bleroy/3d-junkyard/Atari130MX/Atari130MX-adapter/Atari130MX-FFC-schematic.png

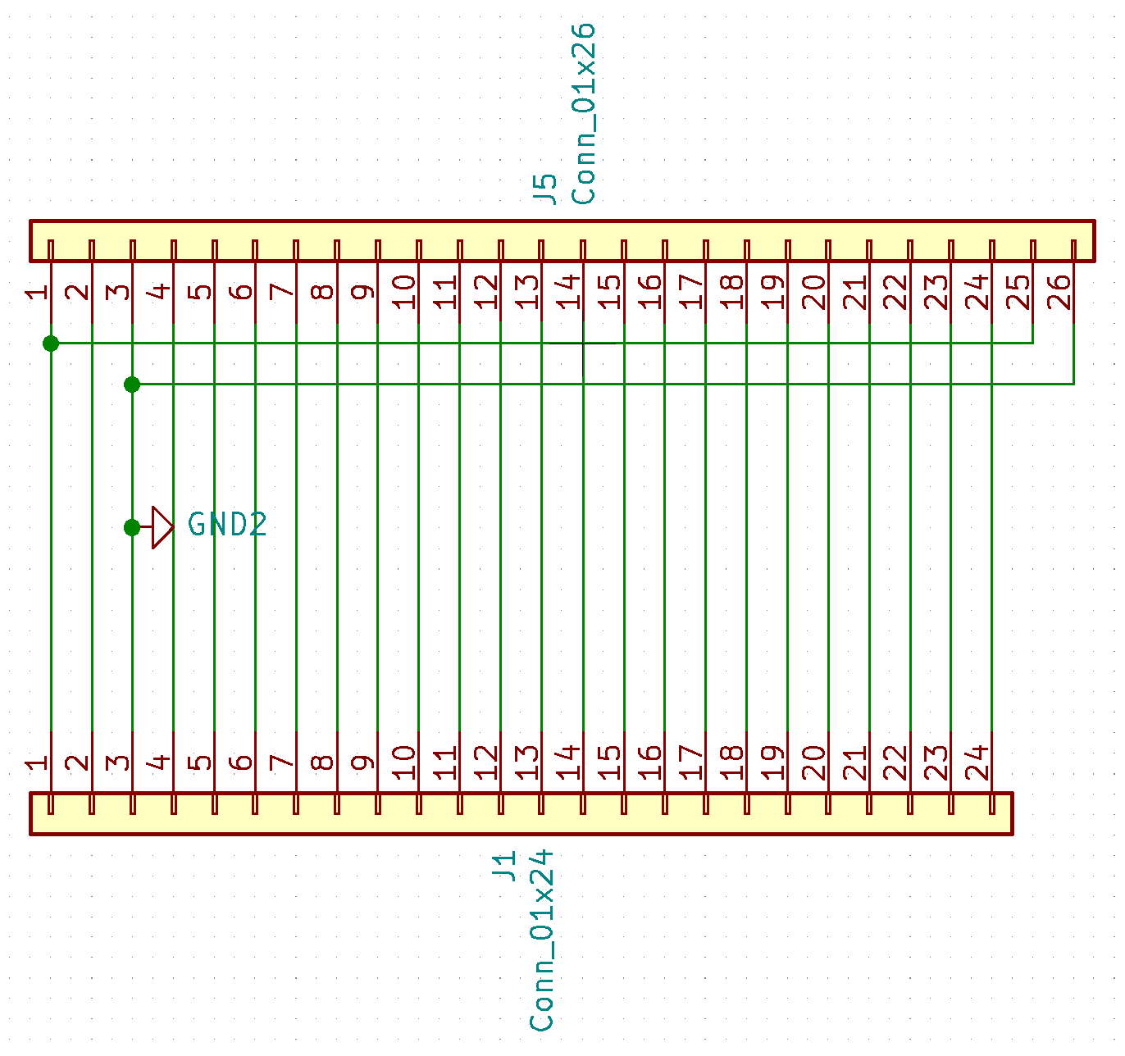
Atari130MX/Atari130MX-adapter/Atari130MX-FFC-schematic.png
