bleroy/3d-junkyard/Atari130MX/Caps/pmk-Layout.png

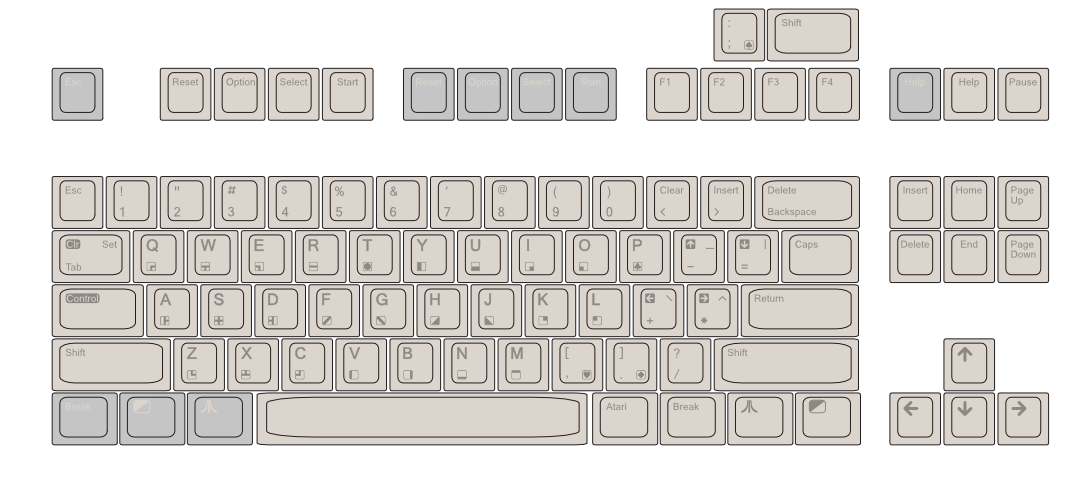
Atari130MX/Caps/pmk-Layout.png
