bleroy/3d-junkyard/Atari130MX/Caps/standard-full-XE-layout.png

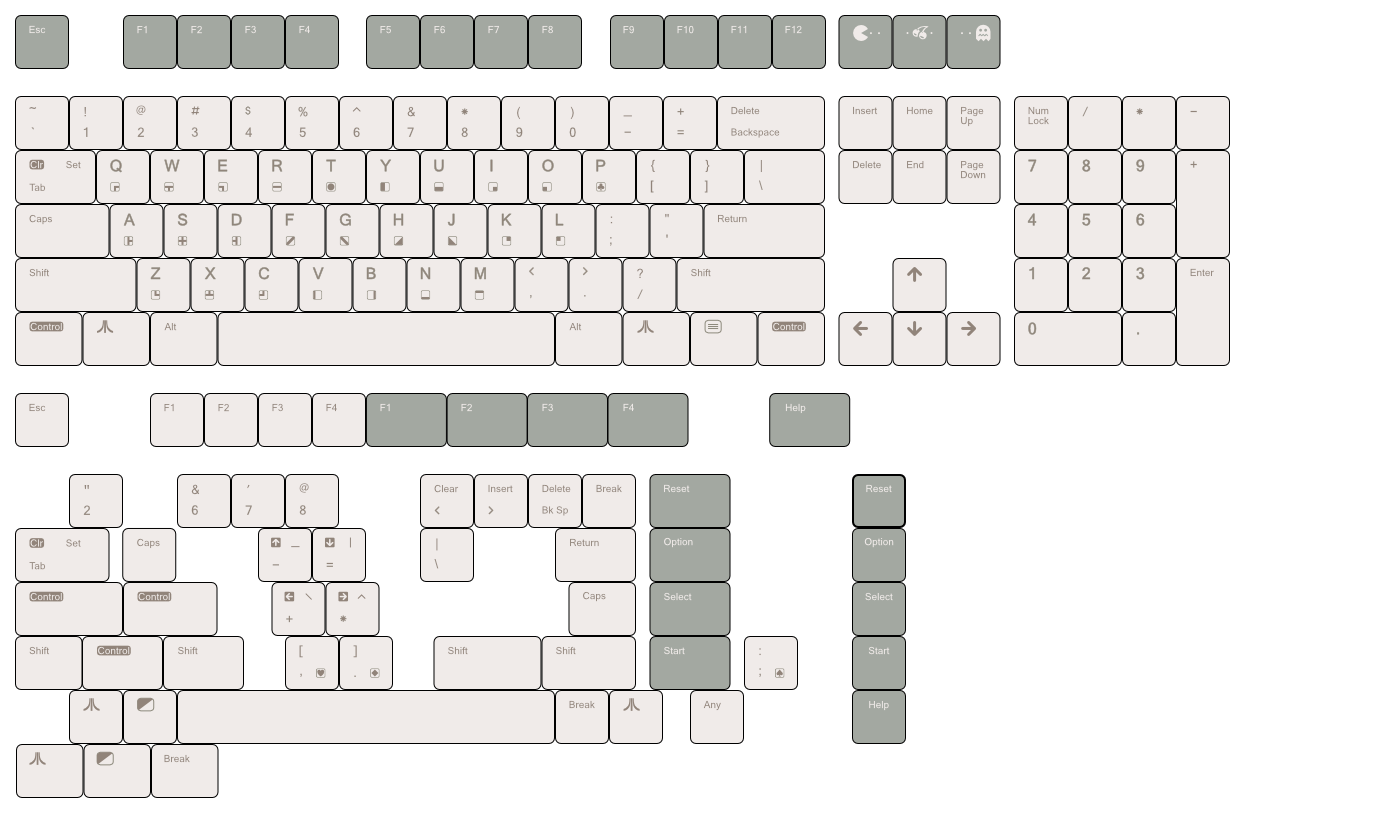
Atari130MX/Caps/standard-full-XE-layout.png
