bleroy/3d-junkyard/Atari130MX/DecentXE-to-USB/DecentXE-to-USB-front.png

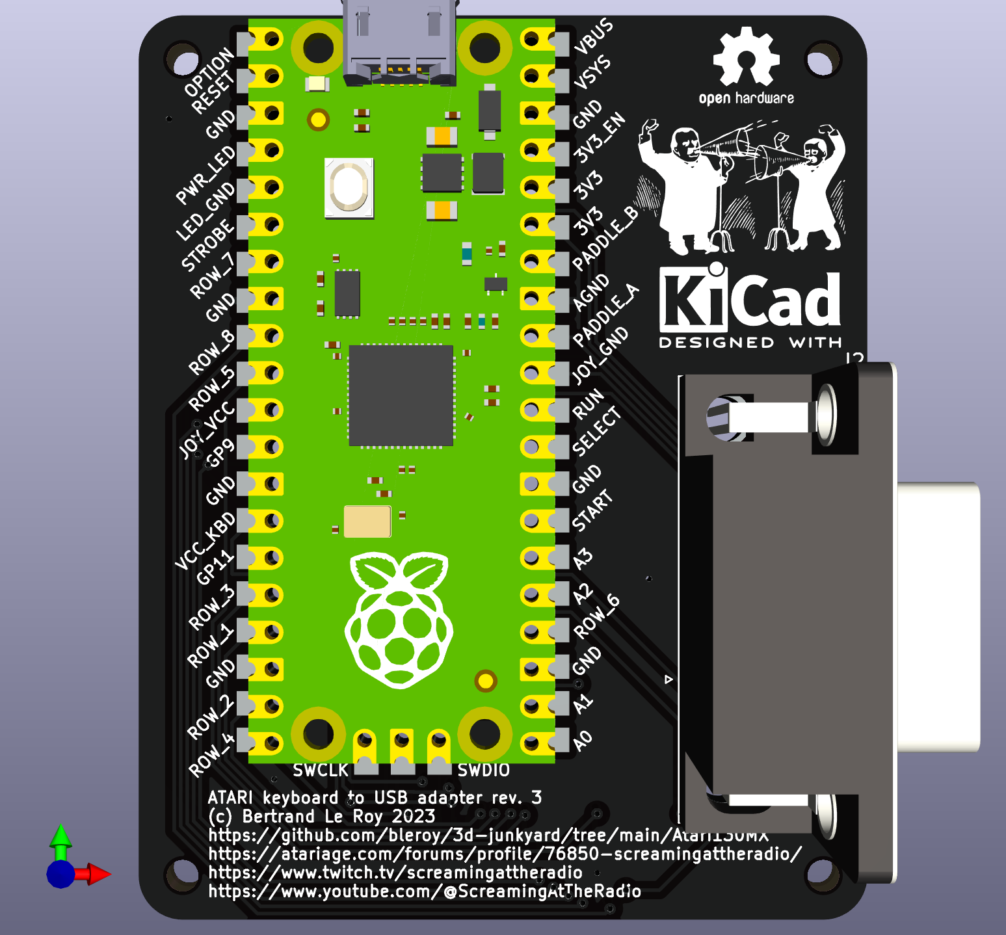
Atari130MX/DecentXE-to-USB/DecentXE-to-USB-front.png
