bleroy/3d-junkyard/Atari130MX/Glyphs/ArrowDownInverse.png

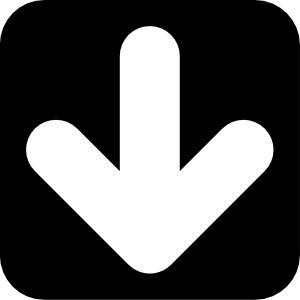
Atari130MX/Glyphs/ArrowDownInverse.png
