bleroy/3d-junkyard/Atari130MX/Glyphs/ArrowLeftInverse.png

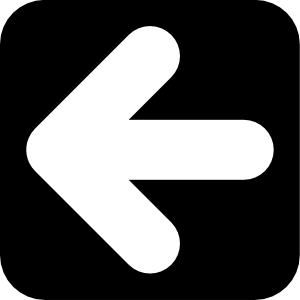
Atari130MX/Glyphs/ArrowLeftInverse.png
