bleroy/3d-junkyard/Atari130MX/Glyphs/ArrowRightInverse.png

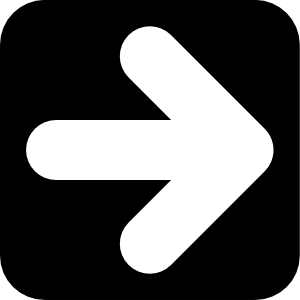
Atari130MX/Glyphs/ArrowRightInverse.png
