bleroy/3d-junkyard/Atari130MX/Glyphs/ArrowUpInverse.png

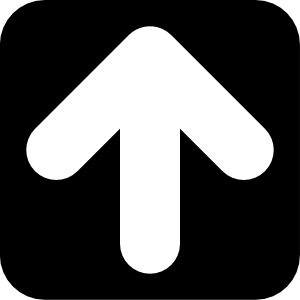
Atari130MX/Glyphs/ArrowUpInverse.png
