bleroy/3d-junkyard/Atari130MX/Glyphs/CtrlA.png

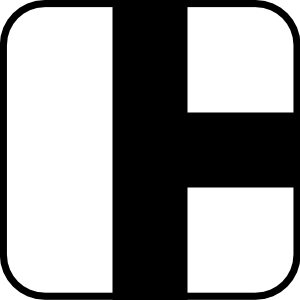
Atari130MX/Glyphs/CtrlA.png
