bleroy/3d-junkyard/Atari130MX/Glyphs/CtrlB.png

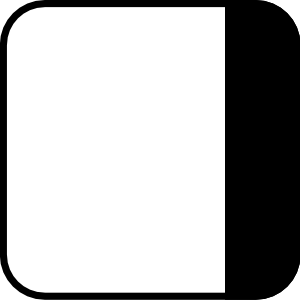
Atari130MX/Glyphs/CtrlB.png
