bleroy/3d-junkyard/Atari130MX/Glyphs/CtrlC.png

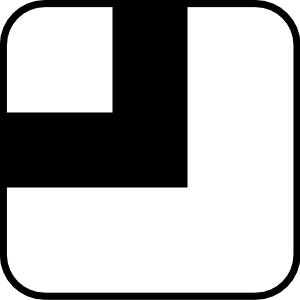
Atari130MX/Glyphs/CtrlC.png
