bleroy/3d-junkyard/Atari130MX/Glyphs/CtrlComma.png

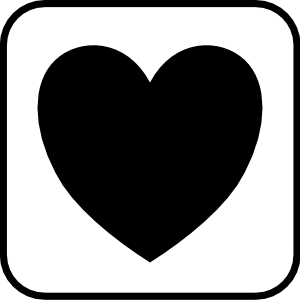
Atari130MX/Glyphs/CtrlComma.png
