bleroy/3d-junkyard/Atari130MX/Glyphs/CtrlD.png

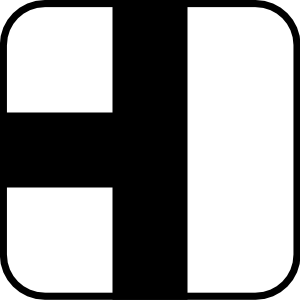
Atari130MX/Glyphs/CtrlD.png
