bleroy/3d-junkyard/Atari130MX/Glyphs/CtrlE.png

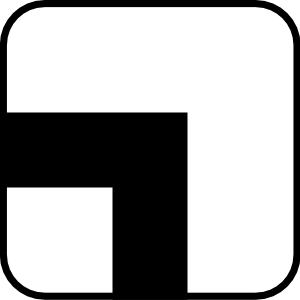
Atari130MX/Glyphs/CtrlE.png
