bleroy/3d-junkyard/Atari130MX/Glyphs/CtrlF.png

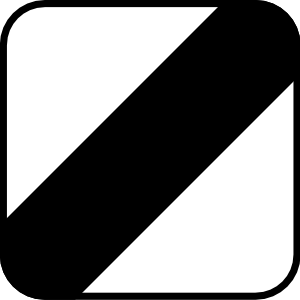
Atari130MX/Glyphs/CtrlF.png
