bleroy/3d-junkyard/Atari130MX/Glyphs/CtrlG.png

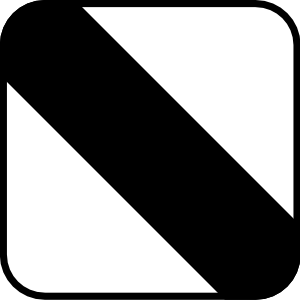
Atari130MX/Glyphs/CtrlG.png
