bleroy/3d-junkyard/Atari130MX/Glyphs/CtrlH.png

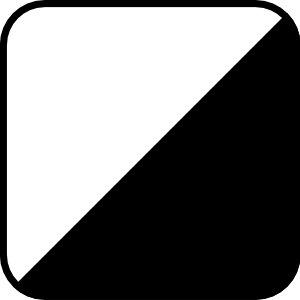
Atari130MX/Glyphs/CtrlH.png
