bleroy/3d-junkyard/Atari130MX/Glyphs/CtrlJ.png

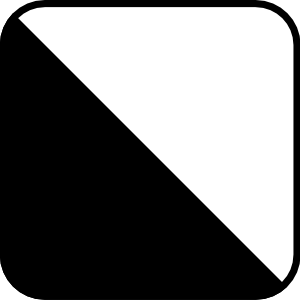
Atari130MX/Glyphs/CtrlJ.png
