bleroy/3d-junkyard/Atari130MX/Glyphs/CtrlL.png

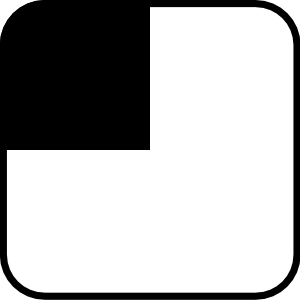
Atari130MX/Glyphs/CtrlL.png
