bleroy/3d-junkyard/Atari130MX/Glyphs/CtrlM.png

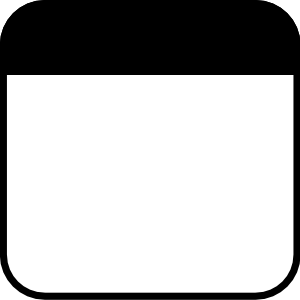
Atari130MX/Glyphs/CtrlM.png
