bleroy/3d-junkyard/Atari130MX/Glyphs/CtrlO.png

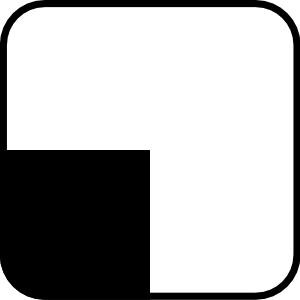
Atari130MX/Glyphs/CtrlO.png
