bleroy/3d-junkyard/Atari130MX/Glyphs/CtrlP.png

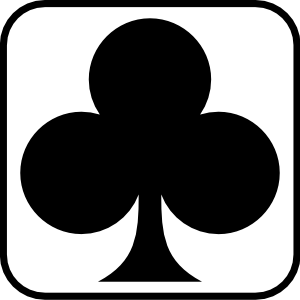
Atari130MX/Glyphs/CtrlP.png
