bleroy/3d-junkyard/Atari130MX/Glyphs/CtrlPeriod.png

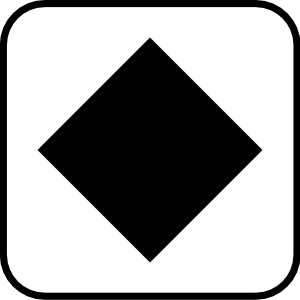
Atari130MX/Glyphs/CtrlPeriod.png
