bleroy/3d-junkyard/Atari130MX/Glyphs/CtrlQ.png

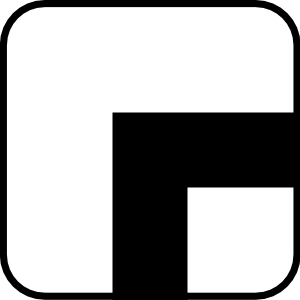
Atari130MX/Glyphs/CtrlQ.png
