bleroy/3d-junkyard/Atari130MX/Glyphs/CtrlR.png

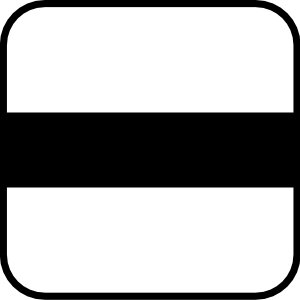
Atari130MX/Glyphs/CtrlR.png
