bleroy/3d-junkyard/Atari130MX/Glyphs/CtrlSemiColon.png

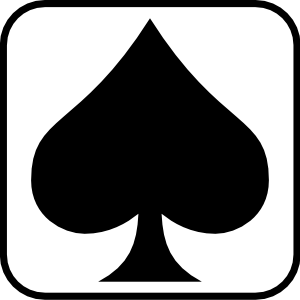
Atari130MX/Glyphs/CtrlSemiColon.png
