bleroy/3d-junkyard/Atari130MX/Glyphs/CtrlT.png

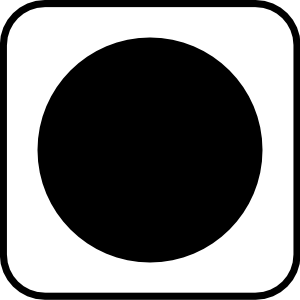
Atari130MX/Glyphs/CtrlT.png
