bleroy/3d-junkyard/Atari130MX/Glyphs/CtrlV.png

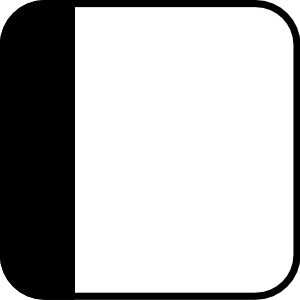
Atari130MX/Glyphs/CtrlV.png
