bleroy/3d-junkyard/Atari130MX/Glyphs/CtrlX.png

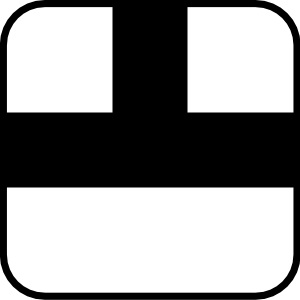
Atari130MX/Glyphs/CtrlX.png
