bleroy/3d-junkyard/Atari130MX/Glyphs/CtrlY.png

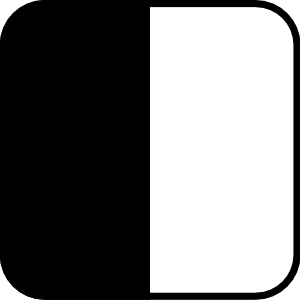
Atari130MX/Glyphs/CtrlY.png
