bleroy/3d-junkyard/Atari130MX/Glyphs/Fuji.png

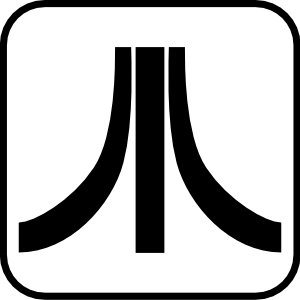
Atari130MX/Glyphs/Fuji.png
