bleroy/3d-junkyard/Atari130MX/Glyphs/FujiInverse.png

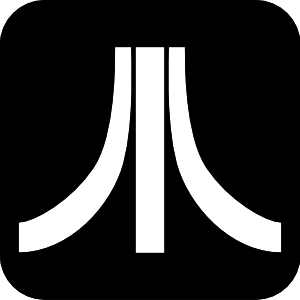
Atari130MX/Glyphs/FujiInverse.png
