bleroy/3d-junkyard/Atari130MX/Media/AlPlate.jpg

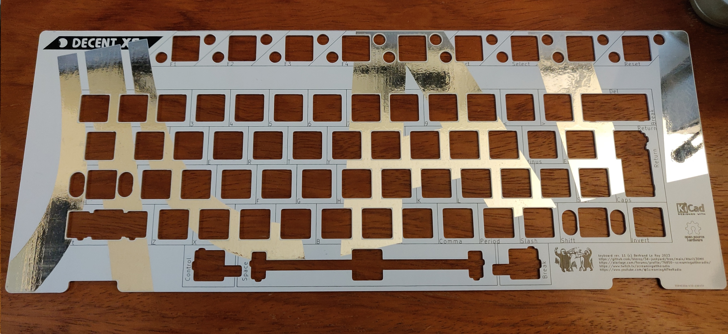
Atari130MX/Media/AlPlate.jpg
