bleroy/3d-junkyard/Atari130MX/Media/Decent-cable.jpg

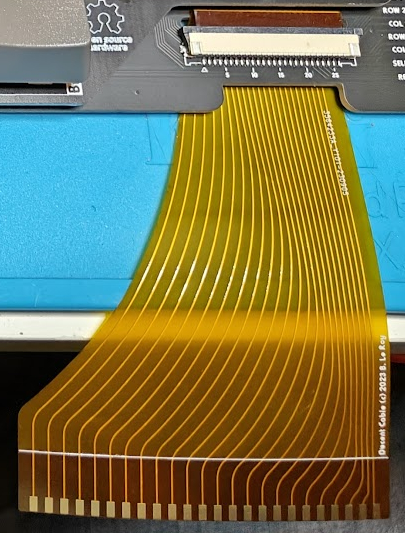
Atari130MX/Media/Decent-cable.jpg
