bleroy/3d-junkyard/Atari130MX/Media/DecentXE-Back.png

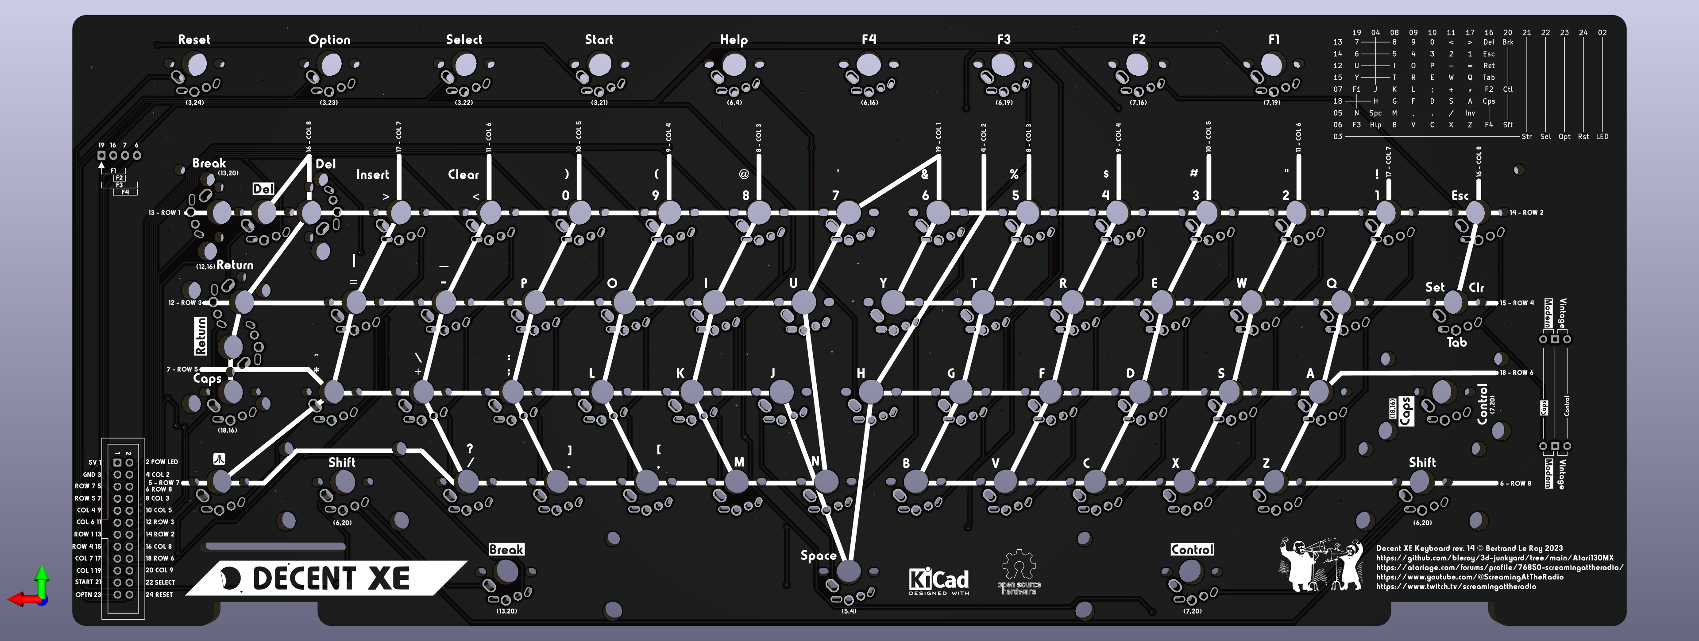
Atari130MX/Media/DecentXE-Back.png
