bleroy/3d-junkyard/Atari130MX/Media/DecentXE-cable.png

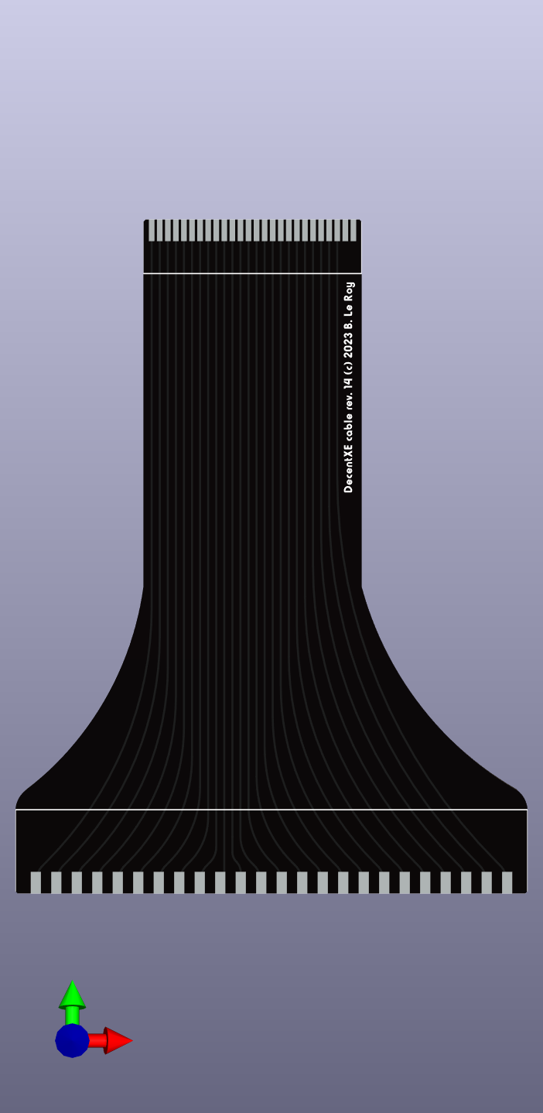
Atari130MX/Media/DecentXE-cable.png
