bleroy/3d-junkyard/Atari130MX/Media/DecentXE-front.png

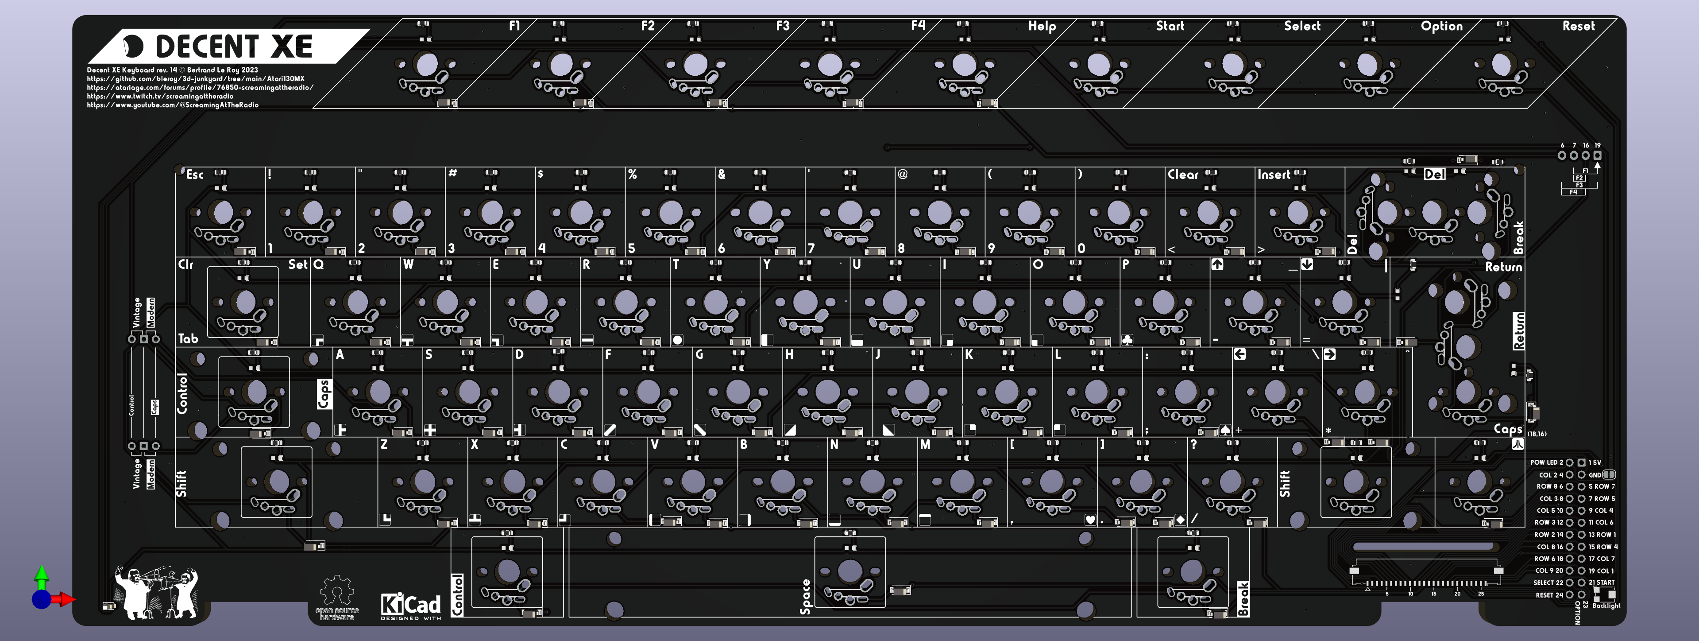
Atari130MX/Media/DecentXE-front.png
