bleroy/3d-junkyard/Atari130MX/Media/DecentXE-plate.png

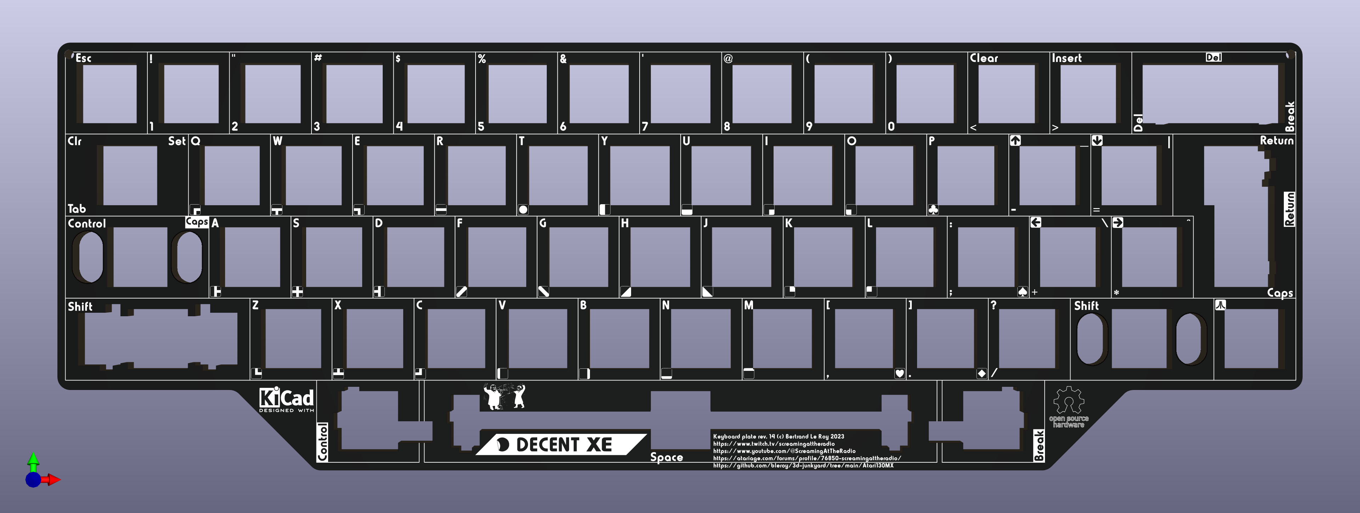
Atari130MX/Media/DecentXE-plate.png
