bleroy/3d-junkyard/Atari130MX/Media/steel-plate.jpg

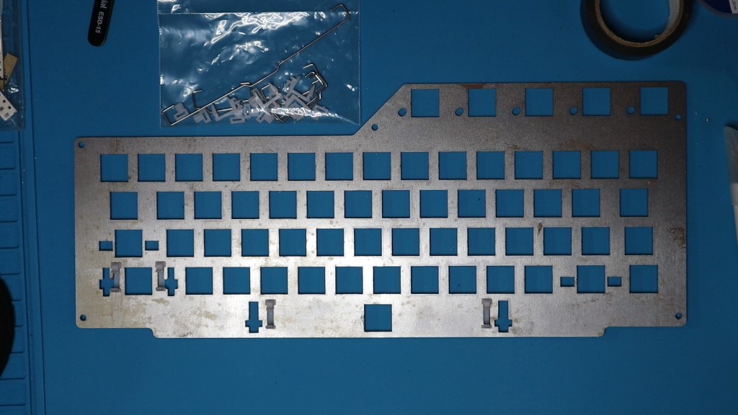
Atari130MX/Media/steel-plate.jpg
