bleroy/3d-junkyard/Atari130MX/Reference/Atari130XE.jpg

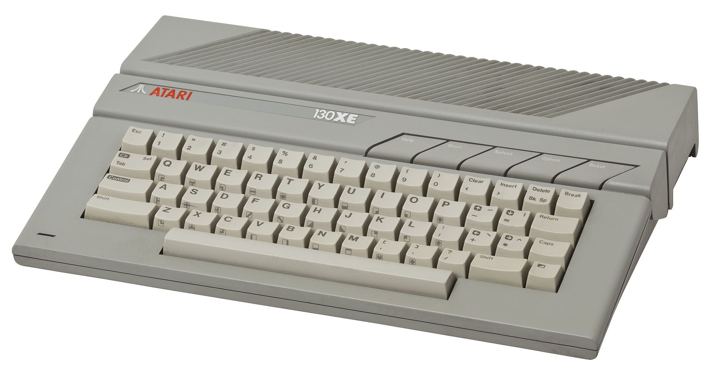
Atari130MX/Reference/Atari130XE.jpg
