bleroy/3d-junkyard/Atari130MX/Reference/AtariXL-Alps.jpg

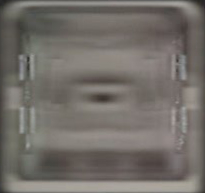
Atari130MX/Reference/AtariXL-Alps.jpg
