bleroy/3d-junkyard/Atari130MX/Reference/BackBottom.jpg

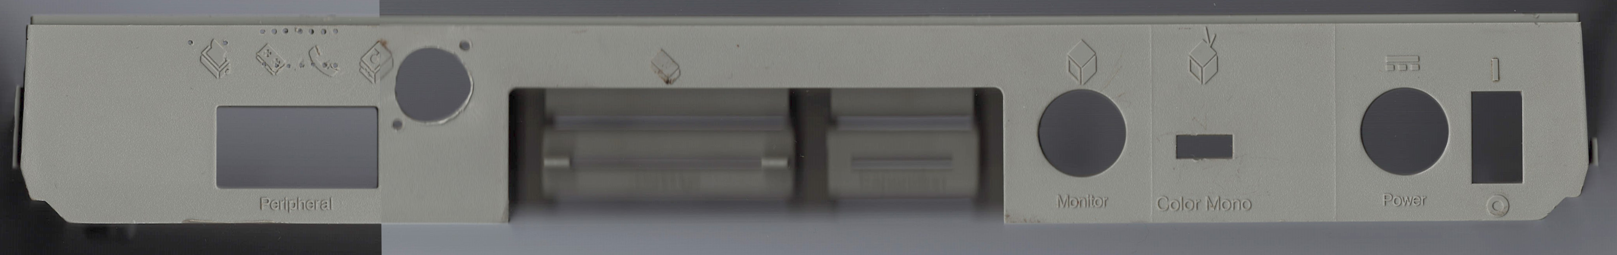
Atari130MX/Reference/BackBottom.jpg
