bleroy/3d-junkyard/Atari130MX/Reference/Bottom.jpg

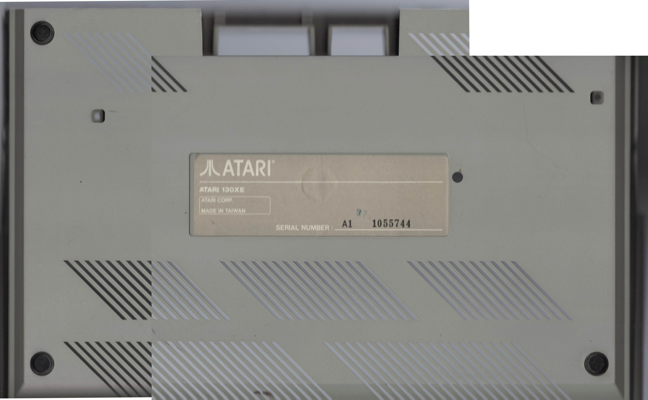
Atari130MX/Reference/Bottom.jpg
