bleroy/3d-junkyard/Atari130MX/Reference/Left.jpg

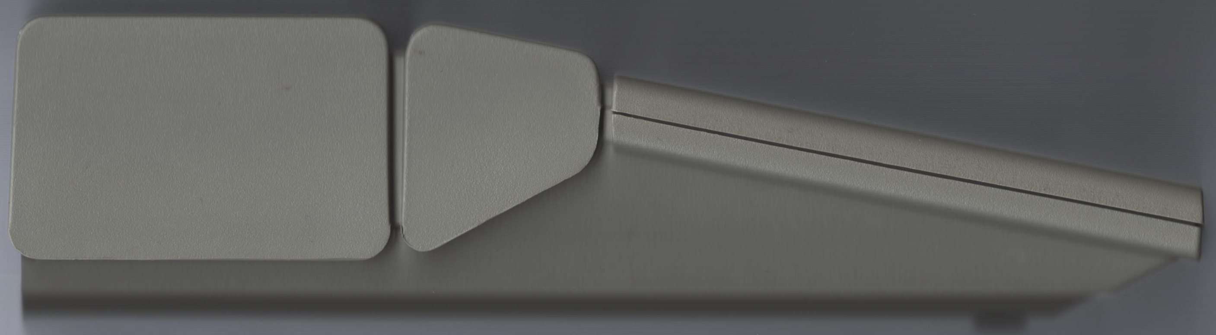
Atari130MX/Reference/Left.jpg
