bleroy/3d-junkyard/Atari130MX/Reference/LeftTop.jpg

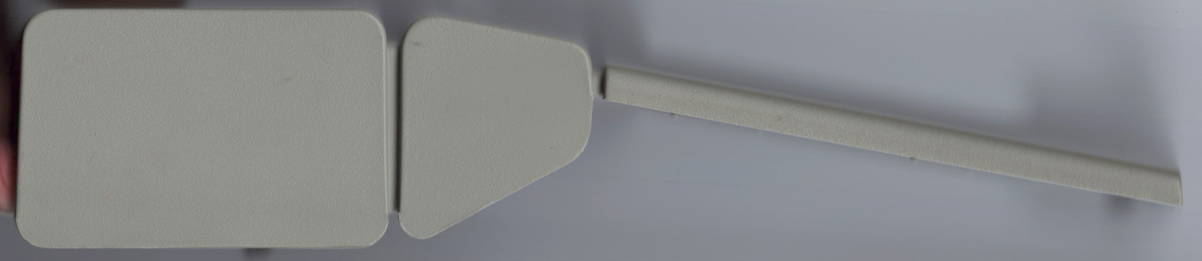
Atari130MX/Reference/LeftTop.jpg
