bleroy/3d-junkyard/Atari130MX/Reference/low-pro-kailh-gateron-reddragon.jpg

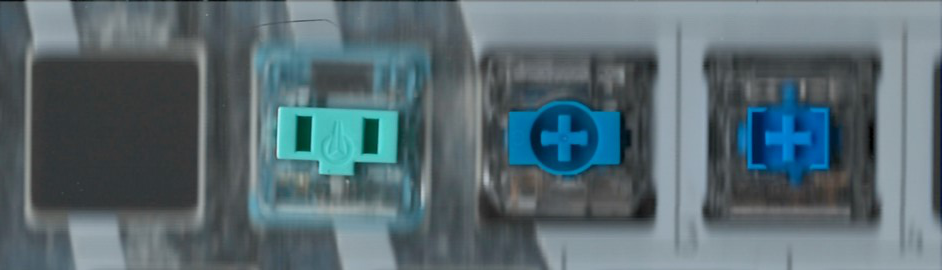
Atari130MX/Reference/low-pro-kailh-gateron-reddragon.jpg
