bleroy/3d-junkyard/Atari130MX/Reference/RightBottom.jpg

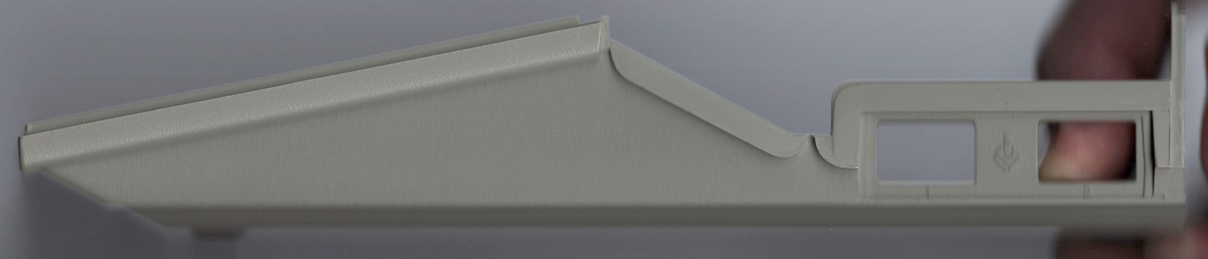
Atari130MX/Reference/RightBottom.jpg
