bleroy/3d-junkyard/Atari130MX/Reference/RightTop.jpg

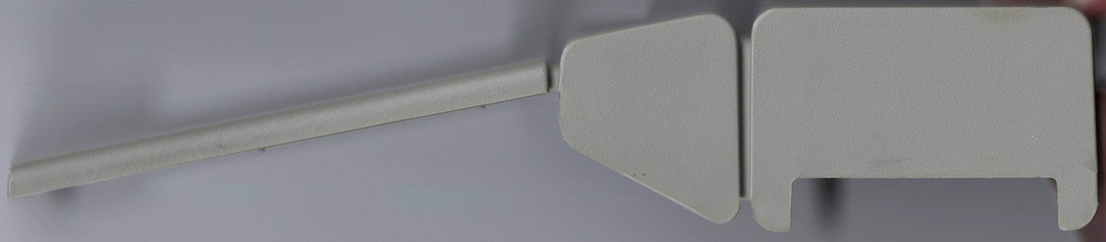
Atari130MX/Reference/RightTop.jpg
