bleroy/3d-junkyard/Atari130MX/Reference/TopBack.jpg

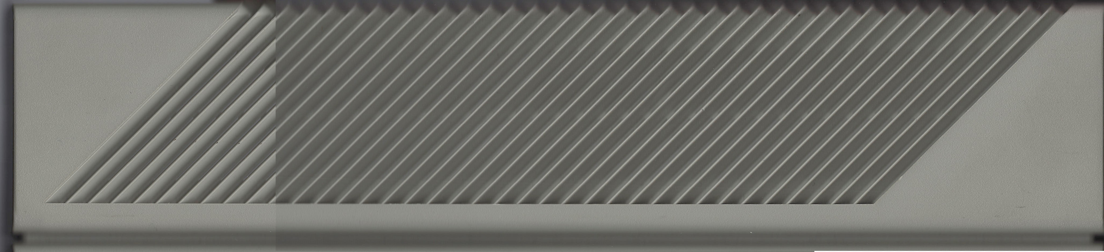
Atari130MX/Reference/TopBack.jpg
