bleroy/3d-junkyard/Atari130MX/Reference/TopFront.jpg

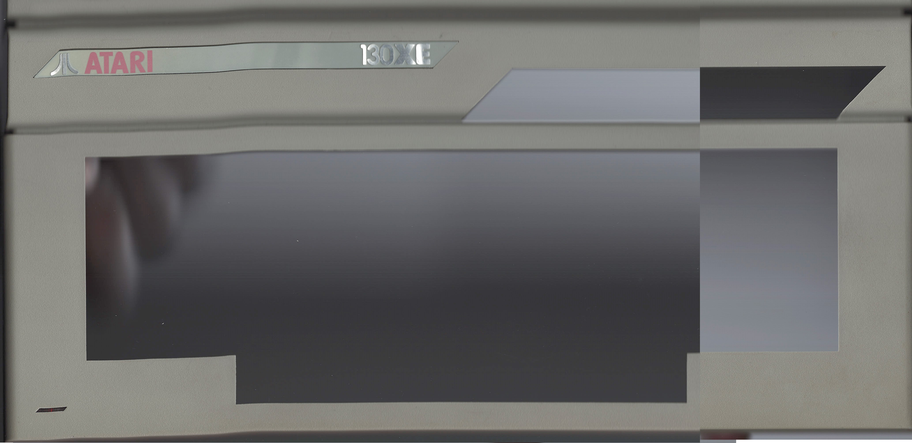
Atari130MX/Reference/TopFront.jpg
