bleroy/3d-junkyard/Atari130MX/Reference/TopLeftScrew.jpg

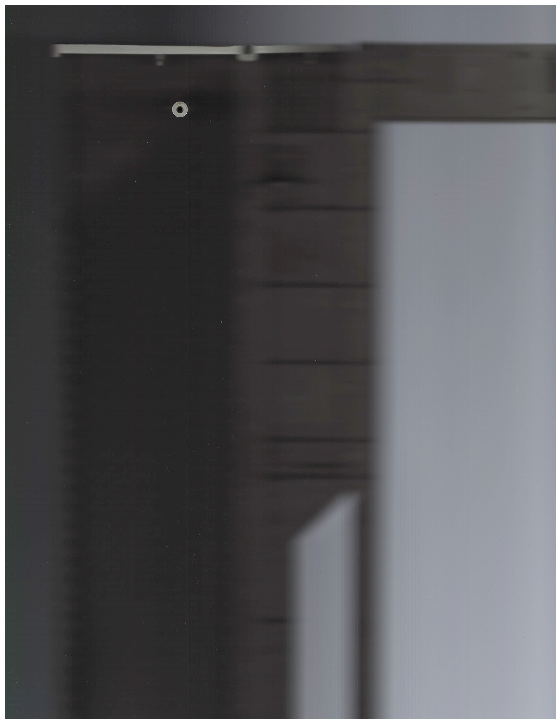
Atari130MX/Reference/TopLeftScrew.jpg
