bleroy/3d-junkyard/Atari130MX/Reference/TopRightScrew.jpg

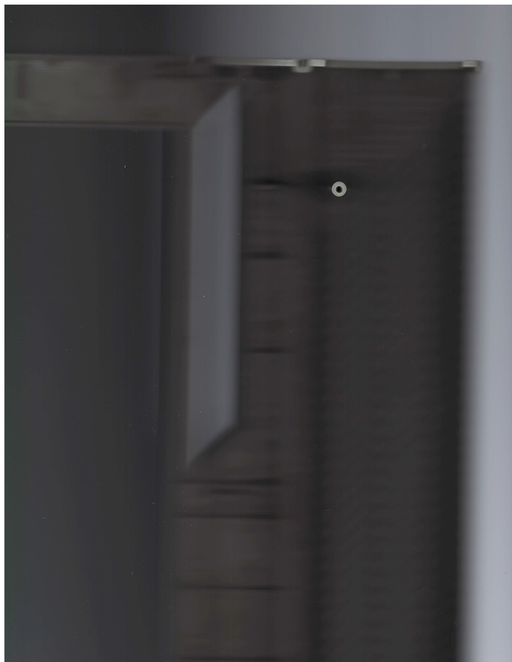
Atari130MX/Reference/TopRightScrew.jpg
