bleroy/3d-junkyard/Decent60/keyboard/Media/Layout.png

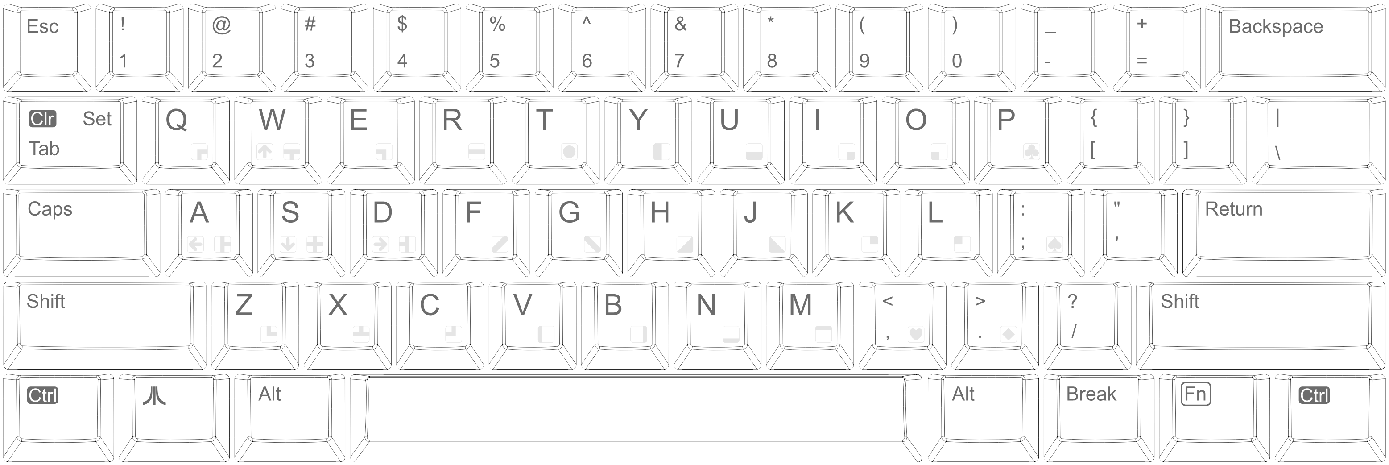
Decent60/keyboard/Media/Layout.png
