bleroy/3d-junkyard/Decent60/keyboard/Media/MegaXE-keyboard-back.png

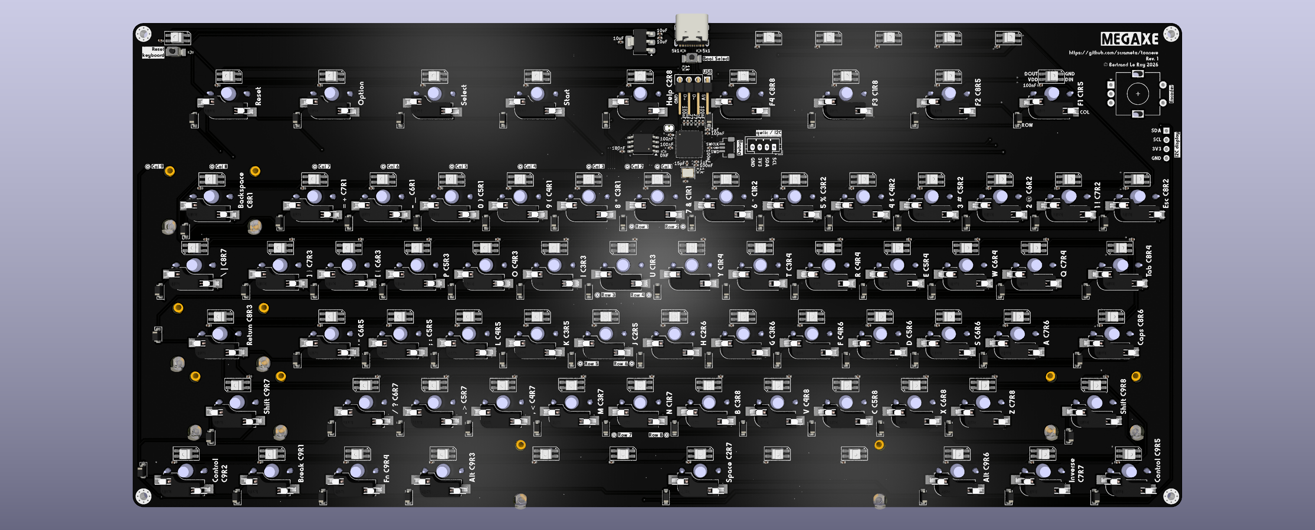
Decent60/keyboard/Media/MegaXE-keyboard-back.png
