bleroy/3d-junkyard/Decent60/keyboard/Media/MegaXE-keyboard.png

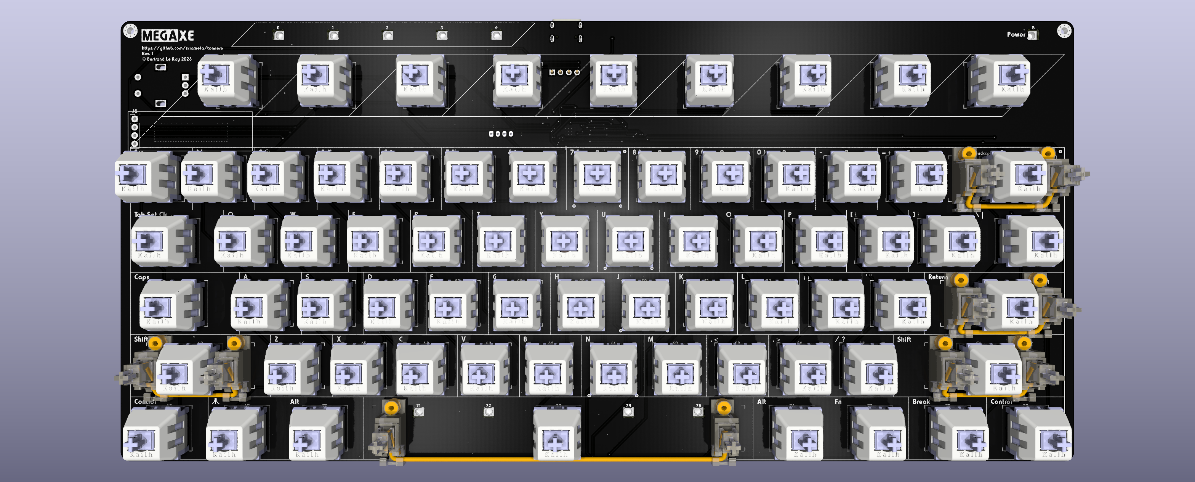
Decent60/keyboard/Media/MegaXE-keyboard.png
