bleroy/3d-junkyard/Decent60/keyboard/Media/MegaXE-plate.png

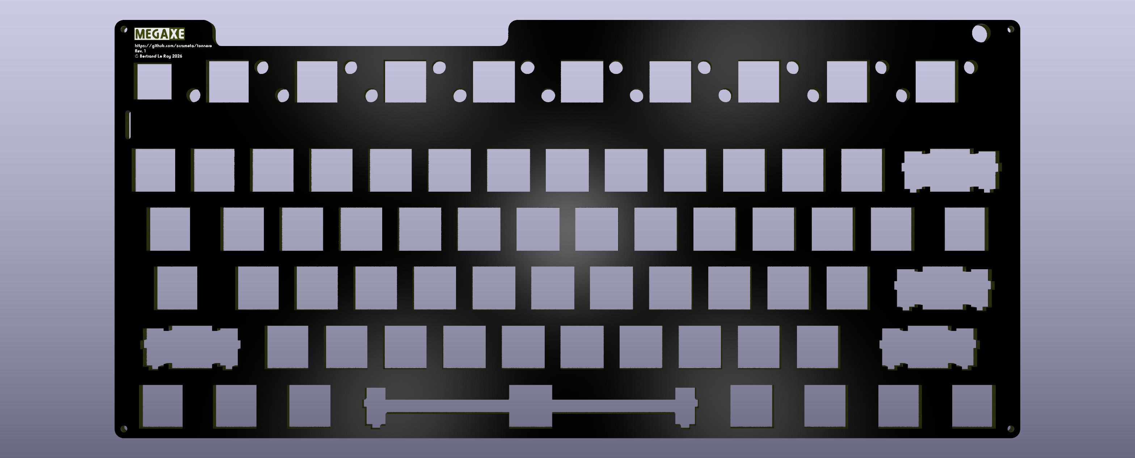
Decent60/keyboard/Media/MegaXE-plate.png
