bleroy/3d-junkyard/Decent60/Media/Decent60DirNumPad-back.png

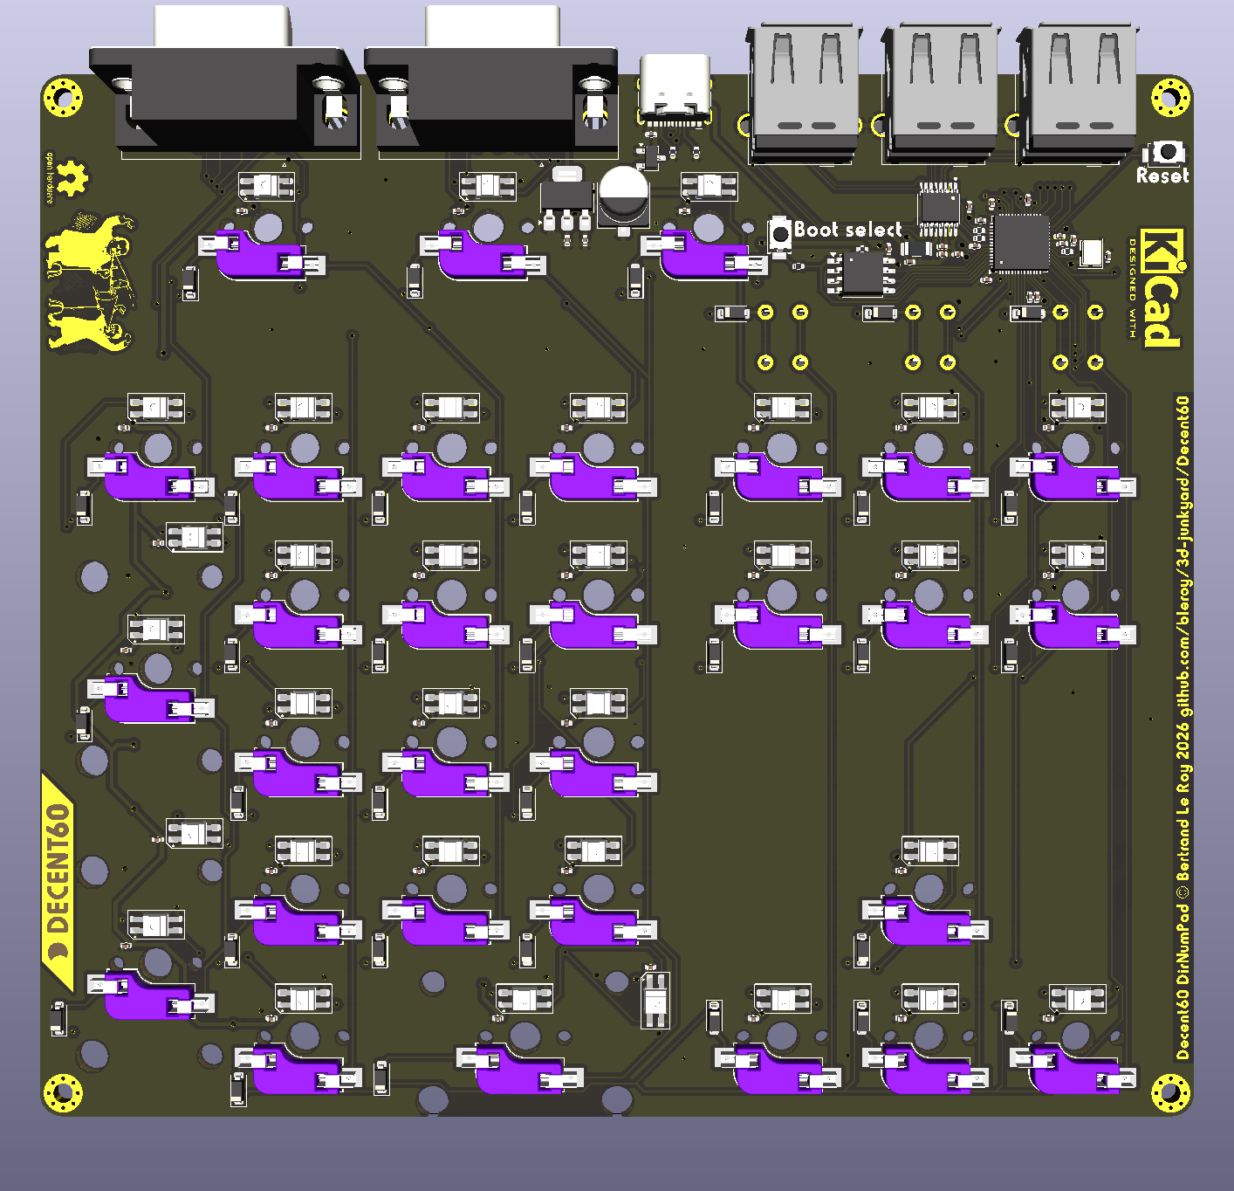
Decent60/Media/Decent60DirNumPad-back.png
