bleroy/3d-junkyard/Decent60/Media/Decent60DirNumPad-front.png

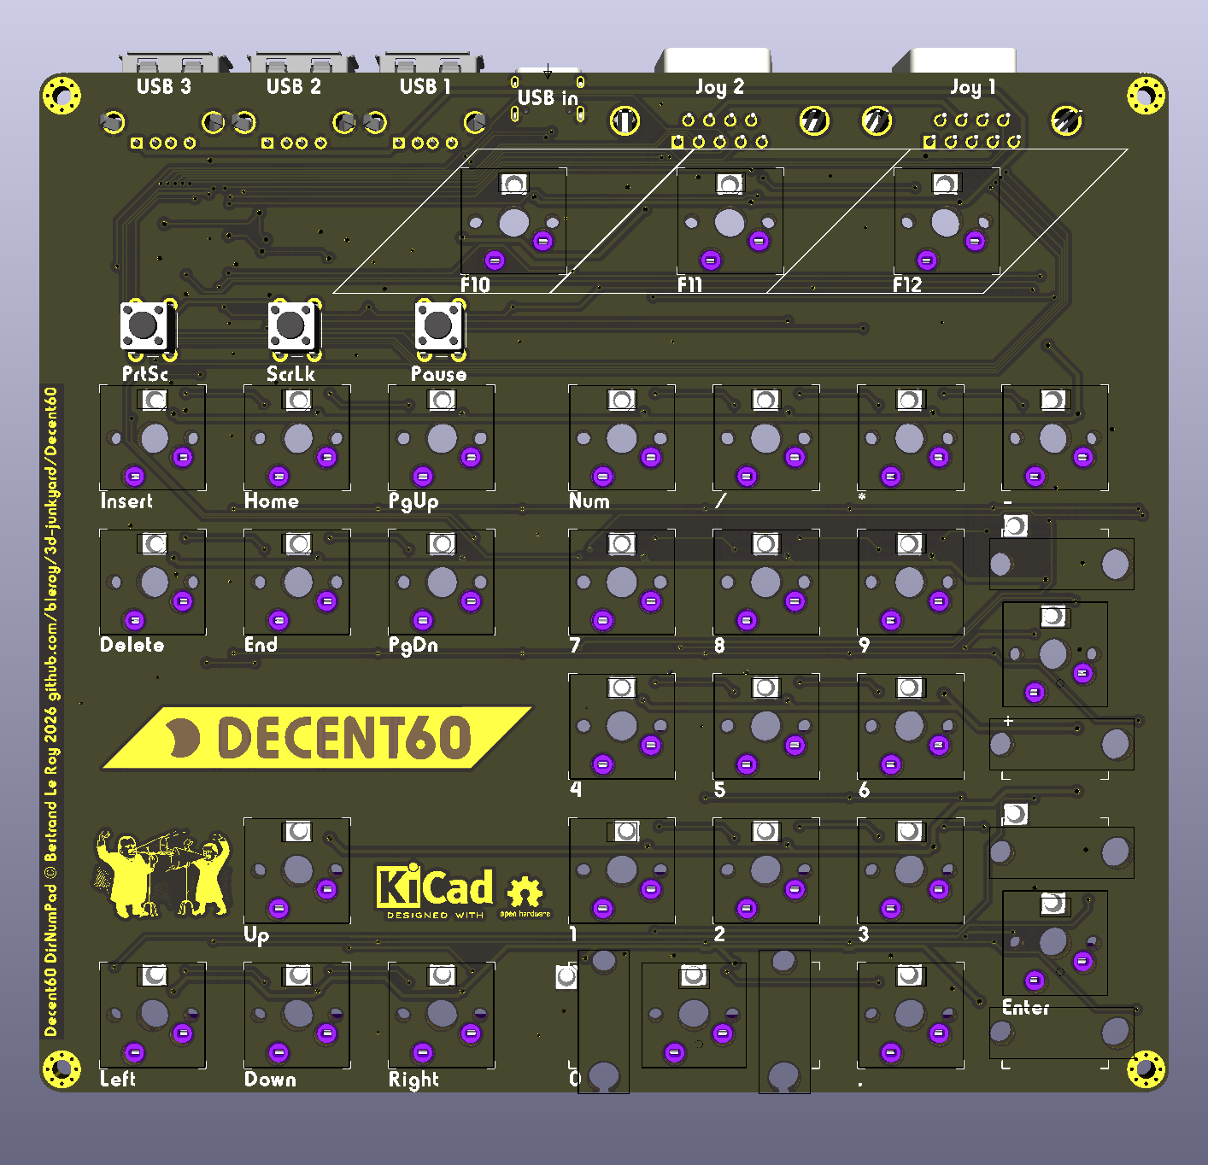
Decent60/Media/Decent60DirNumPad-front.png
