bleroy/3d-junkyard/Decent60/Media/NavNumPad-plate.png

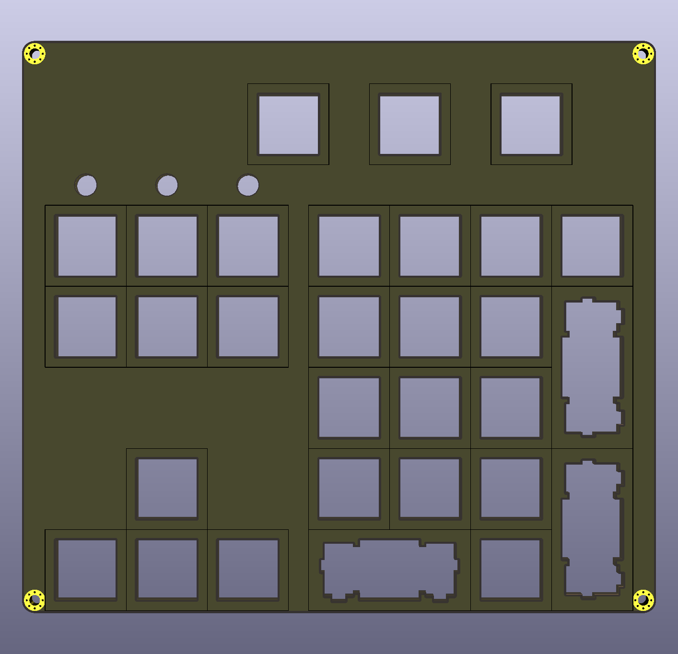
Decent60/Media/NavNumPad-plate.png
