bleroy/3d-junkyard/Decent400/Caps/Blocks/Decent400-emboss-block7.png

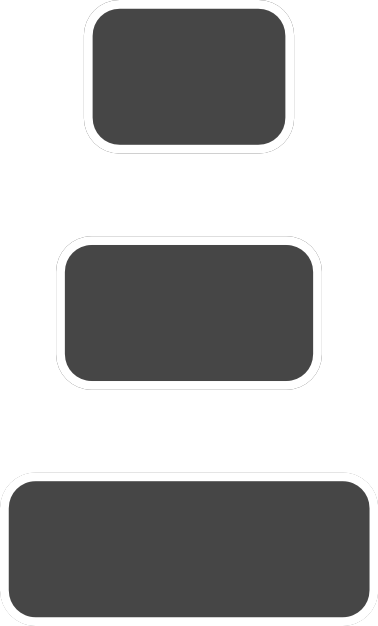
Decent400/Caps/Blocks/Decent400-emboss-block7.png
