bleroy/3d-junkyard/Decent400/Caps/Blocks/Decent400-emboss-block8.png

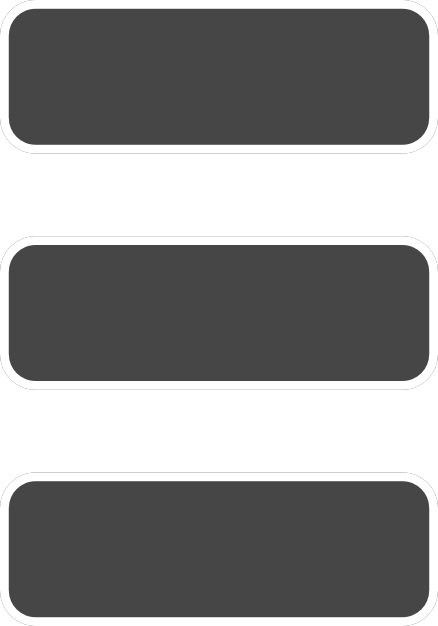
Decent400/Caps/Blocks/Decent400-emboss-block8.png
