bleroy/3d-junkyard/Decent400/Caps/Blocks/Decent400-emboss-block9.png

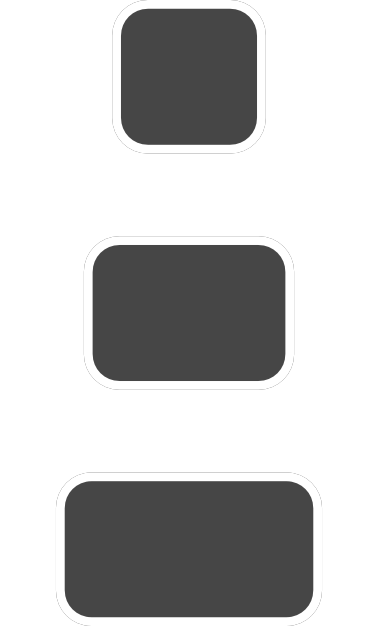
Decent400/Caps/Blocks/Decent400-emboss-block9.png
