bleroy/3d-junkyard/Decent400/Caps/Blocks/Decent400-emboss-block-1U.png

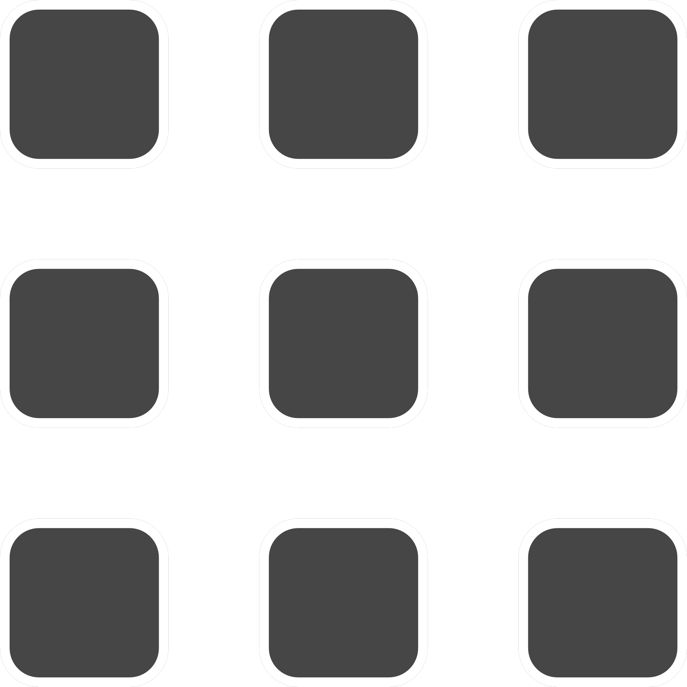
Decent400/Caps/Blocks/Decent400-emboss-block-1U.png
