bleroy/3d-junkyard/Decent400/Caps/Blocks/temp-block.png

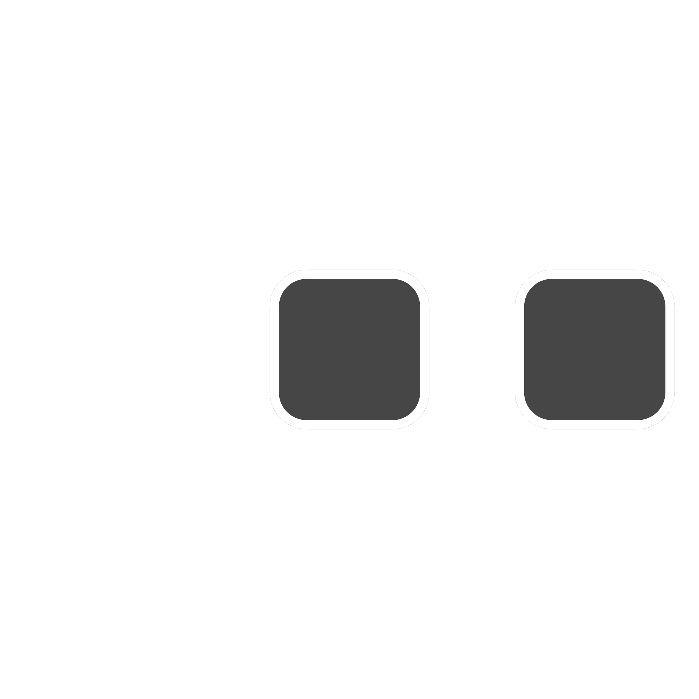
Decent400/Caps/Blocks/temp-block.png
