bleroy/3d-junkyard/Decent400/Caps/Singles/1U25-emboss.png

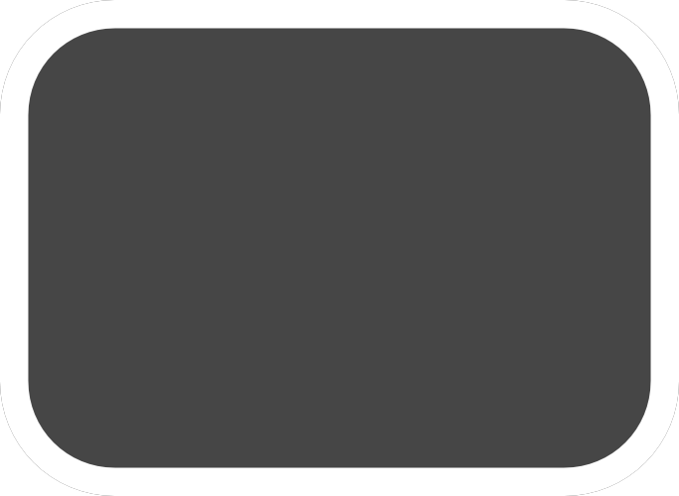
Decent400/Caps/Singles/1U25-emboss.png
