bleroy/3d-junkyard/Decent400/Media/Decent400-keyboard-back.png

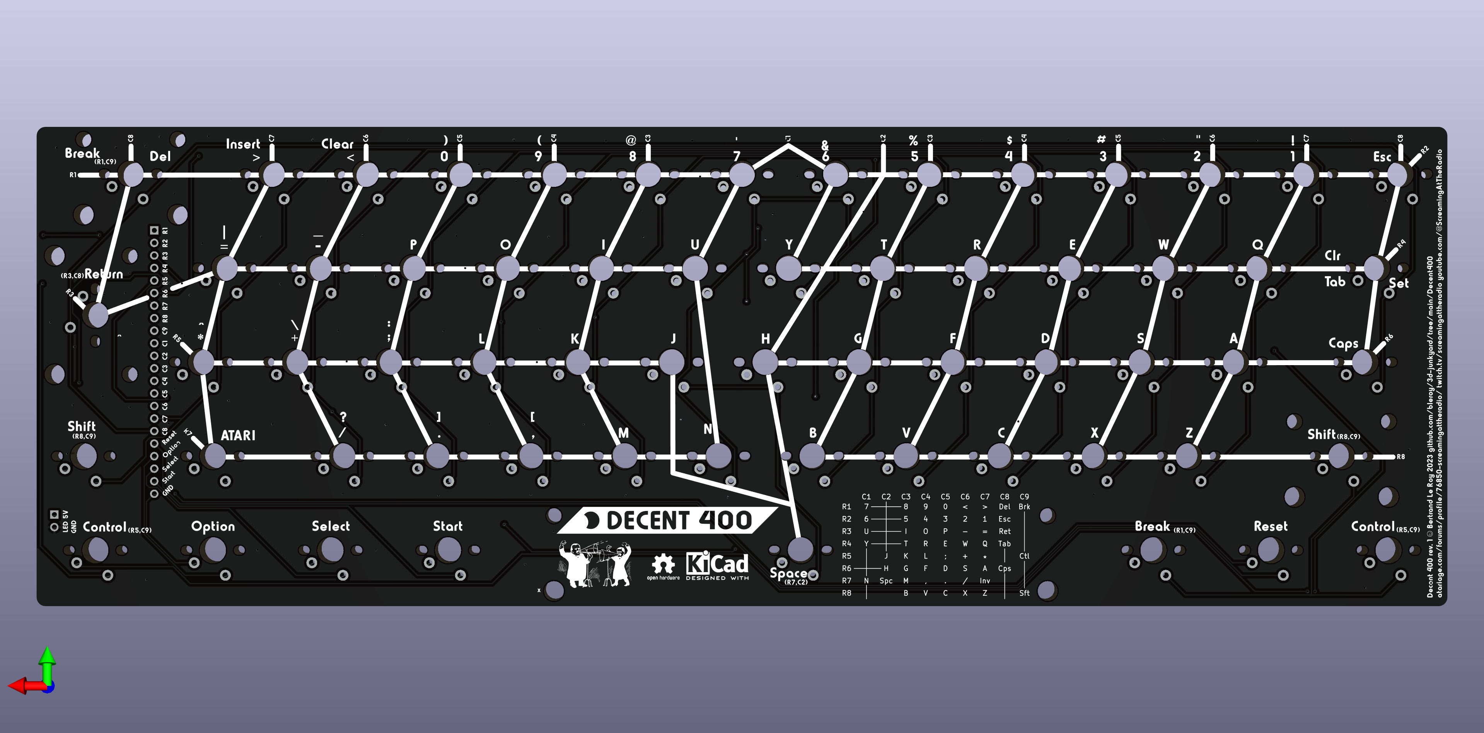
Decent400/Media/Decent400-keyboard-back.png
