bleroy/3d-junkyard/Decent400/Media/Decent400-keyboard-front.png

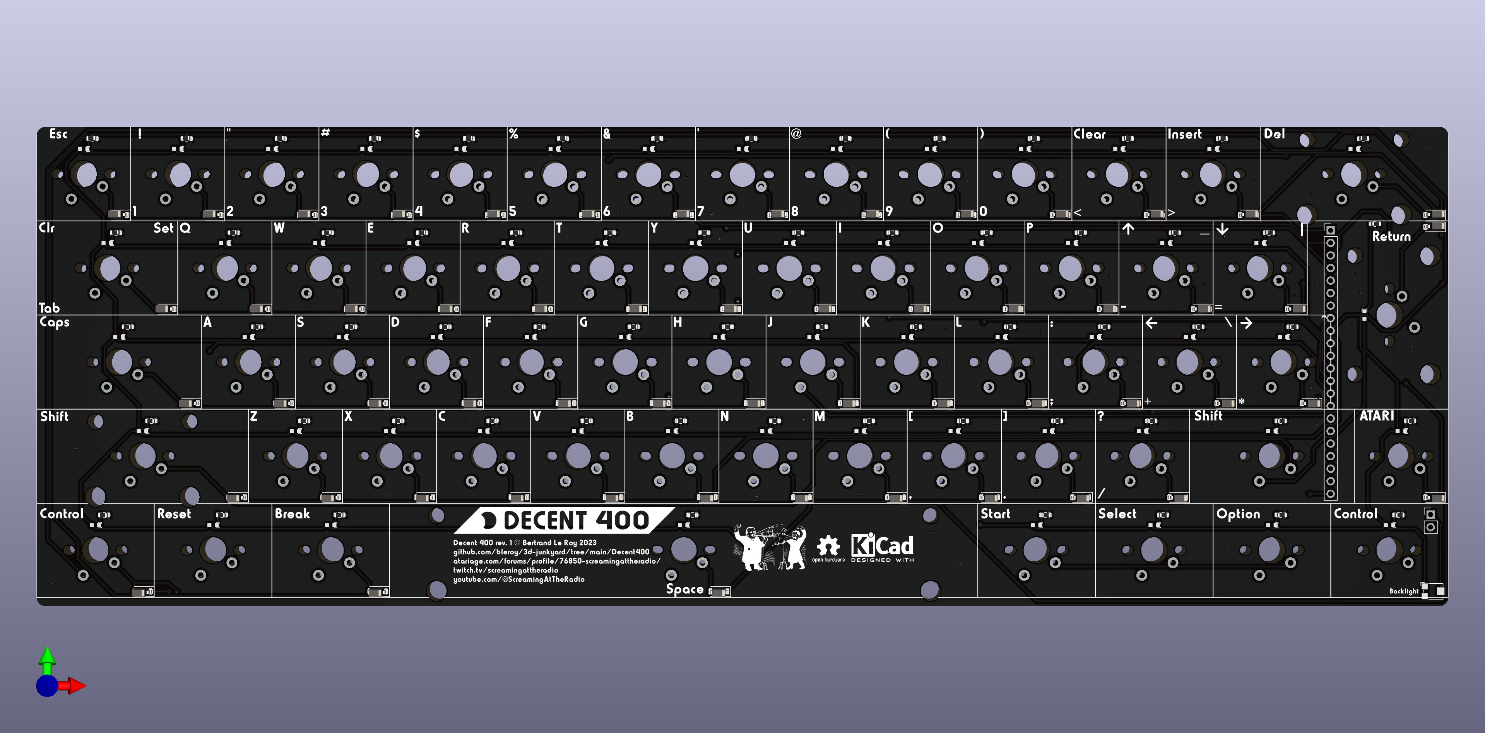
Decent400/Media/Decent400-keyboard-front.png
