bleroy/3d-junkyard/Decent400/Media/Decent400-plate-back.png

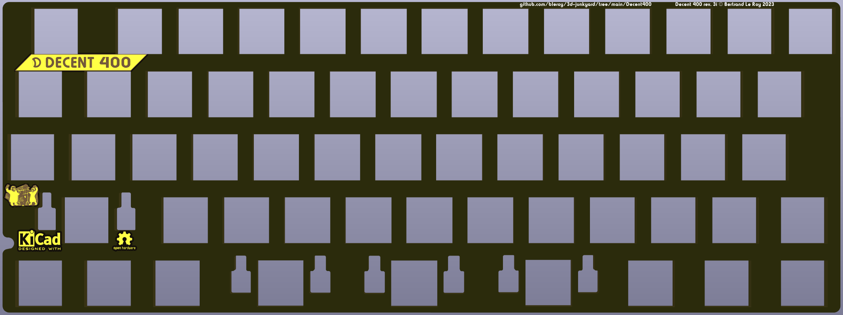
Decent400/Media/Decent400-plate-back.png
