bleroy/3d-junkyard/Decent400/Media/Decent400-plate.png

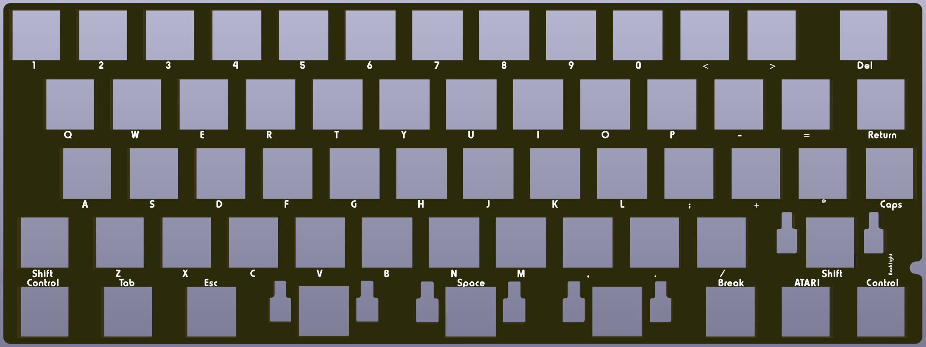
Decent400/Media/Decent400-plate.png
