bleroy/3d-junkyard/Decent400/Media/Decent400i-flush.jpg

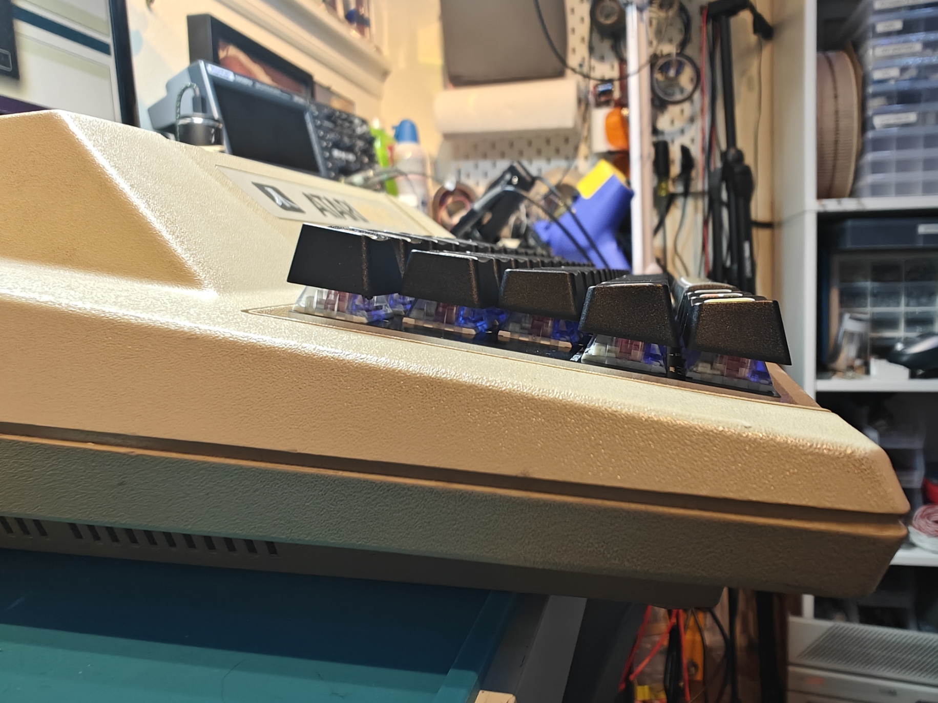
Decent400/Media/Decent400i-flush.jpg
