bleroy/3d-junkyard/Decent400/Media/Decent400i-on.jpg

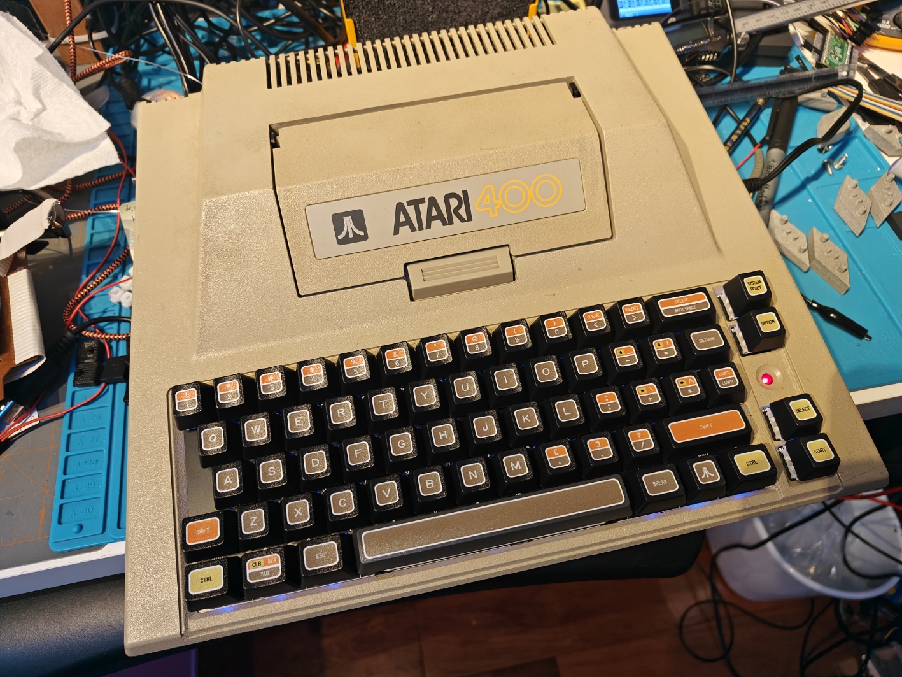
Decent400/Media/Decent400i-on.jpg
