bleroy/3d-junkyard/Decent400/Media/Decent400i.jpg

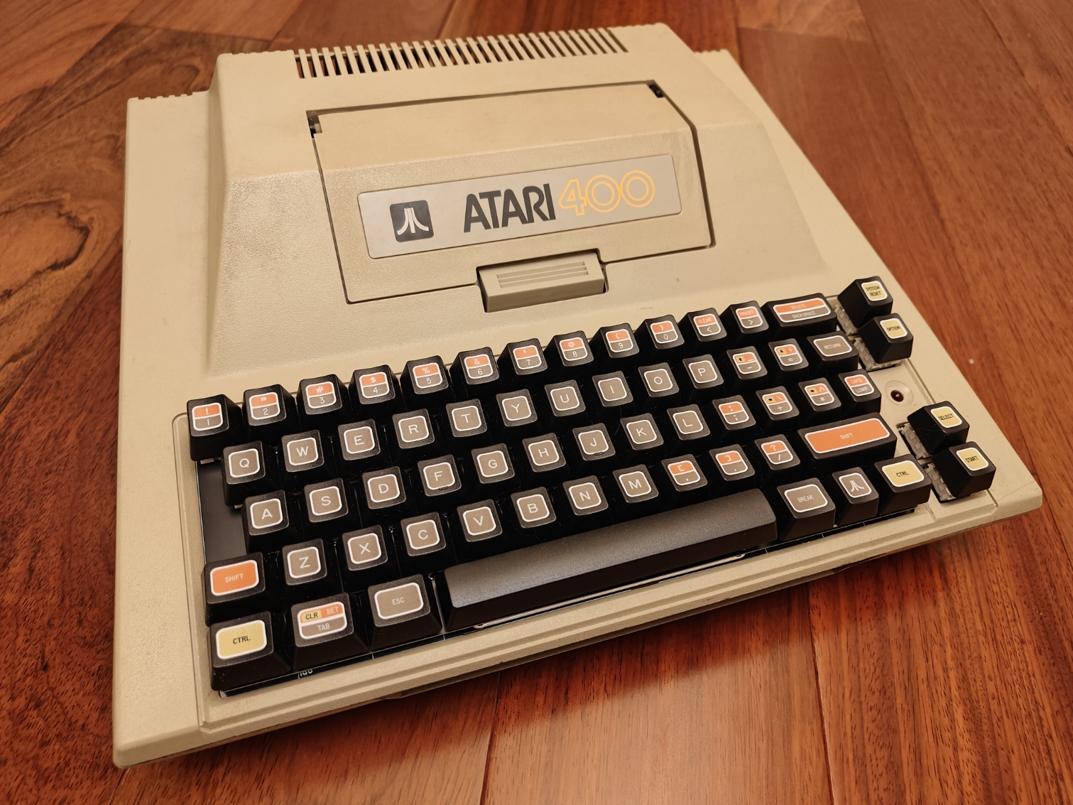
Decent400/Media/Decent400i.jpg
