bleroy/3d-junkyard/Decent400/Media/Decent400W-keyboard-back.png

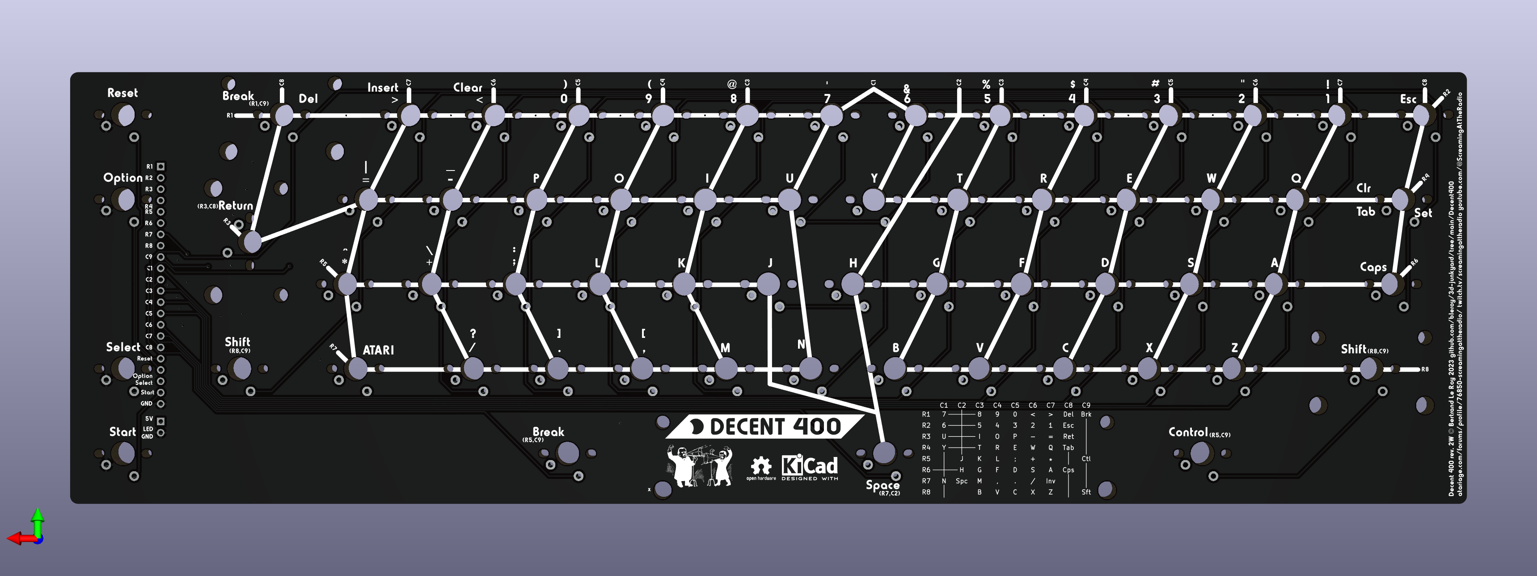
Decent400/Media/Decent400W-keyboard-back.png
