bleroy/3d-junkyard/Decent400/Media/Decent400W-keyboard-front.png

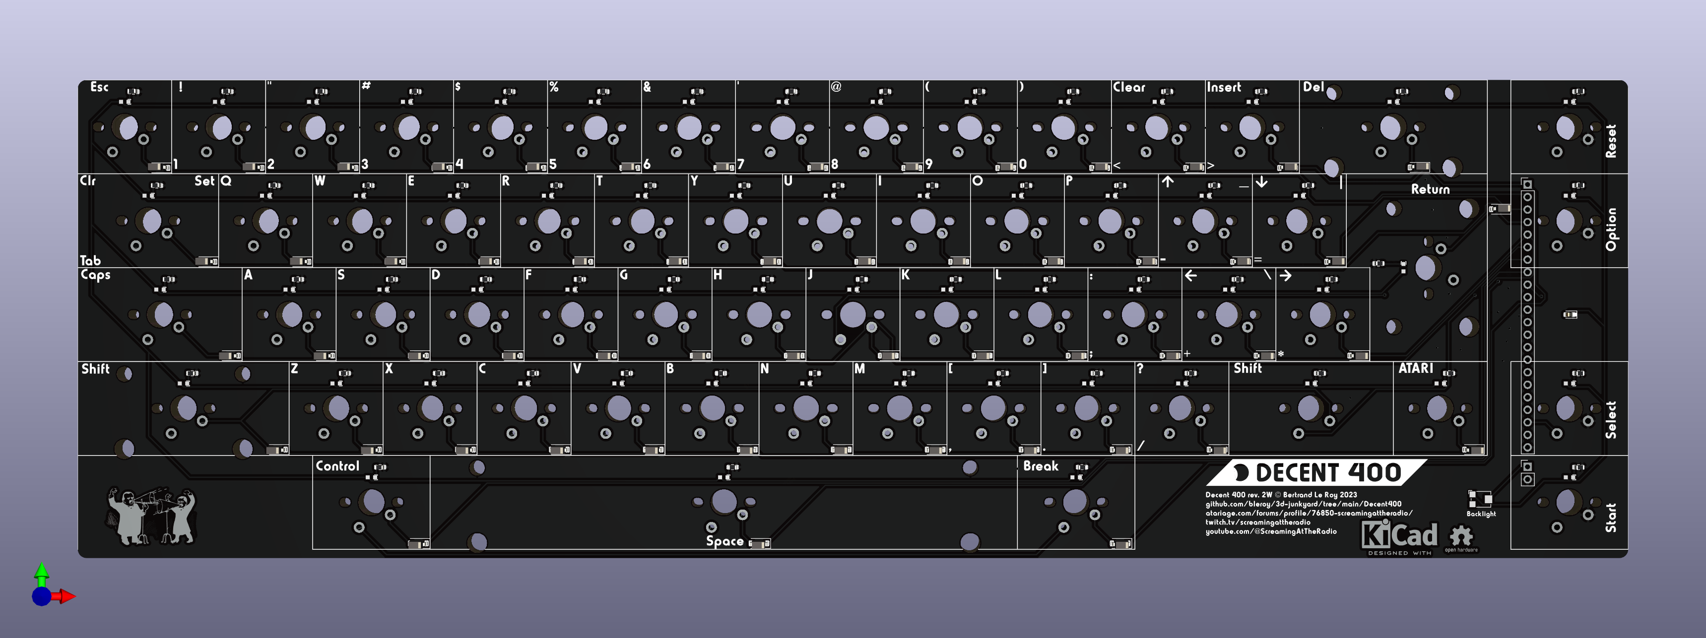
Decent400/Media/Decent400W-keyboard-front.png
