bleroy/3d-junkyard/Decent400/Media/Decent400W-plate.png

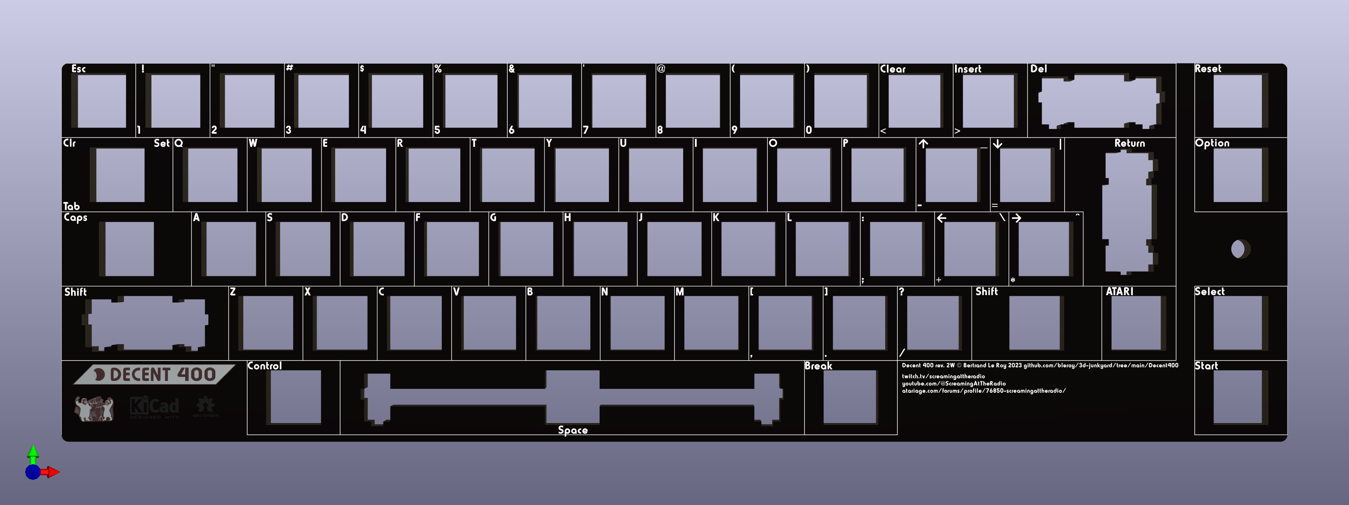
Decent400/Media/Decent400W-plate.png
