bleroy/3d-junkyard/Decent400/Reference/400-above.jpg

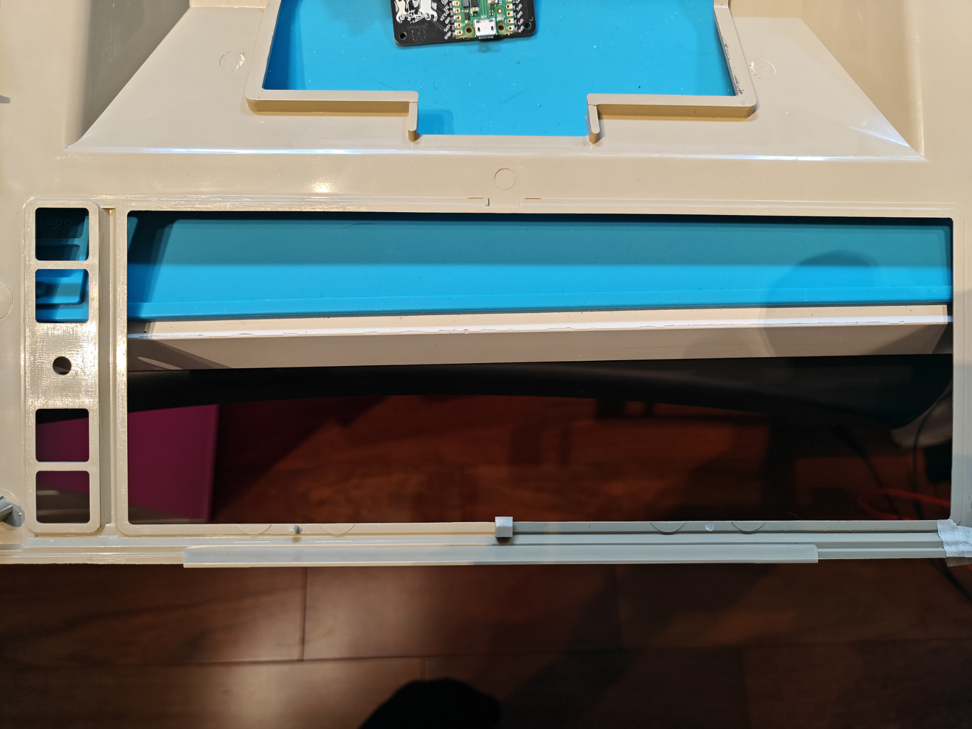
Decent400/Reference/400-above.jpg
