bleroy/3d-junkyard/Decent400/Reference/400-keeb.jpg

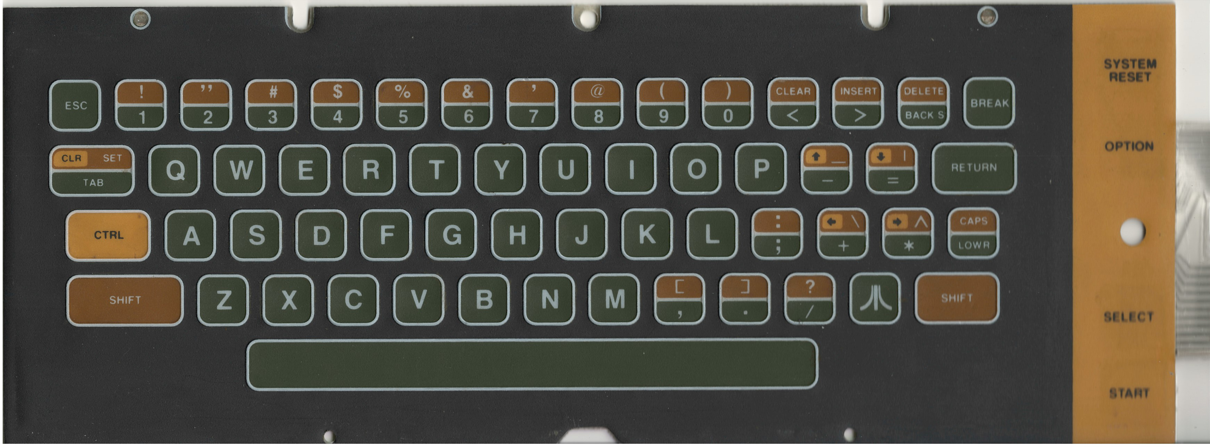
Decent400/Reference/400-keeb.jpg
