bleroy/3d-junkyard/Decent400/Reference/400-under.jpg

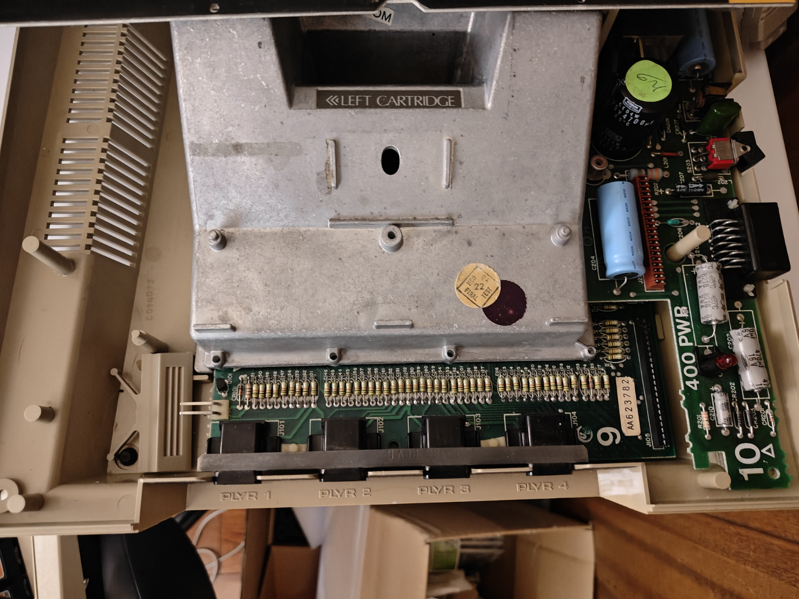
Decent400/Reference/400-under.jpg
