bleroy/3d-junkyard/Decent400/Reference/a400-keeb-back.jpg

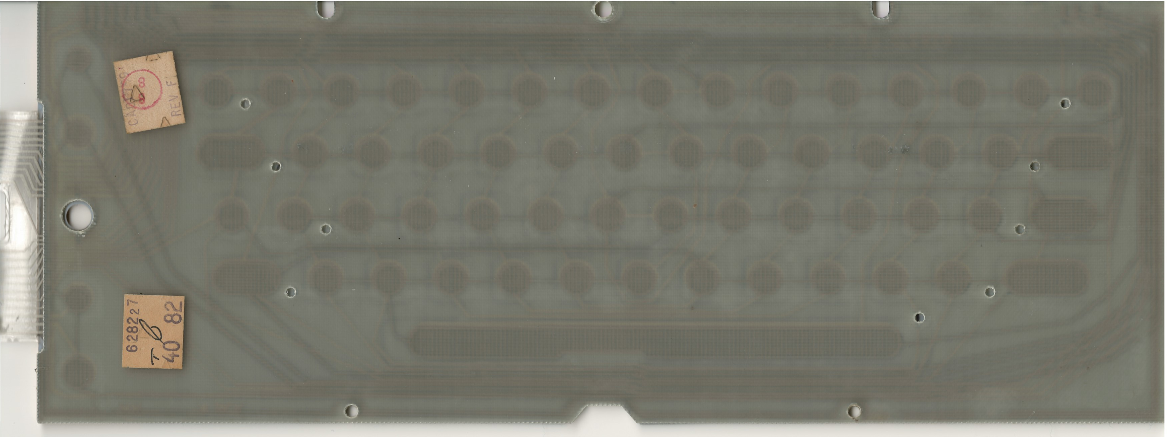
Decent400/Reference/a400-keeb-back.jpg
