bleroy/3d-junkyard/Decent800/Media/Decent800-keyboard-back.png

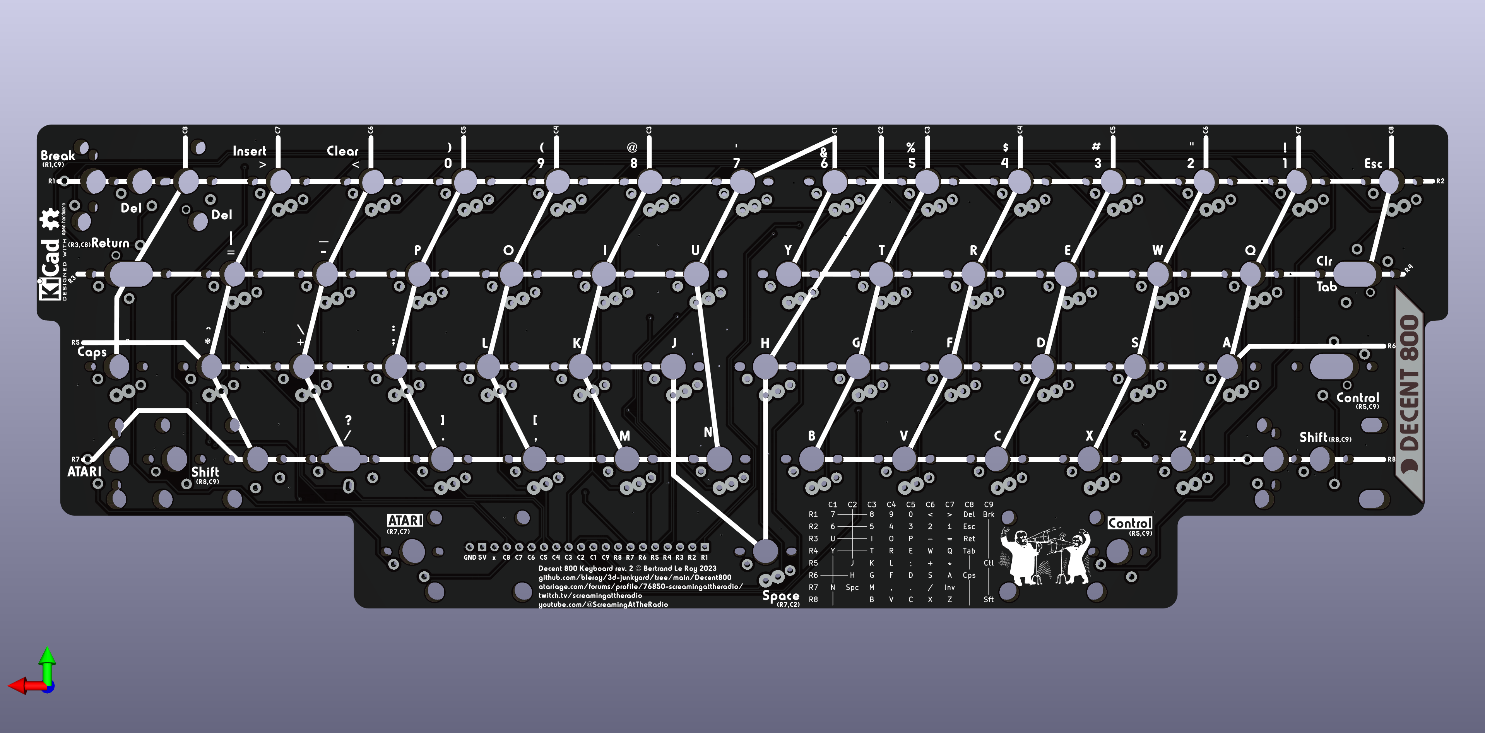
Decent800/Media/Decent800-keyboard-back.png
