bleroy/3d-junkyard/Decent800/Media/Decent800-keyboard-front.png

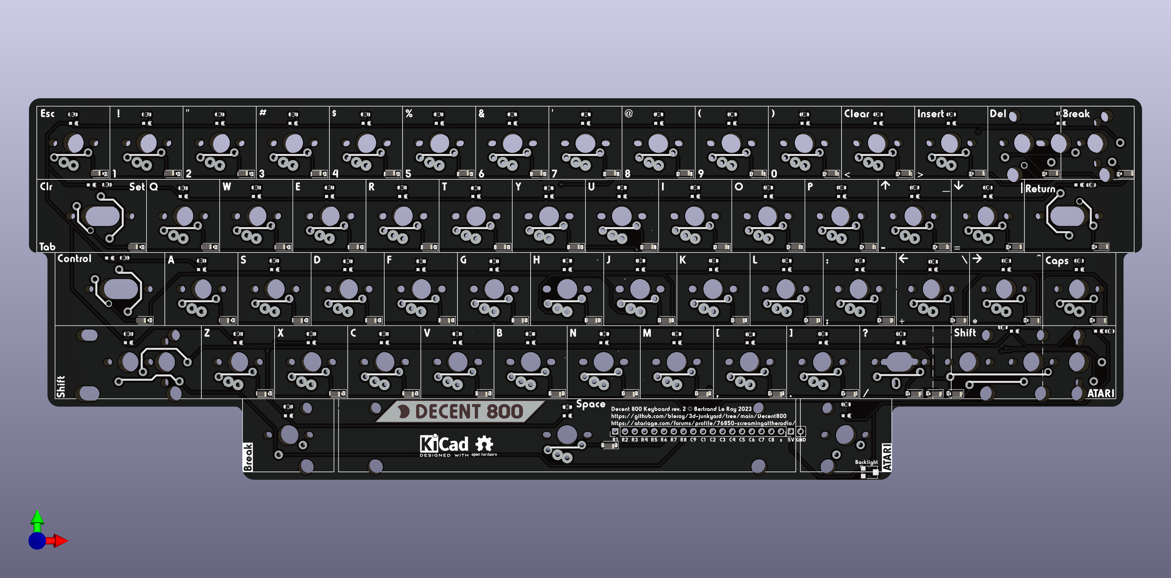
Decent800/Media/Decent800-keyboard-front.png
