bleroy/3d-junkyard/Decent800/Media/Decent800-plate.png

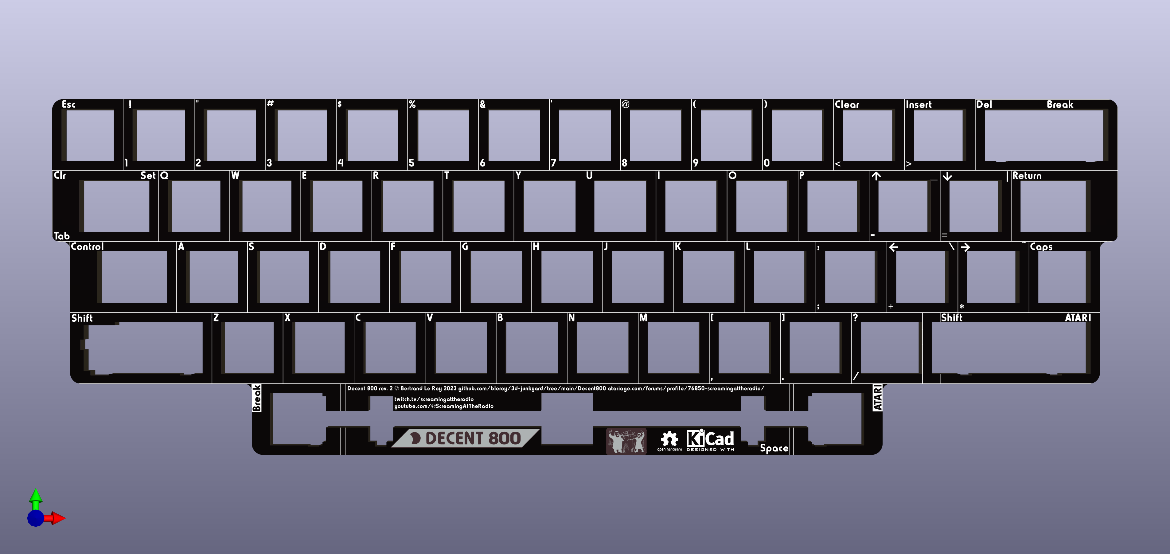
Decent800/Media/Decent800-plate.png
