bleroy/3d-junkyard/Decent800/Reference/Atari800KeyboardPCB-back.jpg

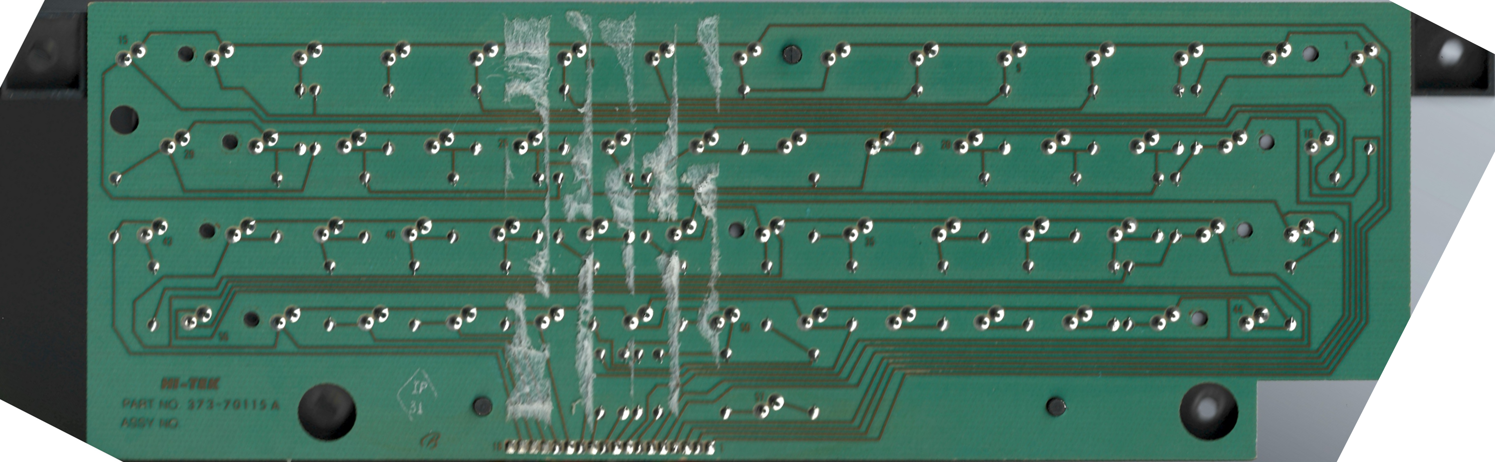
Decent800/Reference/Atari800KeyboardPCB-back.jpg
