bleroy/3d-junkyard/Decent1200/Media/Decent1200-keyboard-front.png

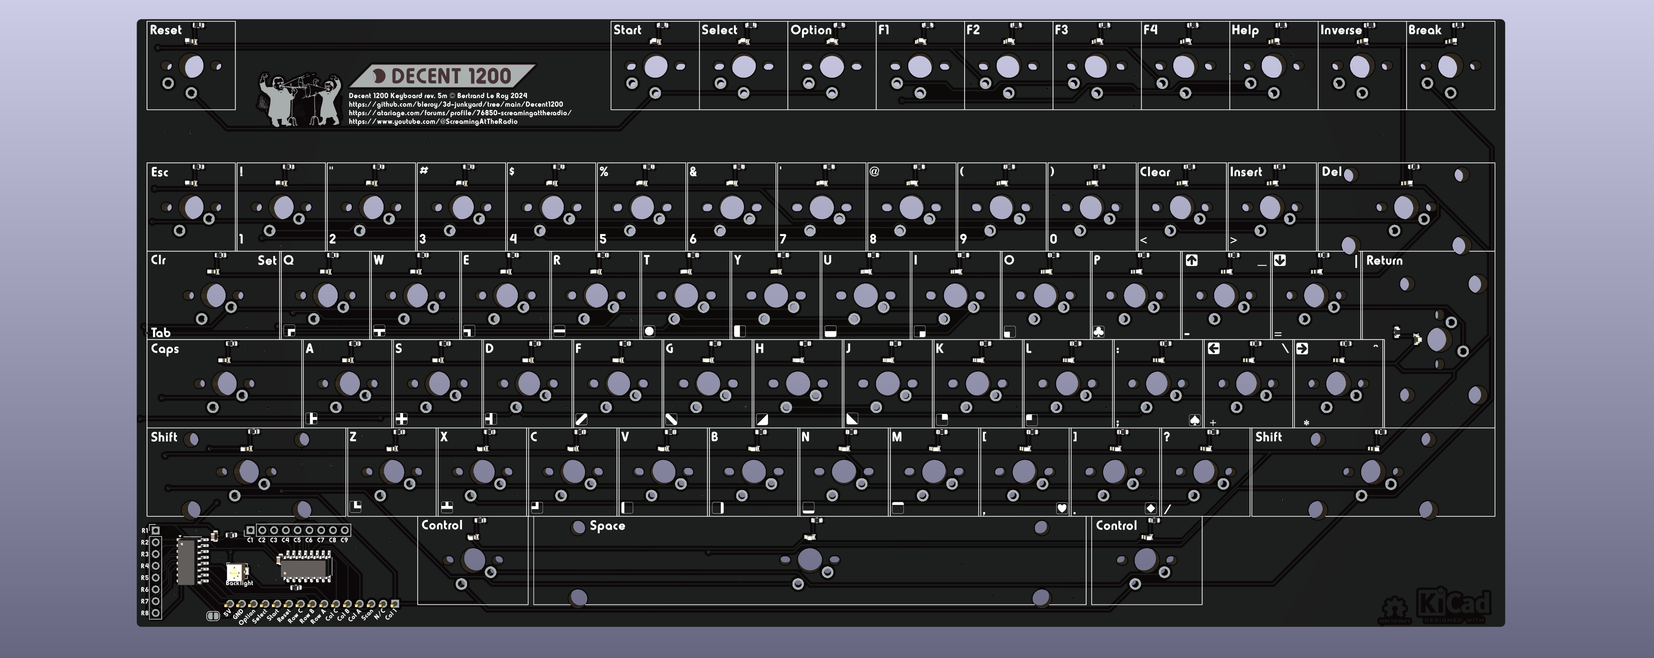
Decent1200/Media/Decent1200-keyboard-front.png
