bleroy/3d-junkyard/Decent1200/Media/decent_atari_1200xl-layout.png

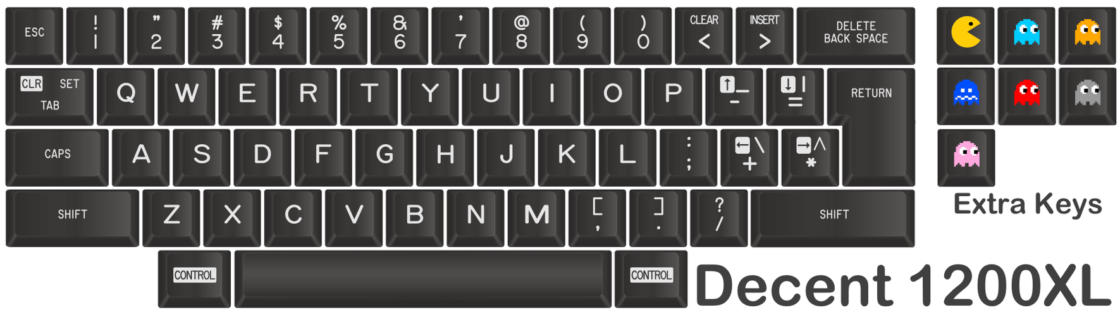
Decent1200/Media/decent_atari_1200xl-layout.png
