bleroy/3d-junkyard/Decent1200/Reference/1200xl_keeb_schematic.png

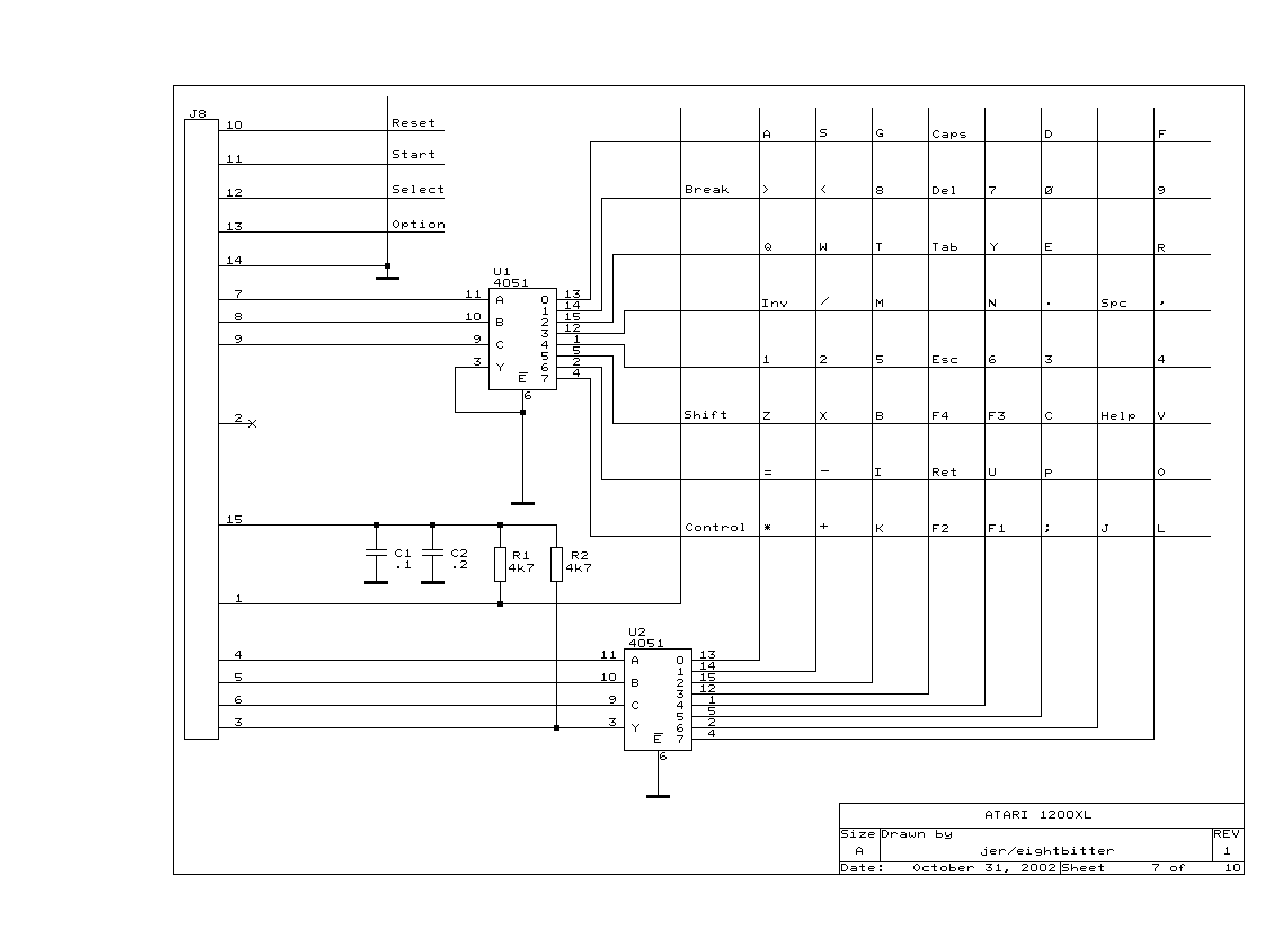
Decent1200/Reference/1200xl_keeb_schematic.png
