bleroy/3d-junkyard/Decent1200/Reference/Frame.jpg

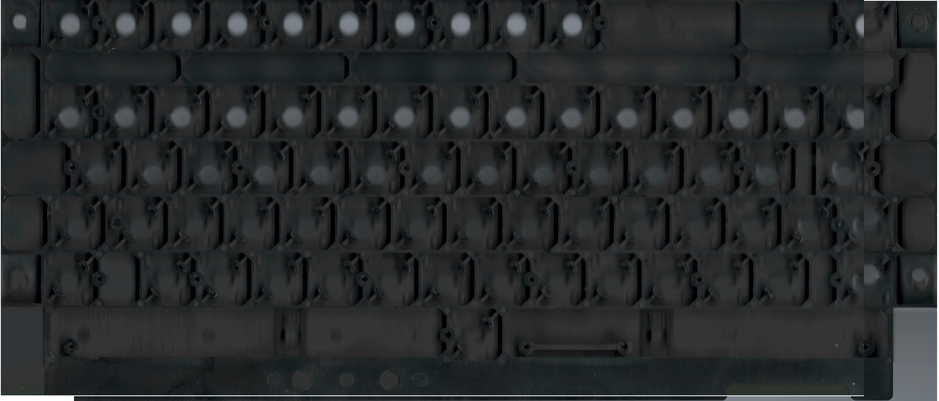
Decent1200/Reference/Frame.jpg
