bleroy/3d-junkyard/Decent1200/Reference/Membrane.jpg

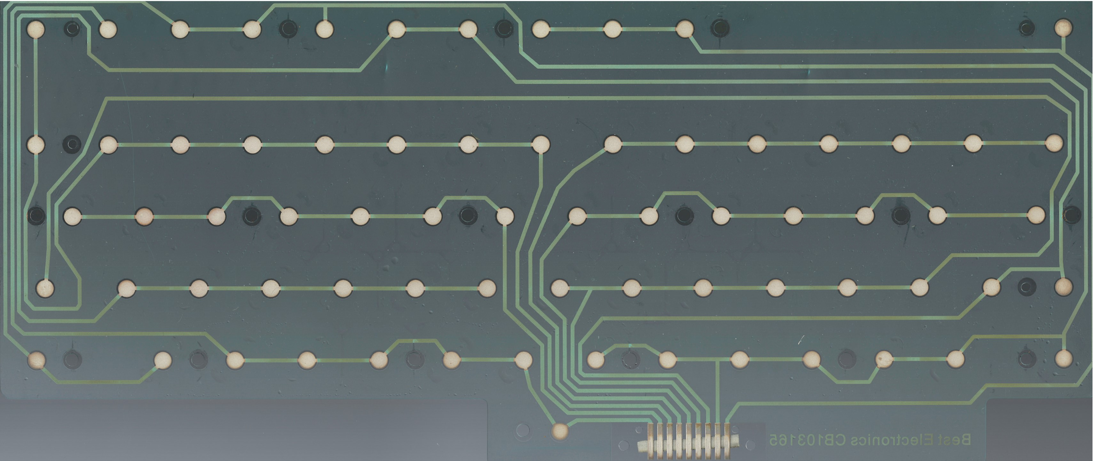
Decent1200/Reference/Membrane.jpg
