bleroy/3d-junkyard/Decent1200/Reference/PCB-back.jpg

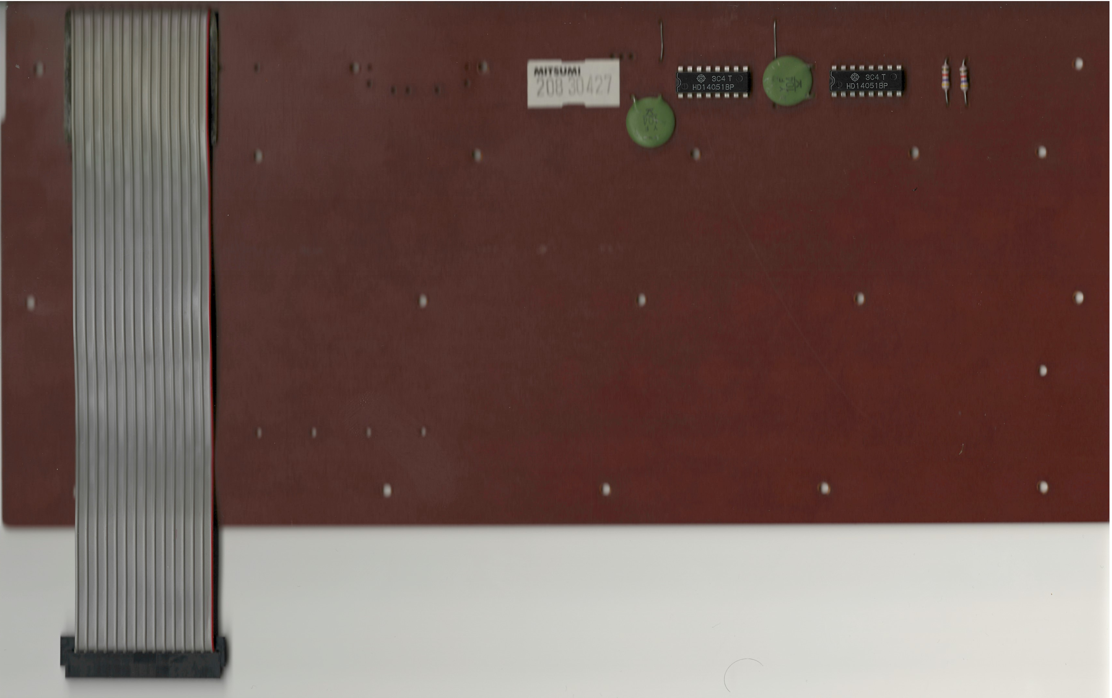
Decent1200/Reference/PCB-back.jpg
