bleroy/3d-junkyard/Decent1200/Reference/PCB-front.jpg

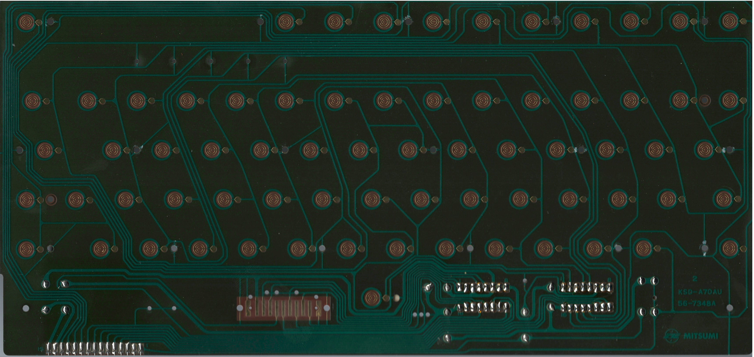
Decent1200/Reference/PCB-front.jpg
