bleroy/3d-junkyard/DecentCart/Media/DecentCart2040-PCB-back.png

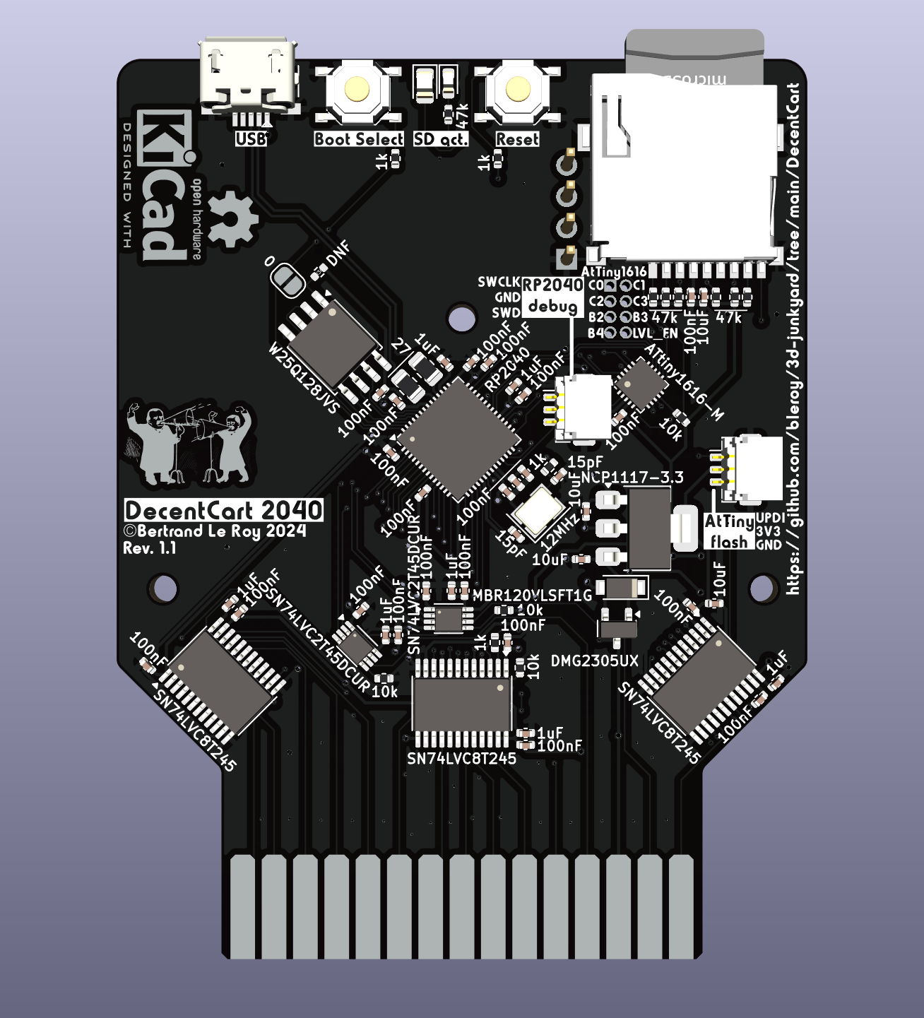
DecentCart/Media/DecentCart2040-PCB-back.png
