bleroy/3d-junkyard/DecentCart/Media/DecentCart2040-PCB-front.png

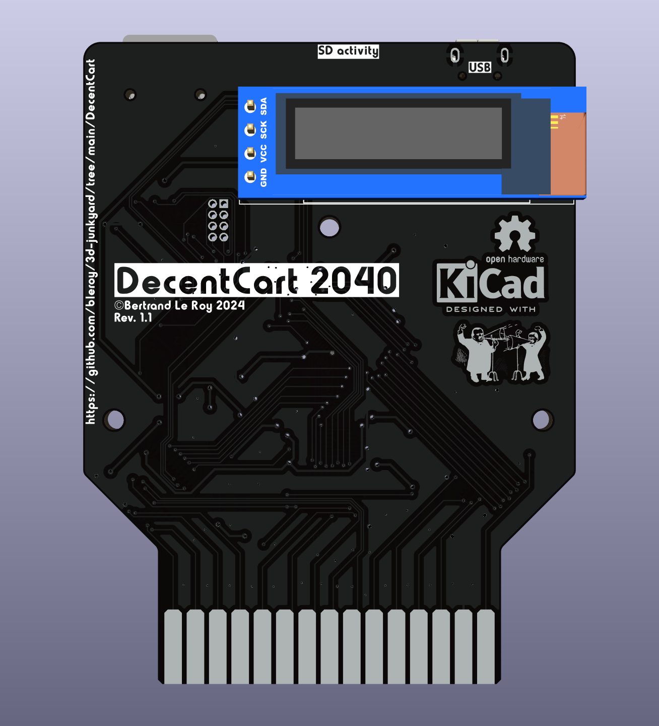
DecentCart/Media/DecentCart2040-PCB-front.png
