bleroy/3d-junkyard/DecentCart/Media/DecentCart2350-PCB-back.png

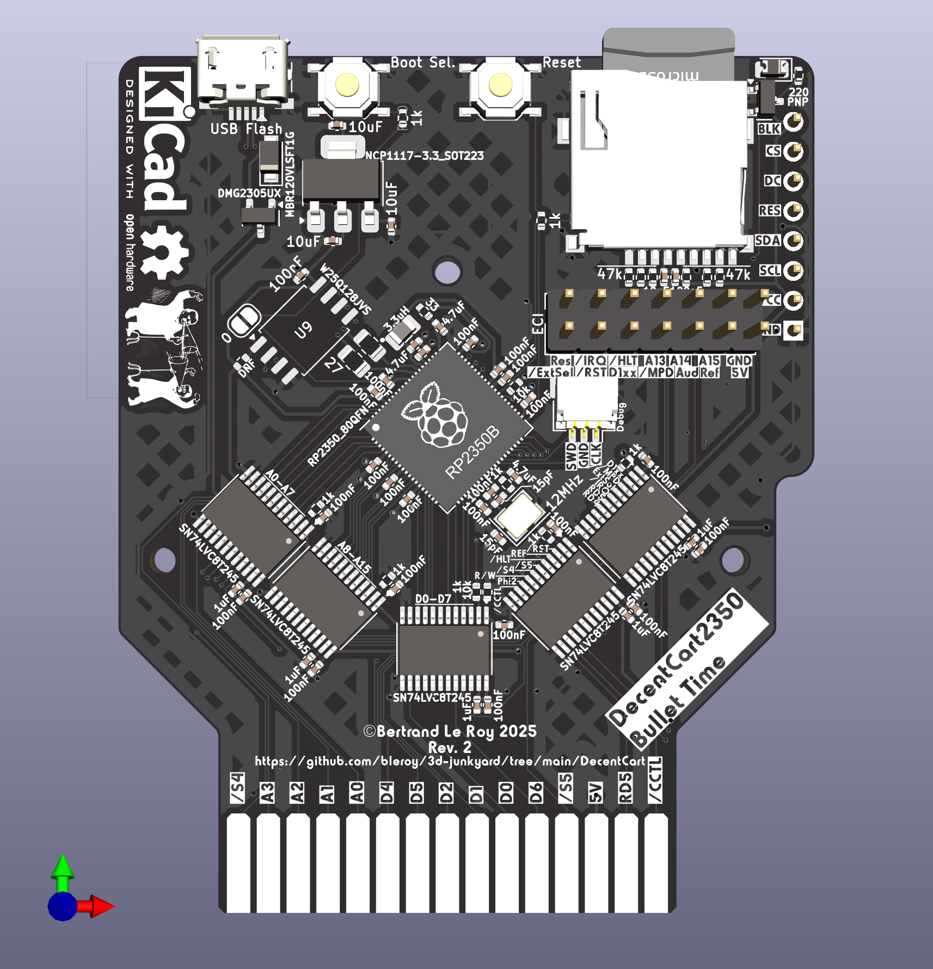
DecentCart/Media/DecentCart2350-PCB-back.png
