bleroy/3d-junkyard/DecentCart/Media/DecentCart2350-PCB-front.png

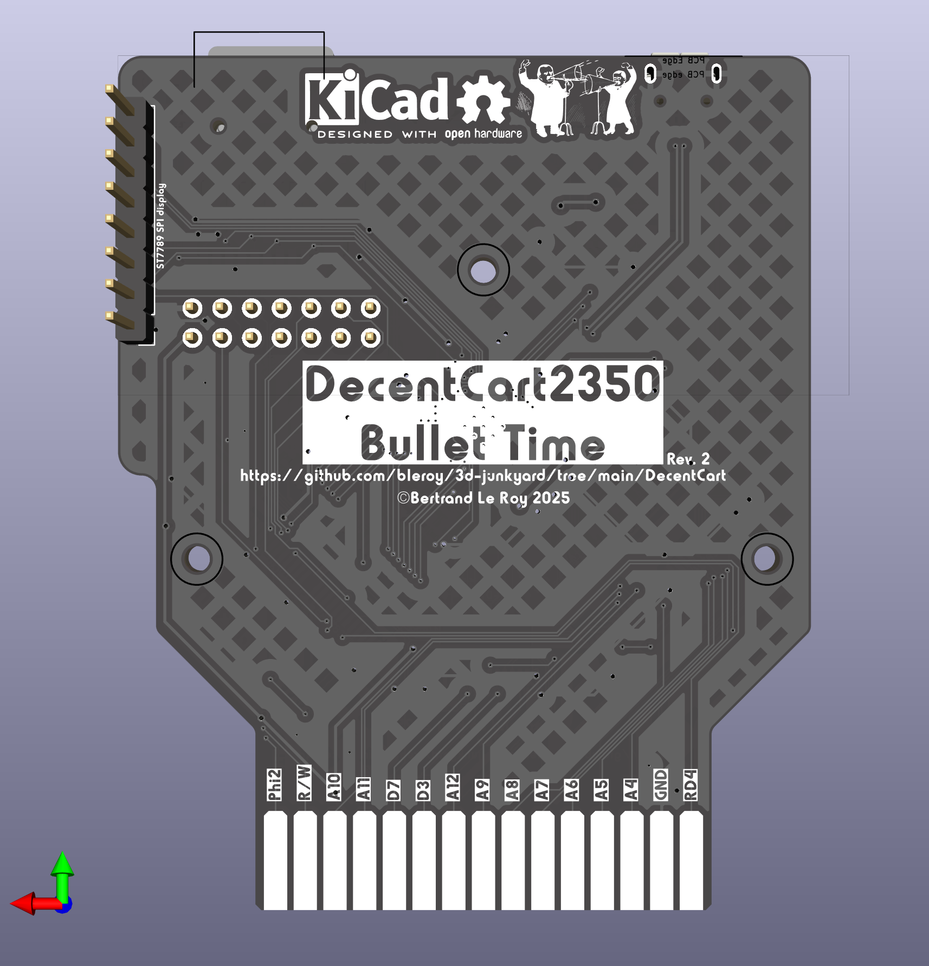
DecentCart/Media/DecentCart2350-PCB-front.png
