bleroy/3d-junkyard/DecentCart/Media/DecentCart2354B-PCB-back.png

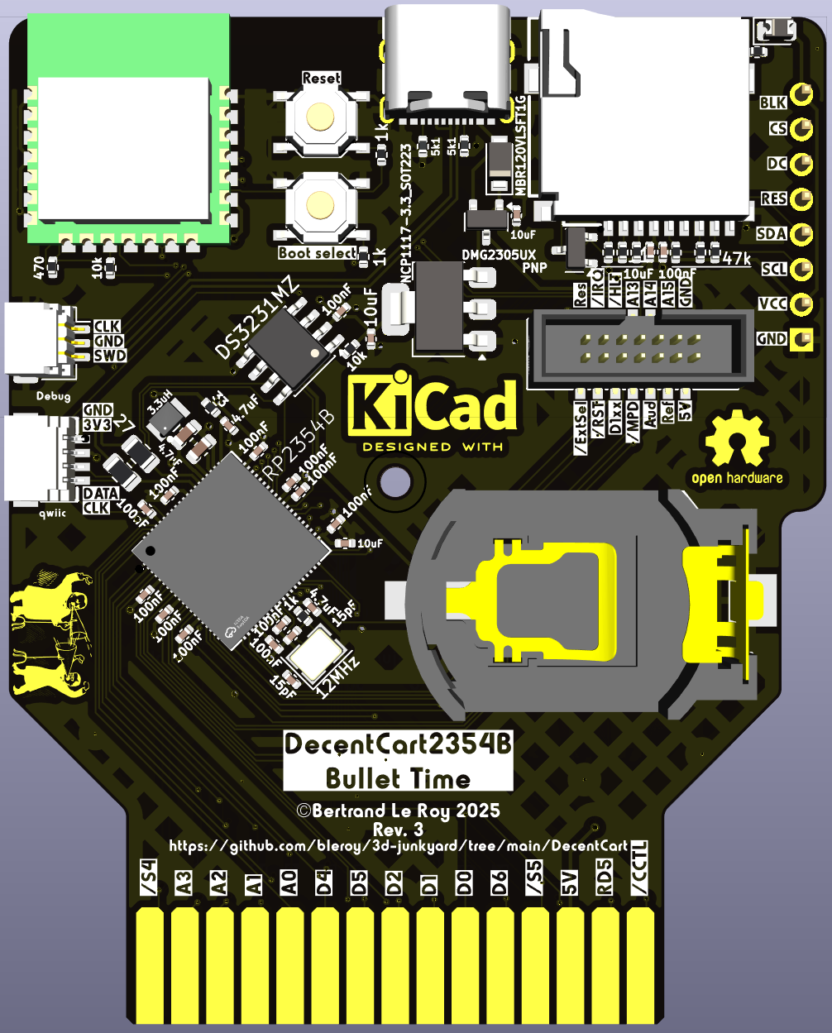
DecentCart/Media/DecentCart2354B-PCB-back.png
