bleroy/3d-junkyard/DecentCart/Media/DecentCart2354B-PCB-front.png

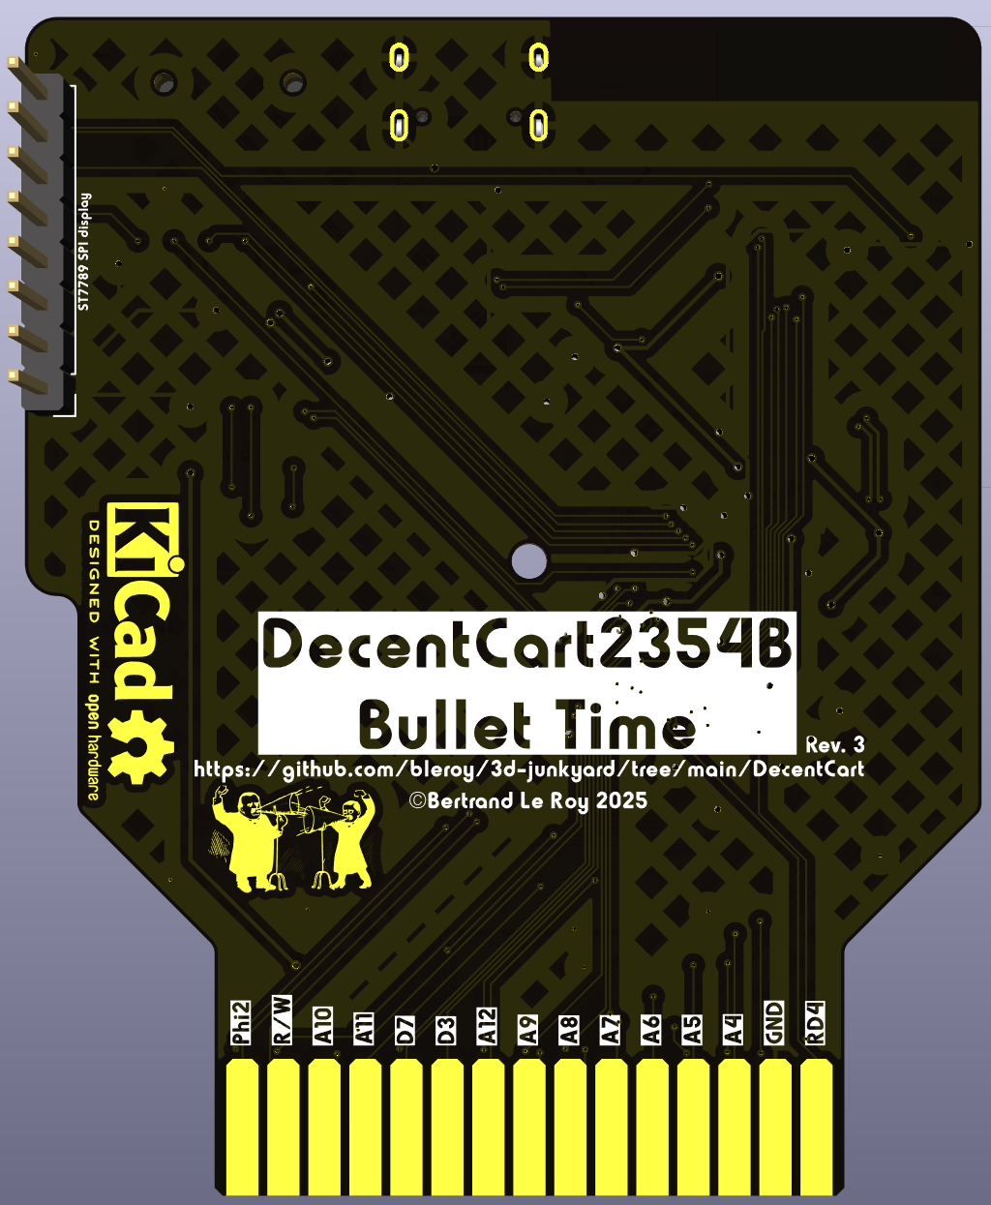
DecentCart/Media/DecentCart2354B-PCB-front.png
