bleroy/3d-junkyard/DecentCart/Media/DecentCart5200-PCB-back.png

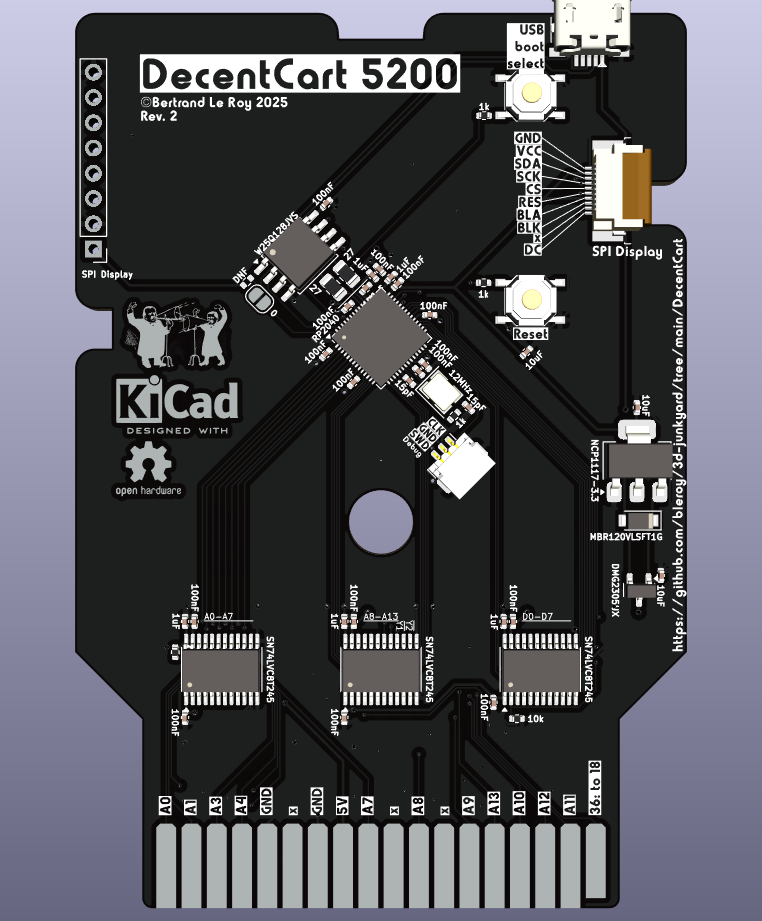
DecentCart/Media/DecentCart5200-PCB-back.png
