bleroy/3d-junkyard/DecentCart/Media/DecentCart5200-PCB-front.png

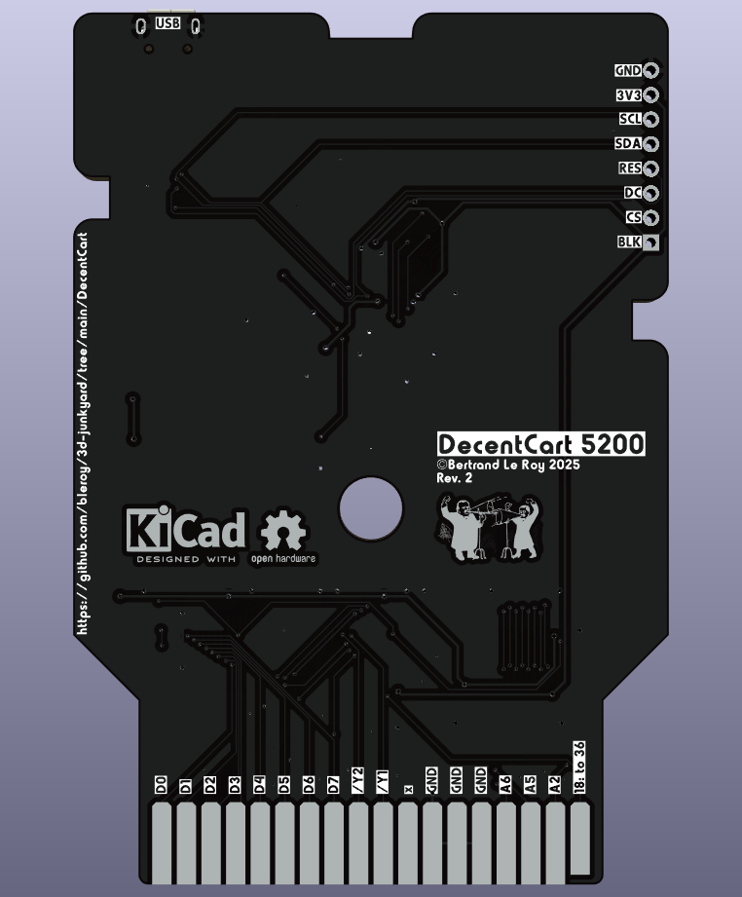
DecentCart/Media/DecentCart5200-PCB-front.png
