bleroy/3d-junkyard/DecenTKL/Media/DecenTKL-back.png

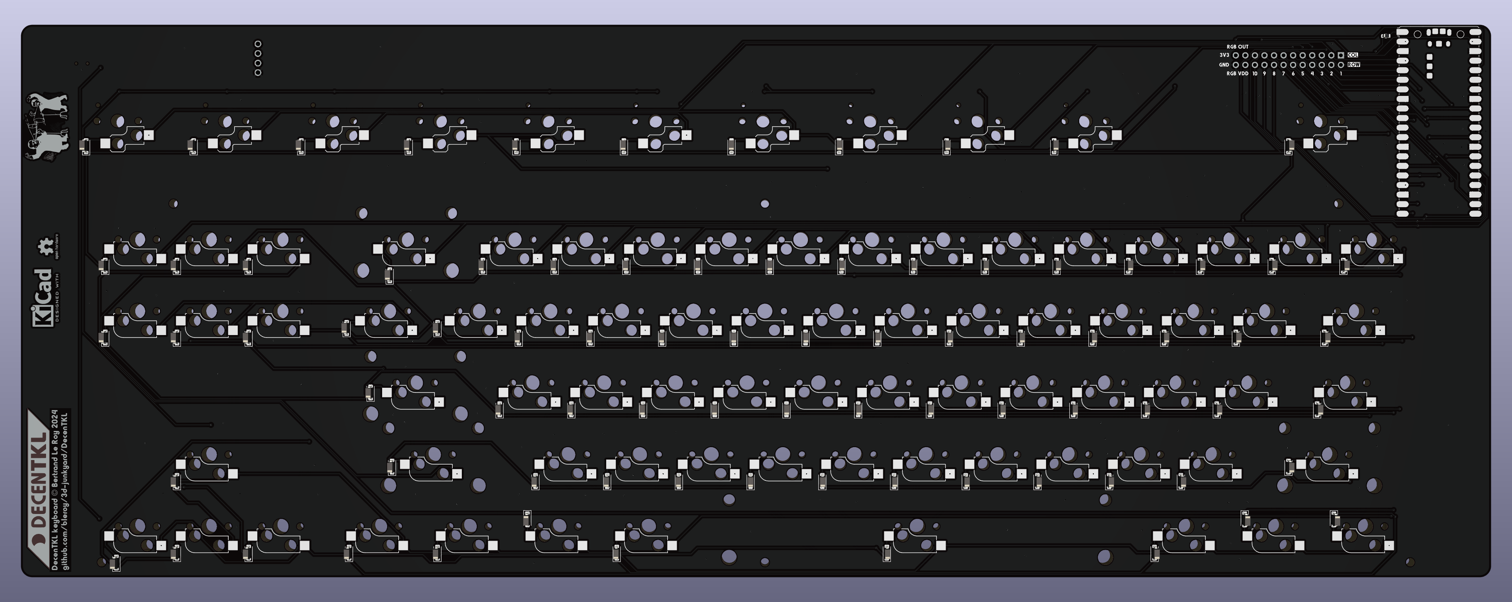
DecenTKL/Media/DecenTKL-back.png
