bleroy/3d-junkyard/DecenTKL/Media/DecenTKL-front.png

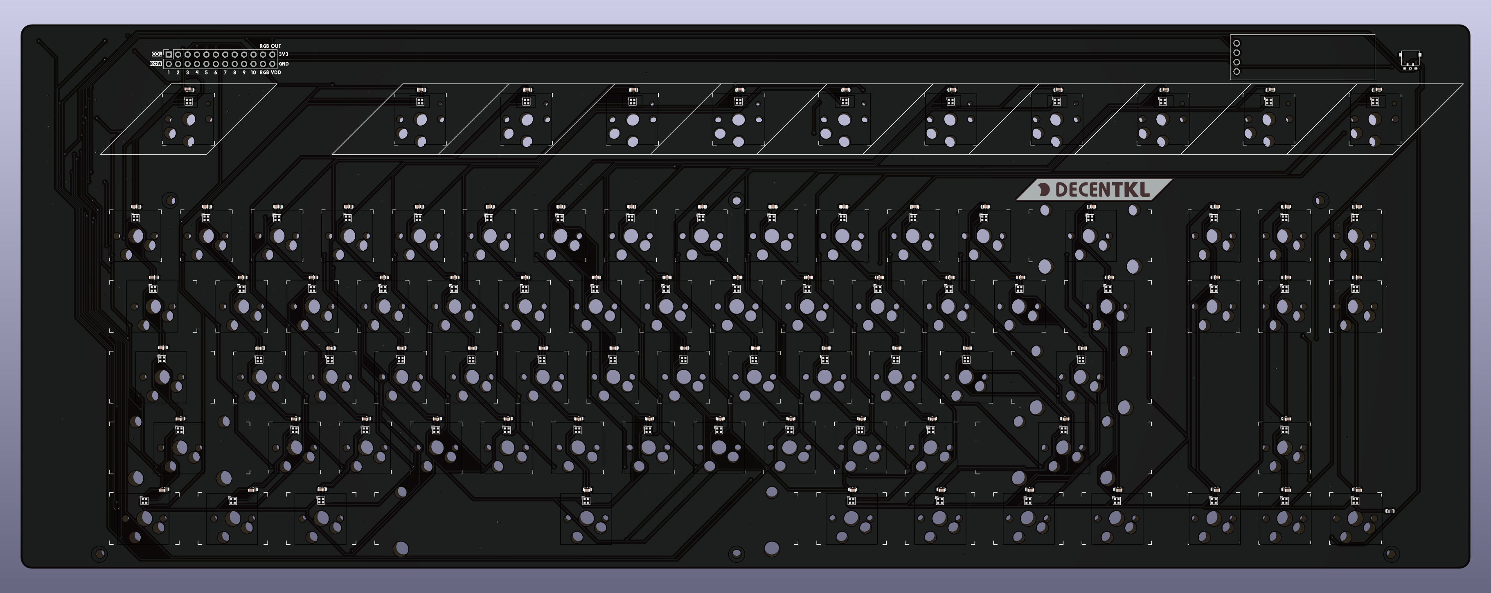
DecenTKL/Media/DecenTKL-front.png
