bleroy/3d-junkyard/DecenTKL/Media/DecenTKL-plate.png

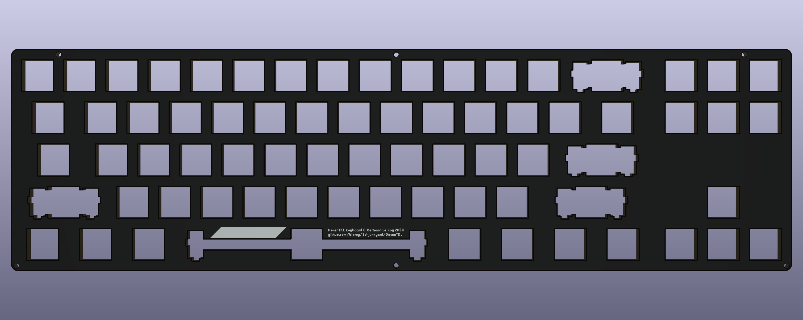
DecenTKL/Media/DecenTKL-plate.png
