bleroy/3d-junkyard/DecenTKL/Media/DecenTKL.jpg

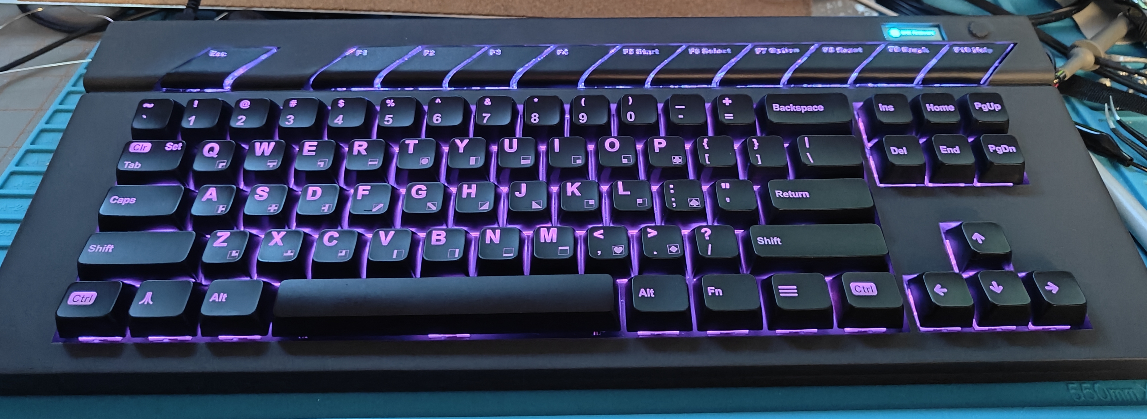
DecenTKL/Media/DecenTKL.jpg
