bleroy/3d-junkyard/DecenTKL/Media/NumPad-back.png

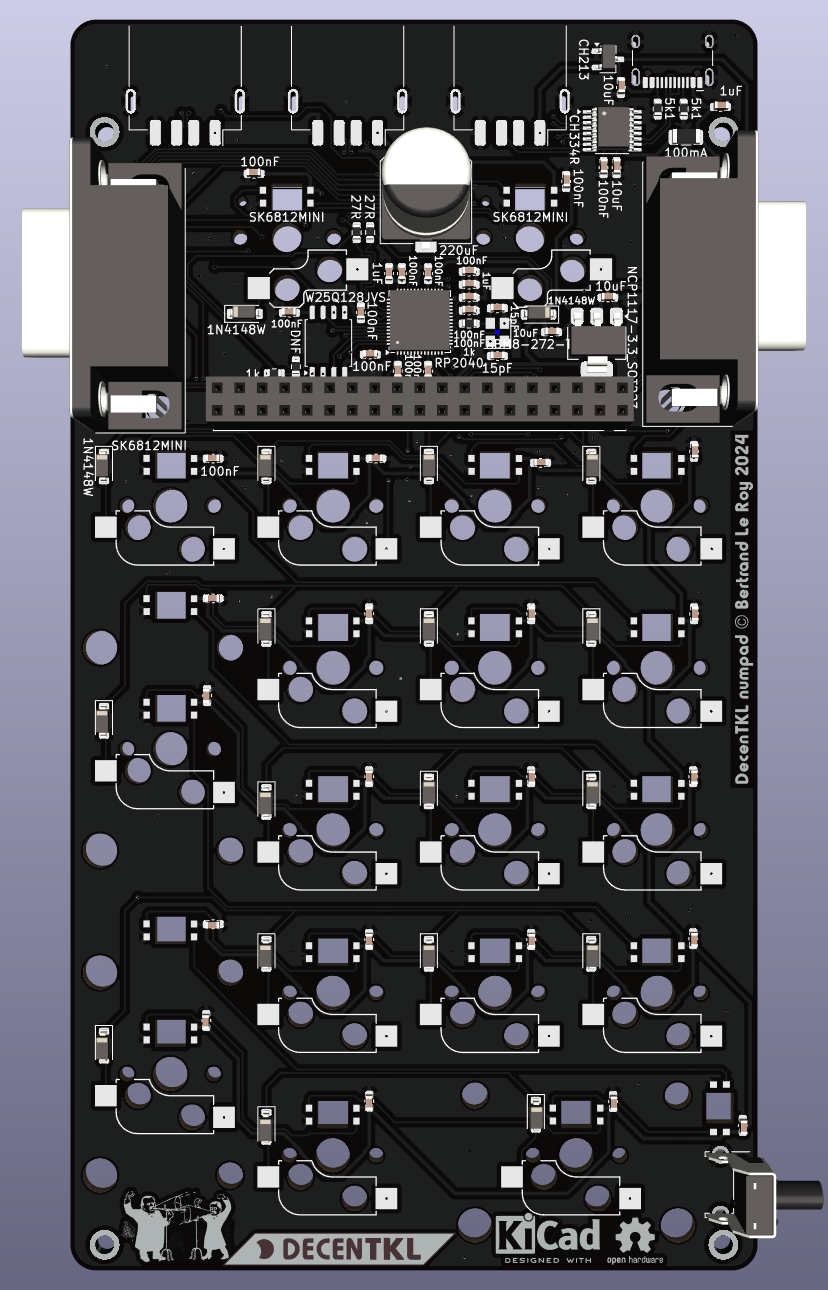
DecenTKL/Media/NumPad-back.png
