bleroy/3d-junkyard/DecenTKL/Media/NumPad-front.png

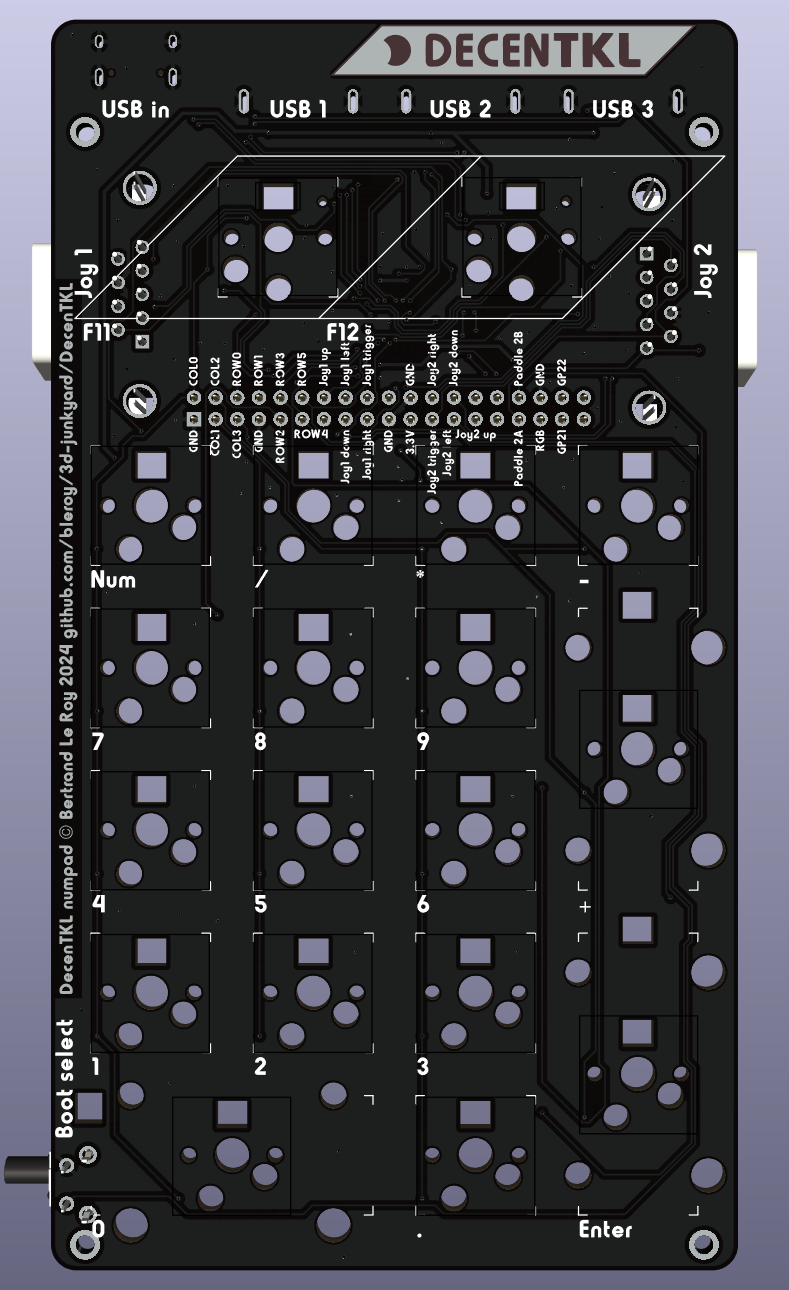
DecenTKL/Media/NumPad-front.png
