bleroy/3d-junkyard/DecenTKL/Media/NumPadPlate.png

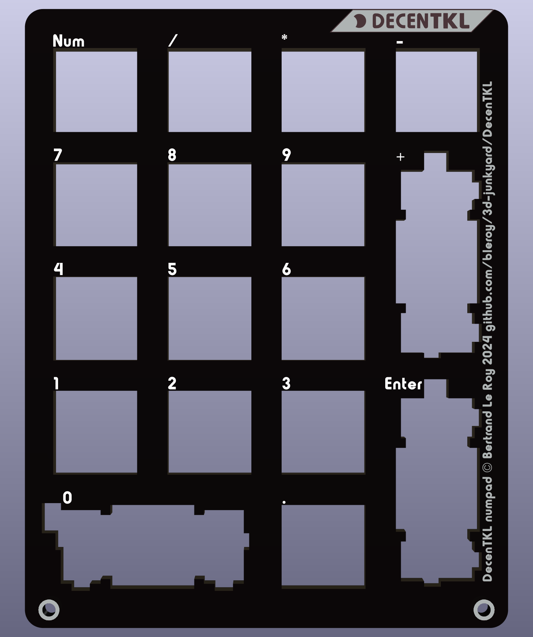
DecenTKL/Media/NumPadPlate.png
