bleroy/3d-junkyard/DecentUSB/Media/DecentUSB-back.png

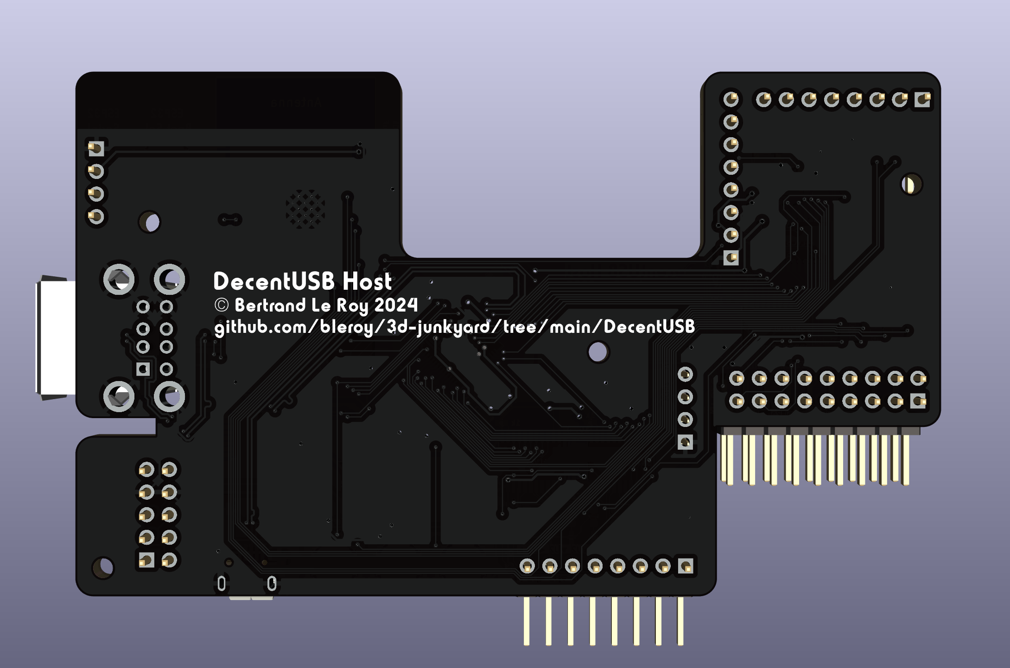
DecentUSB/Media/DecentUSB-back.png
