bleroy/3d-junkyard/DecentUSB/Media/DecentUSB-front.png

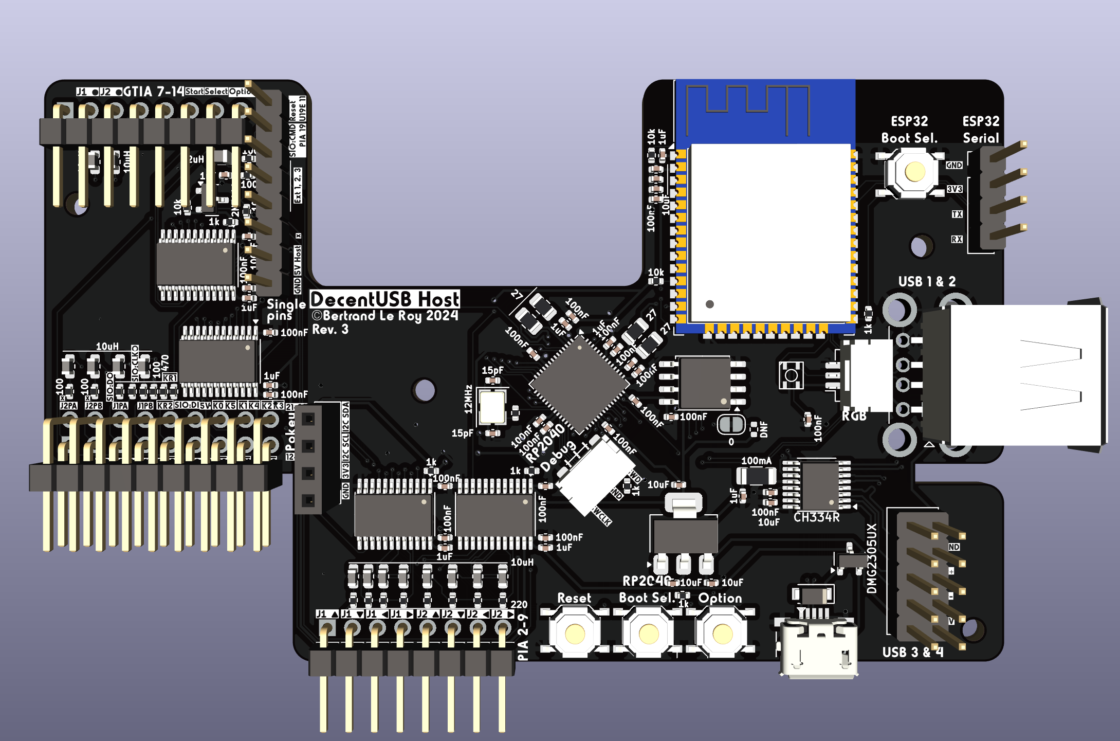
DecentUSB/Media/DecentUSB-front.png
