bleroy/3d-junkyard/DecentUSB/Reference/K3K4K5-Col1.png

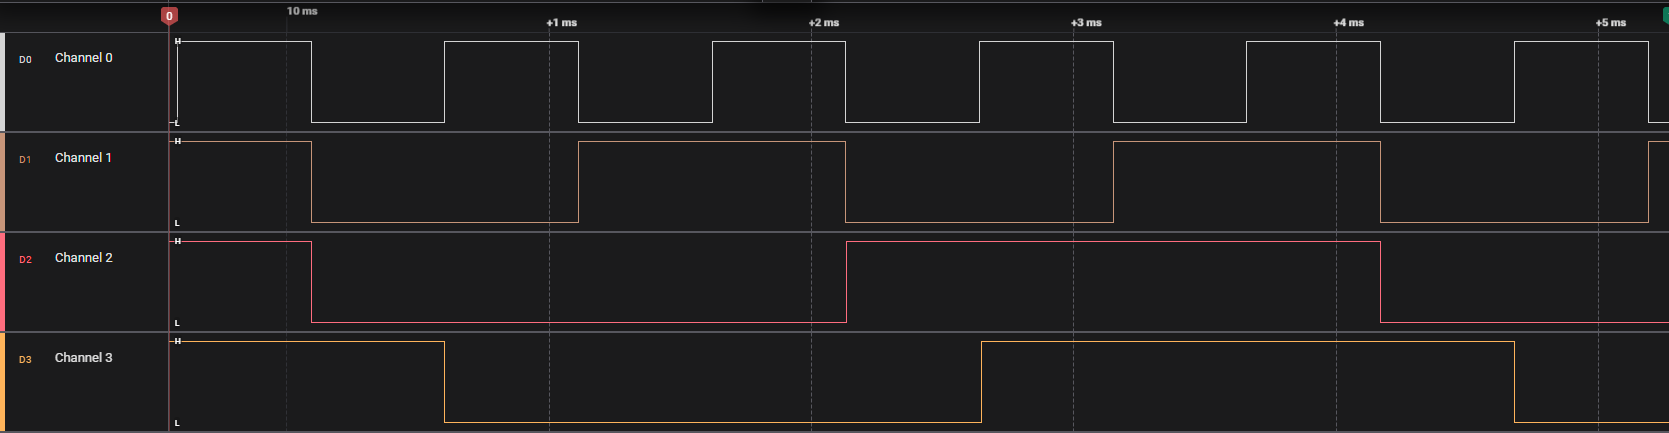
DecentUSB/Reference/K3K4K5-Col1.png
