bleroy/3d-junkyard/DecentUSB/Reference/K3K4K5-Col3.png

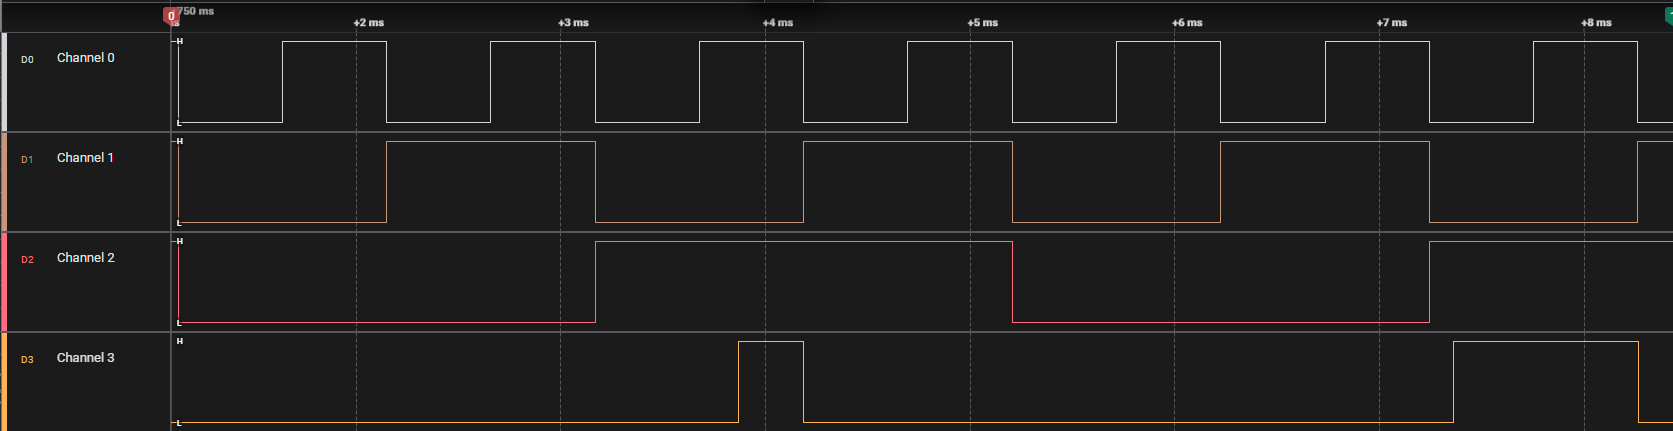
DecentUSB/Reference/K3K4K5-Col3.png
