bleroy/3d-junkyard/DecentUSB/Reference/PokeyCycle_A.png

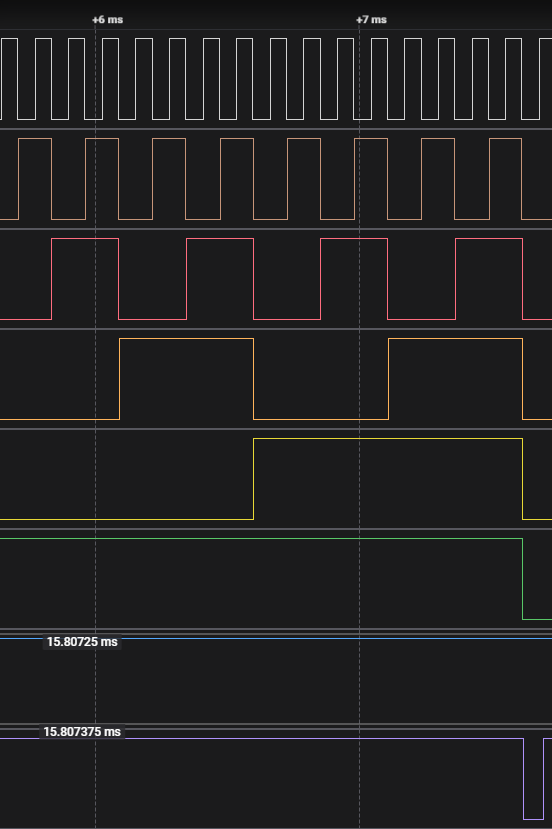
DecentUSB/Reference/PokeyCycle_A.png
