bleroy/3d-junkyard/DecentXE/Caps/AtariXE space bar cap sides reference.jpg

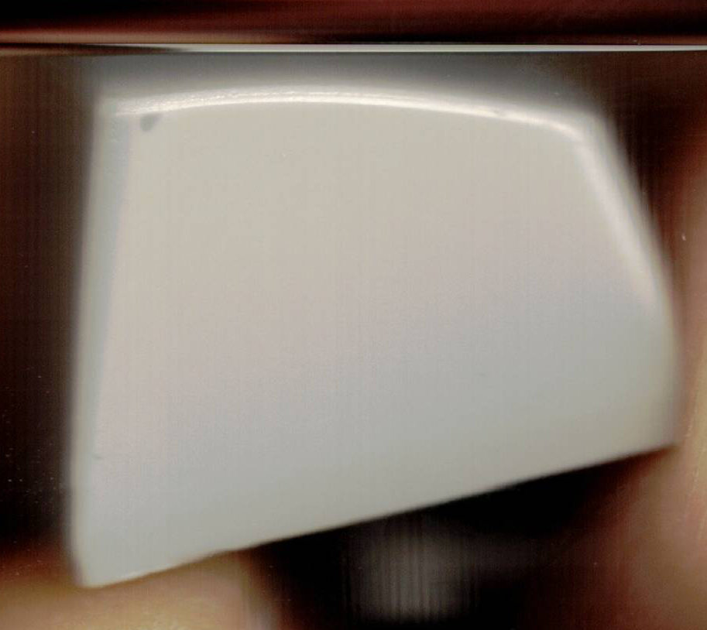
DecentXE/Caps/AtariXE space bar cap sides reference.jpg
