bleroy/3d-junkyard/DecentXE/Media/DecentXE-LowPro.png

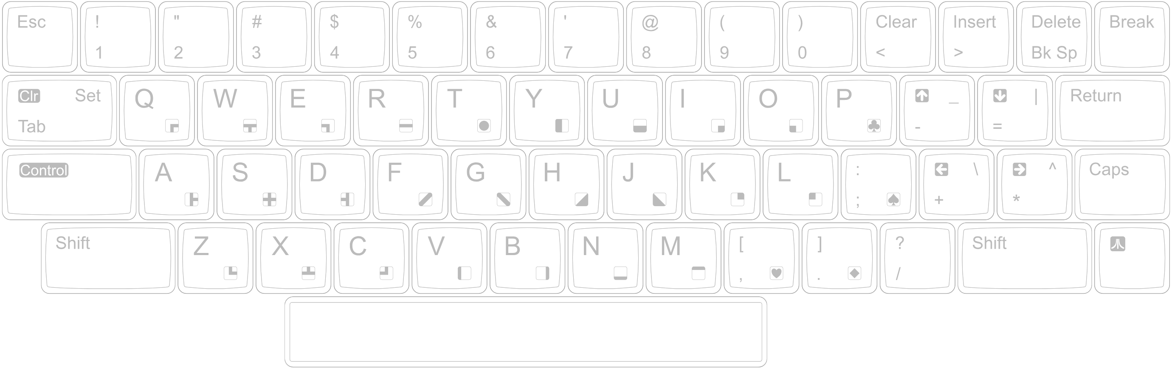
DecentXE/Media/DecentXE-LowPro.png
