bleroy/3d-junkyard/DecentXE/Media/DecentXE-Modern-back.png

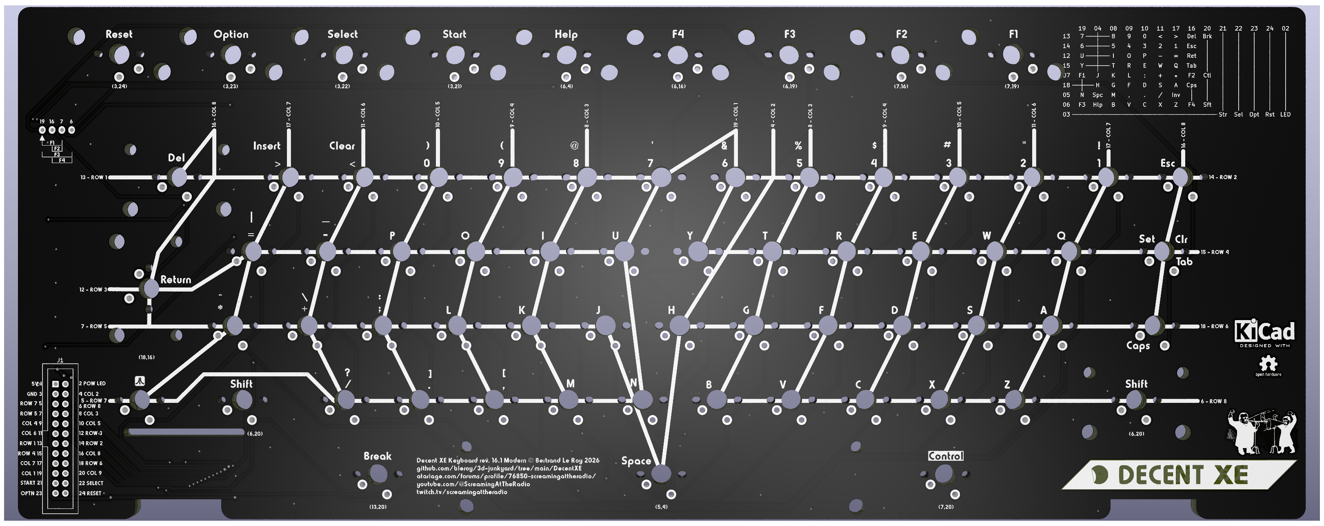
DecentXE/Media/DecentXE-Modern-back.png
