bleroy/3d-junkyard/DecentXE/Media/Vintage.jpg

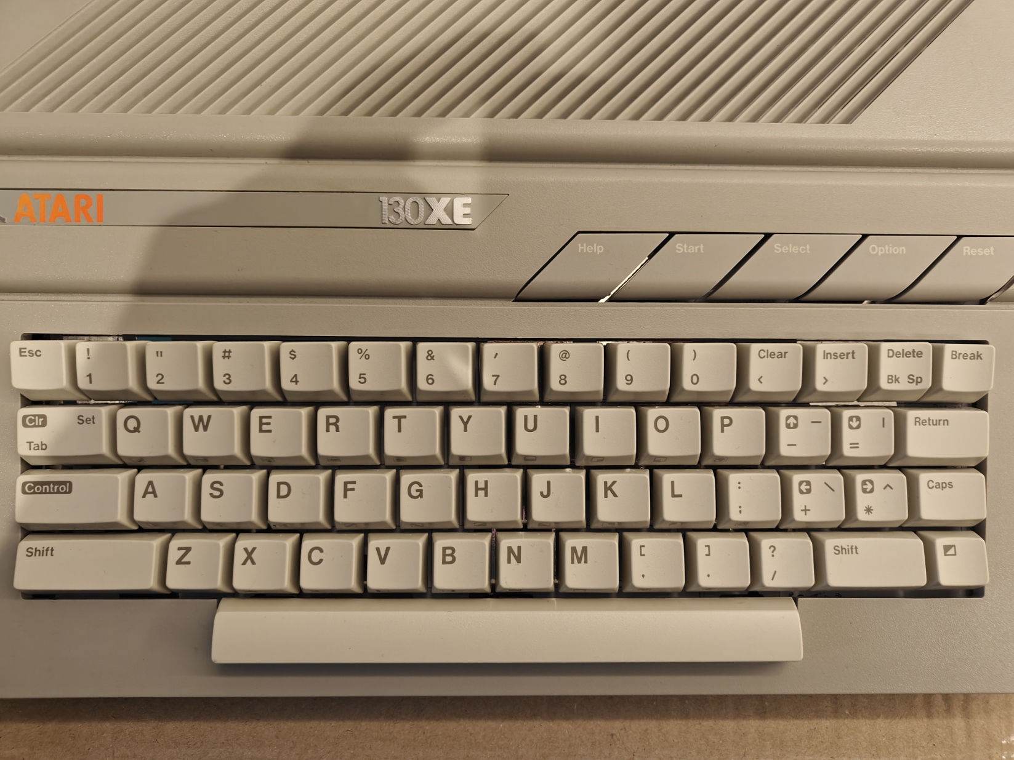
DecentXE/Media/Vintage.jpg
