bleroy/3d-junkyard/DecentXL/Media/DecentXL-keyboard-modern-back.png

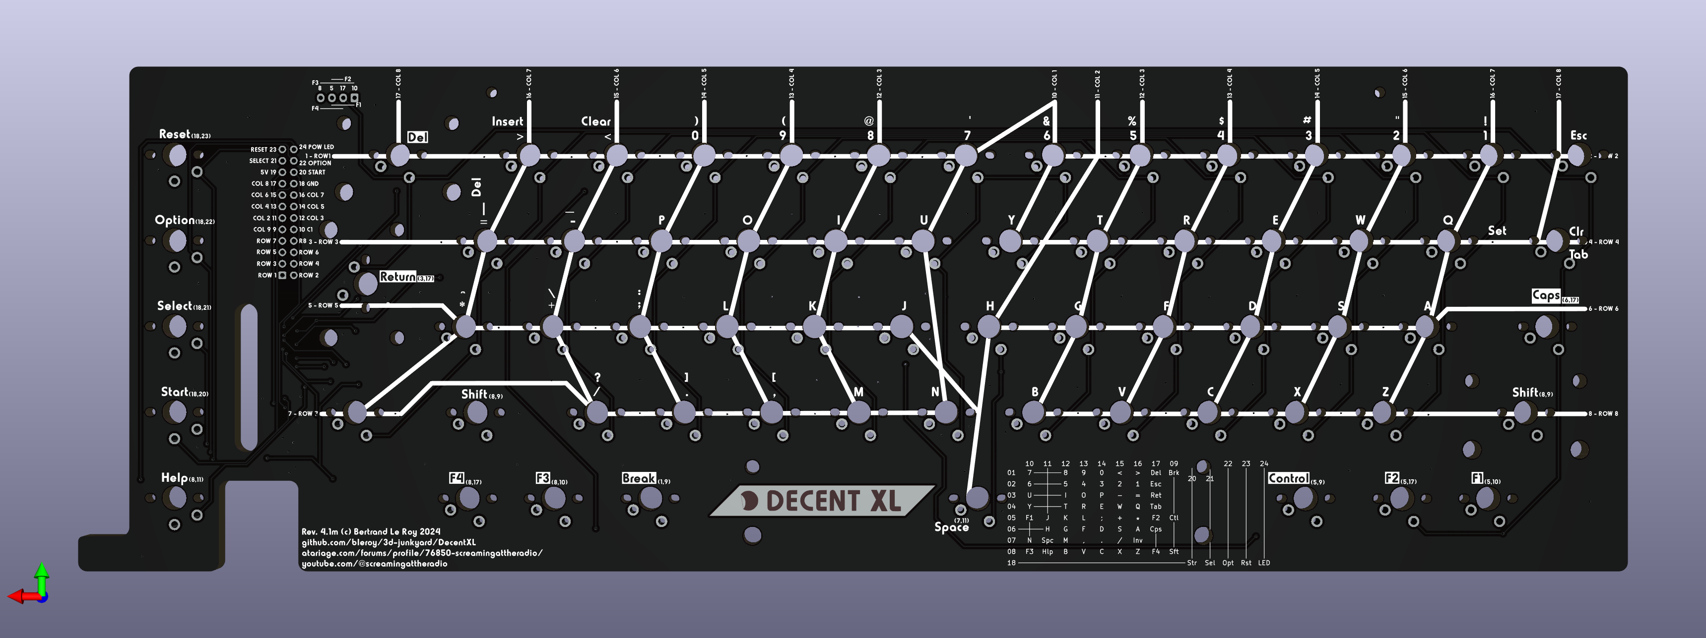
DecentXL/Media/DecentXL-keyboard-modern-back.png
