bleroy/3d-junkyard/DecentXL/Media/DecentXL-keyboard-vintage-back.png

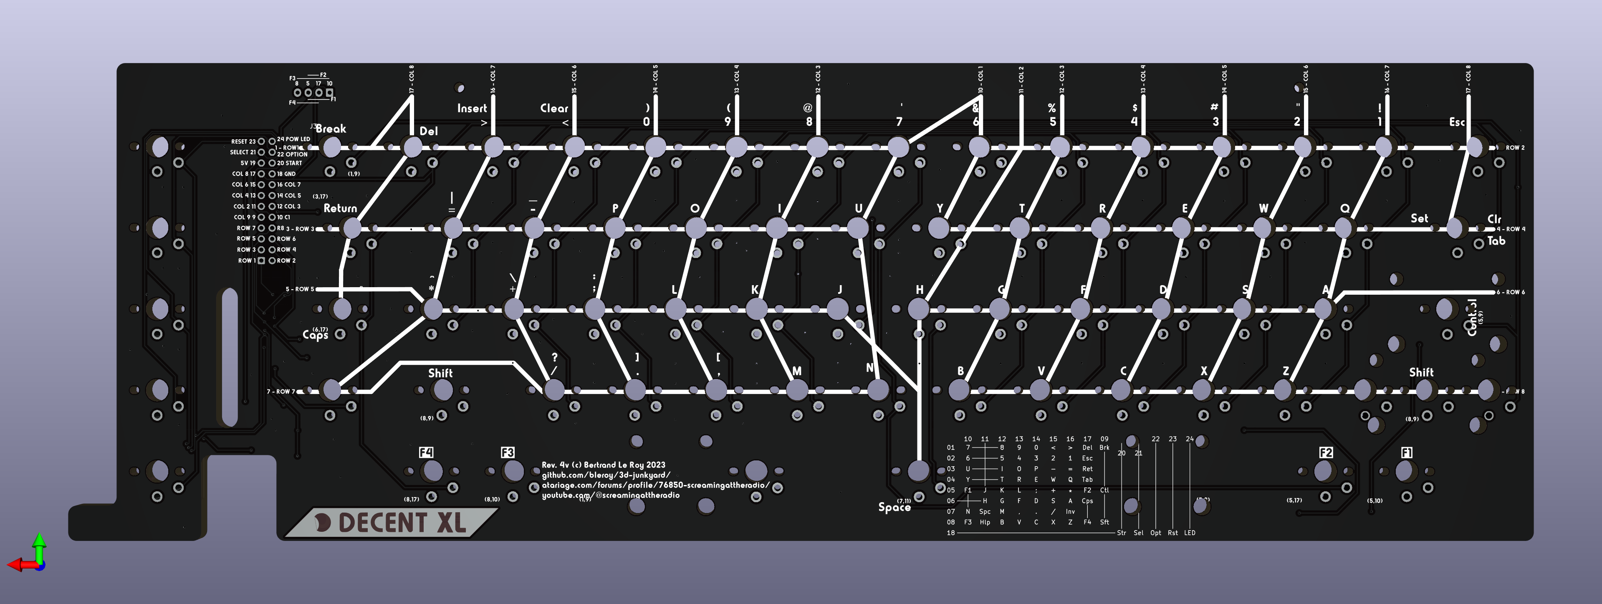
DecentXL/Media/DecentXL-keyboard-vintage-back.png
