bleroy/3d-junkyard/DecentXL/Media/DecentXL-layout-modern.png

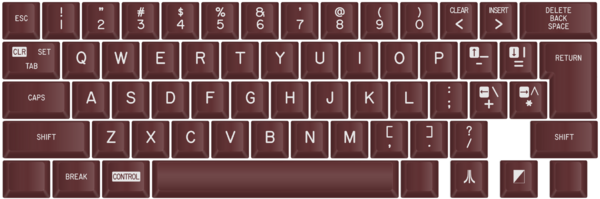
DecentXL/Media/DecentXL-layout-modern.png
