bleroy/3d-junkyard/DecentXL/Media/KailhChocv2.jpg

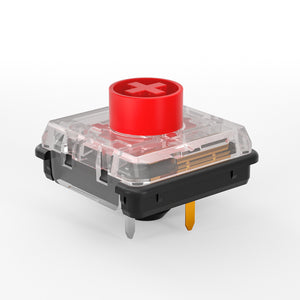
DecentXL/Media/KailhChocv2.jpg
