bleroy/3d-junkyard/DecentXL/Media/MX-Alps.jpg

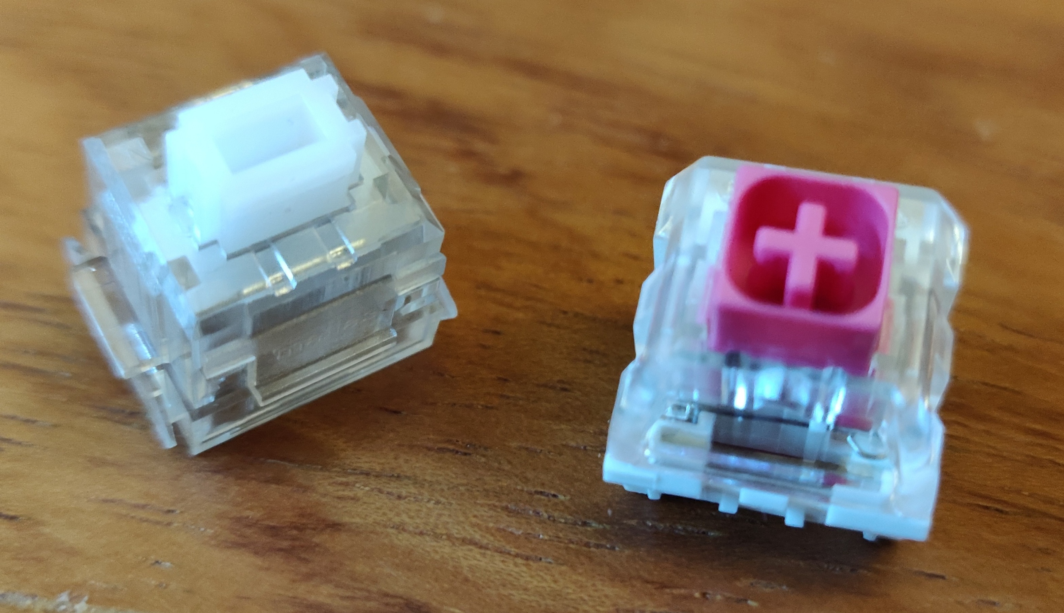
DecentXL/Media/MX-Alps.jpg
