bleroy/3d-junkyard/DungeonMaster/img/Background.png

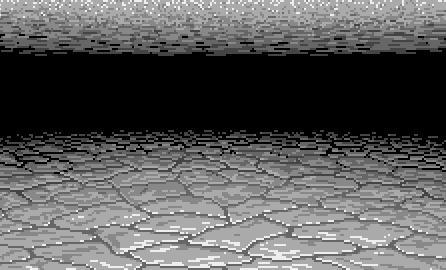
DungeonMaster/img/Background.png
