bleroy/3d-junkyard/DungeonMaster/img/FrontFar.png

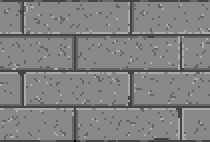
DungeonMaster/img/FrontFar.png
