bleroy/3d-junkyard/DungeonMaster/img/FrontNear.png

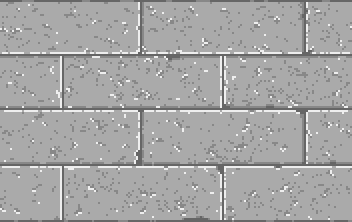
DungeonMaster/img/FrontNear.png
