bleroy/3d-junkyard/DungeonMaster/img/WallLeft.png

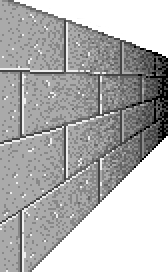
DungeonMaster/img/WallLeft.png
