bleroy/3d-junkyard/DungeonMaster/img/WallRight.png

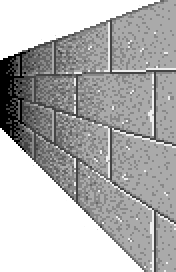
DungeonMaster/img/WallRight.png
