bleroy/3d-junkyard/FFT/assets/chicoree.png

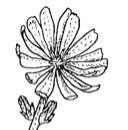
FFT/assets/chicoree.png
