bleroy/3d-junkyard/Jaggilines/assets/cockpit.png

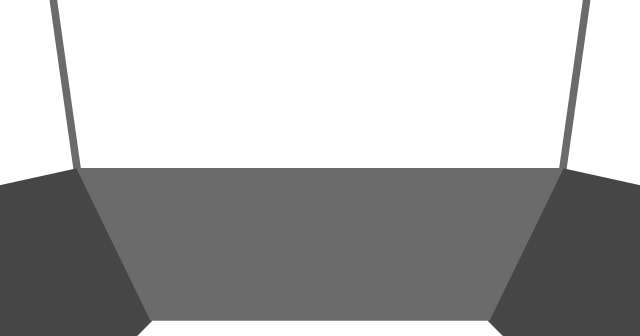
Jaggilines/assets/cockpit.png
