bleroy/3d-junkyard/Jaggilines/assets/Valkyrie.png

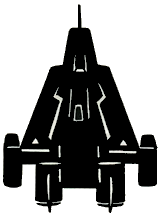
Jaggilines/assets/Valkyrie.png
