bleroy/3d-junkyard/JoyKeyMX/JoyKeyMini.png

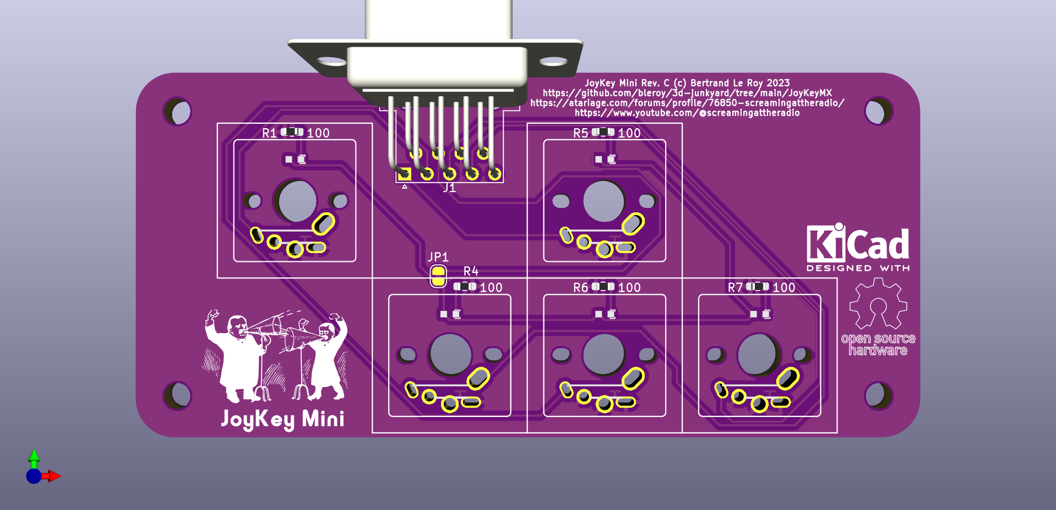
JoyKeyMX/JoyKeyMini.png
