bleroy/3d-junkyard/JoyKeyMX/JoyKeyXL_Back.png

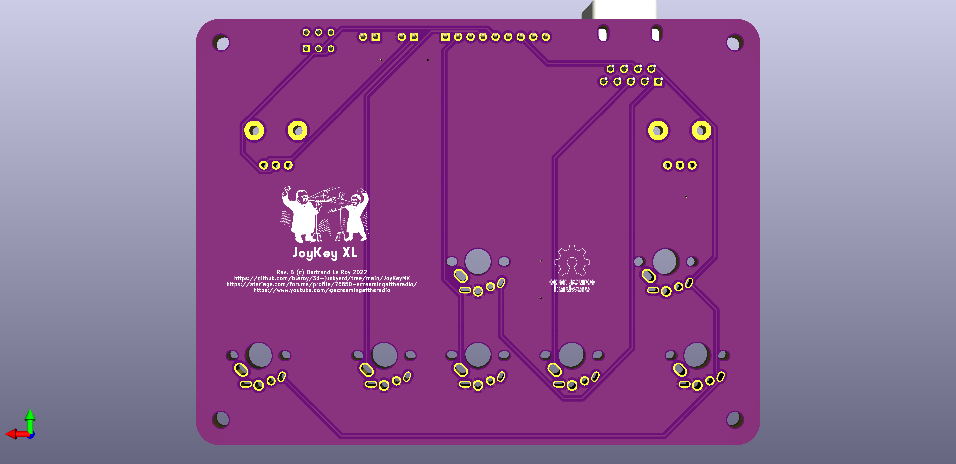
JoyKeyMX/JoyKeyXL_Back.png
