bleroy/3d-junkyard/JoyKeyMX/JoyKeyXL_Front.png

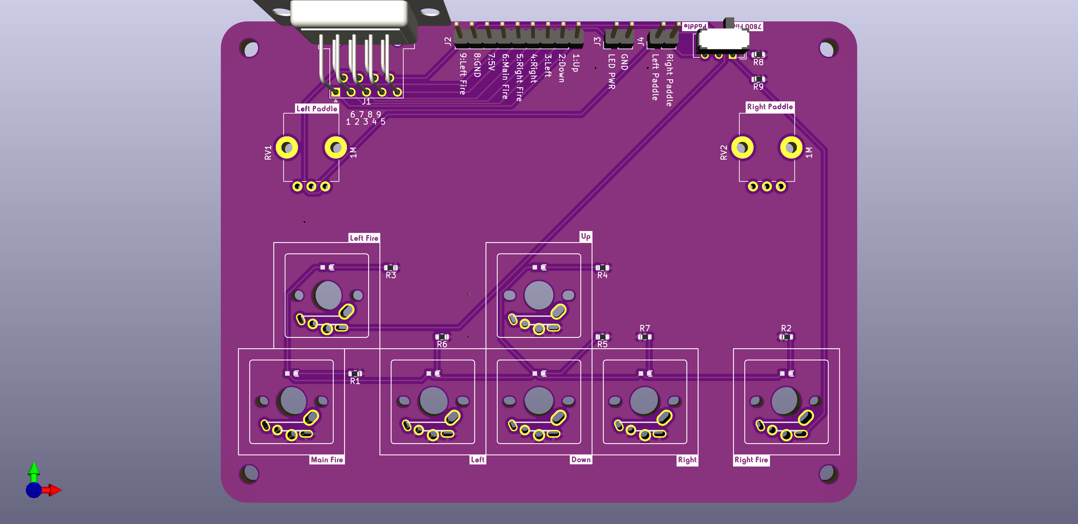
JoyKeyMX/JoyKeyXL_Front.png
