bleroy/3d-junkyard/Macropad/Models/kailh-choc-low-profile-switch-1.snapshot.3/Kailh LP Choc Tactile Switch bottom.jpg

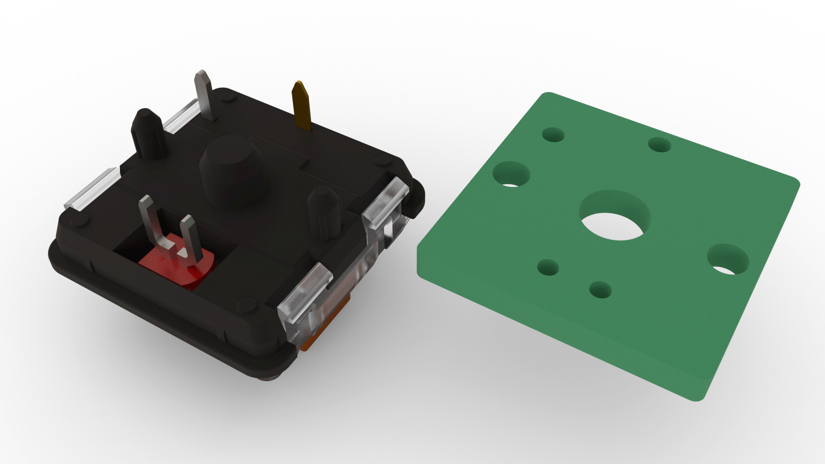
Macropad/Models/kailh-choc-low-profile-switch-1.snapshot.3/Kailh LP Choc Tactile Switch bottom.jpg
