bleroy/3d-junkyard/Macropad/Models/kailh-choc-low-profile-switch-1.snapshot.3/Kailh LP Choc Tactile Switch.jpg

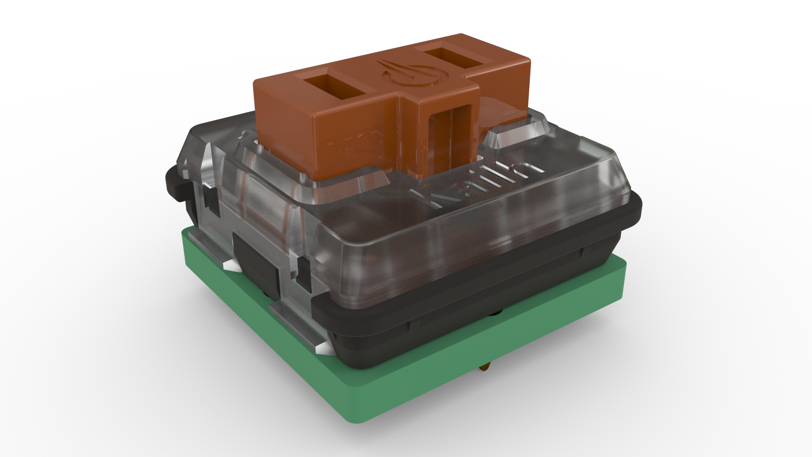
Macropad/Models/kailh-choc-low-profile-switch-1.snapshot.3/Kailh LP Choc Tactile Switch.jpg
