bleroy/3d-junkyard/Macropad/Models/kailh-lp-choc-pc-keycap-1.snapshot.3/Kailh LP Choc PC Keycap bottom.jpg

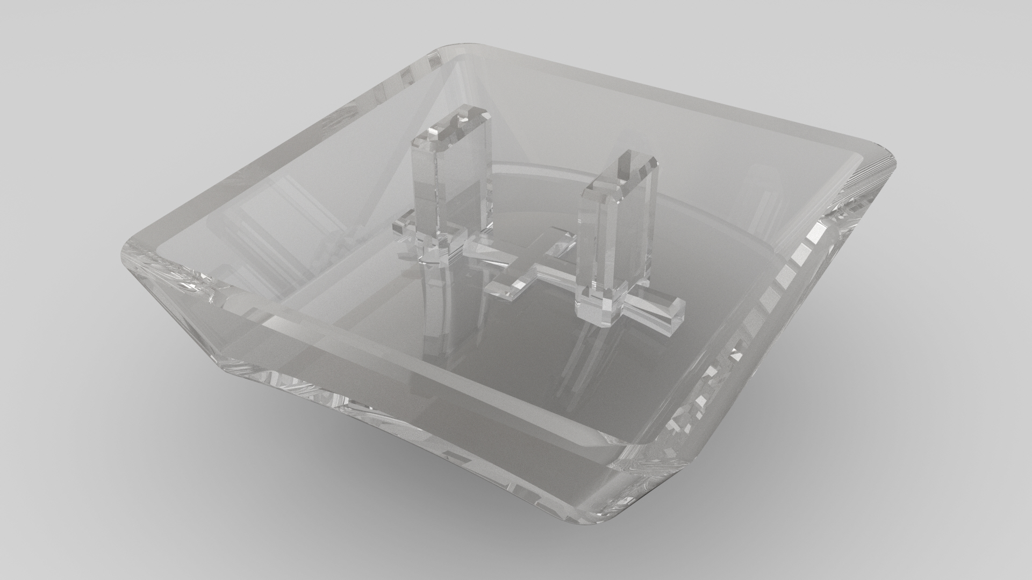
Macropad/Models/kailh-lp-choc-pc-keycap-1.snapshot.3/Kailh LP Choc PC Keycap bottom.jpg
