bleroy/3d-junkyard/misc-models/Atari/PBI-breakout/media/PBI-breakout.png

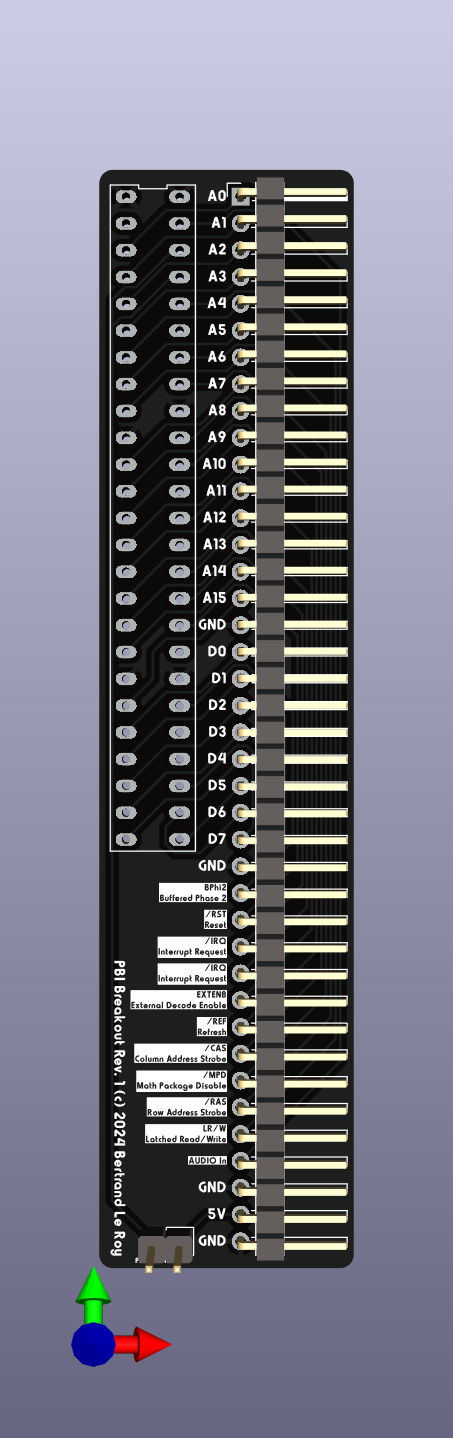
misc-models/Atari/PBI-breakout/media/PBI-breakout.png
