bleroy/3d-junkyard/misc-models/HexLattice/Media/HexLedLattice.png

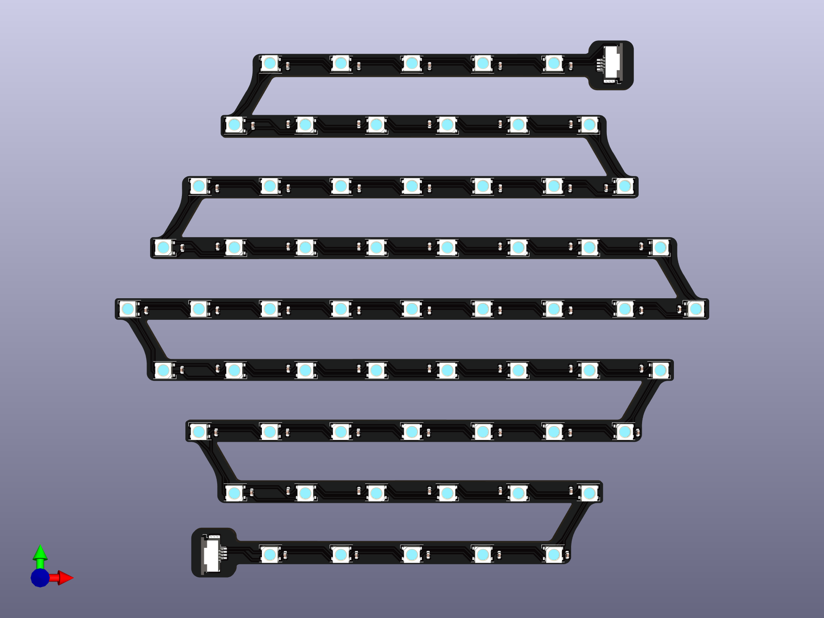
misc-models/HexLattice/Media/HexLedLattice.png
