bleroy/3d-junkyard/misc-models/NanoPC/screen/lumie0.png

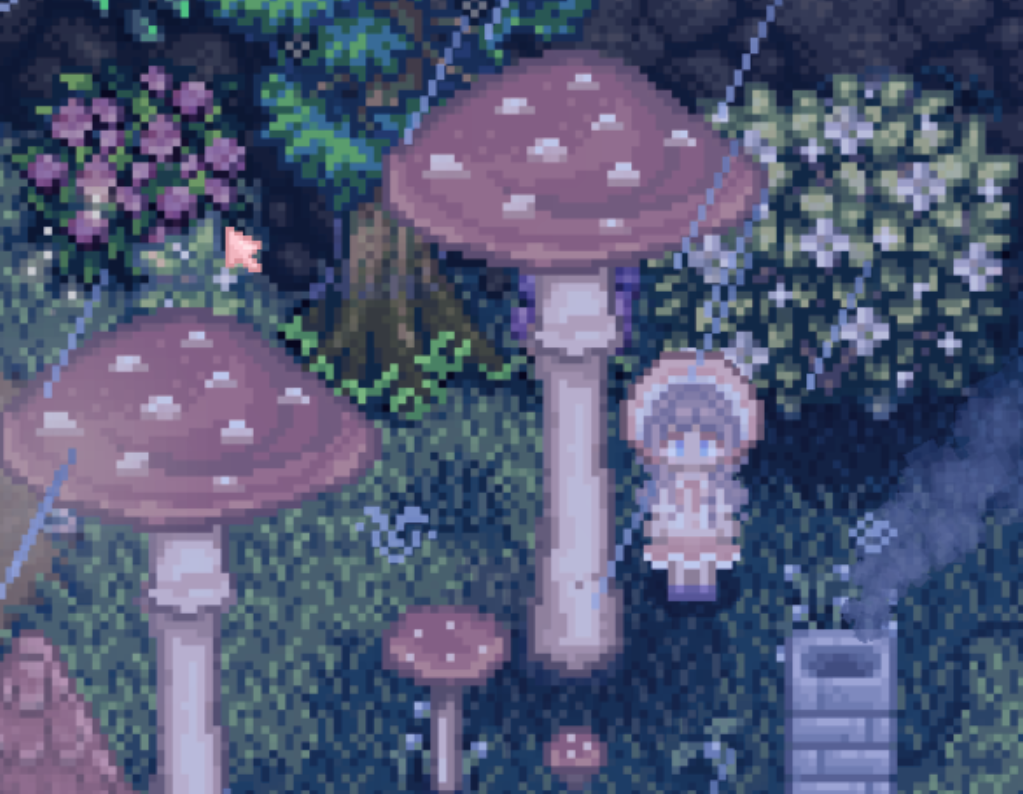
misc-models/NanoPC/screen/lumie0.png
