bleroy/3d-junkyard/misc-models/NanoPC/screen/lumie1.png

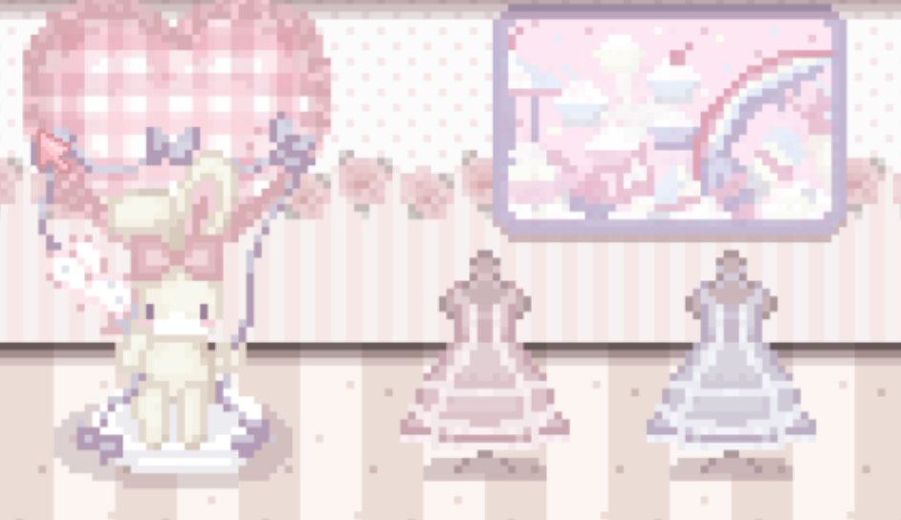
misc-models/NanoPC/screen/lumie1.png
