bleroy/3d-junkyard/misc-models/NanoPC/screen/lumie2.png

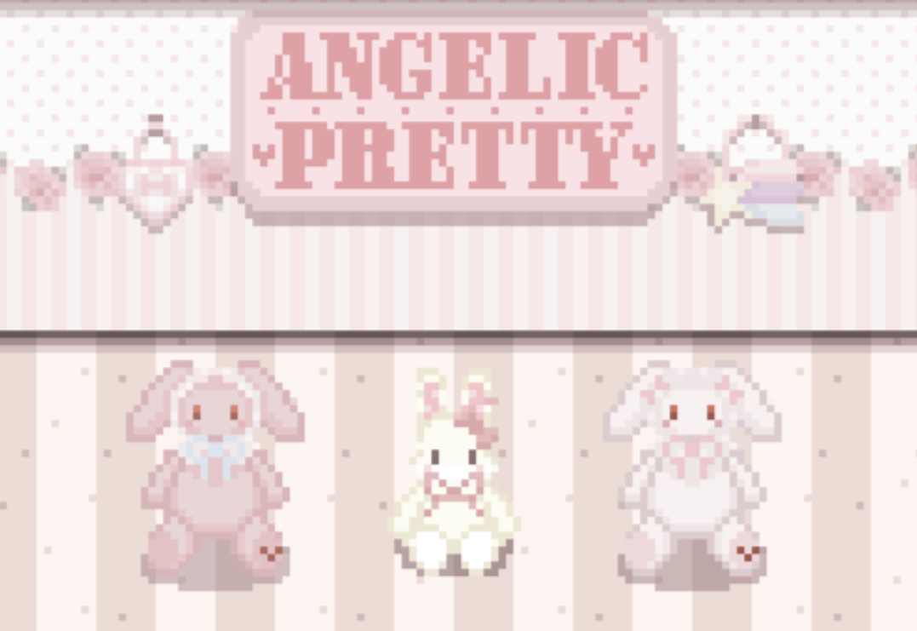
misc-models/NanoPC/screen/lumie2.png
