bleroy/3d-junkyard/misc-models/NanoPC/screen/lumie3.png

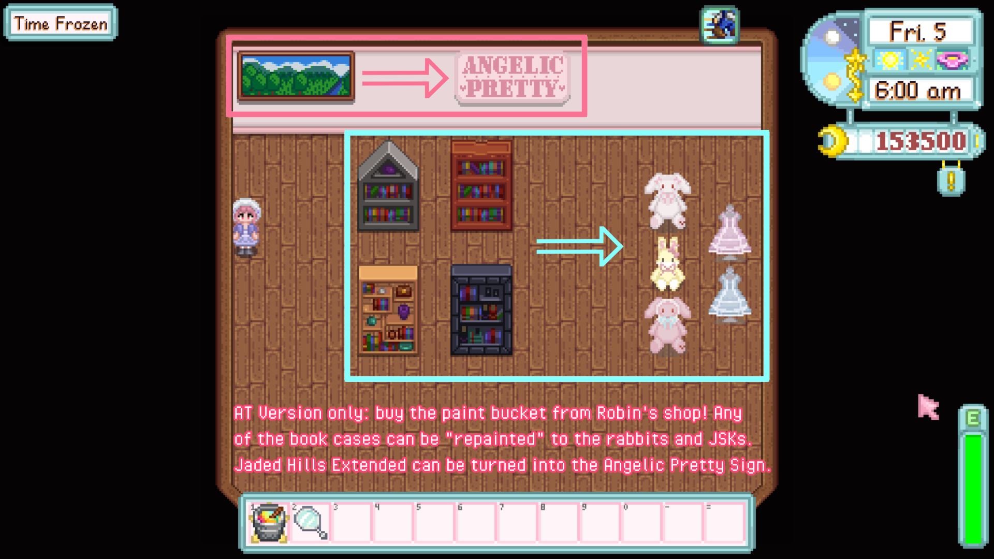
misc-models/NanoPC/screen/lumie3.png
