bleroy/3d-junkyard/misc-models/NanoPC/screen/lumie4.png

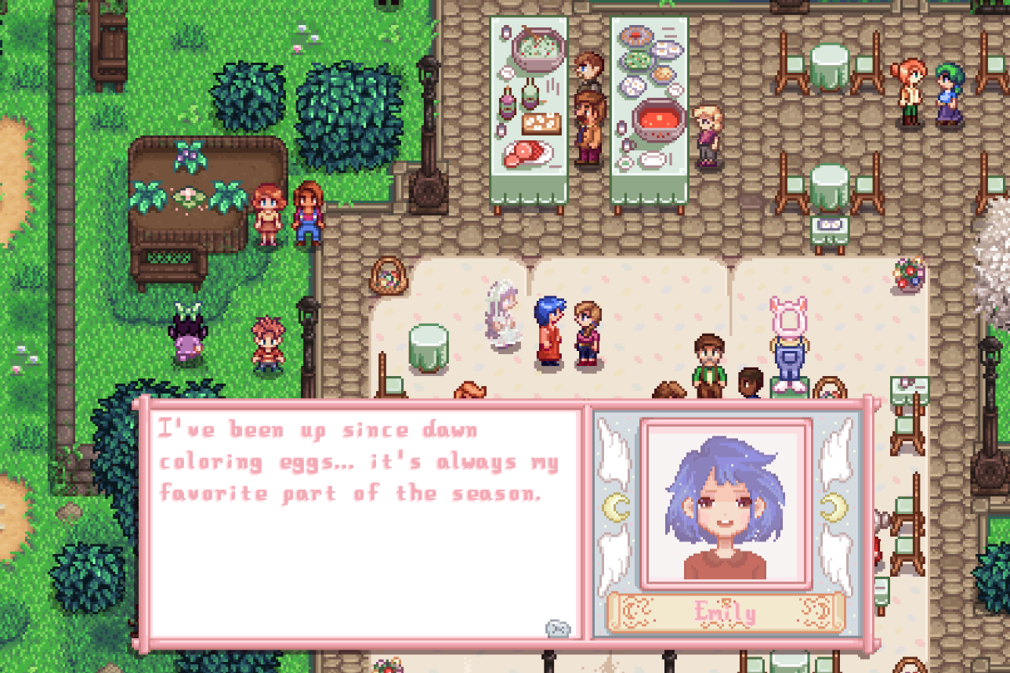
misc-models/NanoPC/screen/lumie4.png
