bleroy/3d-junkyard/misc-models/Workbench/WorkbenchRender.png

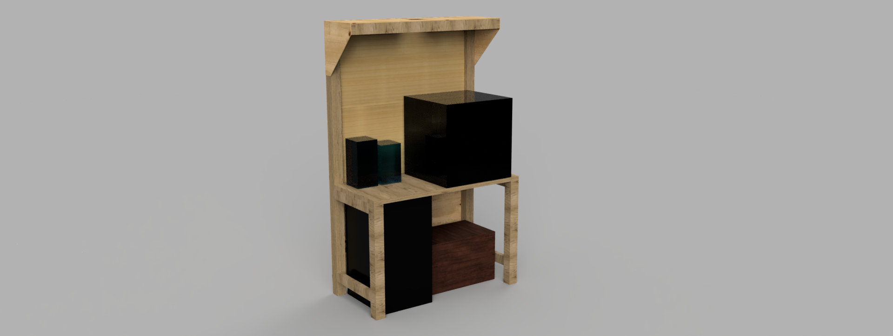
misc-models/Workbench/WorkbenchRender.png
