bleroy/3d-junkyard/misc-models/Workbench/WorkbenchViewBackRemoved.png

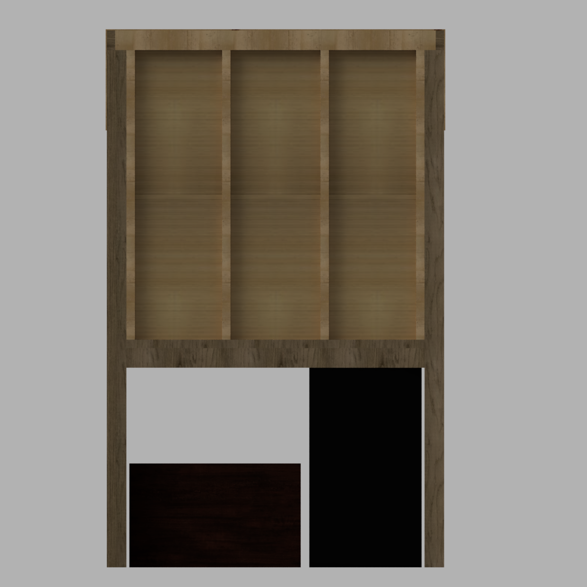
misc-models/Workbench/WorkbenchViewBackRemoved.png
