bleroy/3d-junkyard/misc-models/Workbench/WorkbenchViewCanopyUnderside.png

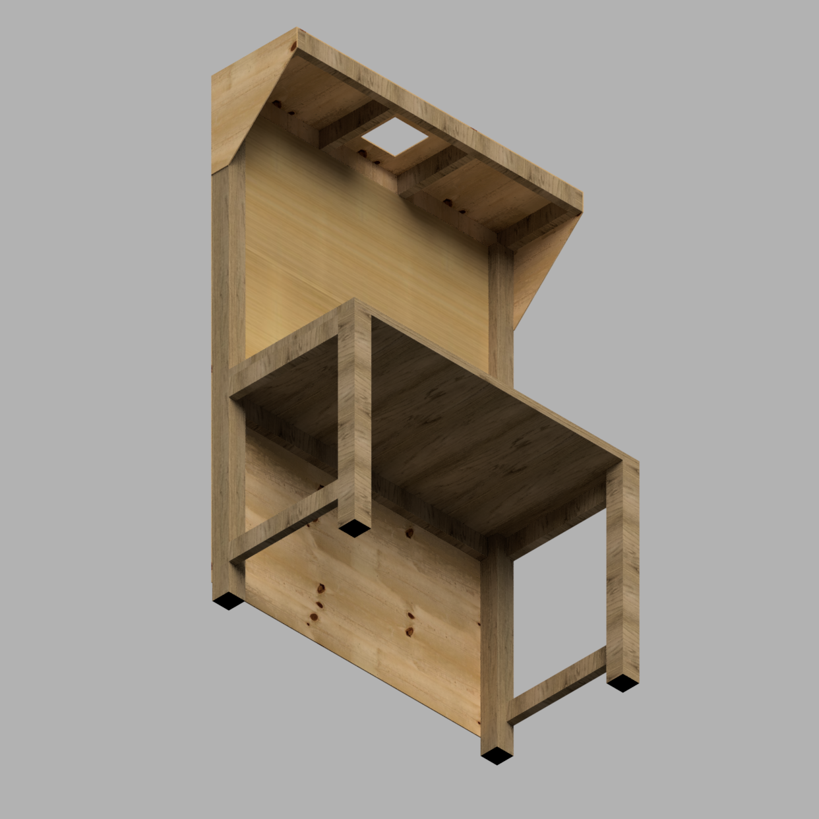
misc-models/Workbench/WorkbenchViewCanopyUnderside.png
