bleroy/3d-junkyard/SidecarXE85/Media/FreeCadModel.png

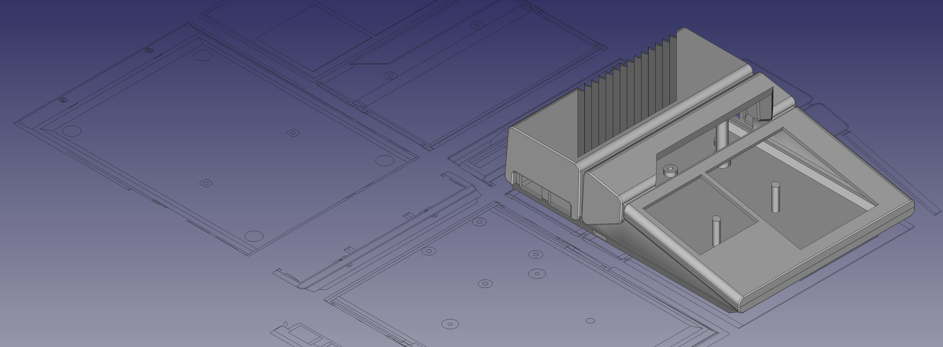
SidecarXE85/Media/FreeCadModel.png
