bleroy/3d-junkyard/SidecarXE85/Media/SidecarXE85-keyboard.png

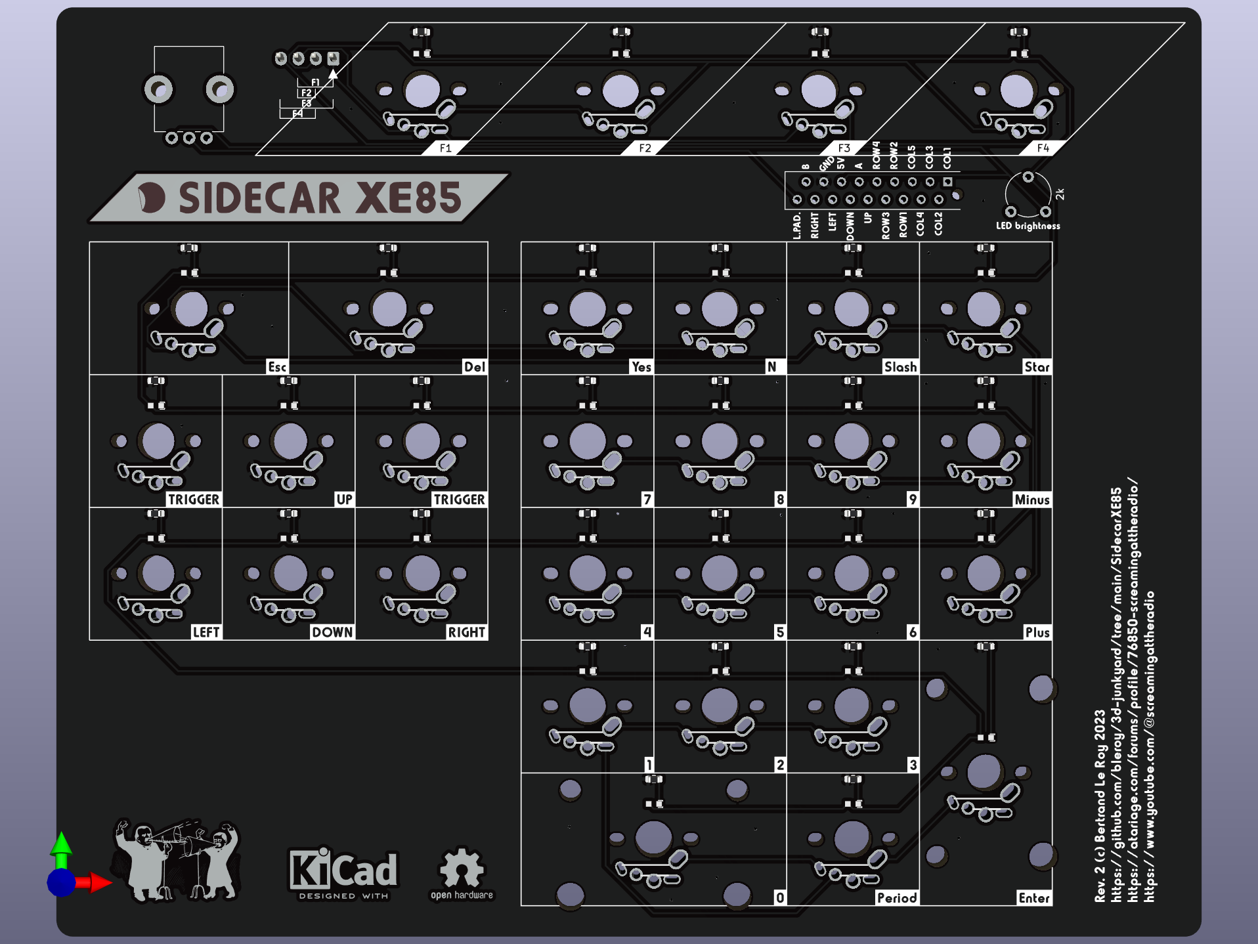
SidecarXE85/Media/SidecarXE85-keyboard.png
