bleroy/3d-junkyard/SidecarXE85/Media/SidecarXE85-plate.png

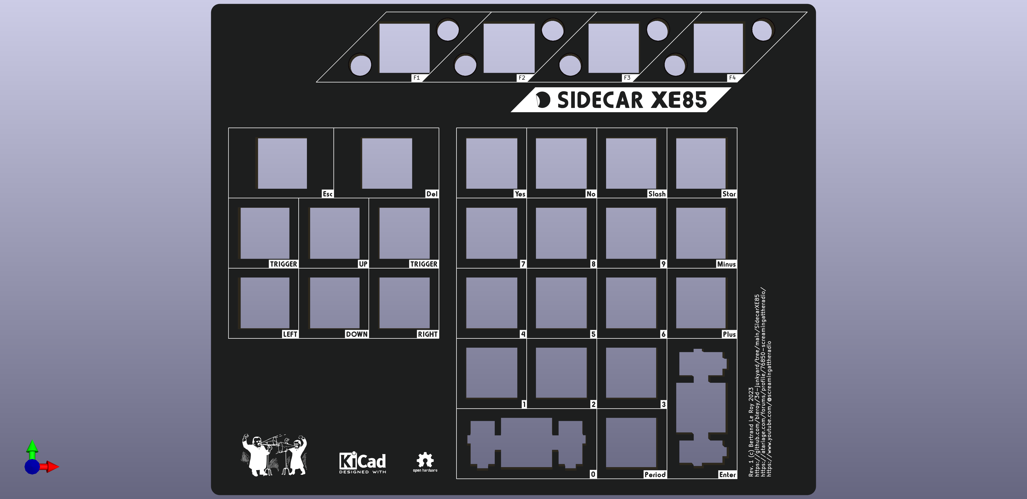
SidecarXE85/Media/SidecarXE85-plate.png
