bleroy/3d-junkyard/SidecarXE85/Media/SidecarXE85.png

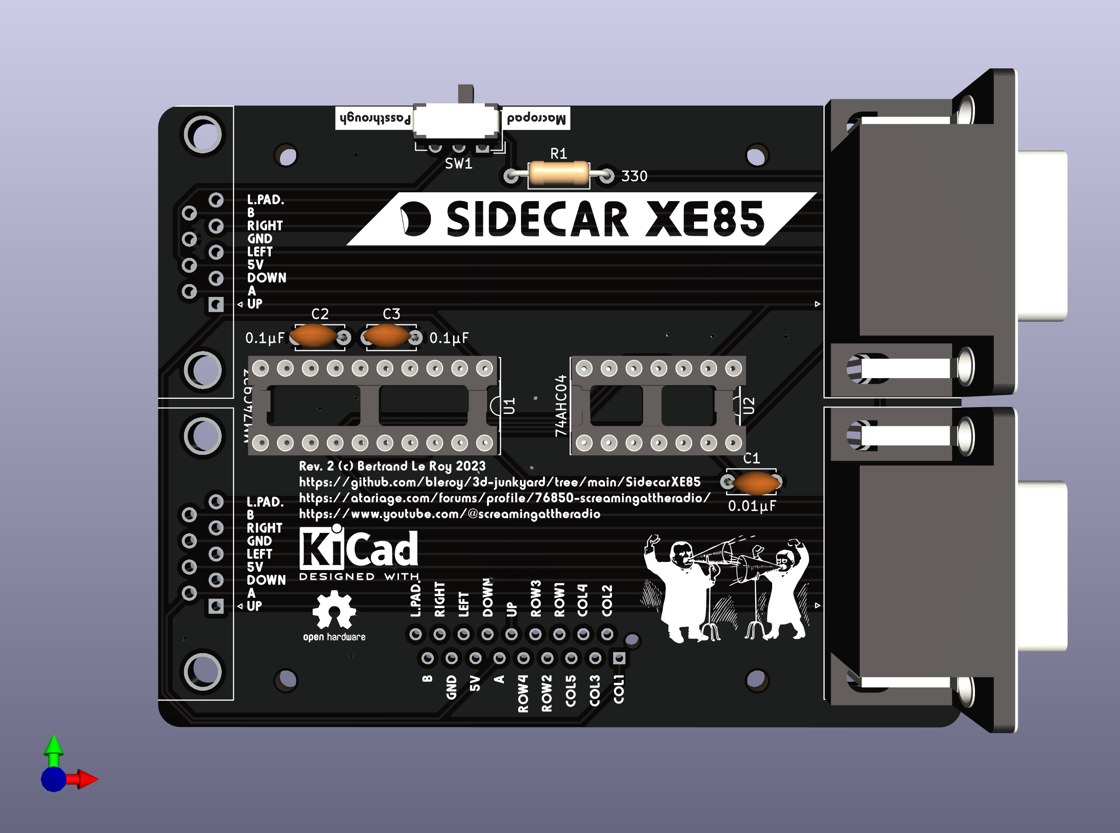
SidecarXE85/Media/SidecarXE85.png
