bleroy/3d-junkyard/Decent60/NavNumPad-plate/production/bom.csv

Designator | Footprint | Quantity | Value | LCSC Part #
SW10, SW11, SW12, SW13, SW14, SW15, SW16, SW18, SW2, SW20, SW22, SW23, SW24, SW25, SW26, SW27, SW3, SW30, SW31, SW32, SW33, SW34, SW4, SW5, SW6, SW7, SW9 | MX-1-00U-Hole | 27 | MX | C41430893
SW17, SW8 | MX-2-00U-Hole | 2 | 2UvMX | C41430893
SW19 | MX-2-00U-Hole | 1 | 2UMX | C41430893
