bleroy/3d-junkyard/Decent60/NavNumPad/production/bom.csv

Designator | Footprint | Quantity | Value | LCSC Part #
C1, C10, C11, C12, C13, C14, C15, C16, C17, C18, C19, C2, C23, C25, C26, C28, C3, C30, C31, C32, C33, C34, C35, C36, C37, C38, C4, C41, C45, C46, C47, C48, C49, C5, C50, C53, C54, C55, C56, C57, C6, C7, C8, C9 | 0402 | 44 | 100nF | C1525
C20, C24, C40, C43 | 0402 | 4 | 10uF | C15525
C21, C22 | 0402 | 2 | 15pF | C1548
C27, C29, C39 | 0402 | 3 | 1uF | C52923
C42 | CP_Elec_6.3x5.4 | 1 | 220uF | C3345
D1, D11, D13, D15, D17, D19, D21, D23, D25, D27, D29, D3, D31, D33, D35, D37, D42, D44, D46, D48, D5, D50, D52, D54, D56, D58, D60, D62, D64, D66, D68, D7, D9 | D_SOD-123 | 33 | 1N4148W | C81598
D10, D12, D14, D16, D18, D2, D20, D22, D24, D26, D28, D30, D32, D34, D36, D38, D39, D4, D40, D41, D45, D47, D49, D51, D53, D55, D6, D61, D63, D65, D67, D69, D8 | LED_SK6812MINI-E_3.2x2.8mm_P1.5mm_ReverseMount | 33 | SK6812MINI | C5378731
F1 | 1206 | 1 | 100mA | C269108
J6 | USB_C_Receptacle_HCTL_HC-TYPE-C-16P-01A | 1 | USB_C_Receptacle_USB2.0_16P | C709357
R2, R5 | 0402 | 2 | 1k | C11702
R3, R4 | 0402 | 2 | 27R | C25100
R6, R7 | 0402 | 2 | 5k1 | C25905
SW1 | SW-SMD_L3.9-W3.0-P4.45 | 1 | BOOTSEL | C720477
SW10, SW11, SW12, SW13, SW14, SW15, SW16, SW18, SW2, SW20, SW22, SW23, SW24, SW25, SW26, SW27, SW3, SW30, SW31, SW32, SW33, SW34, SW4, SW5, SW6, SW7, SW9 | Kailh_socket_MX_1-00U | 27 | MX | C41430893
SW17, SW8 | Kailh_socket_MX_2-00U_V | 2 | 2UvMX | C41430893
SW19 | Kailh_socket_MX_2-00U | 1 | 2UMX | C41430893
SW35 | SW-SMD_L3.9-W3.0-P4.45 | 1 | RESET | C720477
U1 | SOIC-8_5.3x5.3mm_P1.27mm | 1 | W25Q128JVS | C97521
U2 | SOT-223-3_TabPin2 | 1 | NCP1117-3.3_SOT223 | C146799
U3 | QFN-56-1EP_7x7mm_P0.4mm_EP3.2x3.2mm | 1 | RP2040 | C2040
U4 | QSOP-16_3.9x4.9mm_P0.635mm | 1 | CH334R | C4154405
U5 | TSOT-23 | 1 | CH213 | C5456874
Y1 | Oscillator_SMD_Abracon_ASE-4Pin_3.2x2.5mm | 1 | ABM8-272-T3 | C20625731
