bleroy/3d-junkyard/Decent800/Keyboard/production/Decent800_Rev_3M-bom.csv

Designator | Footprint | Quantity | Value | LCSC Part #
D1, D10, D12, D13, D14, D15, D16, D17, D18, D19, D2, D20, D21, D22, D24, D25, D26, D27, D28, D29, D3, D30, D31, D32, D33, D34, D35, D36, D37, D38, D39, D41, D42, D43, D44, D45, D46, D47, D48, D49, D5, D50, D51, D52, D53, D54, D55, D56, D57, D58, D59, D6, D60, D62, D7, D8 | D_SOD-123 | 56 | 1N4148W | C81598
R10, R11, R12, R14, R15, R16, R17, R18, R19, R2, R20, R21, R22, R23, R24, R25, R26, R27, R28, R29, R3, R30, R31, R32, R33, R34, R35, R36, R37, R38, R39, R4, R40, R42, R43, R44, R45, R46, R47, R48, R49, R5, R50, R51, R52, R53, R54, R55, R57, R6, R60, R61, R62, R64, R7, R8, R9 | 0603 | 57 | 100 | C22775
RV1 | Potentiometer_Bourns_TC33X_Vertical | 1 | R_Potentiometer | C719174
SW0, SW1, SW2, SW3, SW4, SW5, SW6, SW7, SW8, SW9, SWA1, SWB1, SWC1, SWCOMMA1, SWCPS1, SWD1, SWDASH1, SWE1, SWEQUAL1, SWESC1, SWF1, SWG1, SWGT1, SWH1, SWI1, SWJ1, SWK1, SWL1, SWLT1, SWM1, SWN1, SWO1, SWP1, SWPERIOD1, SWPLUS1, SWQ1, SWR1, SWS1, SWSEMI1, SWSTAR1, SWT1, SWU1, SWV1, SWW1, SWX1, SWY1, SWZ1 | 1U-LED | 47 | blue | C19171394
SWATARI2, SWBRK2, SWSLASH1 | 1-25U-LED | 3 | blue | C19171394
SWCTL1, SWRET1, SWTAB1 | 1-50U-LED | 3 | blue | C19171394
SWDEL2, SWLEFTSFT1 | 2-00U-LED | 2 | blue | C19171394
SWRIGHTSFT1 | 2-25U-LED | 1 | blue | C19171394
SWSPC1 | 6-25U-LED | 1 | blue | C19171394
