bleroy/3d-junkyard/Atari130MX/Atari130MX-adapter/production/bom.csv

Designator | Footprint | Quantity | Value | LCSC Part #
J1 | FPC 1x24 P2.54mm Edge | 1 | Conn_01x24
J2 | FPC Molex 1x26 P1mm Edge | 1 | Conn_01x26
