bleroy/3d-junkyard/misc-models/KeyboardTester/v1/AtariKeyboardTester_BOM.ods

Component | Quantity | Digikey | Notes
300Ω Resistors | 38 | https://www.digikey.com/en/products/detail/nte-electronics-inc/QW130/11653195
LED Col | 24 | https://www.digikey.com/en/products/detail/nte-electronics-inc/NTE30142/13968306
LED Row | 24 | https://www.digikey.com/en/products/detail/nte-electronics-inc/NTE30141/13968204
LED Key | 66 | https://www.digikey.com/en/products/detail/nte-electronics-inc/NTE30143/13968277
LED Power | 1 | https://www.digikey.com/en/products/detail/nte-electronics-inc/NTE3140/11653644
PNP Transistors | 14 | https://www.digikey.com/en/products/detail/nte-electronics-inc/2N3906/11653409
NPN Transistors | 9 | https://www.digikey.com/en/products/detail/onsemi/2N4401TFR/458820
Header 24 pin 2.54mm pitch | 1 | https://www.digikey.com/en/products/detail/sullins-connector-solutions/PRPC024SAAN-RC/2775230
Header 3x8 pin 2.54mm pitch | 3 | https://www.digikey.com/en/products/detail/samtec-inc/TSW-108-07-T-T/7868980
Jumper 2x8 2.54mm pitch | 3 | https://www.digikey.com/en/products/detail/würth-elektronik/60910813421/9920889
FFC 2x12 Connector | 1 | https://www.digikey.com/en/products/detail/adam-tech/BHR-24-VUA/9832347
IDC 26 1mm pitch Connector | 1 | https://www.digikey.com/en/products/detail/molex/0522072633/4444523
Atari keyboard connector | 1 | https://www.digikey.com/en/products/detail/edac-inc/342-024-523-101/10856286 | Unverified compatibility of this modern connector, that is hard to source
Battery holder | 1 | https://www.digikey.com/en/products/detail/mpd-memory-protection-devices/BH9VPC/31510
Switch | 1 | https://www.digikey.com/en/products/detail/e-switch/EG1224/502052
