bleroy/3d-junkyard/DecentCart/Enclosure/DecentCart2350-Front.stl

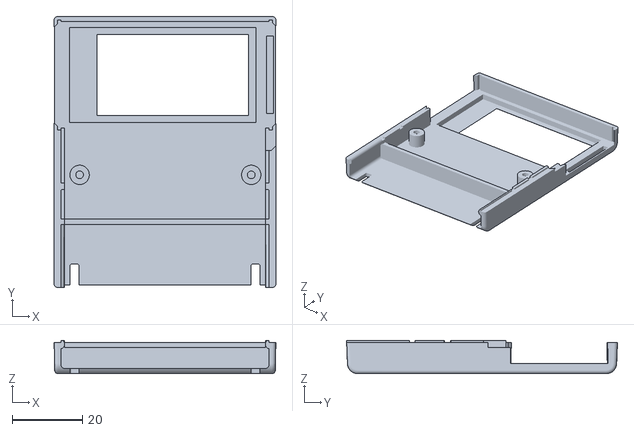
[picture p225: CAD file, 2025-10-22]
DecentCart/Enclosure/DecentCart2350-Front.stl
63.0 x 77.0 x 9.50
