bleroy/3d-junkyard/DecentCart/VertiCart/Enclosure/VertiCart Base Support.FCStd

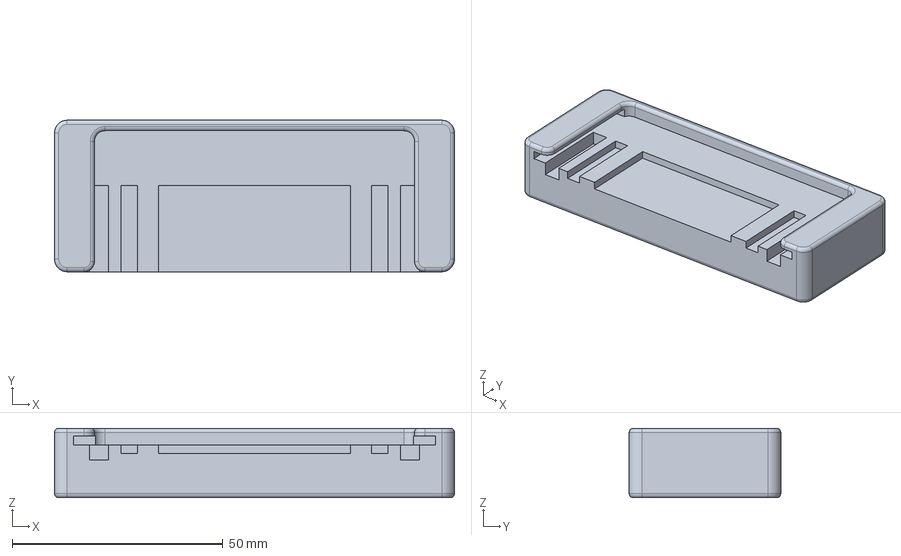
[picture p226: CAD file, 2024-11-11]
DecentCart/VertiCart/Enclosure/VertiCart Base Support.FCStd
95.0 x 36.0 x 16.5 mm
