bleroy/3d-junkyard/DecentCaseXE/DecentCaseXE.FCStd

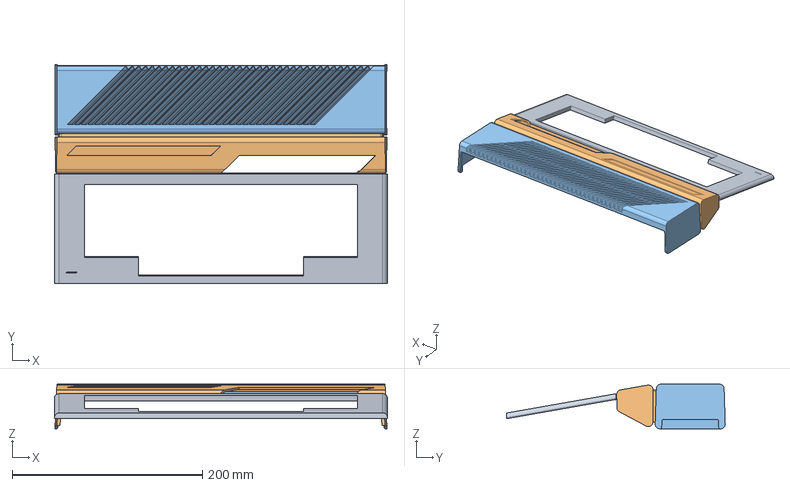
[picture p227: CAD file, 2026-08-26]
DecentCaseXE/DecentCaseXE.FCStd
350.0 x 229.7 x 47.0 mm
Top keyboard
Top middle
Top back
