bleroy/3d-junkyard/DecenTKL/Caps/ConsoleXE-F11-F12.FCStd

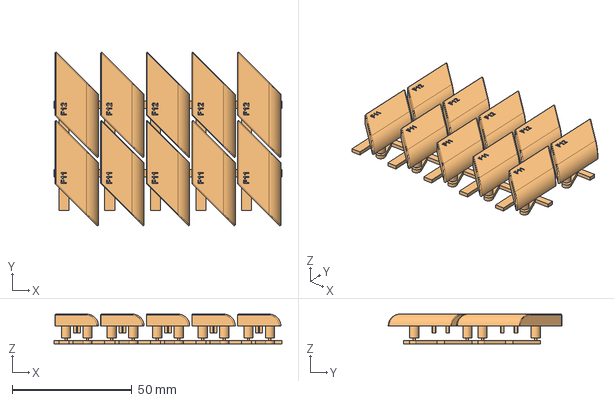
[picture p228: CAD file, 2024-10-14]
DecenTKL/Caps/ConsoleXE-F11-F12.FCStd
95.3 x 72.5 x 12.5 mm
ConsoleKeyBody
