bleroy/3d-junkyard/DecenTKL/Enclosure/DecenTKL-bottom.stl

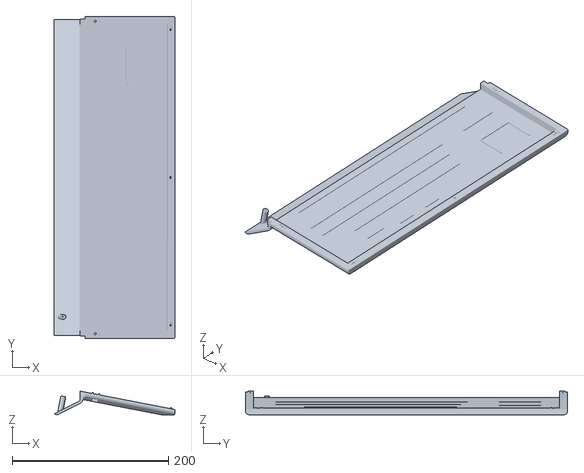
[picture p229: CAD file, 2024-11-14]
DecenTKL/Enclosure/DecenTKL-bottom.stl
154.3 x 412.2 x 30.4
