bleroy/3d-junkyard/DecenTKL/Keyboard/DecenTKL.step

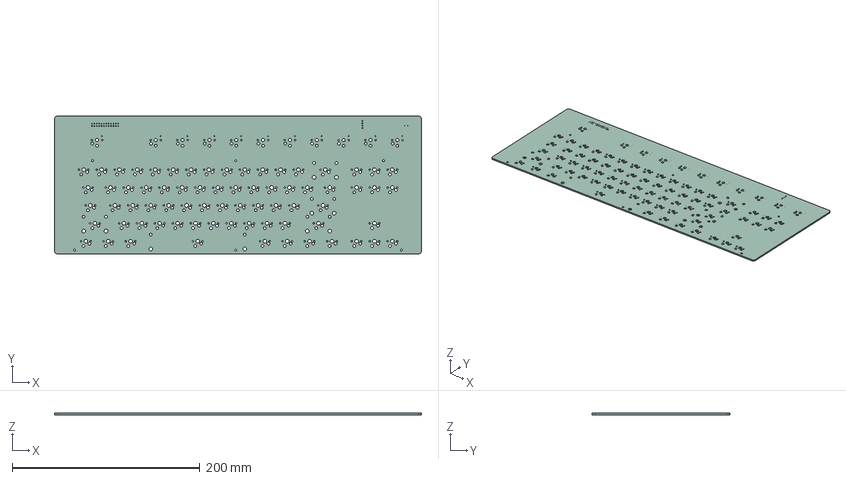
[picture p230: CAD file, 2024-07-21]
DecenTKL/Keyboard/DecenTKL.step
390.6 x 146.7 x 1.60 mm
