bleroy/3d-junkyard/DecenTKL/KeyboardPlate/DecenTKL-plate.step

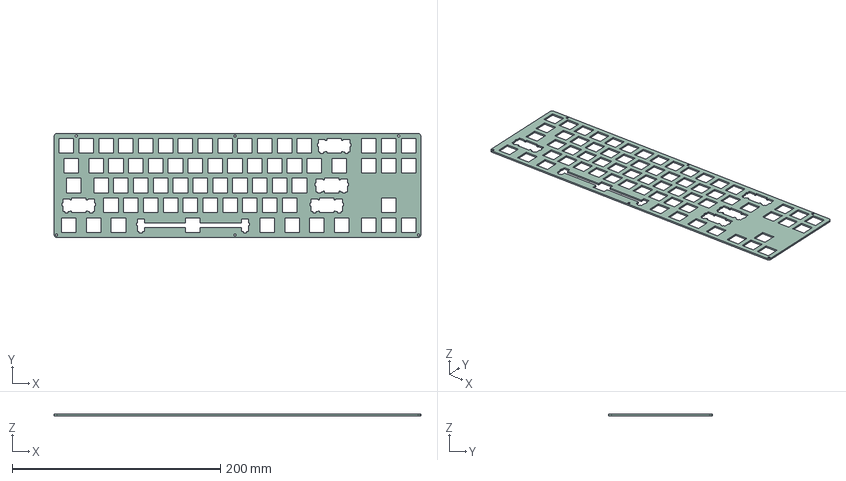
[picture p231: CAD file, 2024-07-21]
DecenTKL/KeyboardPlate/DecenTKL-plate.step
352.4 x 100.0 x 1.60 mm
