bleroy/3d-junkyard/DecenTKL/Misc/EncoderKnob.FCStd

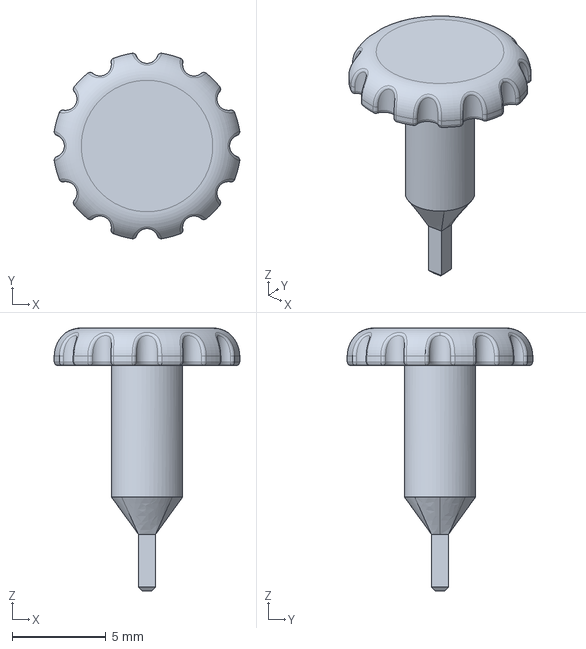
[picture p232: CAD file, 2024-11-30]
DecenTKL/Misc/EncoderKnob.FCStd
9.88 x 9.88 x 14.0 mm
