bleroy/3d-junkyard/DecenTKL/NumPad/DecentNumPad.step

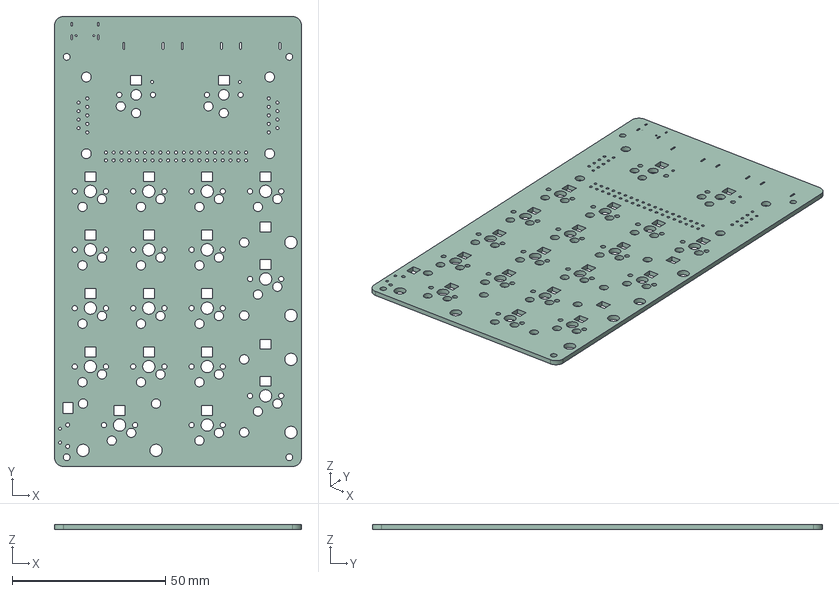
[picture p233: CAD file, 2024-08-25]
DecenTKL/NumPad/DecentNumPad.step
80.6 x 146.7 x 1.60 mm
