bleroy/3d-junkyard/DecenTKL/NumPadEnclosure/DecenTKL-Numpad-Enclosure-Top.stl

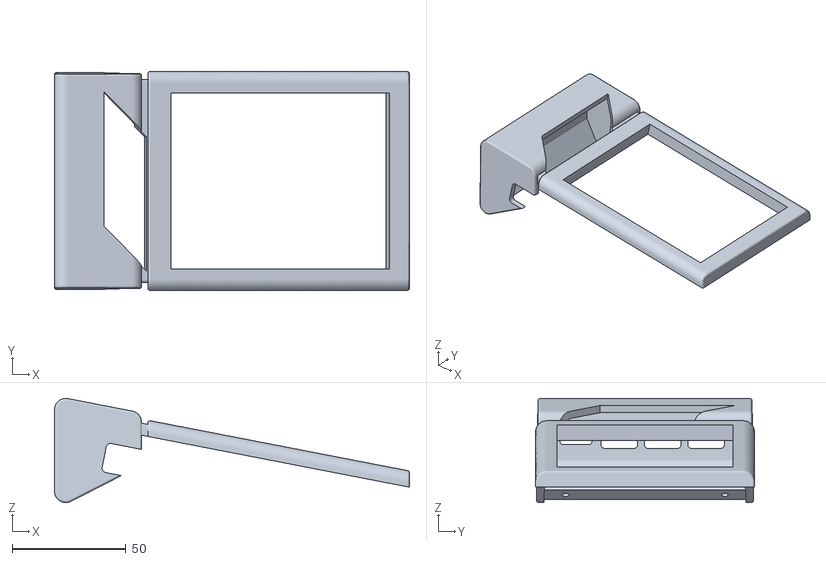
[picture p234: CAD file, 2024-10-14]
DecenTKL/NumPadEnclosure/DecenTKL-Numpad-Enclosure-Top.stl
156.0 x 96.2 x 45.8
