bleroy/3d-junkyard/DecenTKL/NumPadPlate/NumPadPlate.step

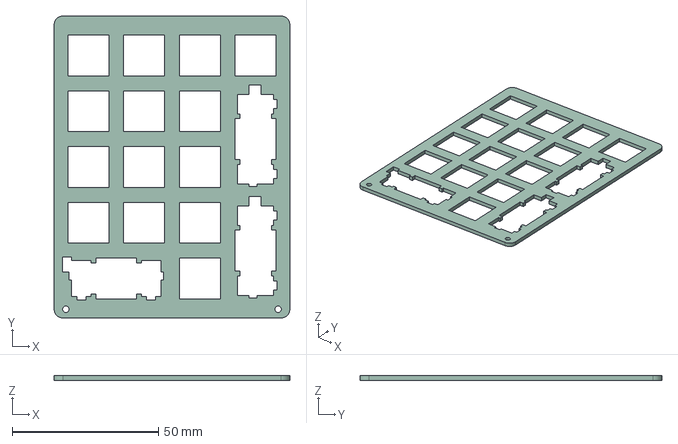
[picture p235: CAD file, 2024-08-25]
DecenTKL/NumPadPlate/NumPadPlate.step
80.6 x 103.2 x 1.60 mm
