bleroy/3d-junkyard/DecentUSB/DecentUSB2350/Models/RP2350_QFN80.step

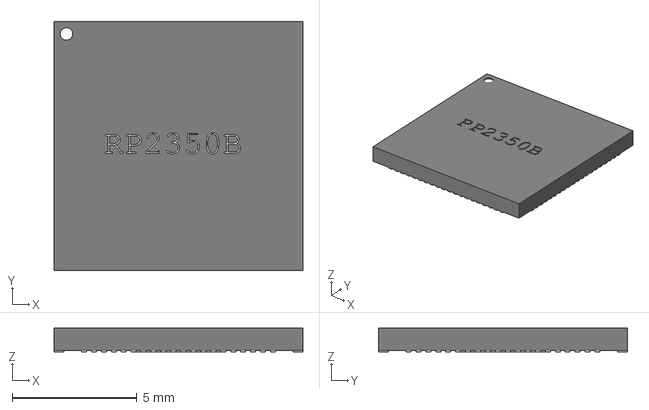
[picture p236: CAD file, 2024-10-14]
DecentUSB/DecentUSB2350/Models/RP2350_QFN80.step
10.0 x 10.0 x 0.95 mm
