bleroy/3d-junkyard/DecentXE/Caps/ConsoleXE-ChocV1-Single.3mf

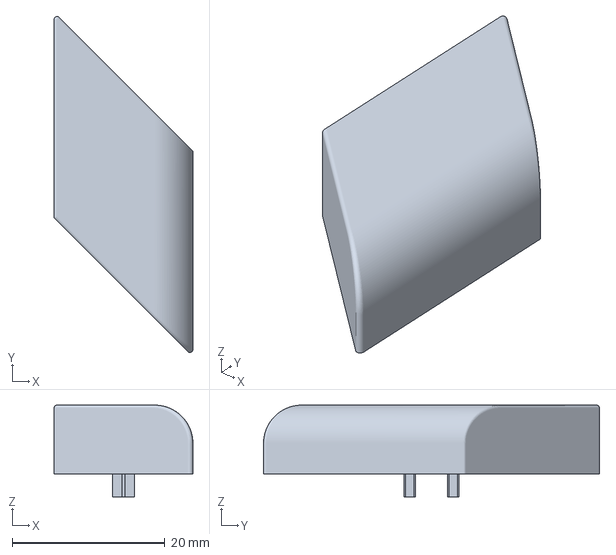
[picture p237: CAD file, 2026-08-26]
DecentXE/Caps/ConsoleXE-ChocV1-Single.3mf
18.2 x 43.9 x 12.0 mm
