bleroy/3d-junkyard/DecentXE/Enclosure/DecentXE-Enclosure.FCStd

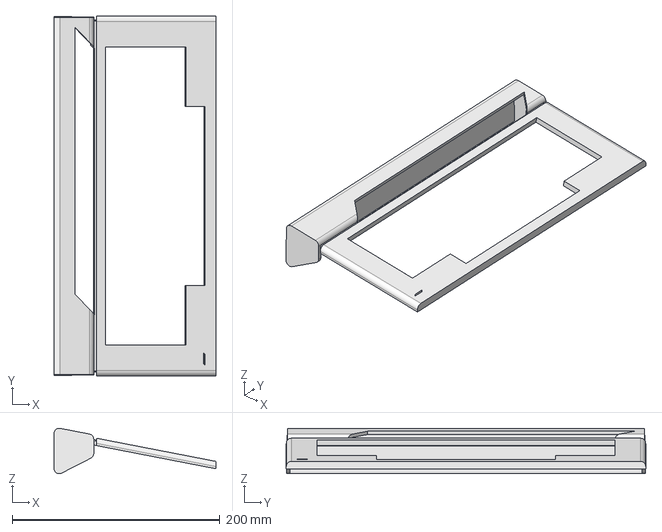
[picture p238: CAD file, 2024-07-21]
DecentXE/Enclosure/DecentXE-Enclosure.FCStd
156.0 x 346.2 x 43.8 mm
