bleroy/3d-junkyard/DecentXE/Keyboard/DecentXE.step

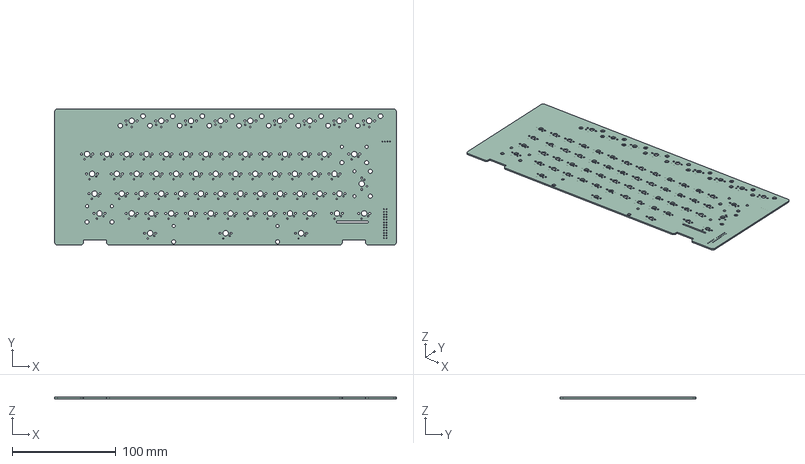
[picture p239: CAD file, 2026-08-26]
DecentXE/Keyboard/DecentXE.step
329.2 x 131.1 x 1.51 mm
