bleroy/3d-junkyard/DecentXE/Misc/XE-mid-keeb-support.FCStd

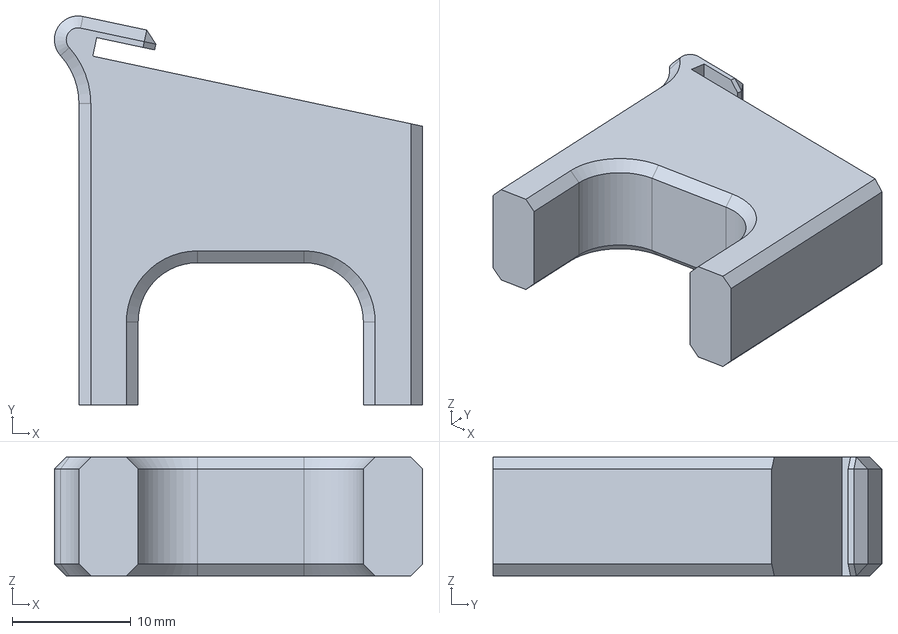
[picture p240: CAD file, 2026-02-09]
DecentXE/Misc/XE-mid-keeb-support.FCStd
31.1 x 32.8 x 10.0 mm
