bleroy/3d-junkyard/DecentXE/Plate/DecentXE-plate-modern-low-cost.FCStd

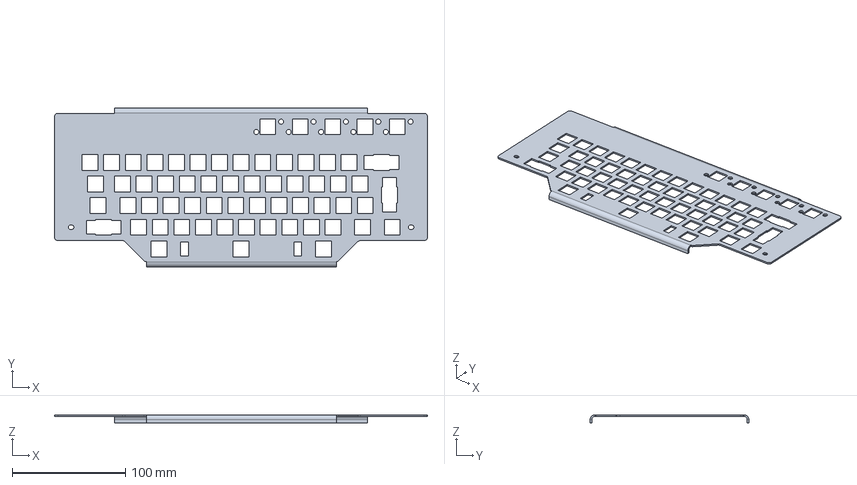
[picture p241: CAD file, 2026-09-28]
DecentXE/Plate/DecentXE-plate-modern-low-cost.FCStd
329.2 x 140.0 x 7.50 mm
