bleroy/3d-junkyard/DecentXE/Stabilizers/LowProRaiserPlate.3mf

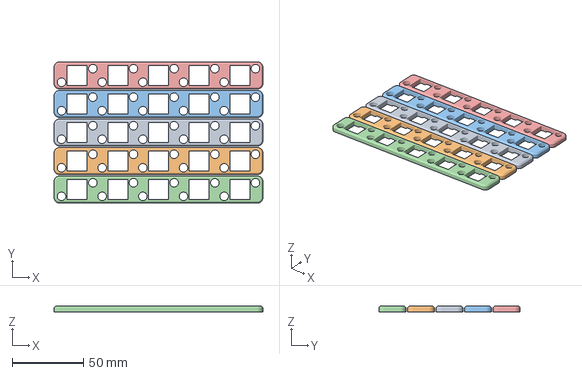
[picture p242: CAD file, 2024-08-18]
DecentXE/Stabilizers/LowProRaiserPlate.3mf
146.9 x 99.3 x 3.95 mm
LowProRaiserPlate.stl x 5
