bleroy/3d-junkyard/DecentXE/Stems/Decent Stem.FCStd

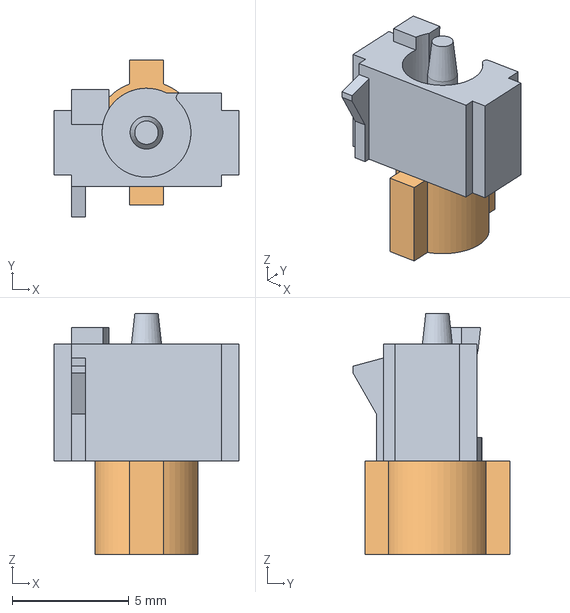
[picture p243: CAD file, 2026-04-19]
DecentXE/Stems/Decent Stem.FCStd
7.90 x 6.70 x 10.3 mm
Kailh Stem Base
XE Round
