bleroy/3d-junkyard/DecentXL/Adapters/StackpoleXLLeftShiftStabilizerAdapter.FCStd

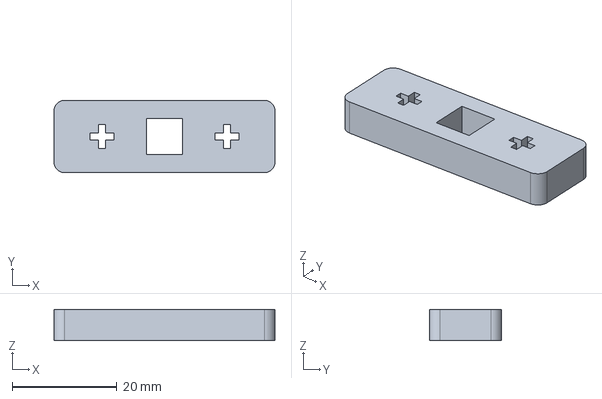
[picture p244: CAD file, 2024-11-30]
DecentXL/Adapters/StackpoleXLLeftShiftStabilizerAdapter.FCStd
42.2 x 13.8 x 6.00 mm
