bleroy/3d-junkyard/DecentXL/Brackets/DecentXL-Right-Bracket.FCStd

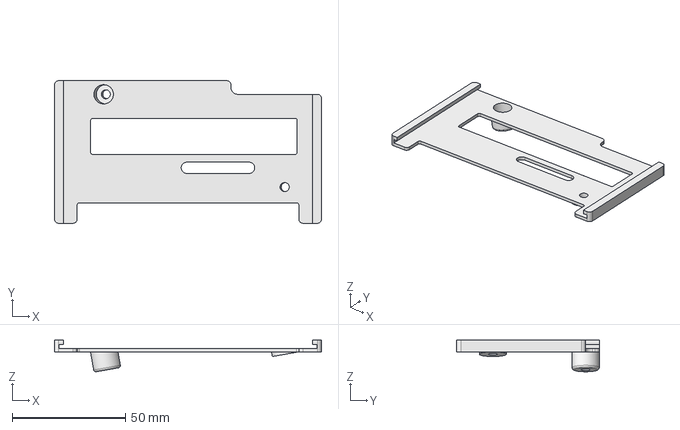
[picture p245: CAD file, 2024-04-10]
DecentXL/Brackets/DecentXL-Right-Bracket.FCStd
118.0 x 63.0 x 14.0 mm
