bleroy/3d-junkyard/DecentXL/Caps/Atari XL Console Key.FCStd

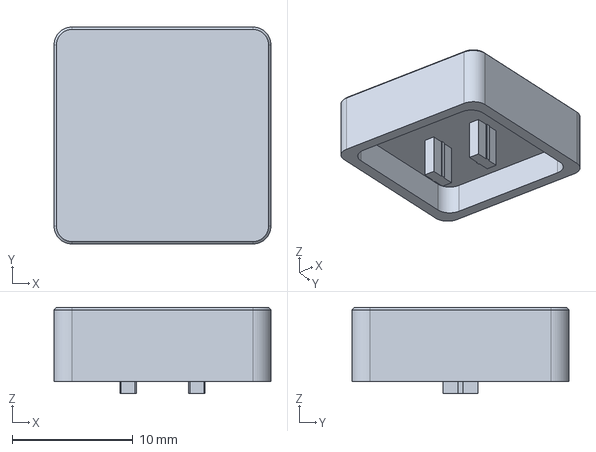
[picture p246: CAD file, 2026-09-07]
DecentXL/Caps/Atari XL Console Key.FCStd
18.0 x 18.0 x 7.15 mm
