bleroy/3d-junkyard/DecentXL/Misc/800XL LED diffuser.stl

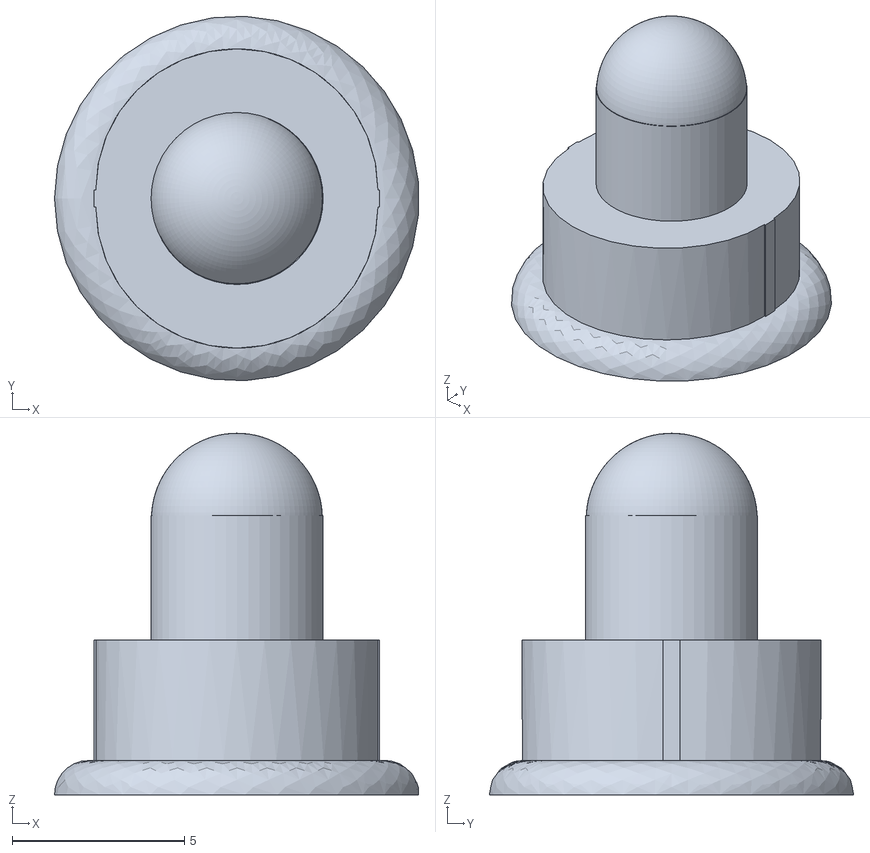
[picture p247: CAD file, 2026-07-02]
DecentXL/Misc/800XL LED diffuser.stl
10.6 x 10.6 x 10.5
