bleroy/3d-junkyard/JoyKeyMX/Case/JoyKeyCase-Bottom.stl

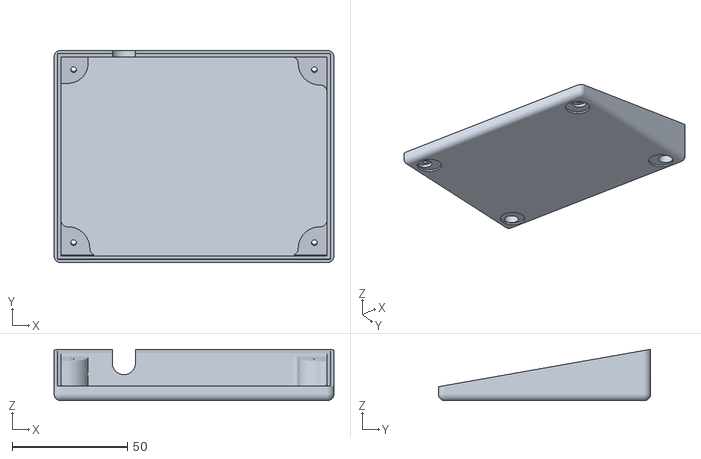
[picture p248: CAD file, 2023-04-02]
JoyKeyMX/Case/JoyKeyCase-Bottom.stl
121.3 x 92.0 x 22.3
