bleroy/3d-junkyard/JoyKeyMX/Models/SlidingSwitch.step

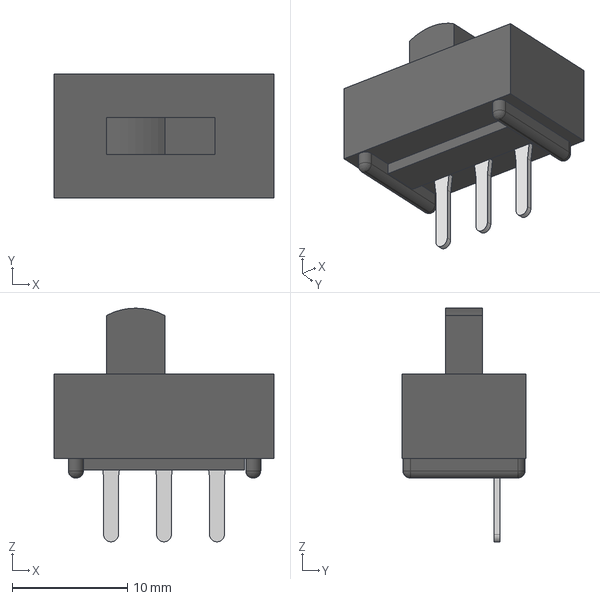
[picture p249: CAD file, 2023-04-02]
JoyKeyMX/Models/SlidingSwitch.step
19.1 x 10.8 x 20.3 mm
