bleroy/3d-junkyard/Macropad/KeyChain/Enclosure/KeyChainEnclosure-Bottom.3mf

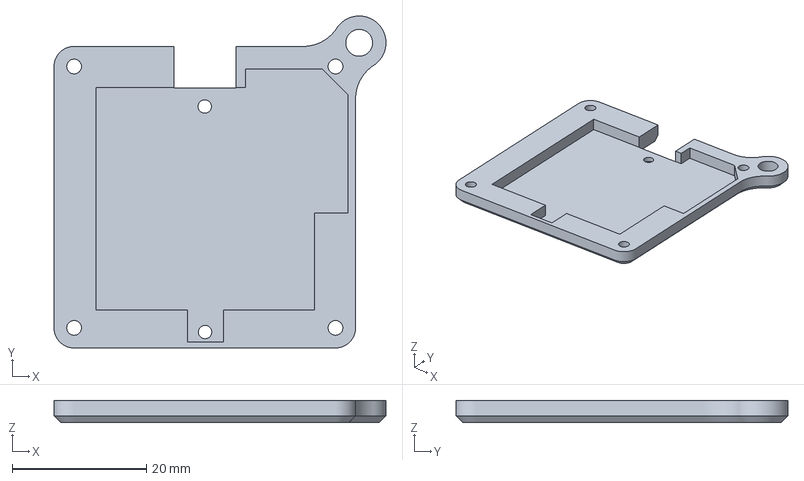
[picture p250: CAD file, 2026-08-10]
Macropad/KeyChain/Enclosure/KeyChainEnclosure-Bottom.3mf
49.5 x 49.5 x 3.30 mm
