bleroy/3d-junkyard/Macropad/KeyChain/KeyChain.step

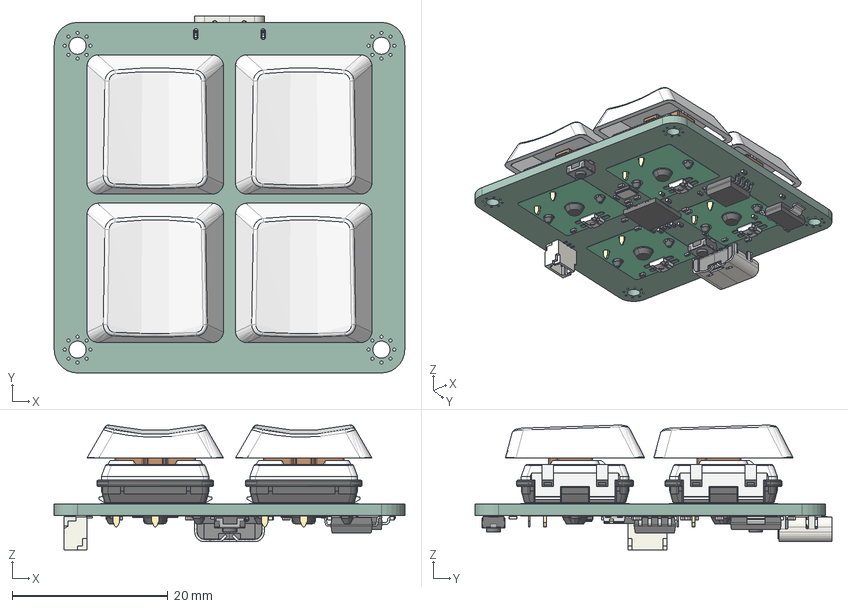
[picture p251: CAD file, 2026-08-10]
Macropad/KeyChain/KeyChain.step
45.0 x 45.8 x 16.0 mm
Document x 8
C_0402_1005Metric x 21
SOIC-8_5.3x5.3mm_P1.27mm
R_0402_1005Metric x 8
SW_SPST_TS-1088-xR020 x 2
QFN-56-1EP_7x7mm_P0.4mm_EP3.2x3.2mm
Pin1 x 4
Pin2 x 4
Pin3 x 4
Pin4 x 4
SOT-223
JST_SH_BM03B-SRSS-TB_1x03-1MP_P1.00mm_Vertical
Crystal_SMD_Abracon_ABM8G-4Pin_3.2x2.5mm
USB_C_Receptacle_GCT_USB4125-xx-x_6P_TopMnt_Horizontal
KeyChain_PCB
