bleroy/3d-junkyard/Macropad/Models/kailh-choc-low-profile-switch-1.snapshot.3/Kailh Choc Low Profile Switch.step

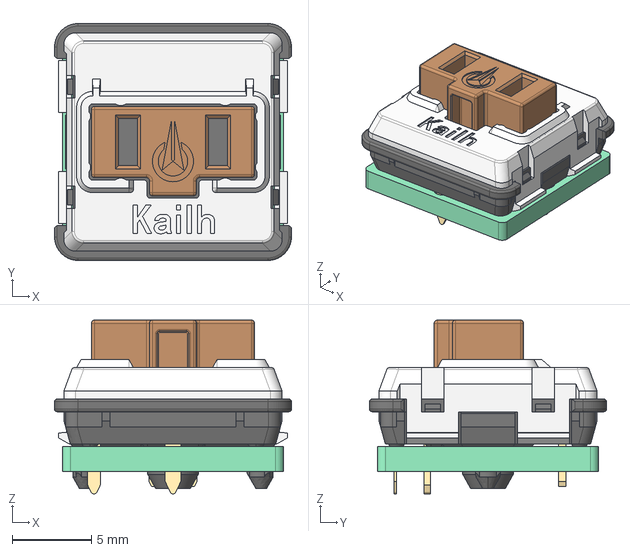
[picture p252: CAD file, 2026-08-26]
Macropad/Models/kailh-choc-low-profile-switch-1.snapshot.3/Kailh Choc Low Profile Switch.step
15.0 x 15.0 x 11.0 mm
