bleroy/3d-junkyard/Macropad/Models/kailh-lp-choc-pc-keycap-1.snapshot.3/Kailh LP Choc PC Keycap.step

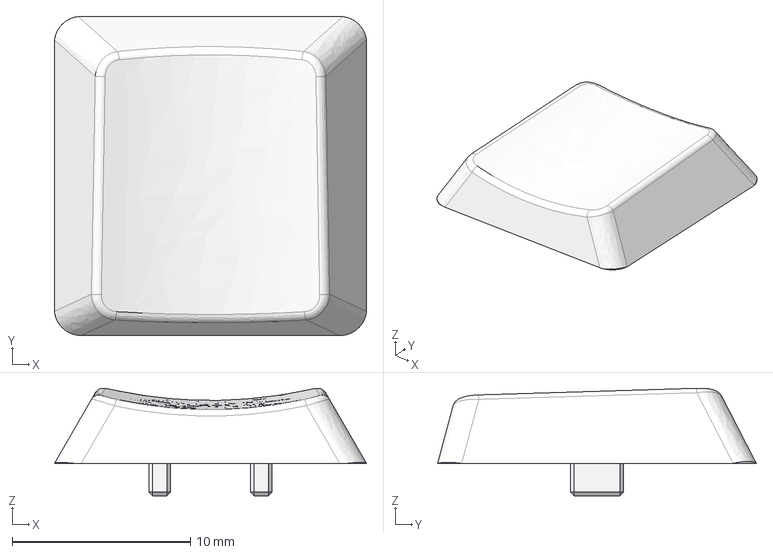
[picture p253: CAD file, 2026-08-26]
Macropad/Models/kailh-lp-choc-pc-keycap-1.snapshot.3/Kailh LP Choc PC Keycap.step
17.5 x 17.9 x 6.03 mm
