bleroy/3d-junkyard/misc-models/Atari/CartridgePortXLXEGS.step

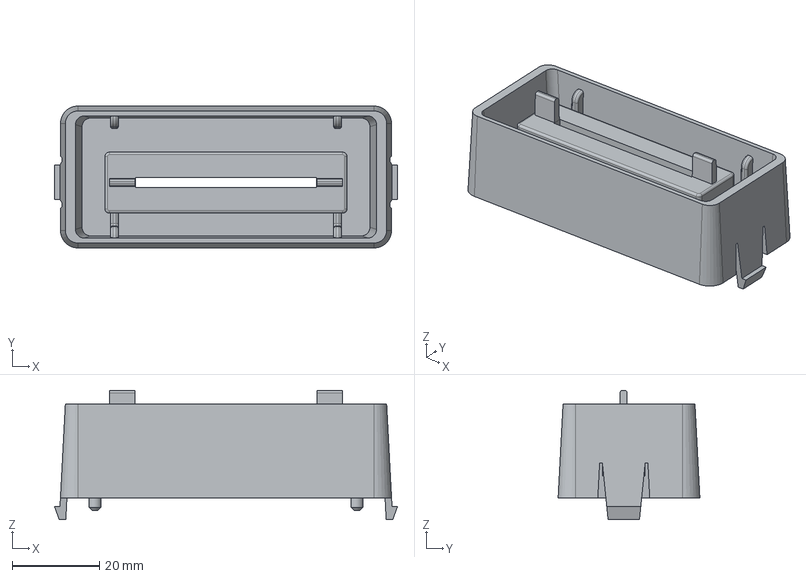
[picture p254: CAD file, 2026-08-10]
misc-models/Atari/CartridgePortXLXEGS.step
78.6 x 32.5 x 29.6 mm
