bleroy/3d-junkyard/misc-models/Bowl/Spill proof bowl holder.FCStd

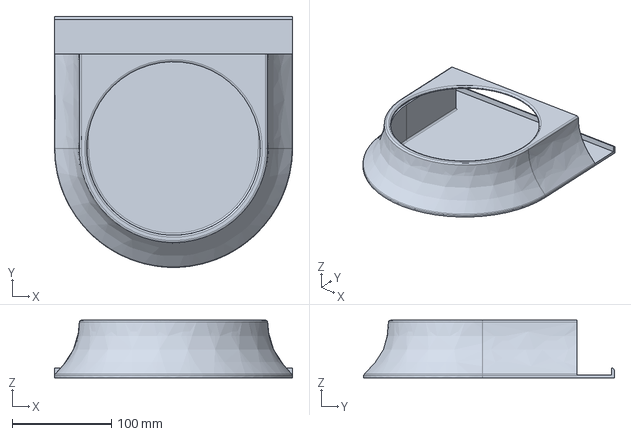
[picture p255: CAD file, 2025-01-10]
misc-models/Bowl/Spill proof bowl holder.FCStd
240.0 x 253.0 x 58.0 mm
