bleroy/3d-junkyard/misc-models/Cans/CanTop.stl

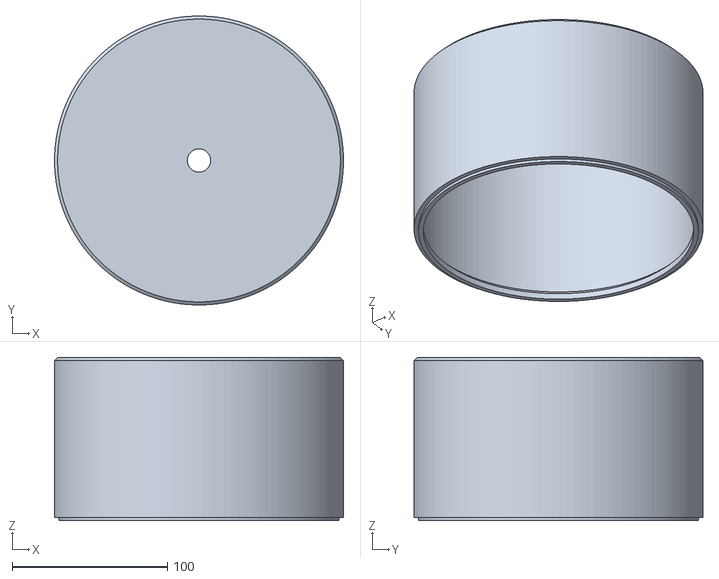
[picture p256: CAD file, 2025-05-28]
misc-models/Cans/CanTop.stl
186.0 x 185.9 x 105.0
