bleroy/3d-junkyard/misc-models/Caps/LowPolySpaceBar.FCStd

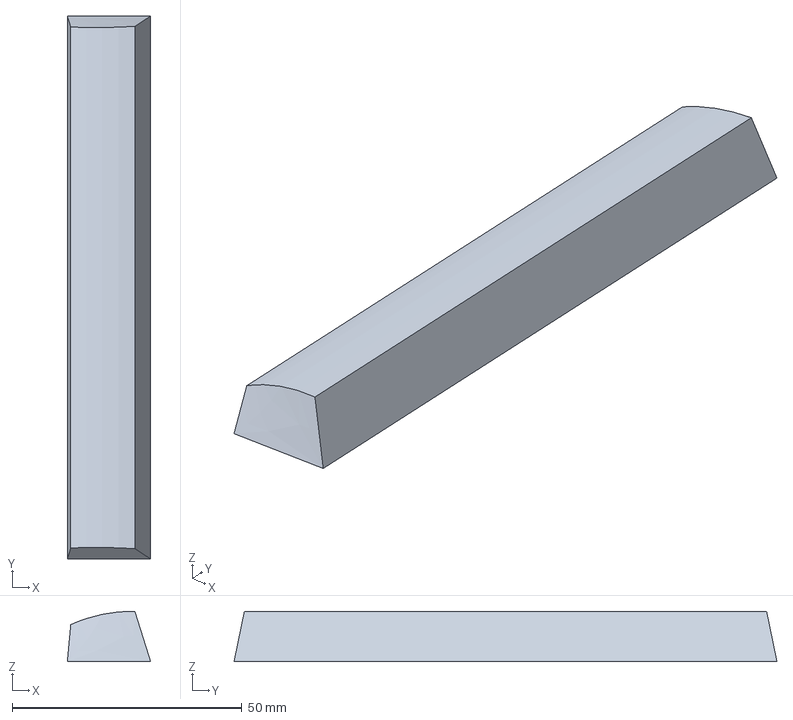
[picture p257: CAD file, 2026-08-10]
misc-models/Caps/LowPolySpaceBar.FCStd
18.2 x 118.2 x 11.0 mm
