bleroy/3d-junkyard/misc-models/CarbonX1/CarbonX1 poop chute table.FCStd

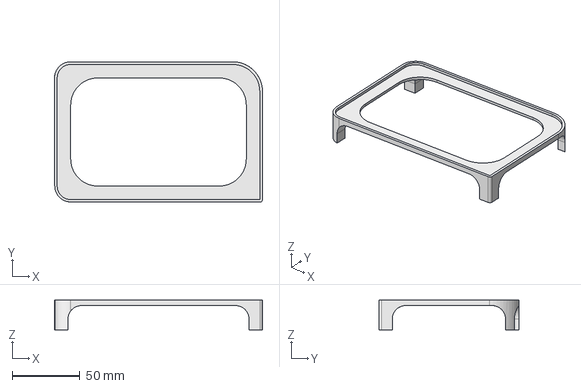
[picture p258: CAD file, 2024-07-21]
misc-models/CarbonX1/CarbonX1 poop chute table.FCStd
154.0 x 104.0 x 22.0 mm
