bleroy/3d-junkyard/misc-models/Cello/CasePodsHolder-Body.stl

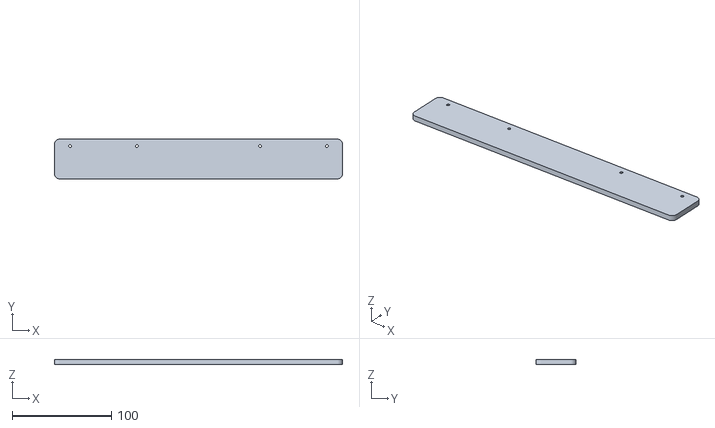
[picture p259: CAD file, 2025-01-10]
misc-models/Cello/CasePodsHolder-Body.stl
290.0 x 40.0 x 5.00
