bleroy/3d-junkyard/misc-models/Eufymake/AtariXE-Console-print-rig.FCStd

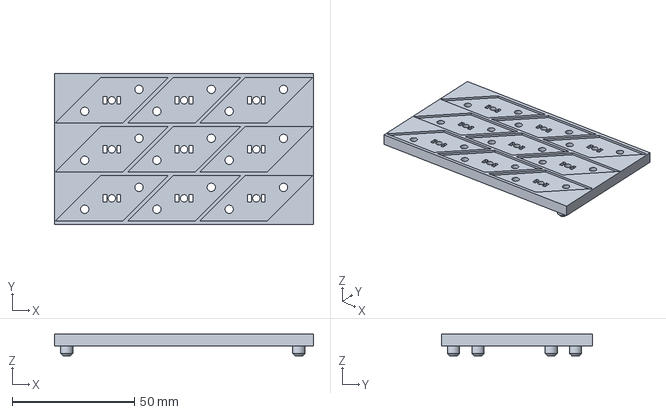
[picture p260: CAD file, 2026-08-10]
misc-models/Eufymake/AtariXE-Console-print-rig.FCStd
106.0 x 62.0 x 9.00 mm
