bleroy/3d-junkyard/misc-models/Fessetoule/FesseTouleRails-ThreadsOnRail.stl

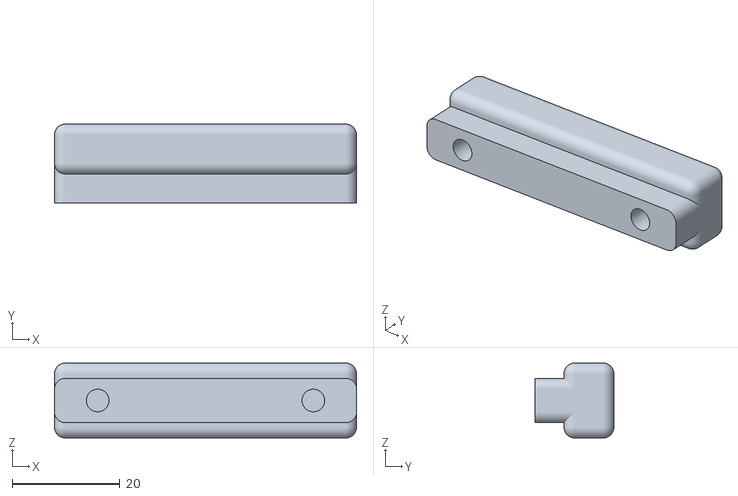
[picture p261: CAD file, 2024-09-04]
misc-models/Fessetoule/FesseTouleRails-ThreadsOnRail.stl
56.0 x 14.6 x 13.9
