bleroy/3d-junkyard/misc-models/Frames/Frame-Back.3mf

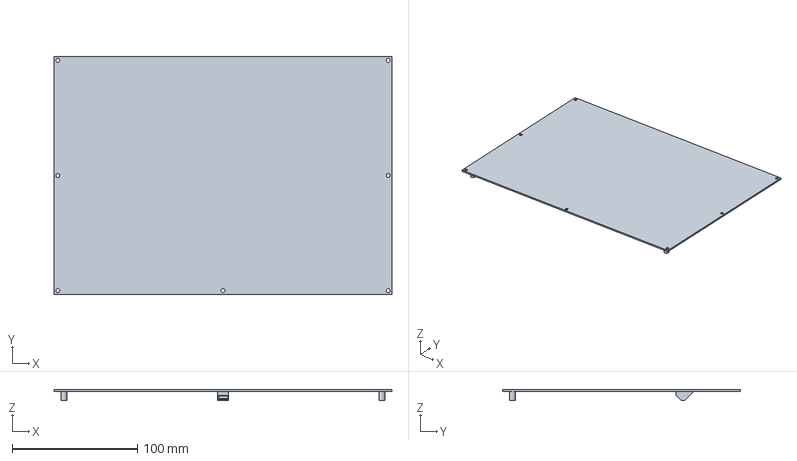
[picture p262: CAD file, 2026-04-19]
misc-models/Frames/Frame-Back.3mf
270.0 x 190.0 x 8.50 mm
