bleroy/3d-junkyard/misc-models/Gridfinity/Gridfinity_LEGO_Dimensions.FCStd

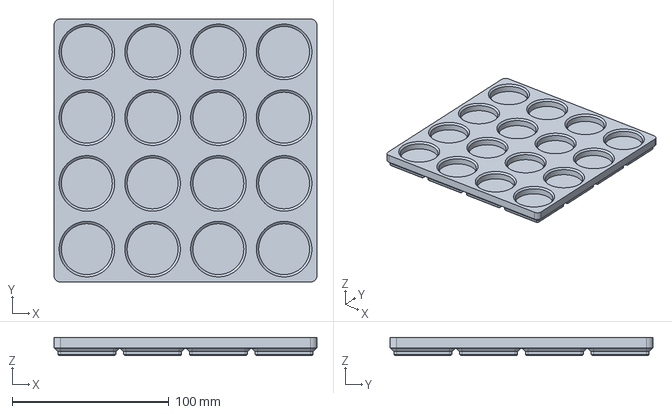
[picture p263: CAD file, 2026-08-10]
misc-models/Gridfinity/Gridfinity_LEGO_Dimensions.FCStd
168.0 x 168.0 x 11.8 mm
