bleroy/3d-junkyard/misc-models/H2C/PoopChute-All parts.3mf

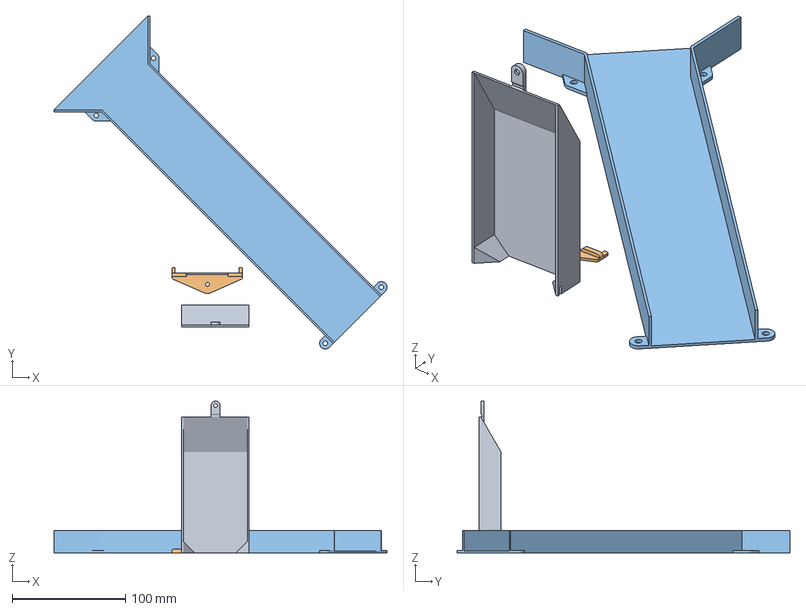
[picture p264: CAD file, 2026-04-19]
misc-models/H2C/PoopChute-All parts.3mf
293.9 x 293.9 x 134.0 mm
