bleroy/3d-junkyard/misc-models/Headphones/Sony MDR-V50 repair-right.3mf

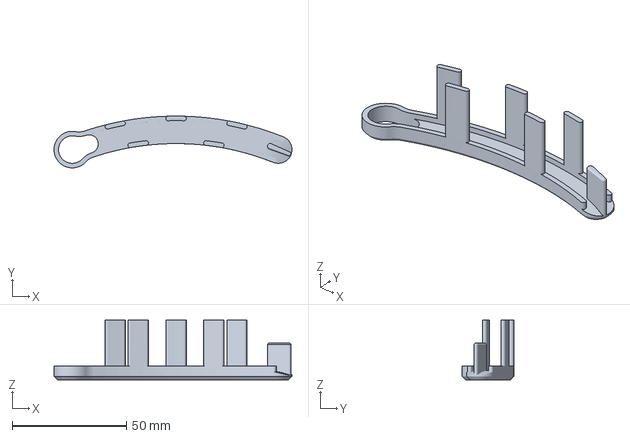
[picture p265: CAD file, 2026-08-10]
misc-models/Headphones/Sony MDR-V50 repair-right.3mf
104.0 x 22.6 x 26.0 mm
