bleroy/3d-junkyard/misc-models/HexLattice/Printed/WearableHexLattice.FCStd

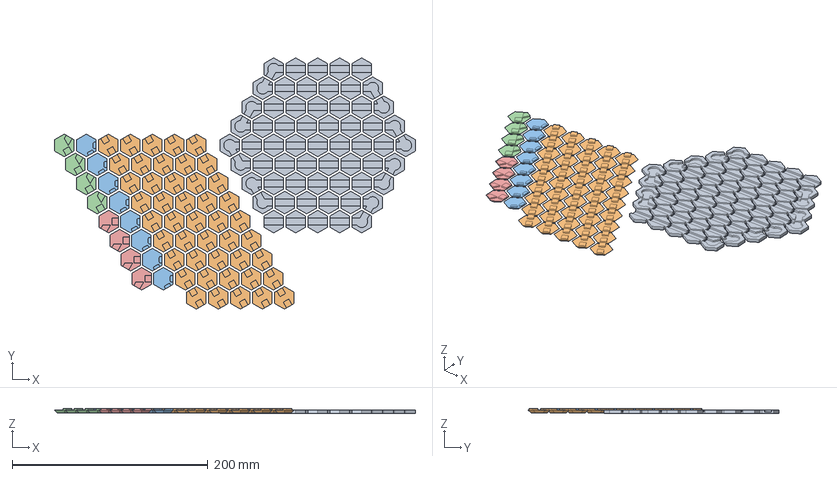
[picture p266: CAD file, 2024-09-04]
misc-models/HexLattice/Printed/WearableHexLattice.FCStd
369.1 x 256.9 x 5.00 mm
BottomPartToPrint
Populate Populate LinearArray005 with LinearArray006 with StraightTop001
Populate LinearArray007 with 120TurnTop001
Populate LinearArray008 with 60TurnTop001
Populate LinearArray008 with 60TurnTop002
