bleroy/3d-junkyard/misc-models/HouseRepairs/IkeaDrawerFixBracket.FCStd

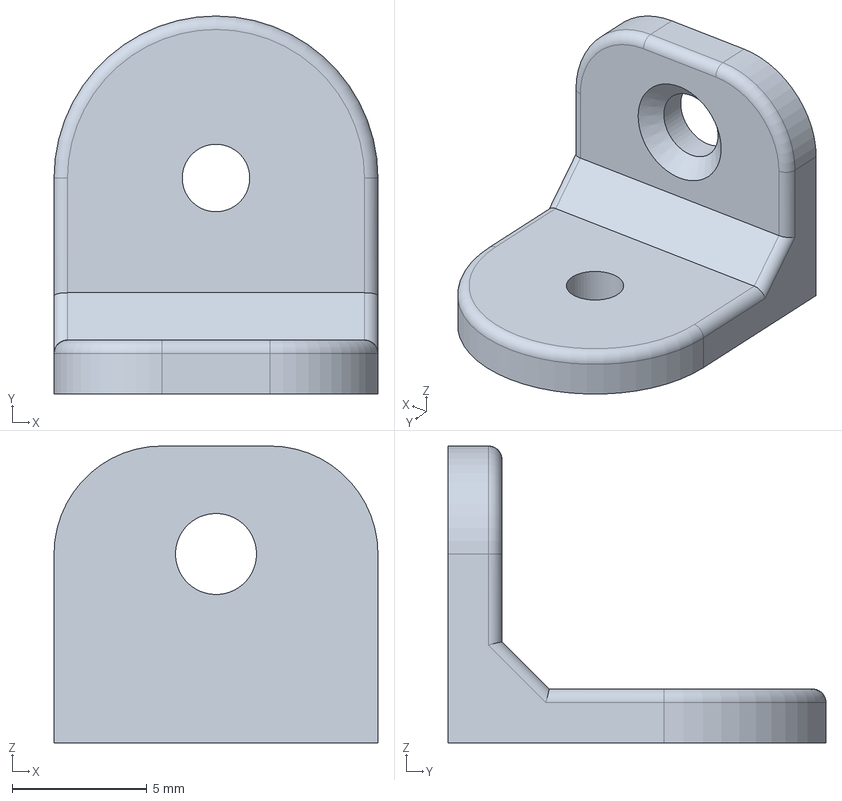
[picture p267: CAD file, 2026-10-01]
misc-models/HouseRepairs/IkeaDrawerFixBracket.FCStd
12.0 x 14.0 x 11.0 mm
