bleroy/3d-junkyard/misc-models/KeyboardTester/Enclosure/Decent Retro Keyboard Tester Enclosure-Bottom.stl

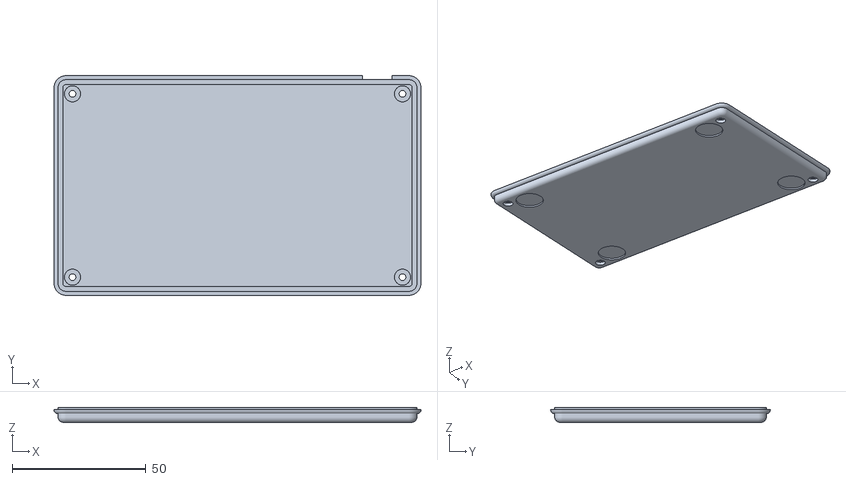
[picture p268: CAD file, 2025-04-13]
misc-models/KeyboardTester/Enclosure/Decent Retro Keyboard Tester Enclosure-Bottom.stl
137.0 x 82.0 x 5.50
