bleroy/3d-junkyard/misc-models/KeyboardTester/Overlays/Decent Retro Keyboard Tester Enclosure-Light tunnels.stl

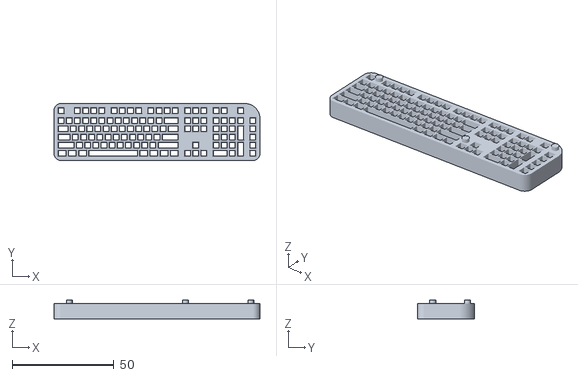
[picture p269: CAD file, 2025-03-02]
misc-models/KeyboardTester/Overlays/Decent Retro Keyboard Tester Enclosure-Light tunnels.stl
101.0 x 28.0 x 9.10
