bleroy/3d-junkyard/misc-models/KeyboardTester/Overlays/XE-overlay/Decent Retro Keyboard Tester Enclosure-ATARI-XE-Light tunnels.stl

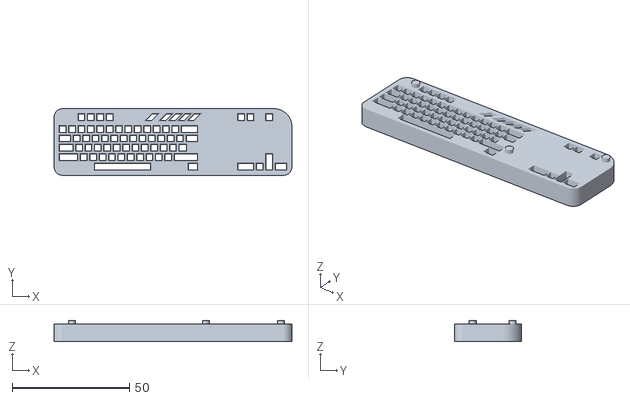
[picture p270: CAD file, 2025-04-13]
misc-models/KeyboardTester/Overlays/XE-overlay/Decent Retro Keyboard Tester Enclosure-ATARI-XE-Light tunnels.stl
101.4 x 28.4 x 9.10
