bleroy/3d-junkyard/misc-models/KeyboardTester/shapes3D/SK6805-EC15.step

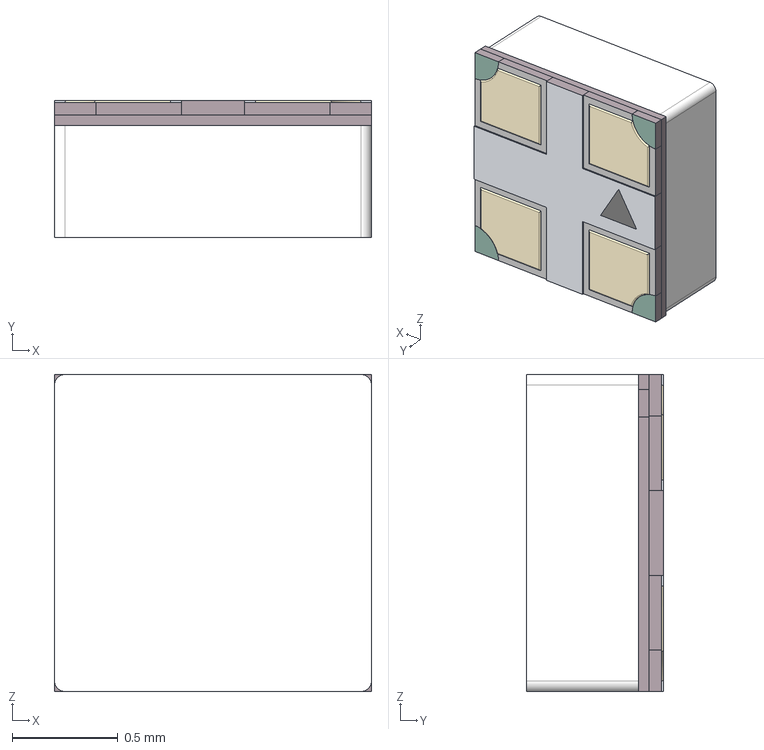
[picture p271: CAD file, 2025-03-02]
misc-models/KeyboardTester/shapes3D/SK6805-EC15.step
1.50 x 0.65 x 1.50 mm
