bleroy/3d-junkyard/misc-models/Kobra Max/FilamentHolderAxle.FCStd

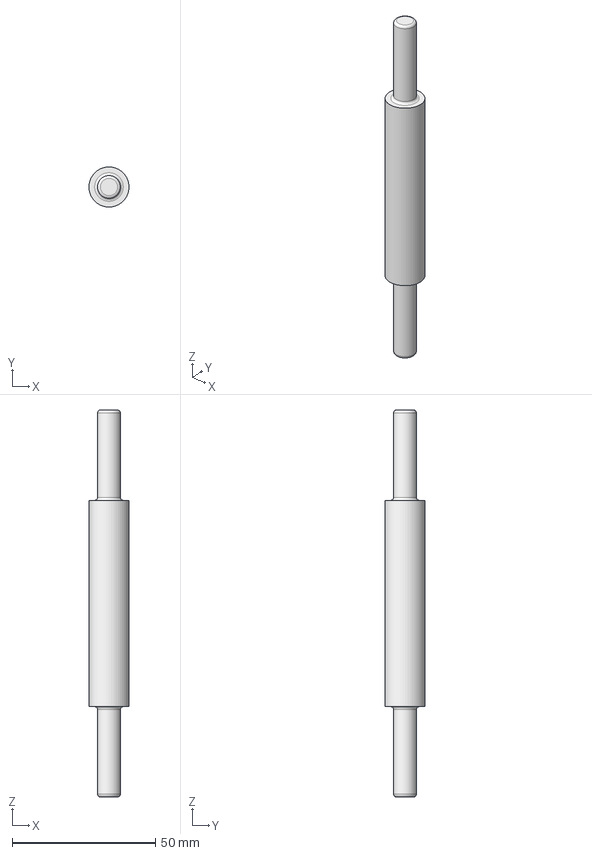
[picture p272: CAD file, 2023-12-09]
misc-models/Kobra Max/FilamentHolderAxle.FCStd
14.0 x 14.0 x 135.0 mm
