bleroy/3d-junkyard/misc-models/Lab/ProbeHolder.FCStd

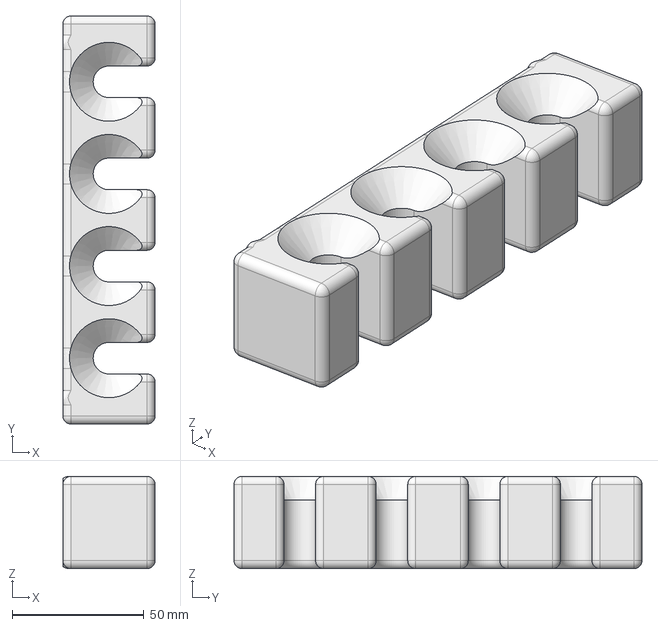
[picture p273: CAD file, 2023-10-16]
misc-models/Lab/ProbeHolder.FCStd
35.0 x 155.0 x 35.0 mm
