bleroy/3d-junkyard/misc-models/Measuring/KeyboardUnitRuler.FCStd

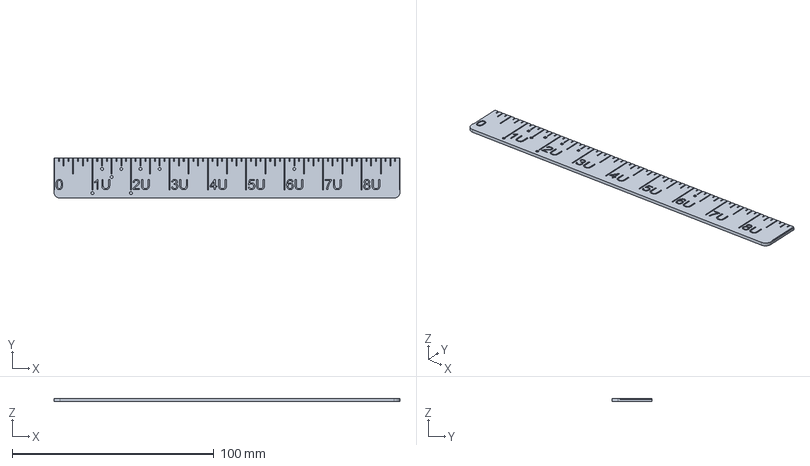
[picture p274: CAD file, 2026-08-10]
misc-models/Measuring/KeyboardUnitRuler.FCStd
171.4 x 20.0 x 1.50 mm
