bleroy/3d-junkyard/misc-models/MiniPC/MiniMonitor.stl

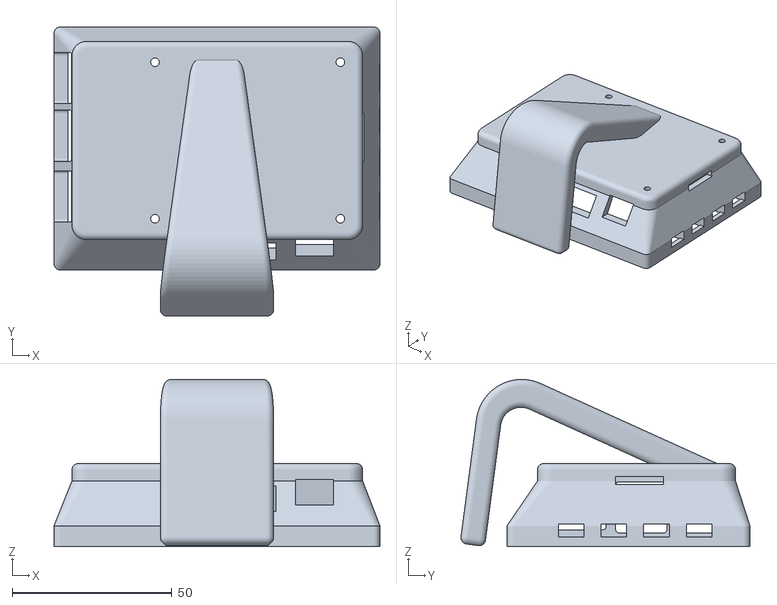
[picture p275: CAD file, 2023-04-02]
misc-models/MiniPC/MiniMonitor.stl
102.0 x 90.4 x 52.3
