bleroy/3d-junkyard/misc-models/Minishelves/PopBracket.FCStd

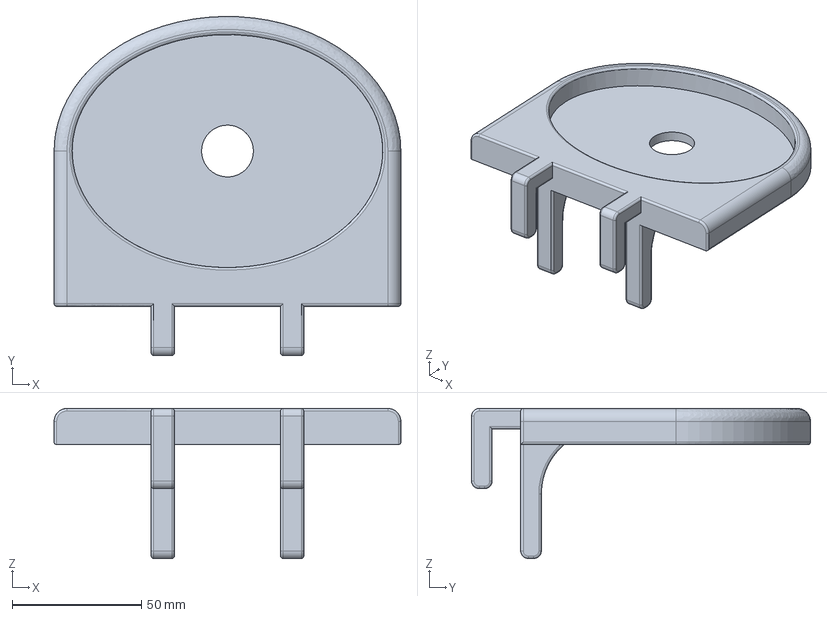
[picture p276: CAD file, 2024-10-24]
misc-models/Minishelves/PopBracket.FCStd
134.0 x 131.0 x 58.0 mm
