bleroy/3d-junkyard/misc-models/Music/LedGuitarStrap/printed/GuitarStrapControllerEnclosure-TopPart.3mf

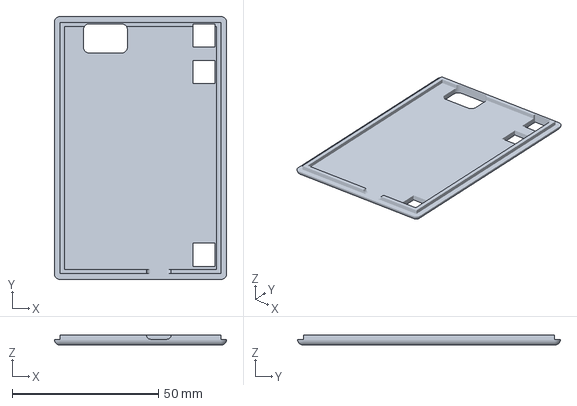
[picture p277: CAD file, 2025-01-10]
misc-models/Music/LedGuitarStrap/printed/GuitarStrapControllerEnclosure-TopPart.3mf
59.0 x 90.0 x 3.50 mm
