bleroy/3d-junkyard/misc-models/Music/Mediator box-top.3mf

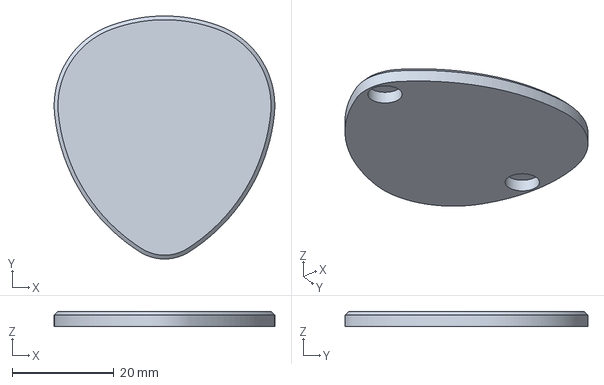
[picture p278: CAD file, 2026-03-14]
misc-models/Music/Mediator box-top.3mf
43.4 x 47.7 x 3.00 mm
