bleroy/3d-junkyard/misc-models/NanoPC/keyboard/NanoKeyboard.FCStd

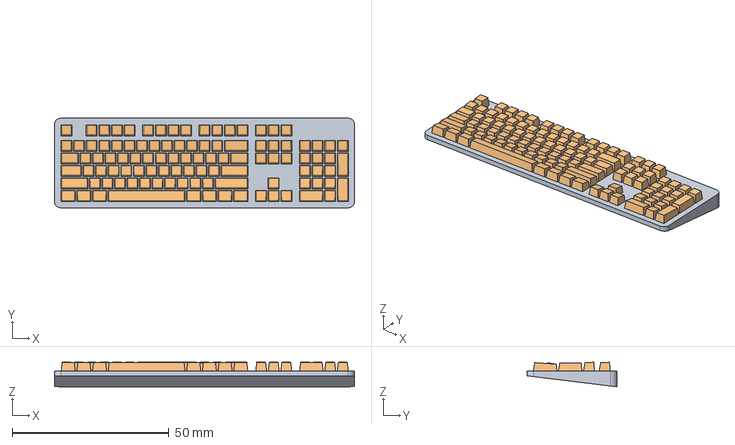
[picture p279: CAD file, 2025-03-02]
misc-models/NanoPC/keyboard/NanoKeyboard.FCStd
95.6 x 28.6 x 7.85 mm
Base
Keys
