bleroy/3d-junkyard/misc-models/Optical/Catadioptre.FCStd

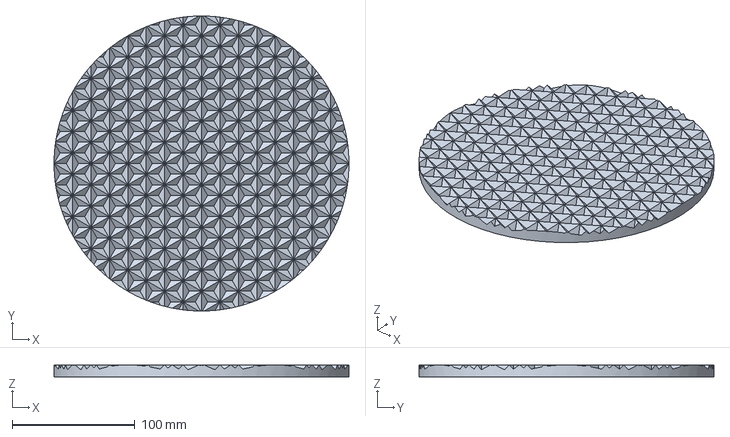
[picture p280: CAD file, 2025-08-22]
misc-models/Optical/Catadioptre.FCStd
240.0 x 240.0 x 10.0 mm
