bleroy/3d-junkyard/misc-models/OrientableSupport/VerticalProjectorSupport-ProjectorHold.3mf

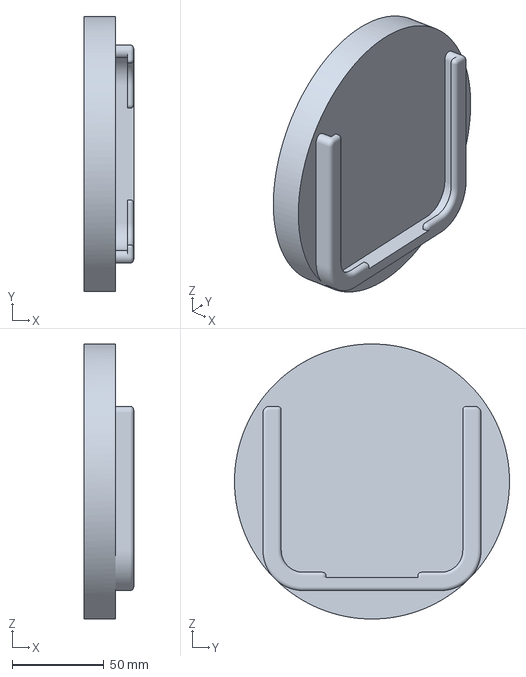
[picture p281: CAD file, 2026-08-10]
misc-models/OrientableSupport/VerticalProjectorSupport-ProjectorHold.3mf
27.0 x 150.0 x 150.0 mm
