bleroy/3d-junkyard/misc-models/PedalRack/PedalRack-MiddlePart-Fat.3mf

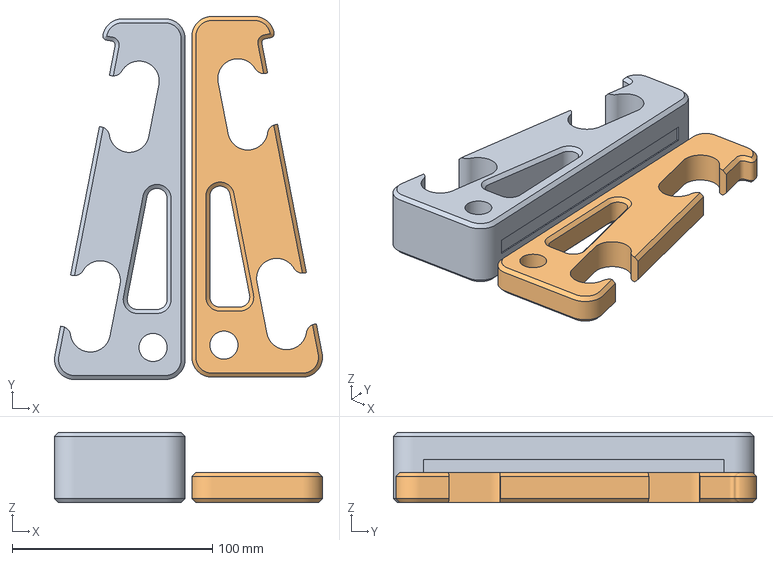
[picture p282: CAD file, 2024-09-04]
misc-models/PedalRack/PedalRack-MiddlePart-Fat.3mf
133.7 x 181.2 x 35.0 mm
PedalRack-MiddlePart-Fat.stl
PedalRack-MiddlePart.stl
