bleroy/3d-junkyard/misc-models/ProbeHolderTable.FCStd

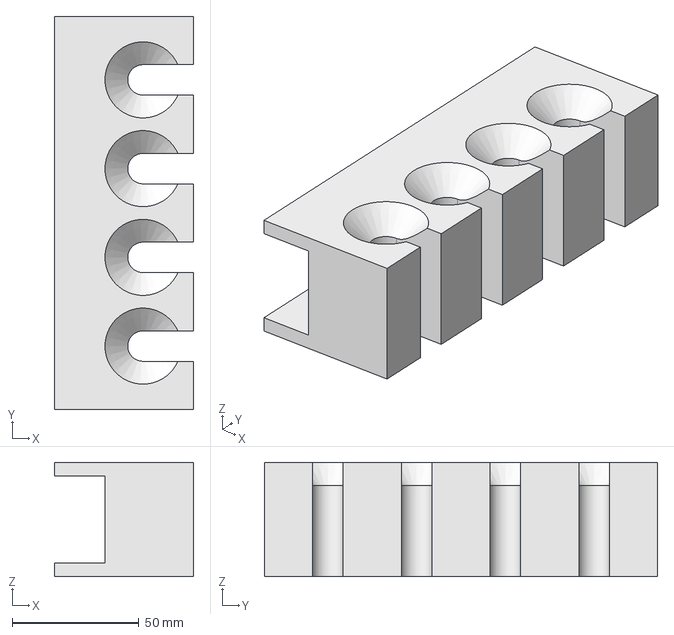
[picture p283: CAD file, 2023-10-16]
misc-models/ProbeHolderTable.FCStd
55.0 x 155.0 x 45.0 mm
