bleroy/3d-junkyard/misc-models/RetroChipTester/RetroChipTesterCase.FCStd

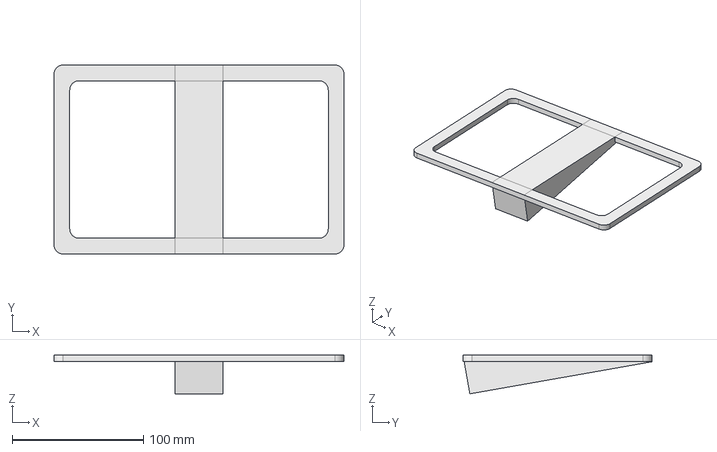
[picture p284: CAD file, 2023-07-05]
misc-models/RetroChipTester/RetroChipTesterCase.FCStd
221.0 x 144.0 x 29.5 mm
