bleroy/3d-junkyard/misc-models/Skadis/BetweenTheBeams-PartC.3mf

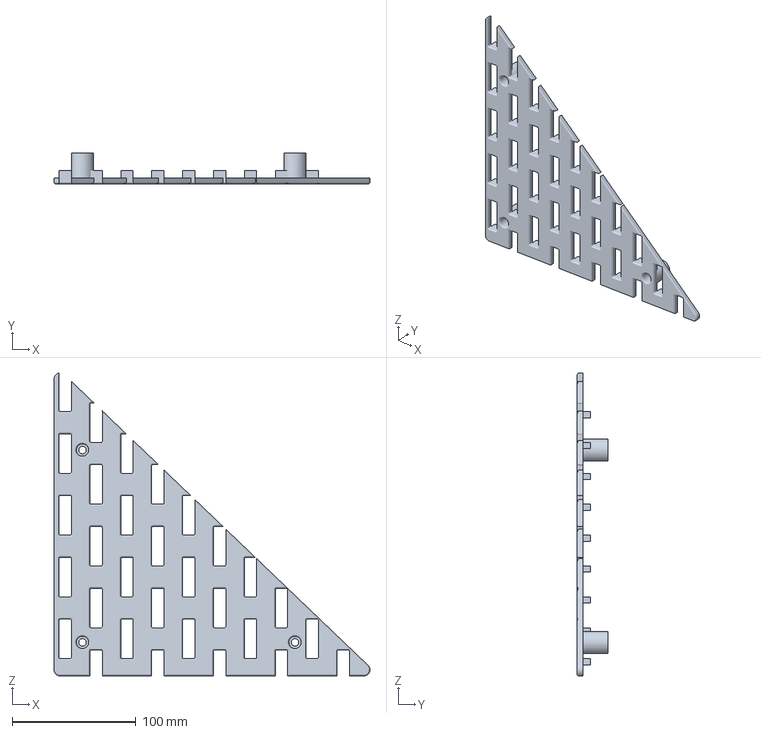
[picture p285: CAD file, 2026-08-10]
misc-models/Skadis/BetweenTheBeams-PartC.3mf
255.8 x 24.9 x 245.2 mm
