bleroy/3d-junkyard/misc-models/Toothbrush/Toothbrush charging base.FCStd

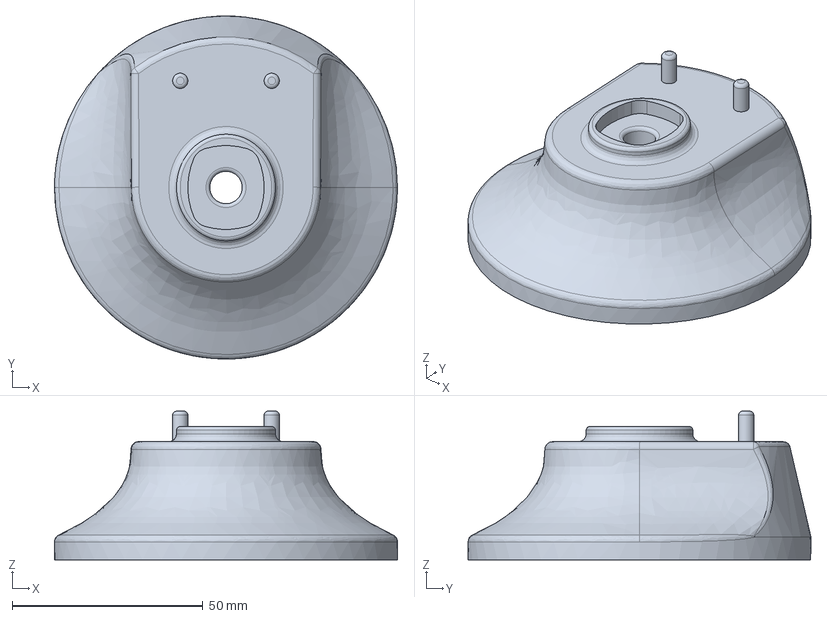
[picture p286: CAD file, 2024-12-02]
misc-models/Toothbrush/Toothbrush charging base.FCStd
90.0 x 90.0 x 39.0 mm
