bleroy/3d-junkyard/Atari130MX/Caps/f1-4-set-choc.stl

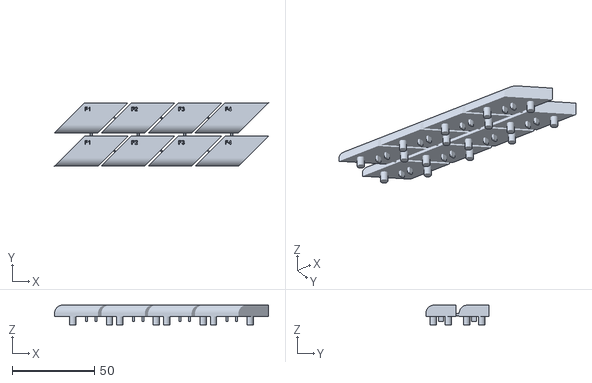
[picture p287: CAD file, 2023-06-15]
Atari130MX/Caps/f1-4-set-choc.stl
129.8 x 38.3 x 12.0
