bleroy/3d-junkyard/Atari130MX/Stabilizers/ConsoleKeyPlate.stl

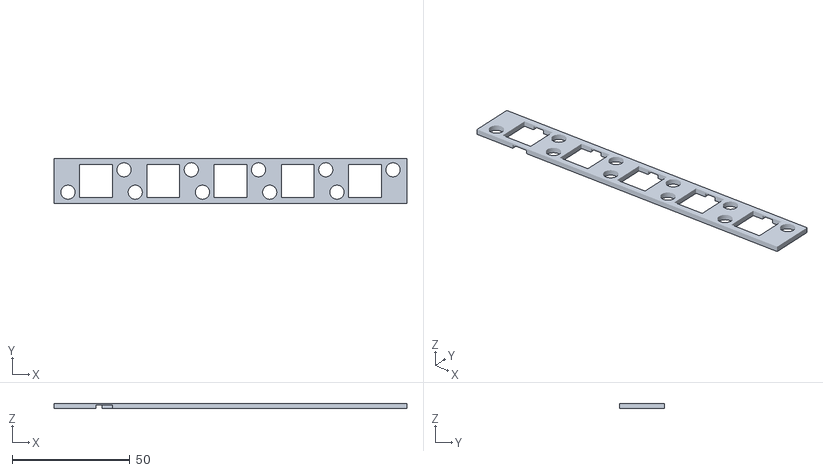
[picture p288: CAD file, 2023-09-24]
Atari130MX/Stabilizers/ConsoleKeyPlate.stl
150.0 x 19.0 x 2.20
