bleroy/3d-junkyard/Atari130MX/Stems/kailh-choc-to-xl-console.stl

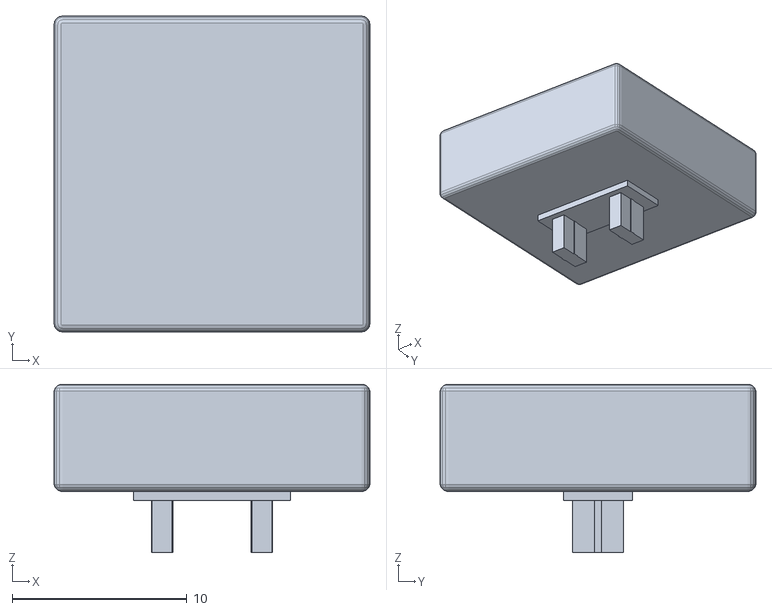
[picture p289: CAD file, 2023-09-24]
Atari130MX/Stems/kailh-choc-to-xl-console.stl
18.1 x 18.1 x 9.64
