bleroy/3d-junkyard/Decent1200/Adapters/ResetKeyPad.stl

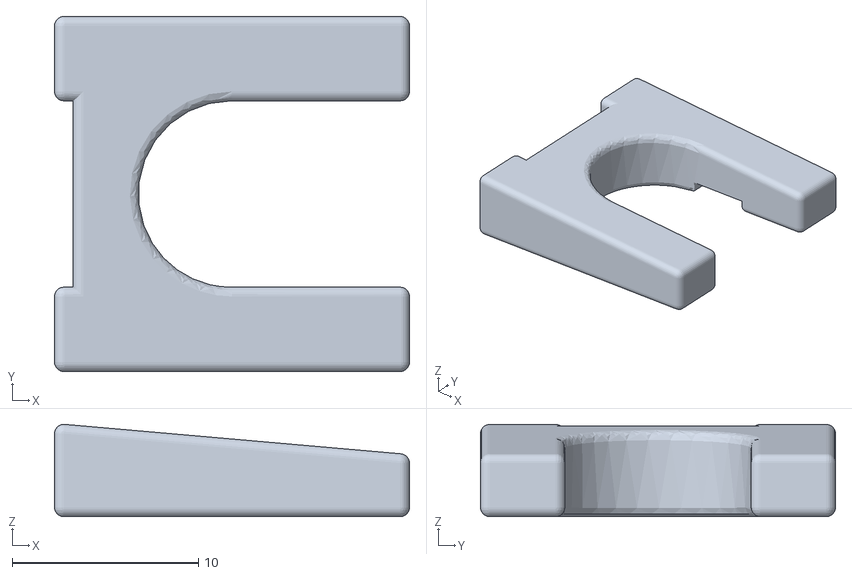
[picture p290: CAD file, 2024-01-14]
Decent1200/Adapters/ResetKeyPad.stl
19.0 x 19.0 x 4.95
