bleroy/3d-junkyard/Decent1200/Caps/Decent1200-console-choc-x12.stl

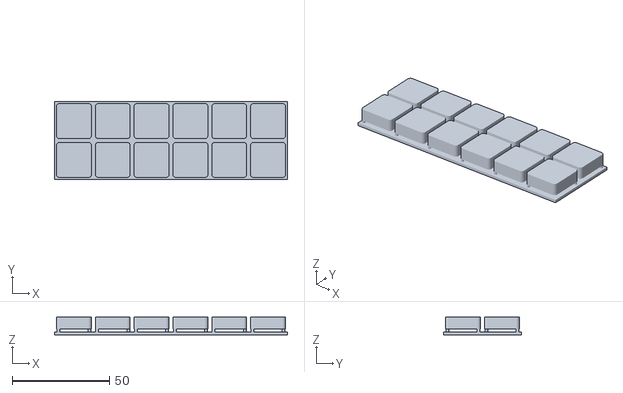
[picture p291: CAD file, 2024-04-16]
Decent1200/Caps/Decent1200-console-choc-x12.stl
120.0 x 40.0 x 9.15
