bleroy/3d-junkyard/Decent400/Caps/SpaceBar-flat-top.3mf

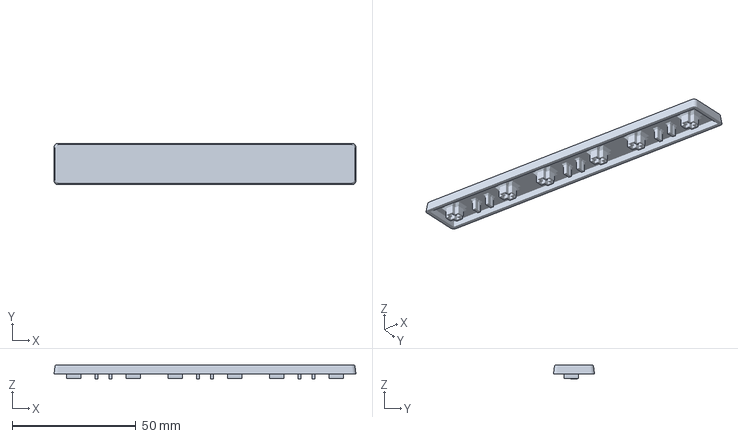
[picture p292: CAD file, 2026-04-18]
Decent400/Caps/SpaceBar-flat-top.3mf
122.0 x 16.6 x 5.60 mm
