bleroy/3d-junkyard/Decent400/Misc/Decent400CapPrintRig-Space bar fixture plate.3mf

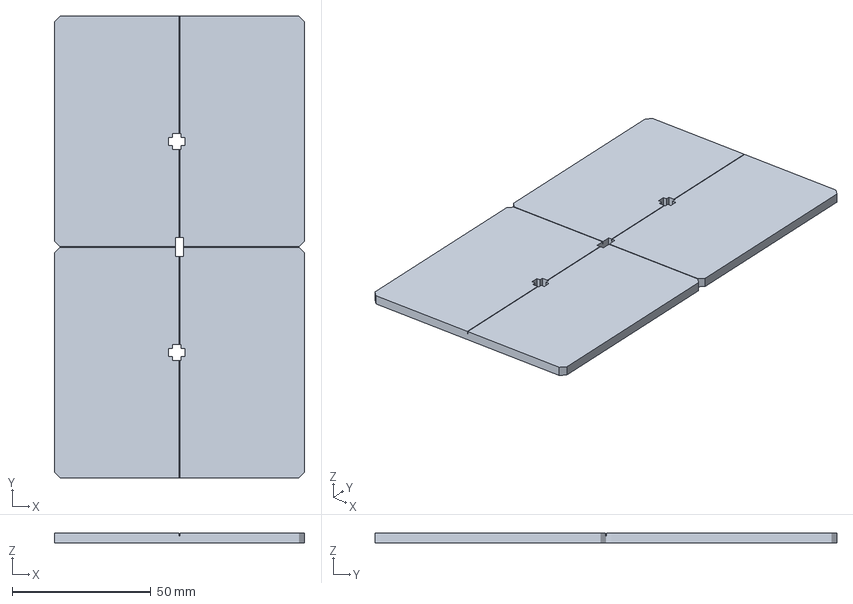
[picture p293: CAD file, 2026-04-18]
Decent400/Misc/Decent400CapPrintRig-Space bar fixture plate.3mf
90.0 x 166.2 x 3.50 mm
