bleroy/3d-junkyard/Decent800/Misc/Decent800 left bracket rev 2.3mf

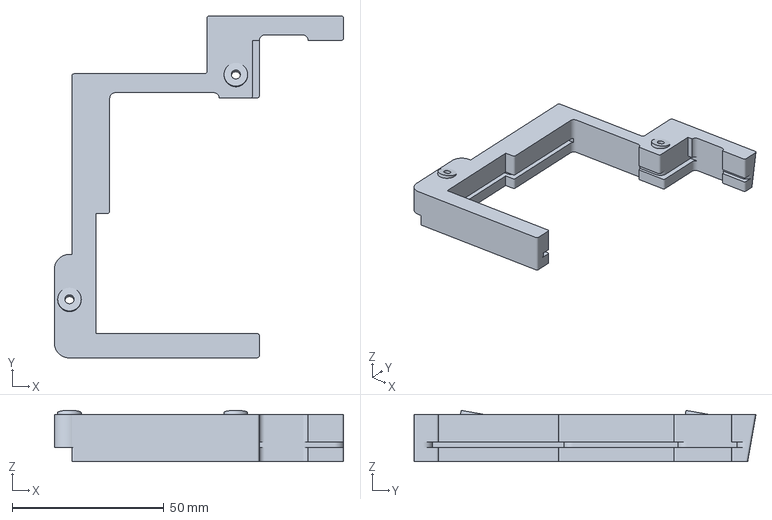
[picture p294: CAD file, 2026-10-01]
Decent800/Misc/Decent800 left bracket rev 2.3mf
95.2 x 112.6 x 16.9 mm
