bleroy/3d-junkyard/DecentCart/3DModels/rpi_rmc20452t.step

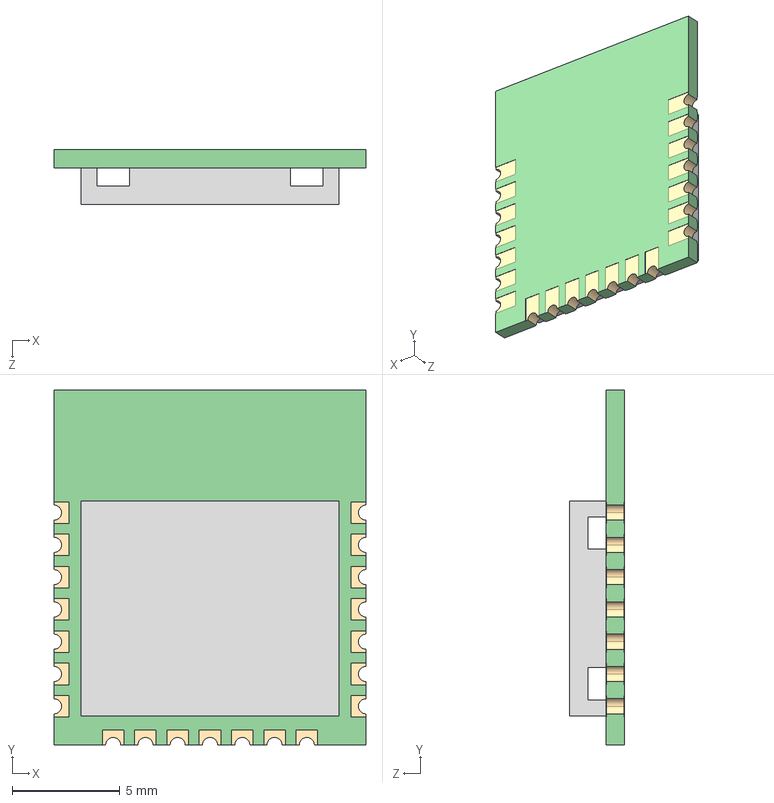
[picture p295: CAD file, 2025-08-22]
DecentCart/3DModels/rpi_rmc20452t.step
14.5 x 16.5 x 2.55 mm
