bleroy/3d-junkyard/DecenTKL/Caps/ConsoleXE-F1-4.FCStd

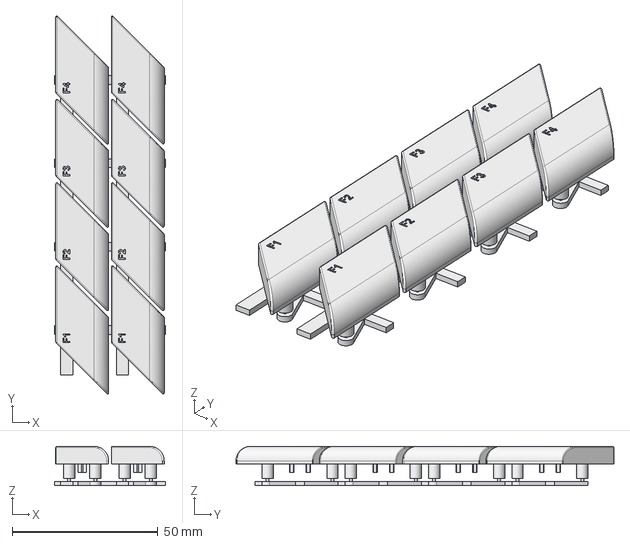
[picture p296: CAD file, 2024-08-09]
DecenTKL/Caps/ConsoleXE-F1-4.FCStd
38.1 x 129.7 x 13.5 mm
