bleroy/3d-junkyard/DecenTKL/Enclosure/DecenTKL-Enclosure.FCStd

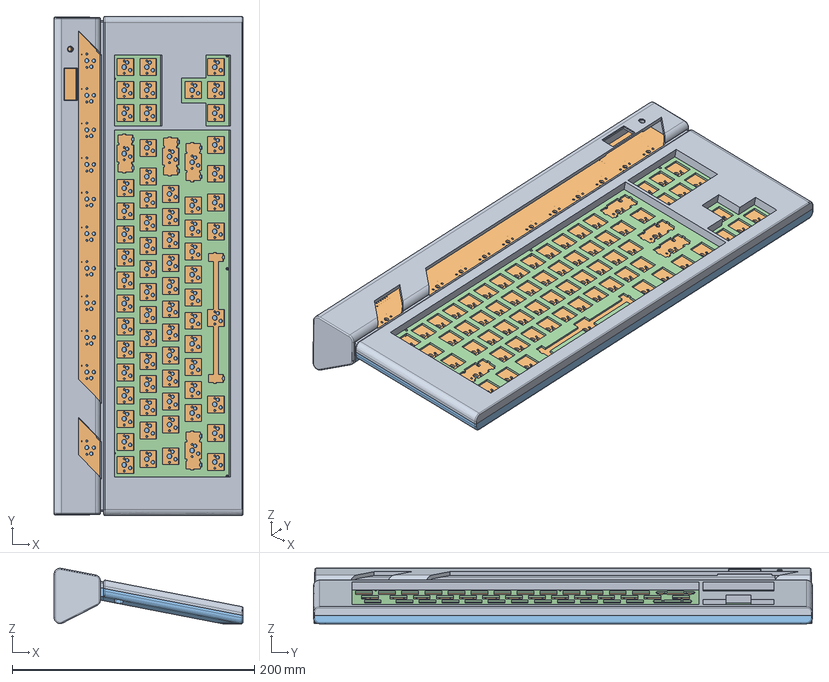
[picture p297: CAD file, 2024-11-14]
DecenTKL/Enclosure/DecenTKL-Enclosure.FCStd
156.0 x 412.2 x 45.9 mm
EnclosureTopBody
DecenTKL_PCB
EnclosureBottomBody
DecenTKL-plate_PCB
