bleroy/3d-junkyard/DecenTKL/Misc/OledSupport.stl

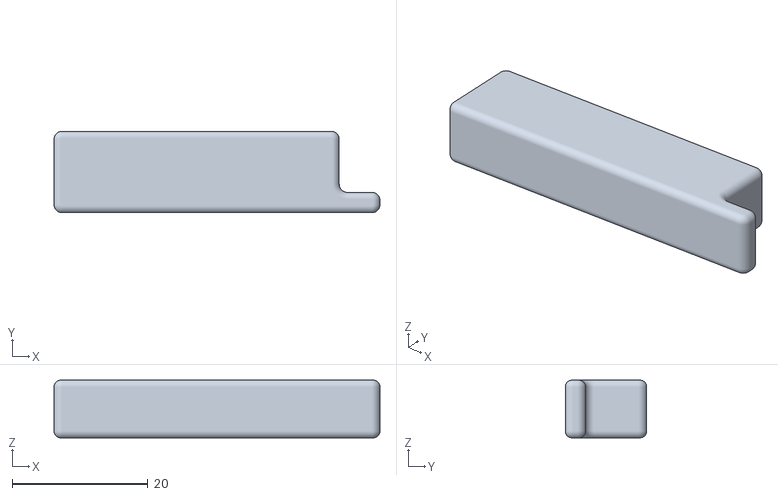
[picture p298: CAD file, 2024-11-14]
DecenTKL/Misc/OledSupport.stl
48.0 x 12.0 x 8.50
