bleroy/3d-junkyard/DecenTKL/NumPadEnclosure/DecenTKL-Numpad-Enclosure-Bottom.3mf

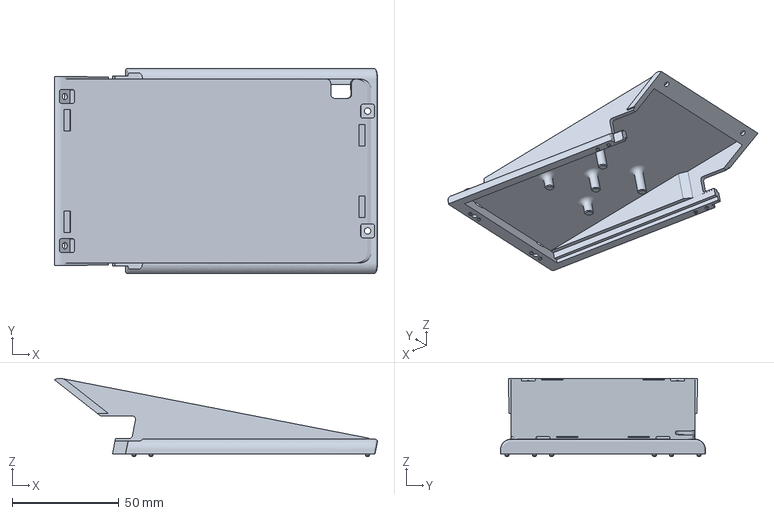
[picture p299: CAD file, 2024-10-14]
DecenTKL/NumPadEnclosure/DecenTKL-Numpad-Enclosure-Bottom.3mf
151.6 x 96.2 x 36.8 mm
