bleroy/3d-junkyard/DecentUSB/DecentUSB2350/Models/SO8 Wide 7.50mm.step

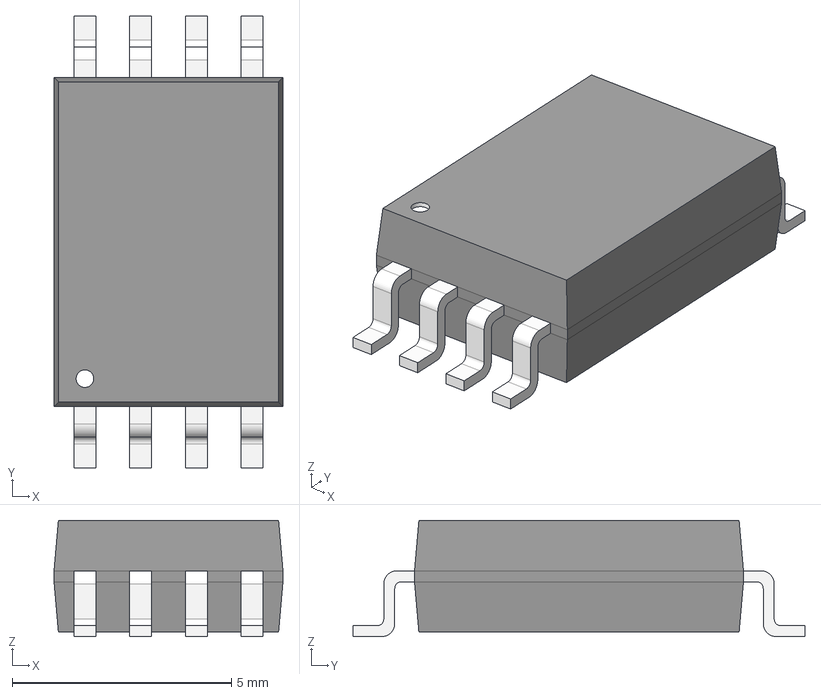
[picture p300: CAD file, 2024-10-14]
DecentUSB/DecentUSB2350/Models/SO8 Wide 7.50mm.step
5.22 x 10.3 x 2.65 mm
