bleroy/3d-junkyard/DecentXE/Misc/LED-red-lens.FCStd

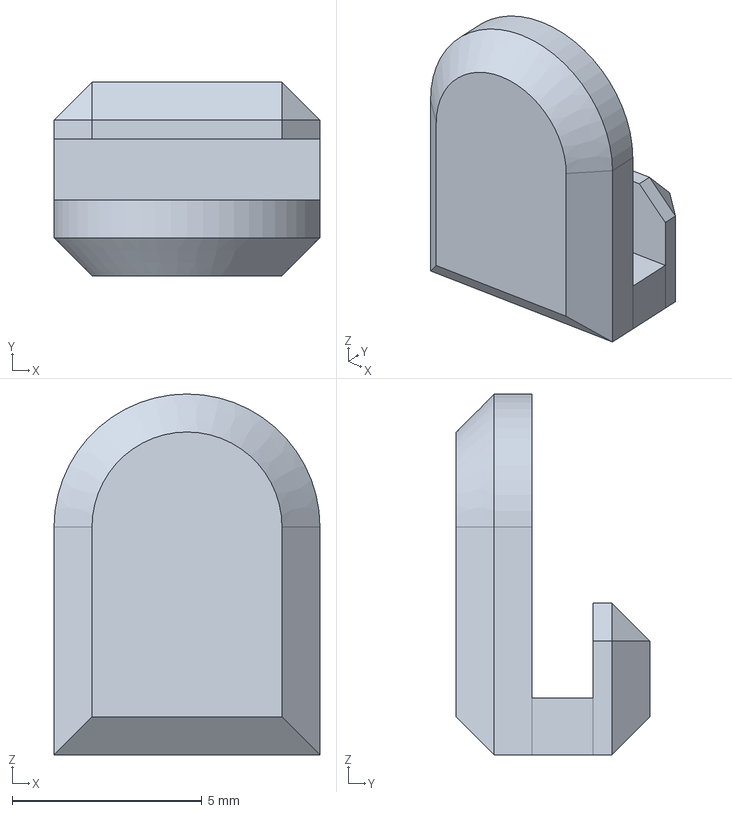
[picture p301: CAD file, 2026-02-04]
DecentXE/Misc/LED-red-lens.FCStd
7.00 x 5.10 x 9.50 mm
