bleroy/3d-junkyard/DecentXE/Stabilizers/HeightPadding.FCStd

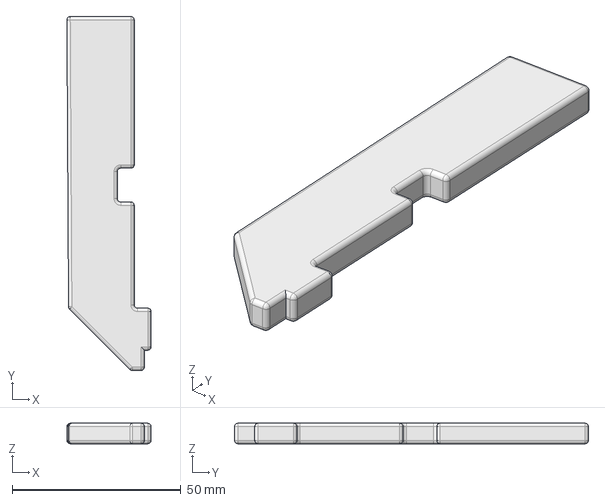
[picture p302: CAD file, 2024-07-21]
DecentXE/Stabilizers/HeightPadding.FCStd
25.0 x 105.0 x 6.10 mm
