bleroy/3d-junkyard/DecentXL/Adapters/StackpoleXLSpaceStabilizerAdapter.FCStd

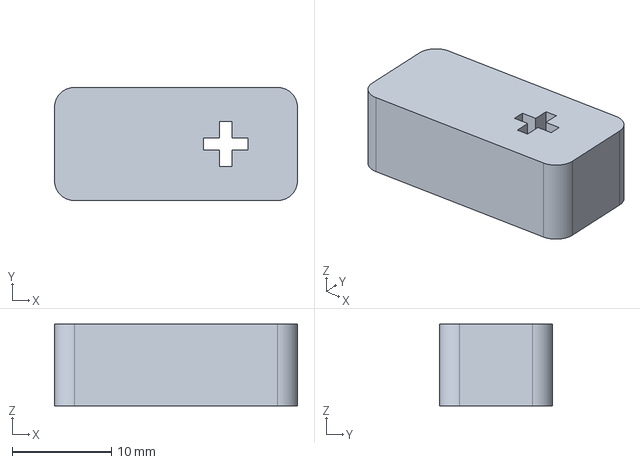
[picture p303: CAD file, 2024-11-30]
DecentXL/Adapters/StackpoleXLSpaceStabilizerAdapter.FCStd
24.5 x 11.4 x 8.25 mm
