bleroy/3d-junkyard/DecentXL/Brackets/DecentXL-Left-Bracket.FCStd

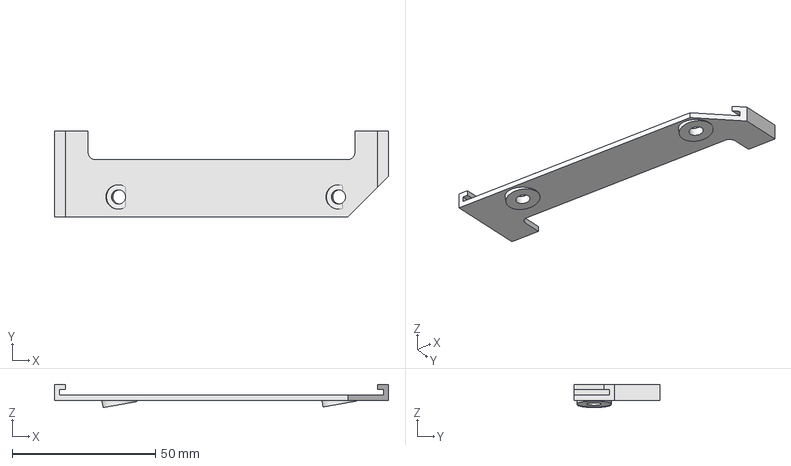
[picture p304: CAD file, 2023-12-04]
DecentXL/Brackets/DecentXL-Left-Bracket.FCStd
116.5 x 30.0 x 8.08 mm
