bleroy/3d-junkyard/JoyKeyMX/Case/JoyKeyCase-Top.stl

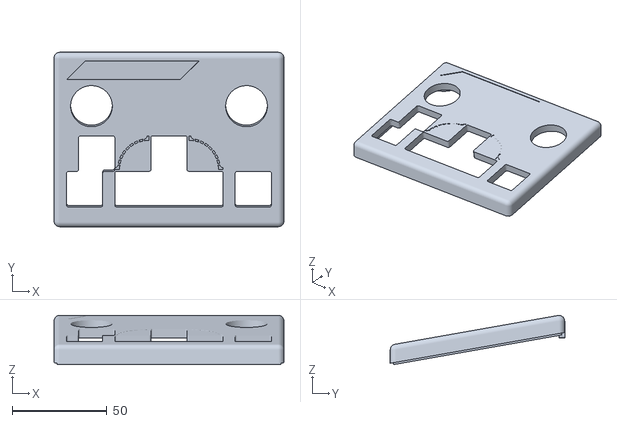
[picture p305: CAD file, 2023-04-02]
JoyKeyMX/Case/JoyKeyCase-Top.stl
121.3 x 92.0 x 25.9
