bleroy/3d-junkyard/Macropad/KeyChain/Enclosure/KeyChainEnclosure-Top.3mf

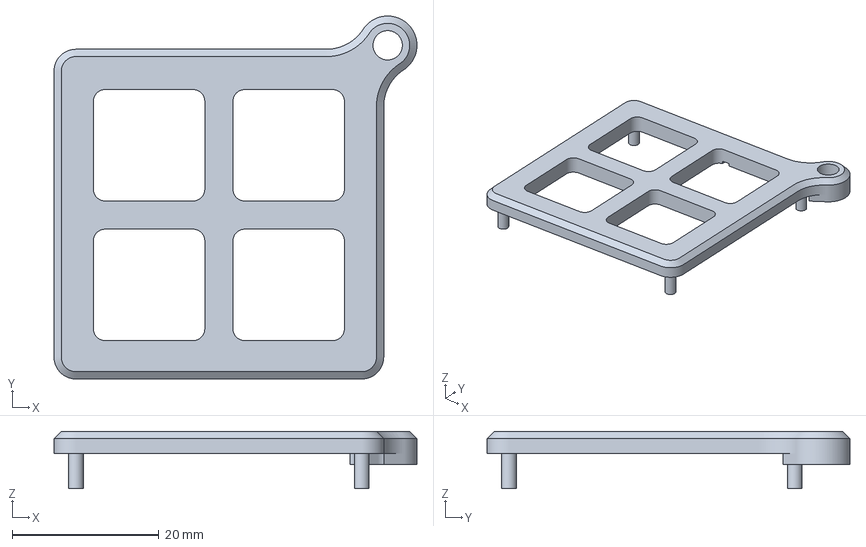
[picture p306: CAD file, 2026-08-10]
Macropad/KeyChain/Enclosure/KeyChainEnclosure-Top.3mf
49.5 x 49.5 x 7.84 mm
