bleroy/3d-junkyard/misc-models/Atari/ATARI 5200 Expansion port AV cover.FCStd

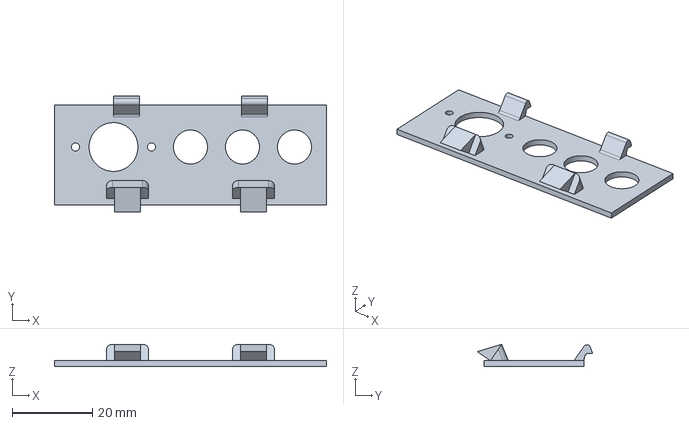
[picture p307: CAD file, 2025-01-10]
misc-models/Atari/ATARI 5200 Expansion port AV cover.FCStd
68.0 x 28.9 x 5.62 mm
