bleroy/3d-junkyard/misc-models/Cans/BoxLid.stl

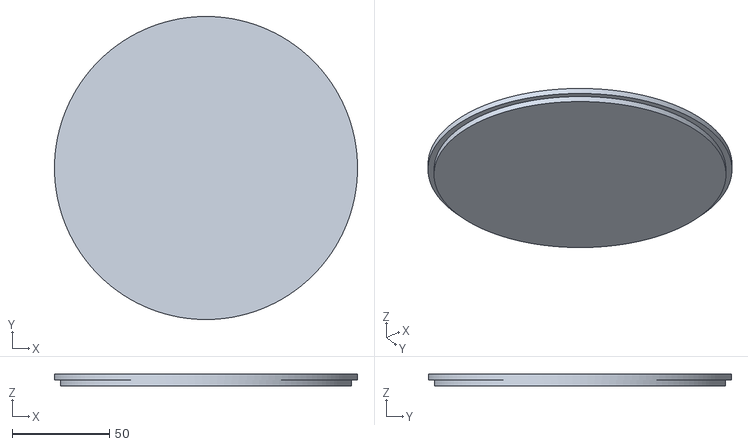
[picture p308: CAD file, 2025-05-28]
misc-models/Cans/BoxLid.stl
156.0 x 156.0 x 6.00
