bleroy/3d-junkyard/misc-models/Caps/LowPoly60PercentLayout.step

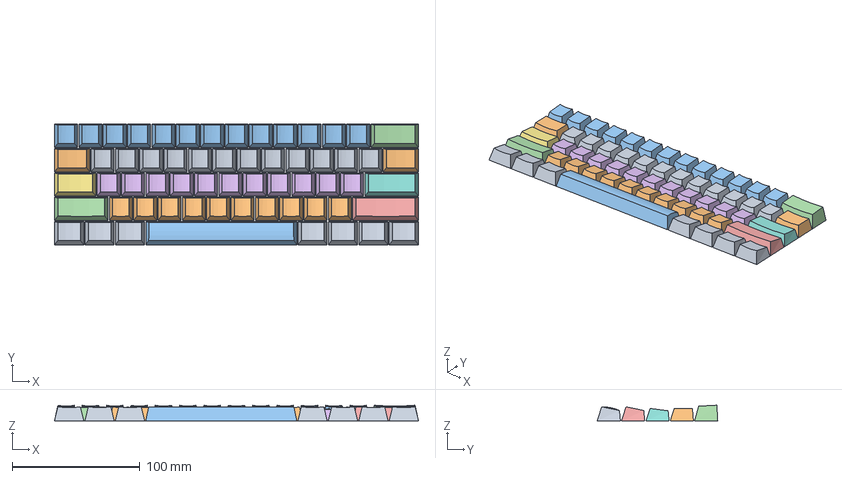
[picture p309: CAD file, 2026-08-10]
misc-models/Caps/LowPoly60PercentLayout.step
284.9 x 94.3 x 12.2 mm
OEM002
OEM004
OEM Space Bar
OEM005
OEM007
OEM009
OEM011
OEM013
OEM015
OEM017
OEM019
OEM021
OEM023
OEM025
