bleroy/3d-junkyard/misc-models/Cosplay/Arrietty's clip - springs.3mf

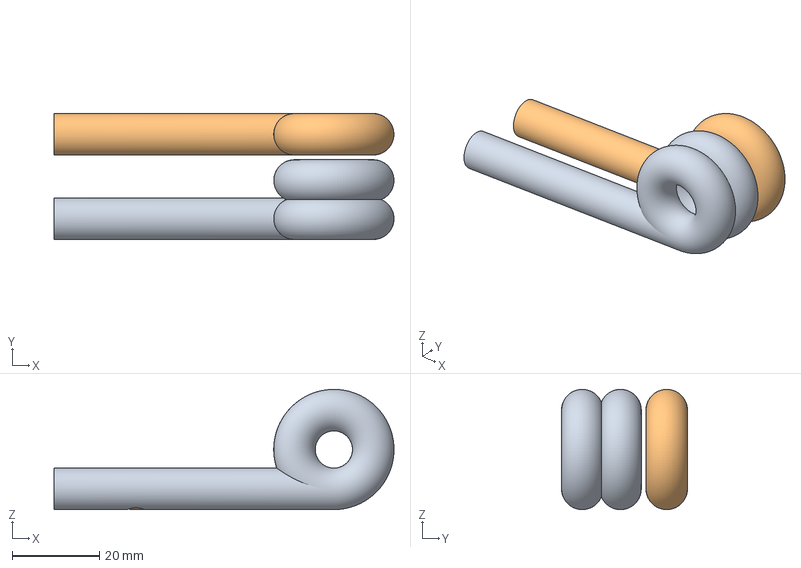
[picture p310: CAD file, 2025-02-17]
misc-models/Cosplay/Arrietty's clip - springs.3mf
77.8 x 28.8 x 27.5 mm
Arrietty's clip-Spring 1.stl
Arrietty's clip-Spring 2.stl
