bleroy/3d-junkyard/misc-models/Fessetoule/FesseTouleRails-SocketAndRailBody.stl

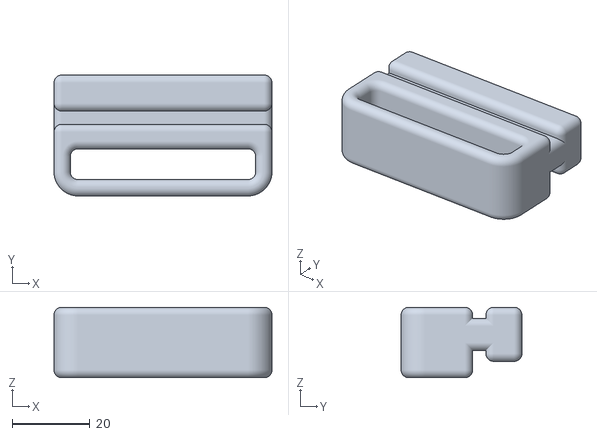
[picture p311: CAD file, 2024-09-04]
misc-models/Fessetoule/FesseTouleRails-SocketAndRailBody.stl
56.0 x 31.0 x 18.1
