bleroy/3d-junkyard/misc-models/Frames/Frame.FCStd

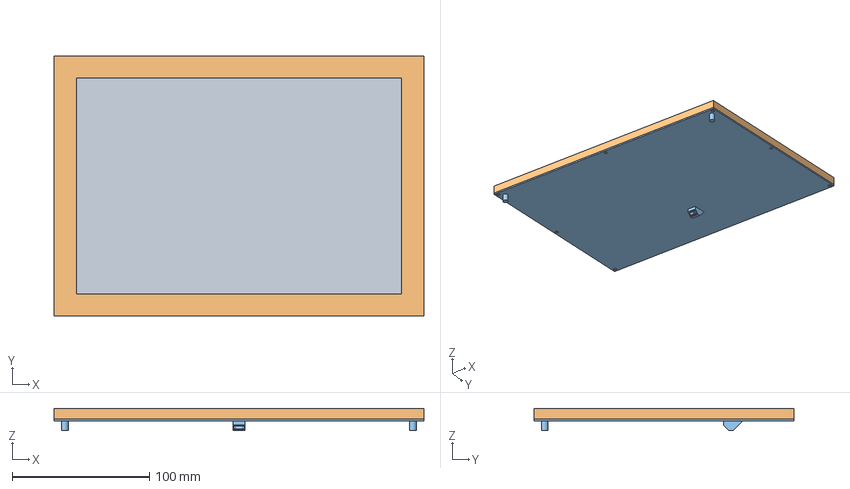
[picture p312: CAD file, 2026-04-19]
misc-models/Frames/Frame.FCStd
270.0 x 190.0 x 16.3 mm
Picture
Frame
Back
Plug
