bleroy/3d-junkyard/misc-models/Gridfinity/Gridfinity BenchtopPowerSupply tray.FCStd

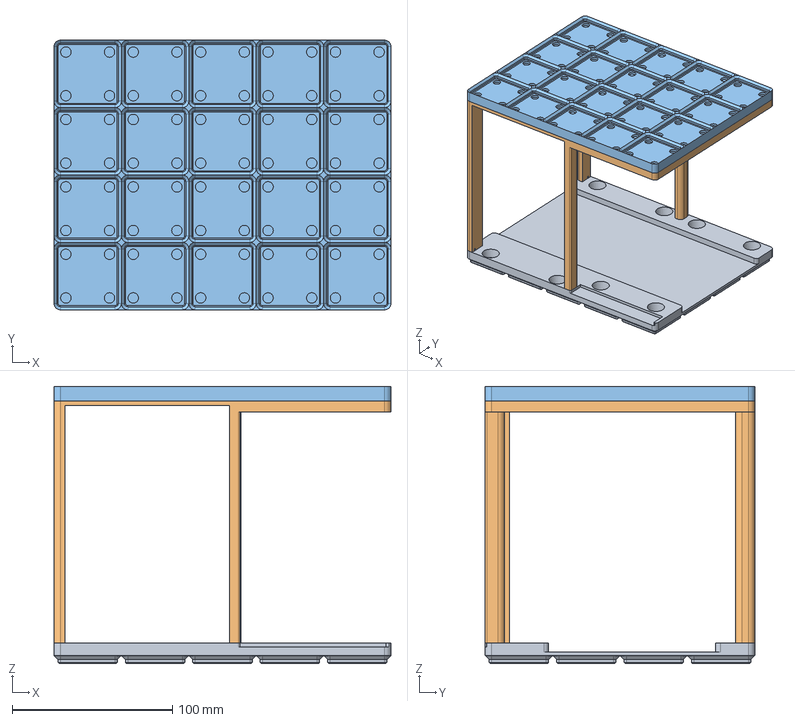
[picture p313: CAD file, 2026-08-10]
misc-models/Gridfinity/Gridfinity BenchtopPowerSupply tray.FCStd
210.0 x 168.0 x 172.7 mm
Bottom Tray
Platform
Top tray
