bleroy/3d-junkyard/misc-models/H2C/PoopChute.FCStd

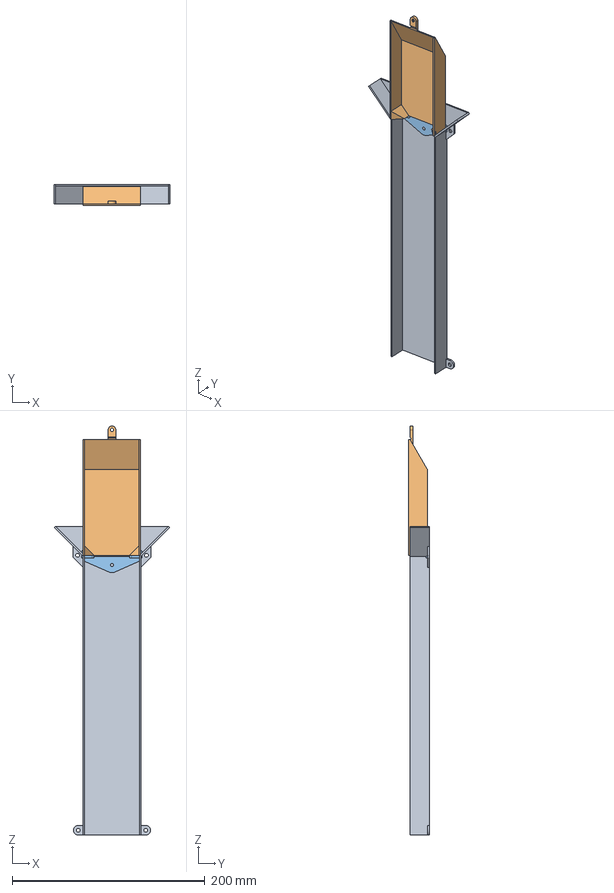
[picture p314: CAD file, 2026-04-19]
misc-models/H2C/PoopChute.FCStd
119.8 x 21.5 x 424.0 mm
Printer attachment
Bottom of window fastener
