bleroy/3d-junkyard/misc-models/Headphones/Sony MDR-V50 repair.FCStd

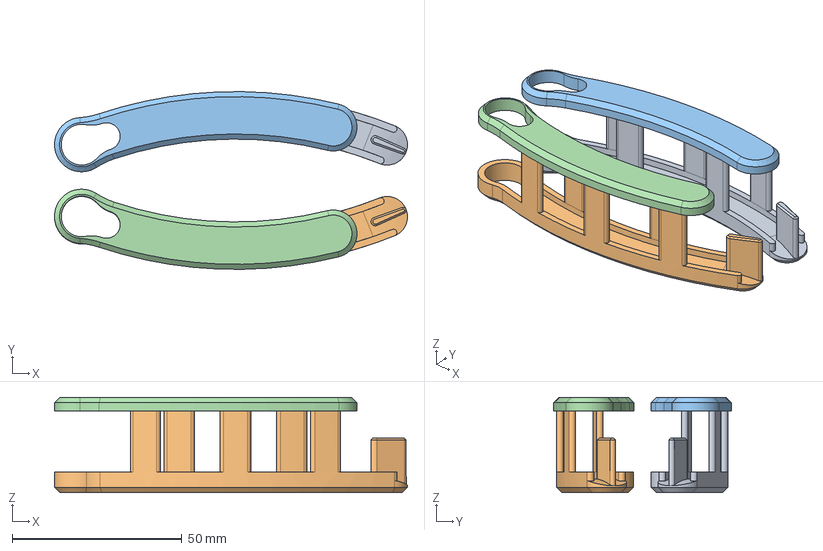
[picture p315: CAD file, 2026-08-10]
misc-models/Headphones/Sony MDR-V50 repair.FCStd
104.0 x 52.4 x 28.0 mm
Right
Left
Right cap
Left cap
