bleroy/3d-junkyard/misc-models/HexLattice/Printed/Single60AngleTop.3mf

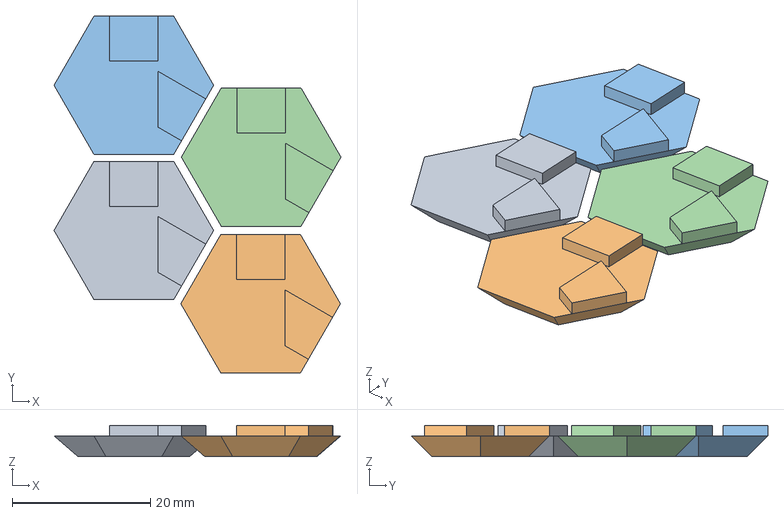
[picture p316: CAD file, 2024-09-04]
misc-models/HexLattice/Printed/Single60AngleTop.3mf
41.5 x 51.6 x 4.50 mm
Single60AngleTop.stl x 4
