bleroy/3d-junkyard/misc-models/HouseRepairs/Parametric Shelf Wall Anchor Spacer.FCStd

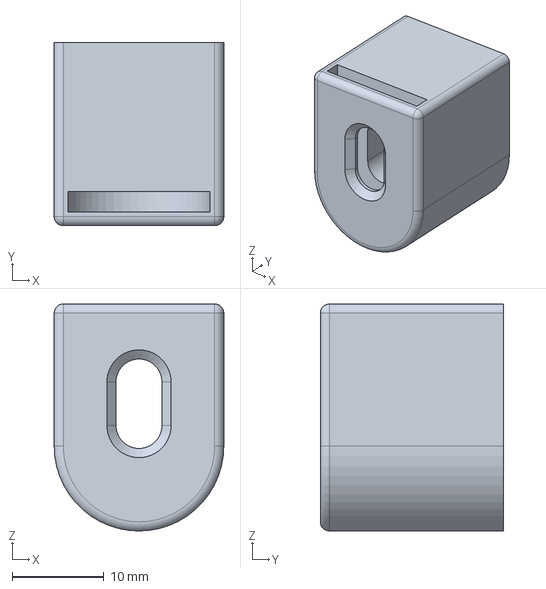
[picture p317: CAD file, 2026-10-01]
misc-models/HouseRepairs/Parametric Shelf Wall Anchor Spacer.FCStd
18.5 x 20.0 x 24.8 mm
