bleroy/3d-junkyard/misc-models/KeyboardTester/Enclosure/Decent Retro Keyboard Tester Enclosure-Top.3mf

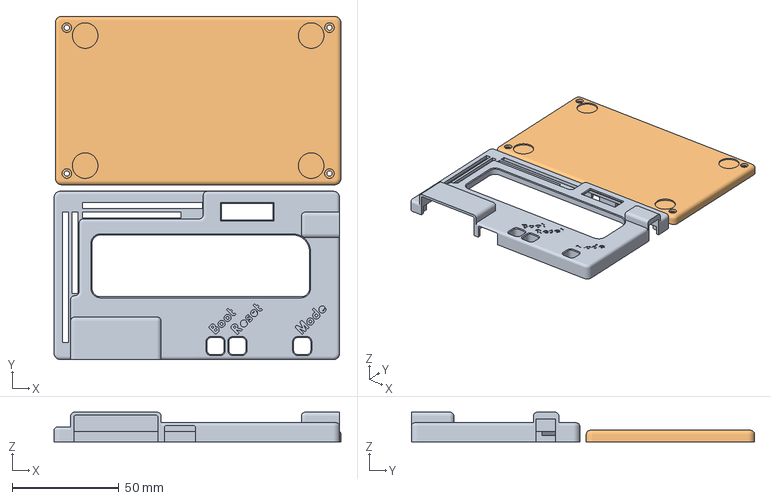
[picture p318: CAD file, 2025-03-02]
misc-models/KeyboardTester/Enclosure/Decent Retro Keyboard Tester Enclosure-Top.3mf
134.6 x 161.0 x 14.0 mm
Decent Retro Keyboard Tester Enclosure-Top.stl
Decent Retro Keyboard Tester Enclosure-Bottom.stl
