bleroy/3d-junkyard/misc-models/KeyboardTester/shapes3D/BM3B-SRSS-TB.step

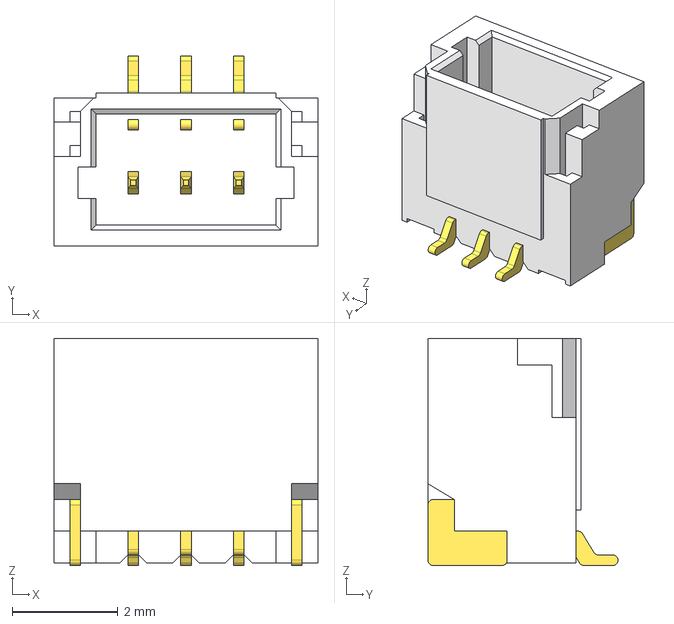
[picture p319: CAD file, 2025-03-02]
misc-models/KeyboardTester/shapes3D/BM3B-SRSS-TB.step
5.00 x 3.60 x 4.30 mm
