bleroy/3d-junkyard/misc-models/Kobra Max/FilamentSpoolExtendedBallBearingPin.FCStd

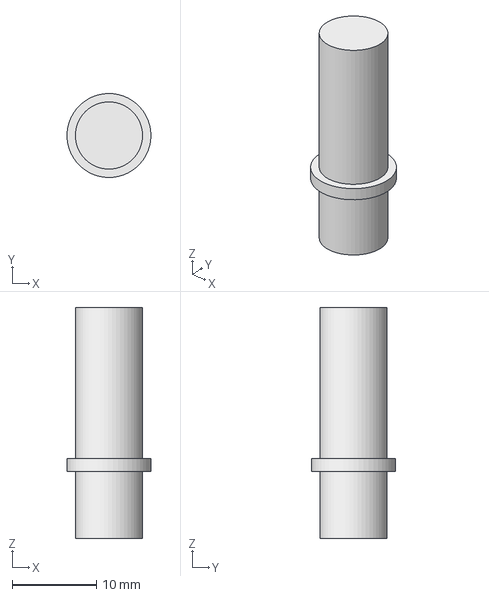
[picture p320: CAD file, 2023-07-05]
misc-models/Kobra Max/FilamentSpoolExtendedBallBearingPin.FCStd
9.99 x 10.00 x 27.5 mm
