bleroy/3d-junkyard/misc-models/Lab/phone-dock.stl

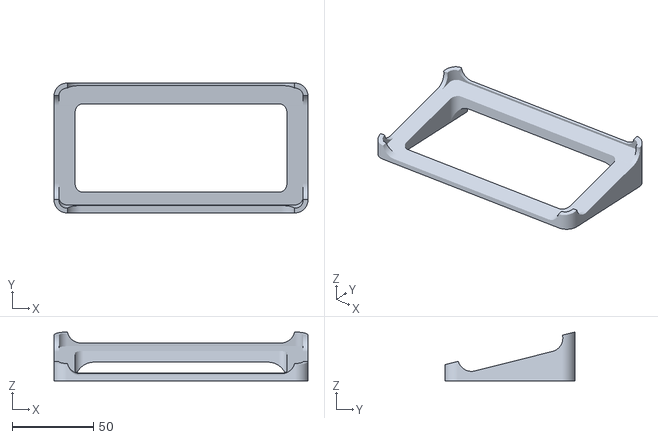
[picture p321: CAD file, 2023-04-02]
misc-models/Lab/phone-dock.stl
156.0 x 79.7 x 30.0
