bleroy/3d-junkyard/misc-models/Measuring/KeyboardUnitRuler-9U.3mf

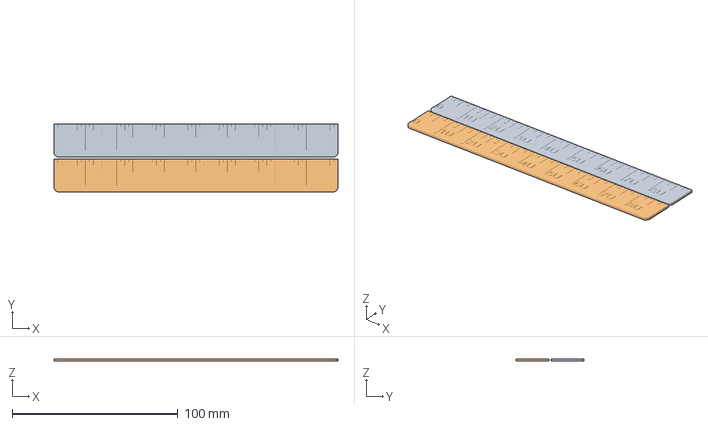
[picture p322: CAD file, 2026-08-10]
misc-models/Measuring/KeyboardUnitRuler-9U.3mf
171.4 x 41.0 x 1.50 mm
