bleroy/3d-junkyard/misc-models/MicroscopeArm.FCStd

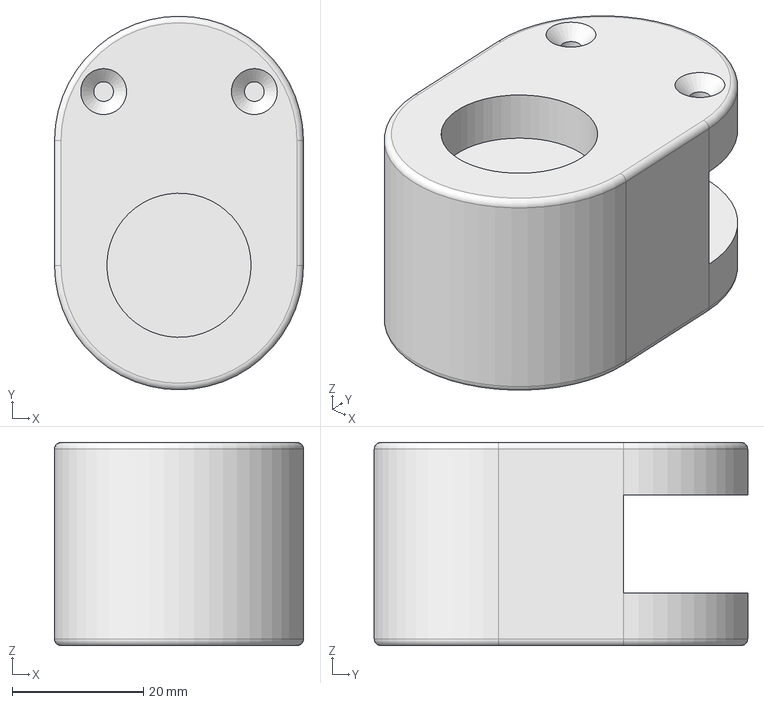
[picture p323: CAD file, 2023-10-16]
misc-models/MicroscopeArm.FCStd
38.0 x 57.0 x 31.0 mm
