bleroy/3d-junkyard/misc-models/Minishelves/ActionFigureBracket-Usopp.3mf

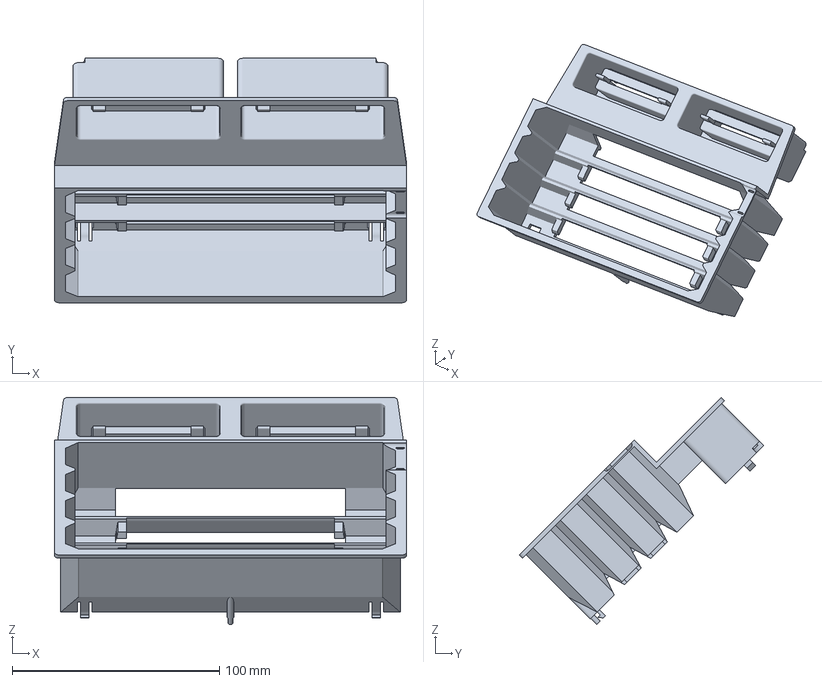
[picture p324: CAD file, 2024-10-24]
misc-models/Minishelves/ActionFigureBracket-Usopp.3mf
170.0 x 118.1 x 109.6 mm
