bleroy/3d-junkyard/misc-models/Music/LedGuitarStrap/printed/GuitarStrapControllerEnclosure.FCStd

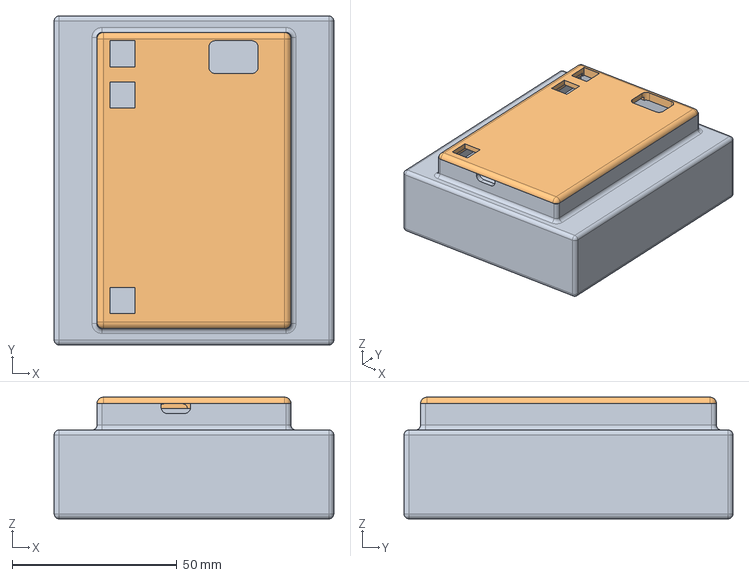
[picture p325: CAD file, 2025-01-10]
misc-models/Music/LedGuitarStrap/printed/GuitarStrapControllerEnclosure.FCStd
85.0 x 100.0 x 37.0 mm
Bottom
Top
