bleroy/3d-junkyard/misc-models/Music/Mediator box.FCStd

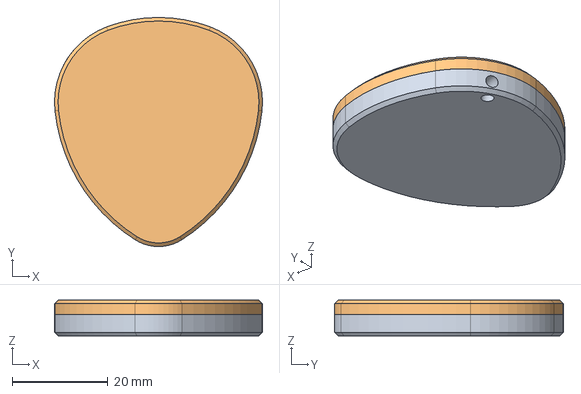
[picture p326: CAD file, 2026-03-14]
misc-models/Music/Mediator box.FCStd
43.4 x 47.8 x 7.50 mm
Bottom
Top
