bleroy/3d-junkyard/misc-models/NanoPC/keyboard/NanoKeyboard-Base.3mf

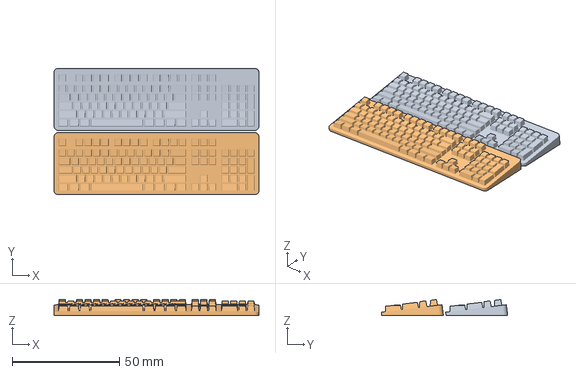
[picture p327: CAD file, 2025-03-02]
misc-models/NanoPC/keyboard/NanoKeyboard-Base.3mf
95.6 x 59.0 x 7.51 mm
NanoKeyboard-Base x 2
