bleroy/3d-junkyard/misc-models/OrientableSupport/OrientableSupport-Support.3mf

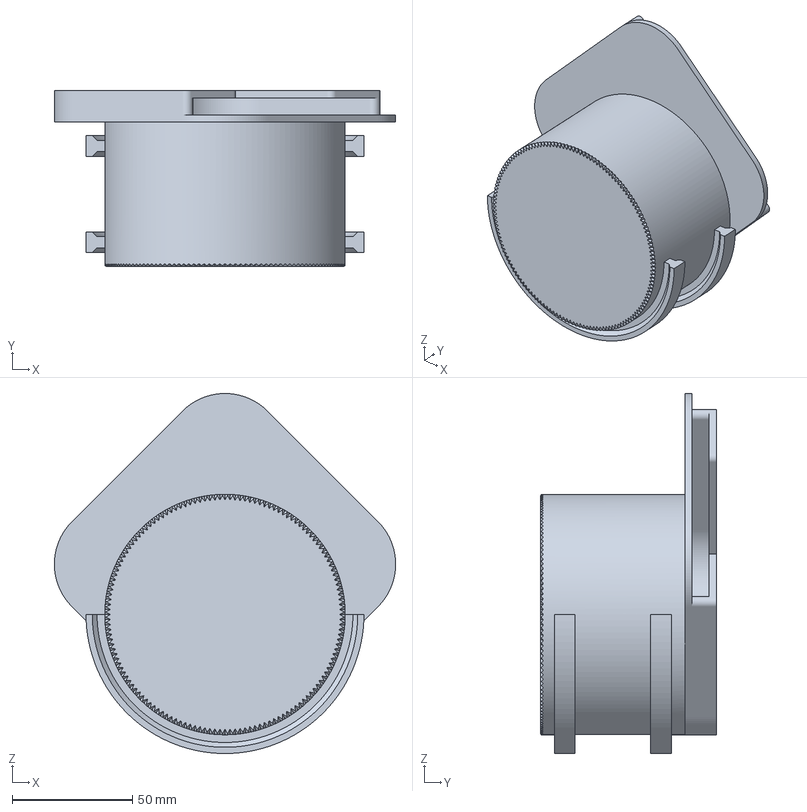
[picture p328: CAD file, 2026-08-10]
misc-models/OrientableSupport/OrientableSupport-Support.3mf
141.9 x 73.0 x 149.7 mm
