bleroy/3d-junkyard/misc-models/PedalRack/PedalRack-LeftPart.3mf

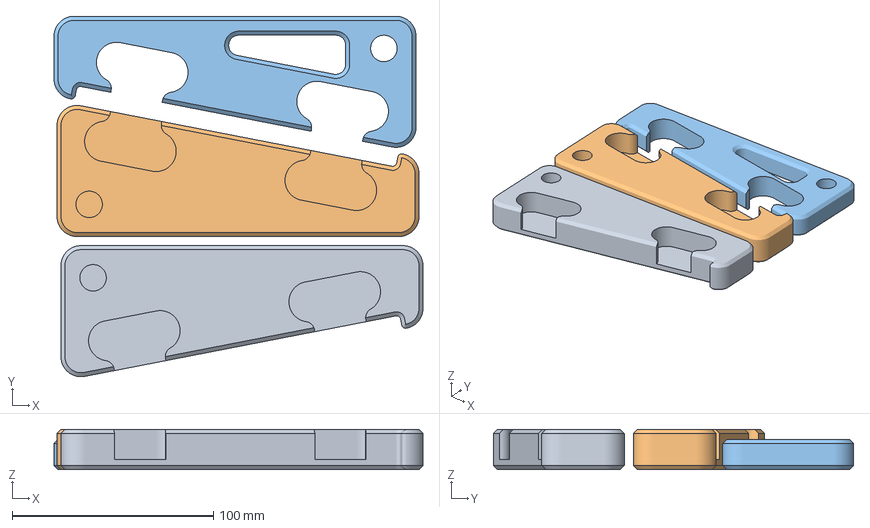
[picture p329: CAD file, 2024-09-04]
misc-models/PedalRack/PedalRack-LeftPart.3mf
183.4 x 179.2 x 20.0 mm
PedalRack-LeftPart.stl
PedalRack-RightPart.stl
PedalRack-MiddlePart.stl
