bleroy/3d-junkyard/misc-models/Skadis/BetweenTheBeams-Part3.3mf

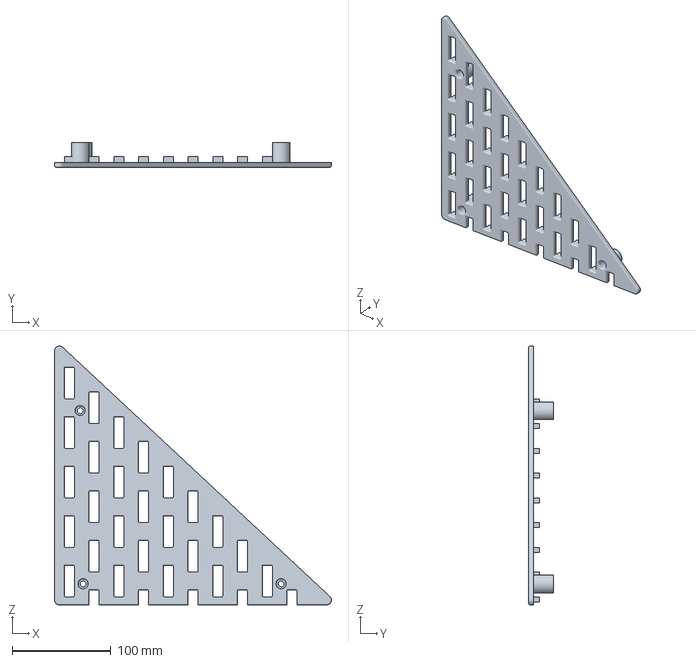
[picture p330: CAD file, 2026-08-10]
misc-models/Skadis/BetweenTheBeams-Part3.3mf
279.9 x 24.9 x 261.6 mm
