bleroy/3d-junkyard/SidecarXE85/Case/SidecarXE85-case-Bottom.stl

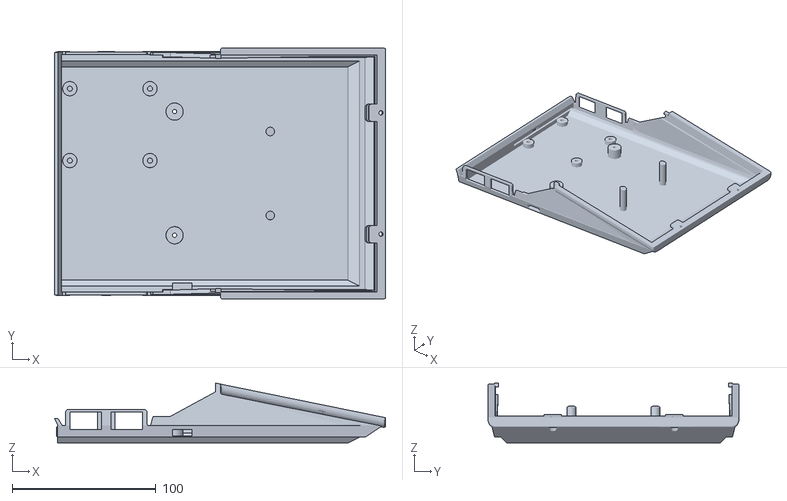
[picture p331: CAD file, 2023-07-08]
SidecarXE85/Case/SidecarXE85-case-Bottom.stl
230.2 x 174.4 x 41.7
