bleroy/3d-junkyard/Atari130MX/Caps/fn-console-set-choc.stl

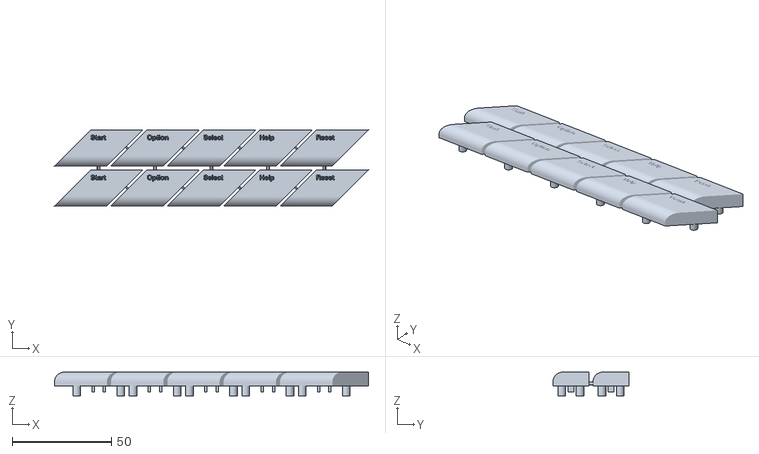
[picture p332: CAD file, 2023-06-15]
Atari130MX/Caps/fn-console-set-choc.stl
158.2 x 38.3 x 12.0
