bleroy/3d-junkyard/Atari130MX/Stems/kailh-choc-to-xl-cross-set-25.stl

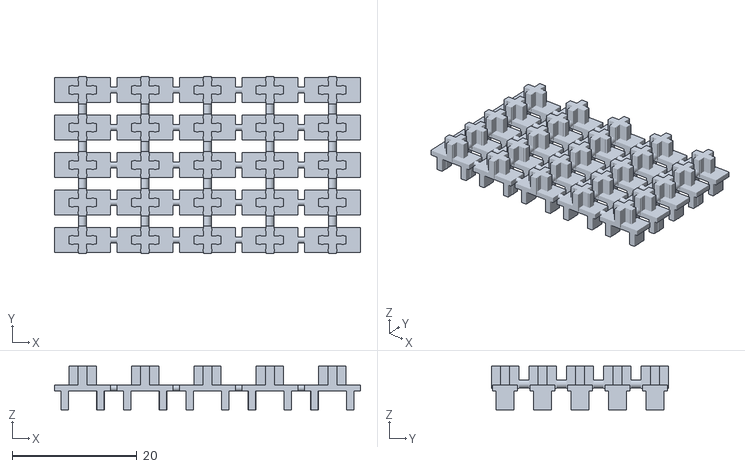
[picture p333: CAD file, 2023-09-24]
Atari130MX/Stems/kailh-choc-to-xl-cross-set-25.stl
49.0 x 28.4 x 7.00
