bleroy/3d-junkyard/Decent1200/Adapters/ConsoleKeyAdapter1200.stl

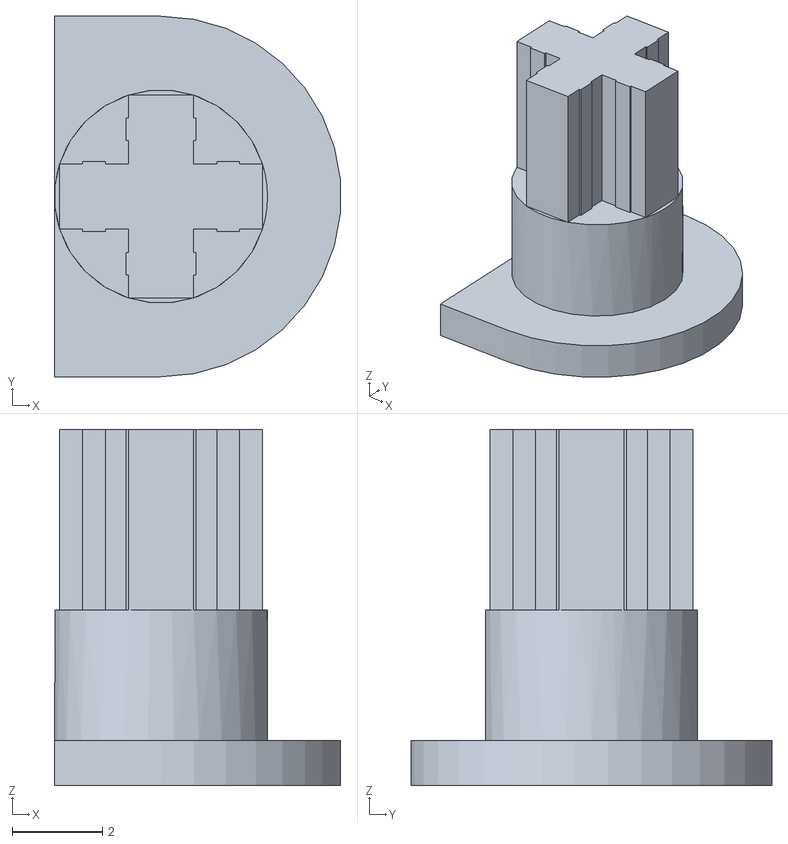
[picture p334: CAD file, 2024-01-14]
Decent1200/Adapters/ConsoleKeyAdapter1200.stl
6.35 x 8.00 x 7.90
