bleroy/3d-junkyard/Decent1200/Caps/Decent1200-console-choc-x10.stl

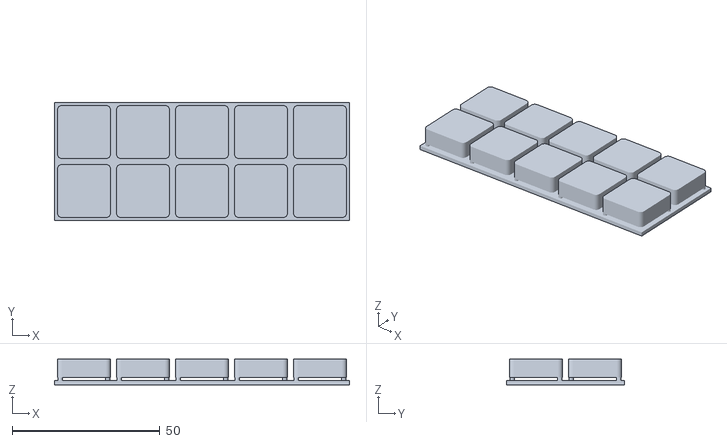
[picture p335: CAD file, 2024-04-16]
Decent1200/Caps/Decent1200-console-choc-x10.stl
100.0 x 40.0 x 8.65
