bleroy/3d-junkyard/Decent1200/PrintedParts/TestWedge.FCStd

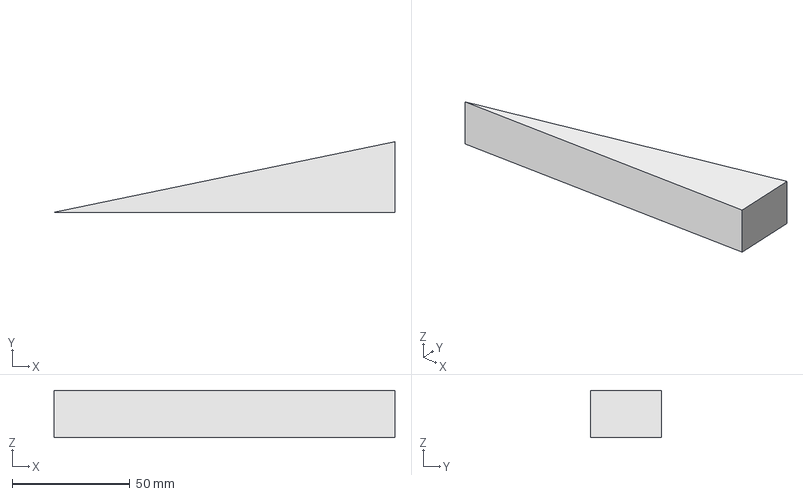
[picture p336: CAD file, 2024-01-14]
Decent1200/PrintedParts/TestWedge.FCStd
144.9 x 30.0 x 20.0 mm
