bleroy/3d-junkyard/Decent400/Misc/Single cap holder 1U.3mf

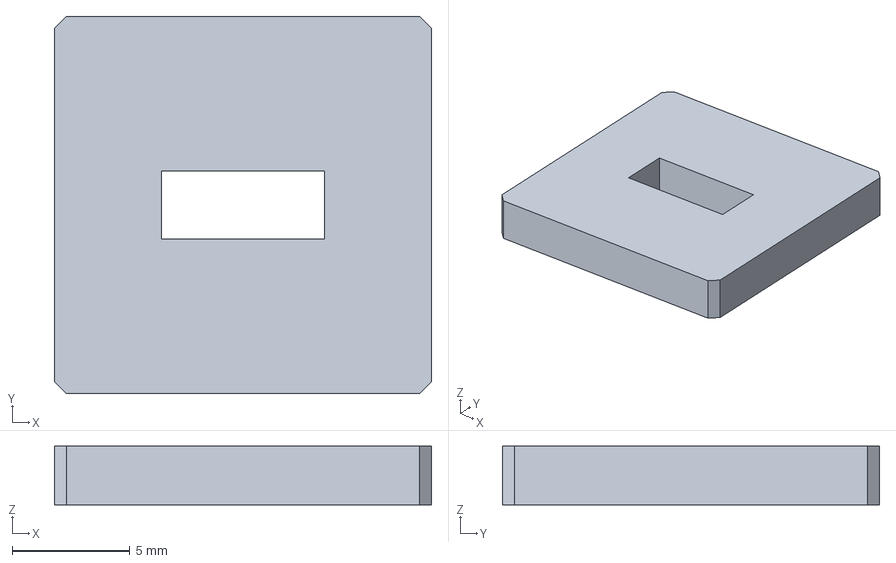
[picture p337: CAD file, 2026-03-22]
Decent400/Misc/Single cap holder 1U.3mf
16.0 x 16.0 x 2.50 mm
