bleroy/3d-junkyard/DecentCart/3DModels/DecentCart5200.step

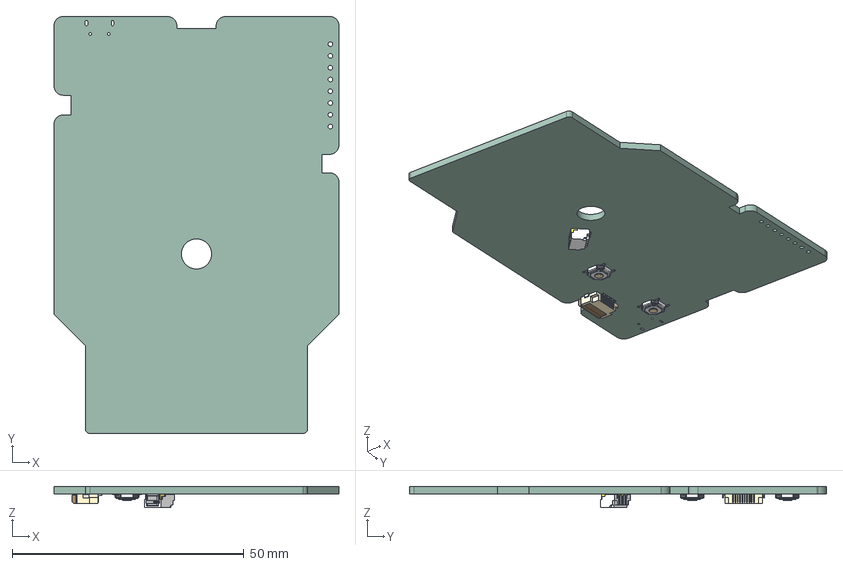
[picture p338: CAD file, 2025-01-26]
DecentCart/3DModels/DecentCart5200.step
61.5 x 90.0 x 4.55 mm
TS-1187A v2 x 2
Hirose_FH12_xxS_0_5SH_Parametric_v0_1
SMxB-SRSS-TB
DecentCart5200_PCB
