bleroy/3d-junkyard/DecentCart/Enclosure/DecentCart2350-RightCover.stl

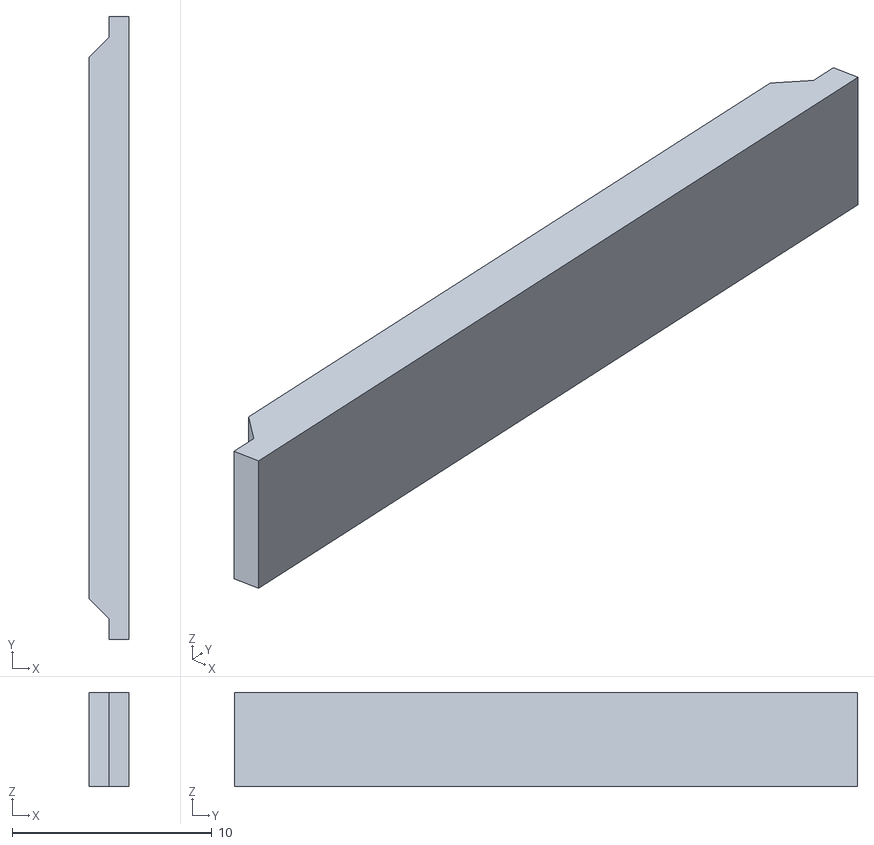
[picture p339: CAD file, 2025-10-22]
DecentCart/Enclosure/DecentCart2350-RightCover.stl
1.99 x 31.2 x 4.71
