bleroy/3d-junkyard/DecenTKL/Enclosure/DecenTKL-top.stl

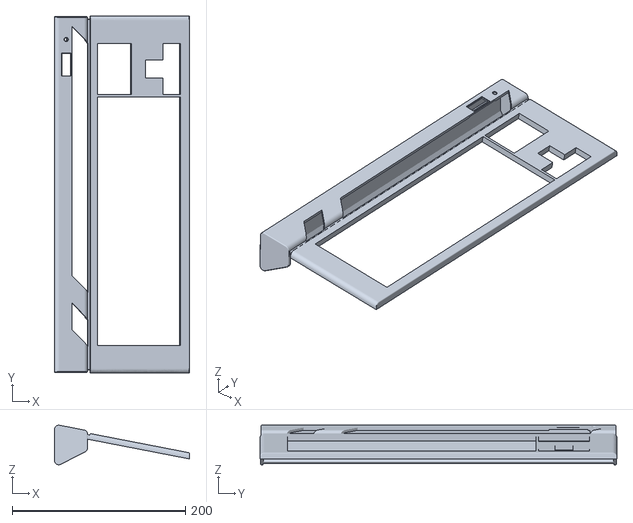
[picture p340: CAD file, 2024-11-11]
DecenTKL/Enclosure/DecenTKL-top.stl
156.0 x 412.2 x 45.8
