bleroy/3d-junkyard/DecenTKL/NumPadEnclosure/DecenTKL-Numpad-Enclosure.3mf

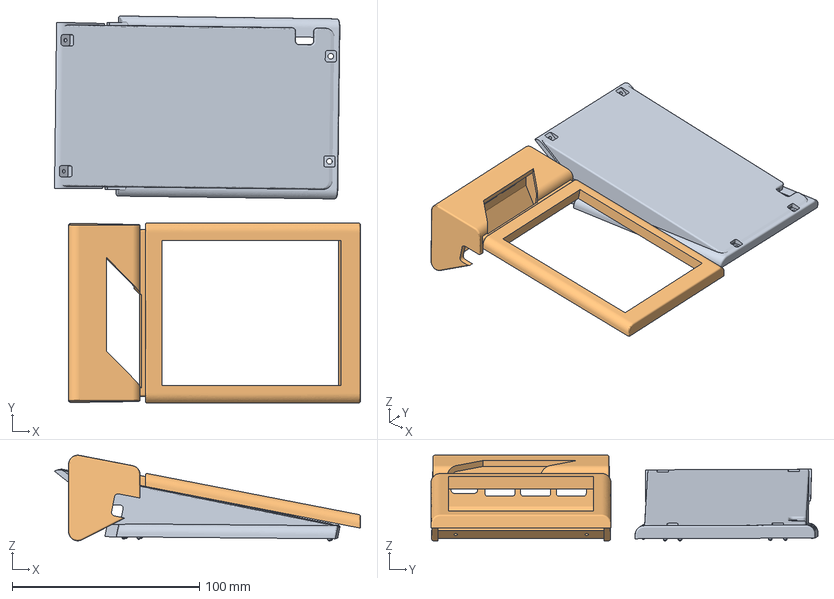
[picture p341: CAD file, 2024-08-24]
DecenTKL/NumPadEnclosure/DecenTKL-Numpad-Enclosure.3mf
163.5 x 206.7 x 45.8 mm
DecenTKL-Numpad-Enclosure-Bottom.stl
DecenTKL-Numpad-Enclosure-Top.stl
