bleroy/3d-junkyard/DecentXE/Misc/XE-rev-before-16-depth-padding.FCStd

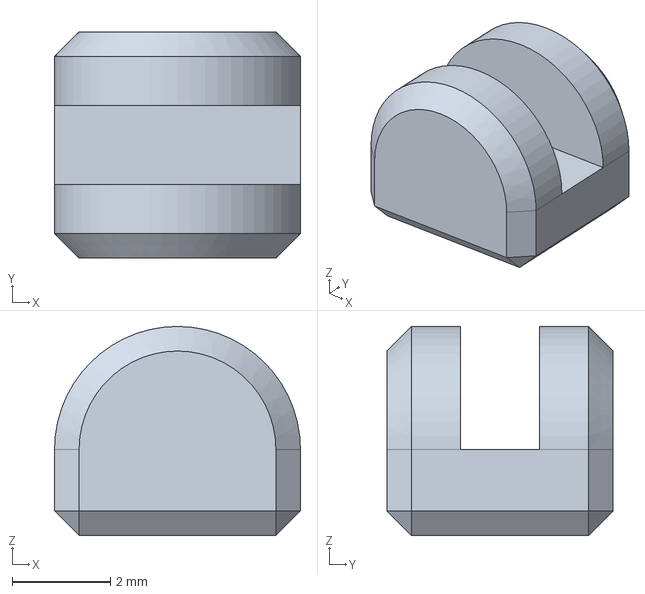
[picture p342: CAD file, 2026-02-04]
DecentXE/Misc/XE-rev-before-16-depth-padding.FCStd
5.00 x 4.60 x 4.25 mm
