bleroy/3d-junkyard/DecentXE/Stabilizers/LowProPlate.FCStd

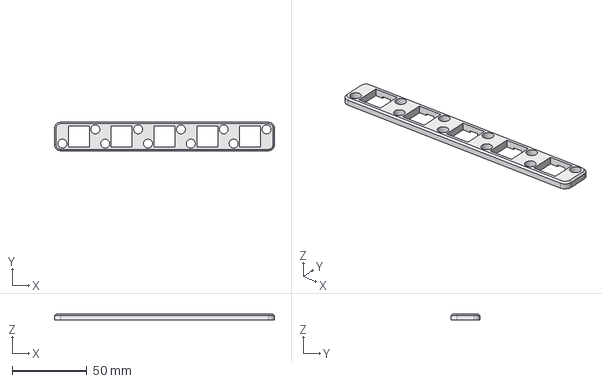
[picture p343: CAD file, 2024-07-21]
DecentXE/Stabilizers/LowProPlate.FCStd
146.9 x 19.1 x 3.95 mm
