bleroy/3d-junkyard/DecentXL/Adapters/DurockInsert.FCStd

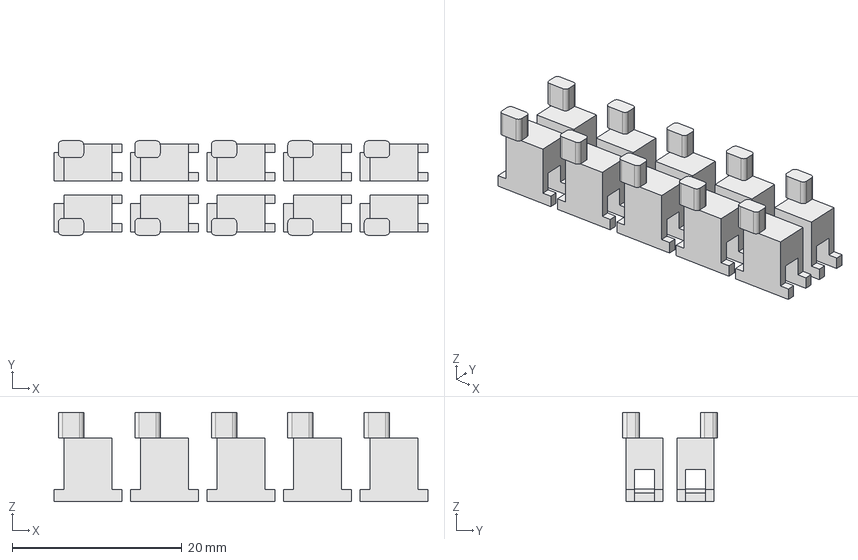
[picture p344: CAD file, 2024-07-21]
DecentXL/Adapters/DurockInsert.FCStd
44.0 x 11.1 x 10.5 mm
