bleroy/3d-junkyard/Decent400/Caps/Decent400-EufyMake-Relief-Layer.png

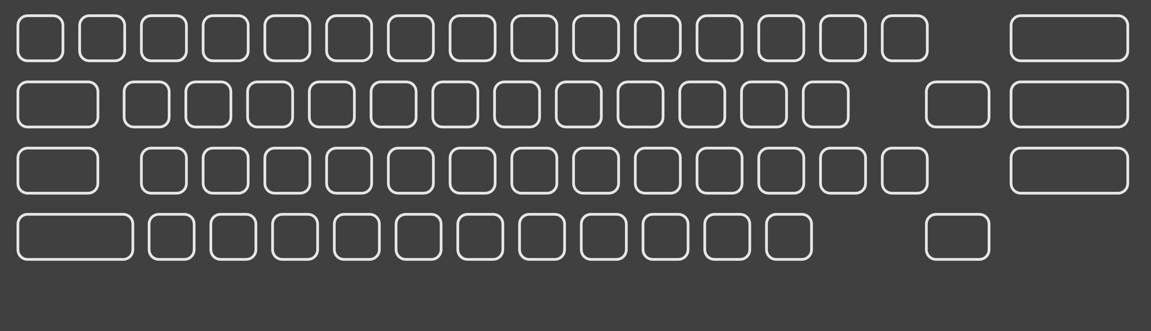
Decent400/Caps/Decent400-EufyMake-Relief-Layer.png
