bleroy/3d-junkyard/Decent400/Caps/Decent_Atari_400_REAL400_Black_MakerPreview.png

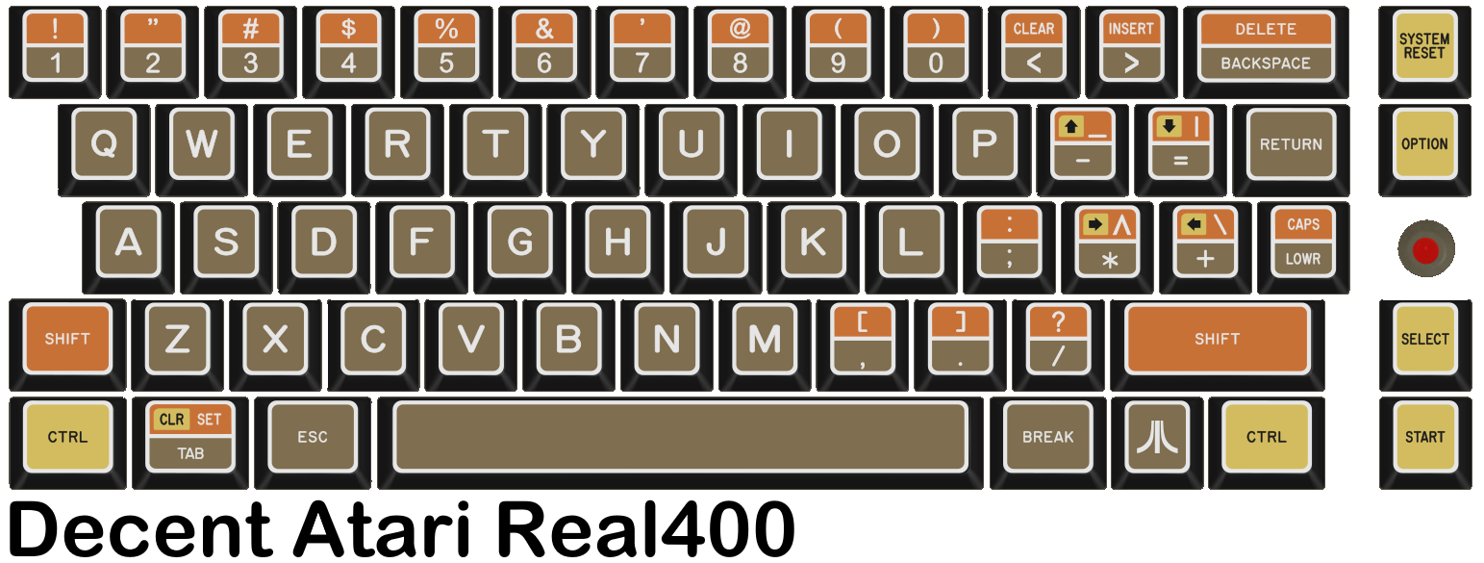
Decent400/Caps/Decent_Atari_400_REAL400_Black_MakerPreview.png
