bleroy/3d-junkyard/JoyKeyMX/AtariJoystickPaddleTester/AtariJoystickPaddleTester_Back.png

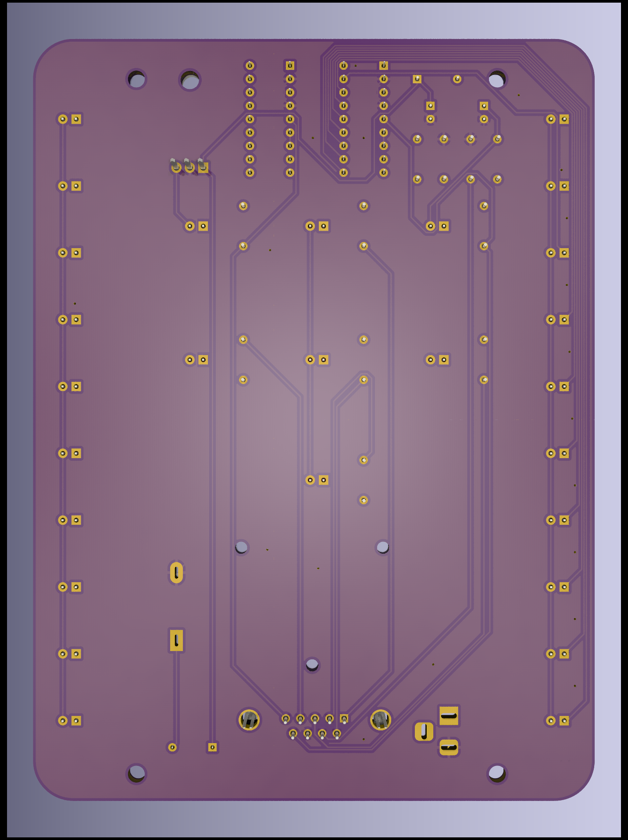
JoyKeyMX/AtariJoystickPaddleTester/AtariJoystickPaddleTester_Back.png
