bleroy/3d-junkyard/JoyKeyMX/AtariJoystickPaddleTester/AtariJoystickPaddleTester_Front.png

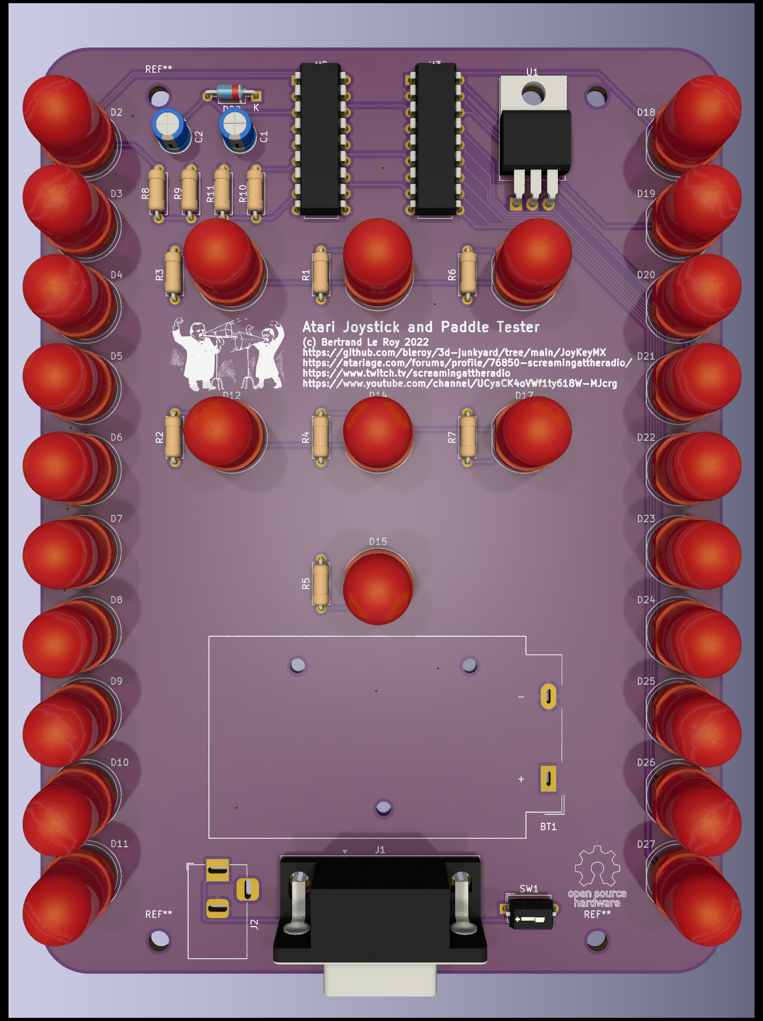
JoyKeyMX/AtariJoystickPaddleTester/AtariJoystickPaddleTester_Front.png
