bleroy/3d-junkyard/misc-models/KeyboardTester/v1/AtariKeyboardTester.png

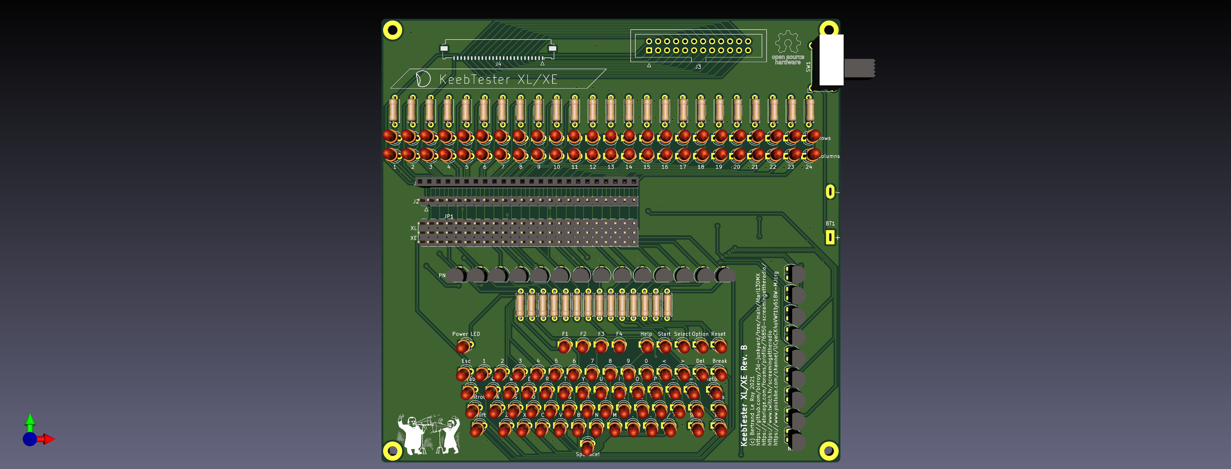
misc-models/KeyboardTester/v1/AtariKeyboardTester.png
