bleroy/3d-junkyard/DecentUSB/DecentUSB2350/DecentUSB2350.kicad_pcb

## KiCad design DecentUSB/DecentUSB2350/DecentUSB2350.kicad_pcb (2025-08-22)

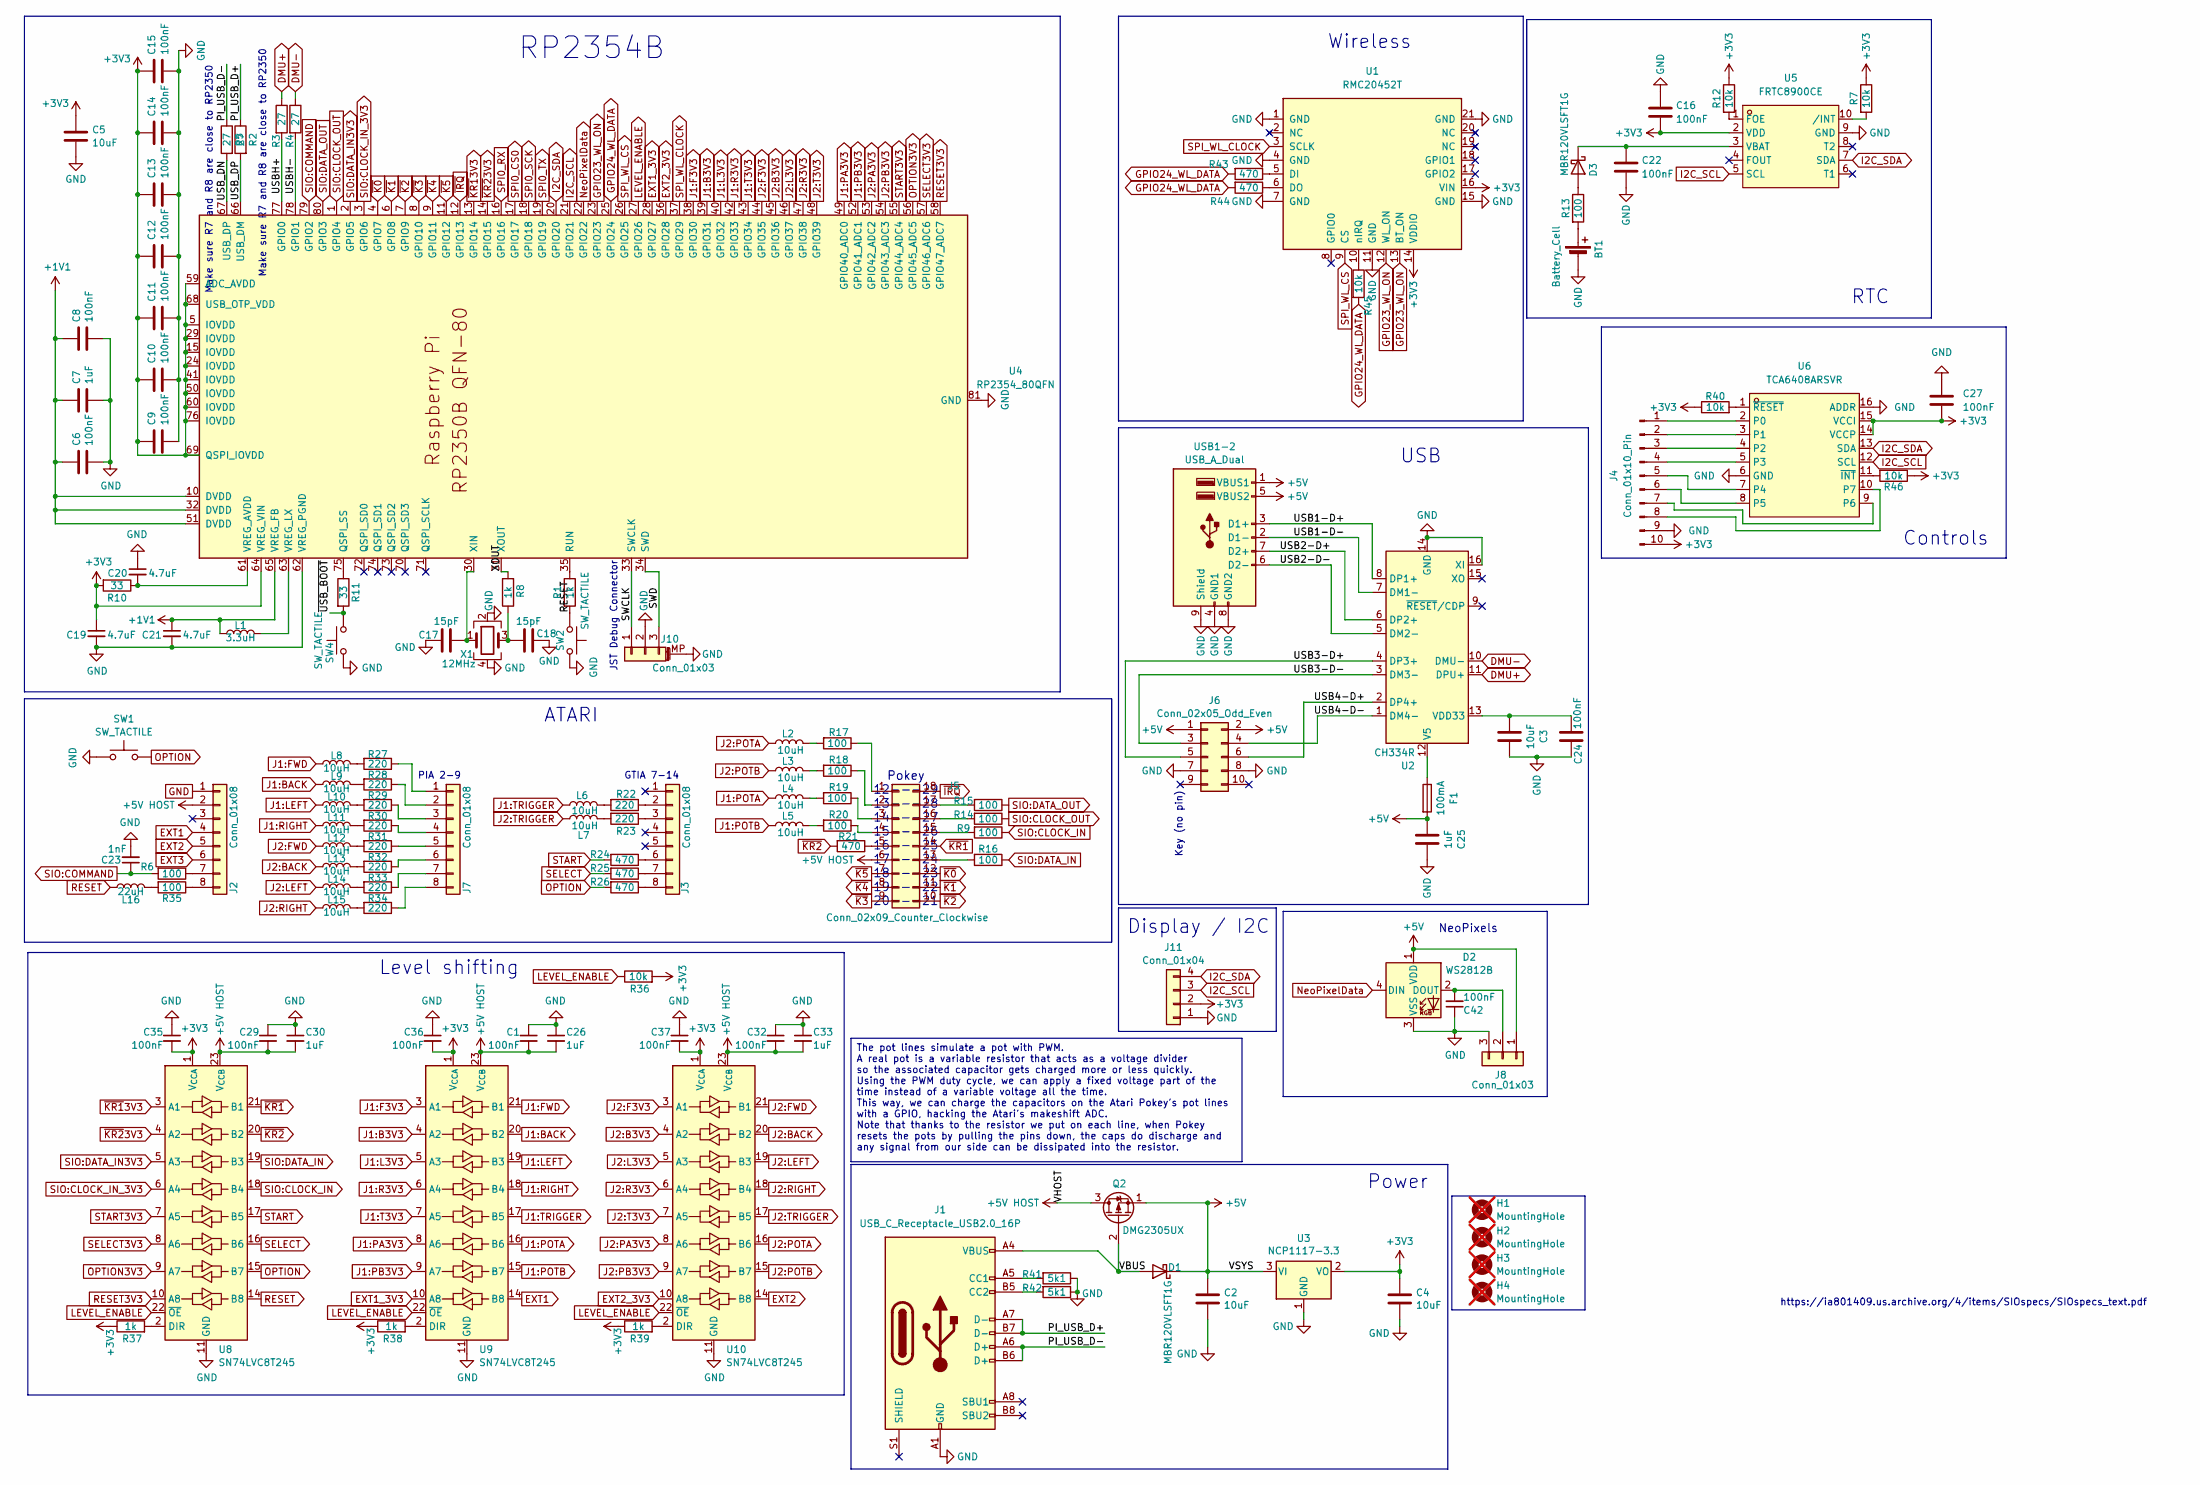
[picture p377: schematic DecentUSB2350.kicad_sch]

Parts:
BT1: Battery_Cell; BAT-SMD_BS-CR2032-8; JLCPCB Part # C7498149
C1, C6, C8, C9, C10, C11, C12, C13, C14, C15, C16, C22, C24, C27, C29, C32, C35, C36, C37, C42: 100nF; C_0402_1005Metric; JLCPCB Part # C1525
C2, C3, C4, C5: 10uF; C_0402_1005Metric; JLCPCB Part # C15525
C7, C25, C26, C30, C33: 1uF; C_0402_1005Metric; JLCPCB Part # C52923
C17, C18: 15pF; C_0402_1005Metric; JLCPCB Part # C1548
C19, C20, C21: 4.7uF; C_0402_1005Metric; JLCPCB Part # C23733
C23: 1nF; C_0402_1005Metric; JLCPCB Part # C1523
D1, D3: MBR120VLSFT1G; Nexperia_CFP3_SOD-123W; JLCPCB Part # C223608
D2: WS2812B; LED-SMD_4P-L2.7-W2.4-TL_WS2812C-2427; JLCPCB Part # C4154872
F1: 100mA; Fuse_1206_3216Metric; JLCPCB Part # C269108
H1, H2, H3, H4: MountingHole; MountingHole_2.2mm_M2; not fitted
J1: USB_C_Receptacle_USB2.0_16P; USB-C-SMD_TYPE-C-6PIN-2MD-073; JLCPCB Part # C2765186
J2, J3, J7: Conn_01x08; PinHeader_1x08_P2.54mm_Vertical
J4: Conn_01x10_Pin; PinHeader_1x10_P2.54mm_Vertical
J5: Conn_02x09_Counter_Clockwise; PinHeader_2x09_P2.54mm_Vertical
J6: Conn_02x05_Odd_Even; PinHeader_2x05_P2.54mm_Vertical
J8, J10: Conn_01x03; CONN-SMD-3P-P1.00_BM03B-SRSS-TB-LF-SN; JLCPCB Part # C160389
J11: Conn_01x04; PinHeader_1x04_P2.54mm_Vertical
L1: 3.3uH; L_0402_1005Metric; JLCPCB Part # C84474
L2, L3, L4, L5, L6, L7, L8, L9, L10, L11, L12, L13, L14, L15: 10uH; L_0603_1608Metric; JLCPCB Part # C1035
L16: 22uH; L_0603_1608Metric; JLCPCB Part # C361669
Q2: DMG2305UX; SOT-23; JLCPCB Part # C150470
R1, R8, R37, R38, R39: 1k; R_0402_1005Metric; JLCPCB Part # C11702
R2, R3, R4, R5: 27; R_0402_1005Metric; JLCPCB Part # C25100
R6, R9, R13, R14, R15, R16, R17, R18, R19, R20, R35: 100; R_0402_1005Metric; JLCPCB Part # C25076
R7, R12, R36, R40, R45, R46: 10k; R_0402_1005Metric; JLCPCB Part # C25744
R10, R11: 33; R_0402_1005Metric; JLCPCB Part # C25105
R21, R24, R25, R26, R43, R44: 470; R_0402_1005Metric; JLCPCB Part # C25117
R22, R23, R27, R28, R29, R30, R31, R32, R33, R34: 220; R_0402_1005Metric; JLCPCB Part # C25091
R41, R42: 5k1; R_0402_1005Metric; JLCPCB Part # C25905
SW1, SW2, SW4: SW_TACTILE; SW-SMD_L3.9-W3.0-P4.45; JLCPCB Part # C720477
U1: RMC20452T; rpi_rmc20452t; JLCPCB Part # C49451547
U2: CH334R; QSOP-16_L4.9-W3.9-P0.64-LS6.0-BL; JLCPCB Part # C4154405
U3: NCP1117-3.3; SOT-223-3_TabPin2; JLCPCB Part # C6186
U4: RP2354_80QFN; QFN-80_L10.0-W10.0-P0.40-TL-EP3.4; JLCPCB Part # C39843328
U5: FRTC8900CE; SMD-10_L3.2-W2.5-P0.70-BL_DAPU_INS5699S; LCSC Part C42413387
U6: TCA6408ARSVR; UQFN-16_L2.6-W1.8-P0.40-BL; LCSC Part C2649390
U8, U9, U10: SN74LVC8T245; TSSOP-24_4.4x7.8mm_P0.65mm; JLCPCB Part # C27643
USB1-2: USB_A_Dual; USB_A_CUI_UJ2-ADH-TH_Horizontal_Stacked
X1: 12MHz; CRYSTAL-SMD_4P-L3.2-W2.5-BL; JLCPCB Part # C20625731

Connections:
+1V1: C6.1, C7.1, C8.1, C21.1, L1.1, U4.10 (DVDD), U4.32 (DVDD), U4.51 (DVDD), U4.65 (VREG_FB)
+3V3: C4.1, C5.1, C9.1, C10.1, C11.1, C12.1, C13.1, C14.1, C15.1, C16.1, C19.1, C27.1, C35.2, C36.2, C37.2, J4.10, J11.2, R7.1, R10.2, R12.1, R36.2, R37.1, R38.1, R39.1, R40.1, R46.1, U1.14 (VDDIO), U1.16 (VIN), U3.2 (VO), U4.5 (IOVDD), U4.15 (IOVDD), U4.24 (IOVDD), U4.29 (IOVDD), U4.41 (IOVDD), U4.50 (IOVDD), U4.59 (ADC_AVDD), U4.60 (IOVDD), U4.64 (VREG_VIN), U4.68 (USB_OTP_VDD), U4.69 (QSPI_IOVDD), U4.76 (IOVDD), U5.2 (VDD), U6.14 (VCCP), U6.15 (VCCI), U8.1 (V_{CCA}), U9.1 (V_{CCA}), U10.1 (V_{CCA})
+5V: C2.1, C25.1, D1.1 (K), D2.1 (VDD), F1.2, J6.1, J6.2, J8.1, Q2.1 (S), U3.3 (VI), USB1-2.1 (VBUS1), USB1-2.5 (VBUS2)
+5V HOST: C1.2, C26.2, C29.2, C30.2, C32.2, C33.2, J2.2, J5.6, Q2.3 (D), U8.23 (V_{CCB}), U8.24 (V_{CCB}), U9.23 (V_{CCB}), U9.24 (V_{CCB}), U10.23 (V_{CCB}), U10.24 (V_{CCB})
/PI_USB_D+: J1.A7 (D-), J1.B7 (D-), R2.1
/PI_USB_D-: J1.A6 (D+), J1.B6 (D+), R5.1
/SWCLK: J10.1, U4.33 (SWCLK)
/SWD: J10.3, U4.34 (SWD)
/USB1-D+: U2.8 (DP1+), USB1-2.3 (D1+)
/USB1-D-: U2.7 (DM1-), USB1-2.2 (D1-)
/USB2-D+: U2.6 (DP2+), USB1-2.7 (D2+)
/USB2-D-: U2.5 (DM2-), USB1-2.6 (D2-)
/USB3-D+: J6.5, U2.4 (DP3+)
/USB3-D-: J6.3, U2.3 (DM3-)
/USB4-D+: J6.6, U2.2 (DP4+)
/USB4-D-: J6.4, U2.1 (DM4-)
/USBH+: R3.2, U4.77 (GPIO0)
/USBH-: R4.2, U4.78 (GPIO1)
/USB_DN: R5.2, U4.67 (USB_DP)
/USB_DP: R2.2, U4.66 (USB_DM)
/VBUS: D1.2 (A), J1.A4 (VBUS), J1.A9 (VBUS), J1.B4 (VBUS), J1.B9 (VBUS), Q2.2 (G)
/XOUT: R8.2, U4.31 (XOUT)
/~USB_BOOT: R11.2, SW4.2
DMU+: R3.1, U2.11 (DPU+)
DMU-: R4.1, U2.10 (DMU-)
EXT1: J2.4, U9.14 (B8)
EXT1_3V3: U4.28 (GPIO27), U9.10 (A8)
EXT2: J2.5, U10.14 (B8)
EXT2_3V3: U4.36 (GPIO28), U10.10 (A8)
EXT3: J2.6
GND: BT1.2 (-), C1.1, C2.2, C3.2, C4.2, C5.2, C6.2, C7.2, C8.2, C9.2, C10.2, C11.2, C12.2, C13.2, C14.2, C15.2, C16.2, C17.2, C18.1, C19.2, C20.1, C21.2, C22.1, C23.2, C24.2, C25.2, C26.1, C27.2, C29.1, C30.1, C32.1, C33.1, C35.1, C36.1, C37.1, C42.1, D2.3 (VSS), J1.A1 (GND), J1.A12 (GND), J1.B1 (GND), J1.B12 (GND), J2.1, J4.9, J6.7, J6.8, J8.3, J10.2, J10.MP (MountPin), J11.1, R41.1, R42.1, SW1.1, SW2.2, SW4.1, U1.1 (GND), U1.4 (GND), U1.7 (GND), U1.11 (GND), U1.15 (GND), U1.21 (GND), U2.14 (GND), U2.16 (XI), U3.1 (GND), U4.62 (VREG_PGND), U4.81 (GND), U5.9 (GND), U6.6 (GND), U6.16 (ADDR), U8.11 (GND), U8.12 (GND), U8.13 (GND), U9.11 (GND), U9.12 (GND), U9.13 (GND), U10.11 (GND), U10.12 (GND), U10.13 (GND), USB1-2.4 (GND1), USB1-2.8 (GND2), USB1-2.9 (Shield), X1.2, X1.4
GPIO23_WL_ON: U1.12 (WL_ON), U1.13 (BT_ON), U4.23 (GPIO23)
GPIO24_WL_DATA: R43.2, R44.2, R45.2, U4.25 (GPIO24)
I2C_SCL: J11.3, U4.21 (GPIO21), U5.5 (SCL), U6.12 (SCL)
I2C_SDA: J11.4, U4.20 (GPIO20), U5.7 (SDA), U6.13 (SDA)
J1:B3V3: U4.39 (GPIO31), U9.4 (A2)
J1:BACK: L9.1, U9.20 (B2)
J1:F3V3: U4.38 (GPIO30), U9.3 (A1)
J1:FWD: L8.1, U9.21 (B1)
J1:L3V3: U4.40 (GPIO32), U9.5 (A3)
J1:LEFT: L10.1, U9.19 (B3)
J1:PA3V3: U4.49 (GPIO40_ADC0), U9.8 (A6)
J1:PB3V3: U4.52 (GPIO41_ADC1), U9.9 (A7)
J1:POTA: L4.1, U9.16 (B6)
J1:POTB: L5.1, U9.15 (B7)
J1:R3V3: U4.42 (GPIO33), U9.6 (A4)
J1:RIGHT: L11.1, U9.18 (B4)
J1:T3V3: U4.43 (GPIO34), U9.7 (A5)
J1:TRIGGER: L6.1, U9.17 (B5)
J2:B3V3: U4.45 (GPIO36), U10.4 (A2)
J2:BACK: L13.1, U10.20 (B2)
J2:F3V3: U4.44 (GPIO35), U10.3 (A1)
J2:FWD: L12.1, U10.21 (B1)
J2:L3V3: U4.46 (GPIO37), U10.5 (A3)
J2:LEFT: L14.1, U10.19 (B3)
J2:PA3V3: U4.53 (GPIO42_ADC2), U10.8 (A6)
J2:PB3V3: U4.54 (GPIO43_ADC3), U10.9 (A7)
J2:POTA: L2.1, U10.16 (B6)
J2:POTB: L3.1, U10.15 (B7)
J2:R3V3: U4.47 (GPIO38), U10.6 (A4)
J2:RIGHT: L15.1, U10.18 (B4)
J2:T3V3: U4.48 (GPIO39), U10.7 (A5)
J2:TRIGGER: L7.1, U10.17 (B5)
LEVEL_ENABLE: R36.1, U4.27 (GPIO26), U8.22 (~OE), U9.22 (~OE), U10.22 (~OE)
NeoPixelData: D2.4 (DIN), U4.22 (GPIO22)
unnamed: BT1.1 (+), R13.2
unnamed: C18.2, R8.1, X1.3
unnamed: C42.2, D2.2 (DOUT), J8.2
unnamed: D3.2 (A), R13.1
unnamed: C22.2, D3.1 (K), U5.3 (VBAT)
unnamed: J1.A5 (CC1), R41.2
unnamed: J1.B5 (CC2), R42.2
unnamed: J2.7, R6.1
unnamed: J2.8, R35.1
unnamed: J3.2, R22.1
unnamed: J3.3, R23.1
unnamed: J3.6, R24.1
unnamed: J3.7, R25.1
unnamed: J3.8, R26.1
unnamed: J4.1, U6.2 (P0)
unnamed: J4.2, U6.3 (P1)
unnamed: J4.3, U6.4 (P2)
unnamed: J4.4, U6.5 (P3)
unnamed: J4.5, U6.7 (P4)
unnamed: J4.6, U6.8 (P5)
unnamed: J4.7, U6.9 (P6)
unnamed: J4.8, U6.10 (P7)
unnamed: J5.1, R17.1
unnamed: J5.2, R18.1
unnamed: J5.3, R19.1
unnamed: J5.4, R20.1
unnamed: J5.5, R21.1
unnamed: J5.13, R16.2
unnamed: J5.15, R9.2
unnamed: J5.16, R14.2
unnamed: J5.17, R15.2
unnamed: J7.1, R27.1
unnamed: J7.2, R28.1
unnamed: J7.3, R29.1
unnamed: J7.4, R30.1
unnamed: J7.5, R31.1
unnamed: J7.6, R32.1
unnamed: J7.7, R33.1
unnamed: J7.8, R34.1
unnamed: L2.2, R17.2
unnamed: L3.2, R18.2
unnamed: L4.2, R19.2
unnamed: L5.2, R20.2
unnamed: L6.2, R22.2
unnamed: L7.2, R23.2
unnamed: L8.2, R27.2
unnamed: L9.2, R28.2
unnamed: L10.2, R29.2
unnamed: L11.2, R30.2
unnamed: L12.2, R31.2
unnamed: L13.2, R32.2
unnamed: L14.2, R33.2
unnamed: L15.2, R34.2
unnamed: L16.2, R35.2
unnamed: R43.1, U1.5 (DI)
unnamed: R44.1, U1.6 (DO)
unnamed: R45.1, U1.10 (nIRQ)
unnamed: F1.1, U2.12 (V5)
unnamed: C3.1, C24.1, U2.13 (VDD33)
unnamed: R11.1, U4.75 (QSPI_SS)
unnamed: R1.1, U4.35 (RUN)
unnamed: C20.2, R10.1, U4.61 (VREG_AVDD)
unnamed: L1.2, U4.63 (VREG_LX)
unnamed: C17.1, U4.30 (XIN), X1.1
unnamed: R12.2, U5.1 (FOE)
unnamed: R7.2, U5.10 (/INT)
unnamed: R46.2, U6.11 (~INT)
unnamed: R40.2, U6.1 (~RESET)
unnamed: R37.2, U8.2 (DIR)
unnamed: R38.2, U9.2 (DIR)
unnamed: R39.2, U10.2 (DIR)
OPTION: R26.2, SW1.2, U8.15 (B7)
OPTION3V3: U4.56 (GPIO45_ADC5), U8.9 (A7)
RESET: L16.1, R1.2, SW2.1, U8.14 (B8)
RESET3V3: U4.58 (GPIO47_ADC7), U8.10 (A8)
SELECT: R25.2, U8.16 (B6)
SELECT3V3: U4.57 (GPIO46_ADC6), U8.8 (A6)
SIO:CLOCK_IN: R9.1, U8.18 (B4)
SIO:CLOCK_IN_3V3: U4.3 (GPIO6), U8.6 (A4)
SIO:CLOCK_OUT: R14.1, U4.1 (GPIO4)
SIO:COMMAND: C23.1, R6.2, U4.79 (GPIO2)
SIO:DATA_IN: R16.1, U8.19 (B3)
SIO:DATA_IN3V3: U4.2 (GPIO5), U8.5 (A3)
SIO:DATA_OUT: R15.1, U4.80 (GPIO3)
SPI0_CS0: U4.17 (GPIO17)
SPI0_RX: U4.16 (GPIO16)
SPI0_SCK: U4.18 (GPIO18)
SPI0_TX: U4.19 (GPIO19)
SPI_WL_CLOCK: U1.3 (SCLK), U4.37 (GPIO29)
SPI_WL_CS: U1.9 (CS), U4.26 (GPIO25)
START: R24.2, U8.17 (B5)
START3V3: U4.55 (GPIO44_ADC4), U8.7 (A5)
~IRQ: J5.18, U4.12 (GPIO13)
~K0: J5.12, U4.4 (GPIO7)
~K1: J5.11, U4.6 (GPIO8)
~K2: J5.10, U4.7 (GPIO9)
~K3: J5.9, U4.8 (GPIO10)
~K4: J5.8, U4.9 (GPIO11)
~K5: J5.7, U4.11 (GPIO12)
~KR1: J5.14, U8.21 (B1)
~KR13V3: U4.13 (GPIO14), U8.3 (A1)
~KR2: R21.2, U8.20 (B2)
~KR23V3: U4.14 (GPIO15), U8.4 (A2)

Notes on the sheet:
Display / I2C
Level shifting
ATARI
GTIA 7-14
PIA 2-9
Wireless
https://ia801409.us.archive.org/4/items/SIOspecs/SIOspecs_text.pdf
RTC
Controls
Make sure R7 and R8 are close to RP2350
JST Debug Connector
Key (no pin)
Pokey 12---29 13---28 14---27 15---26 16---25 17---24 18---23 19---22 20---21
USB
NeoPixels
RP2354B
Power
The pot lines simulate a pot with PWM. A real pot is a variable resistor that acts as a voltage divider so the associated capacitor gets charged more or less quickly. Using the PWM duty cycle, we can apply a fixed voltage part of the time instead of a variable voltage all the time. This way, we can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

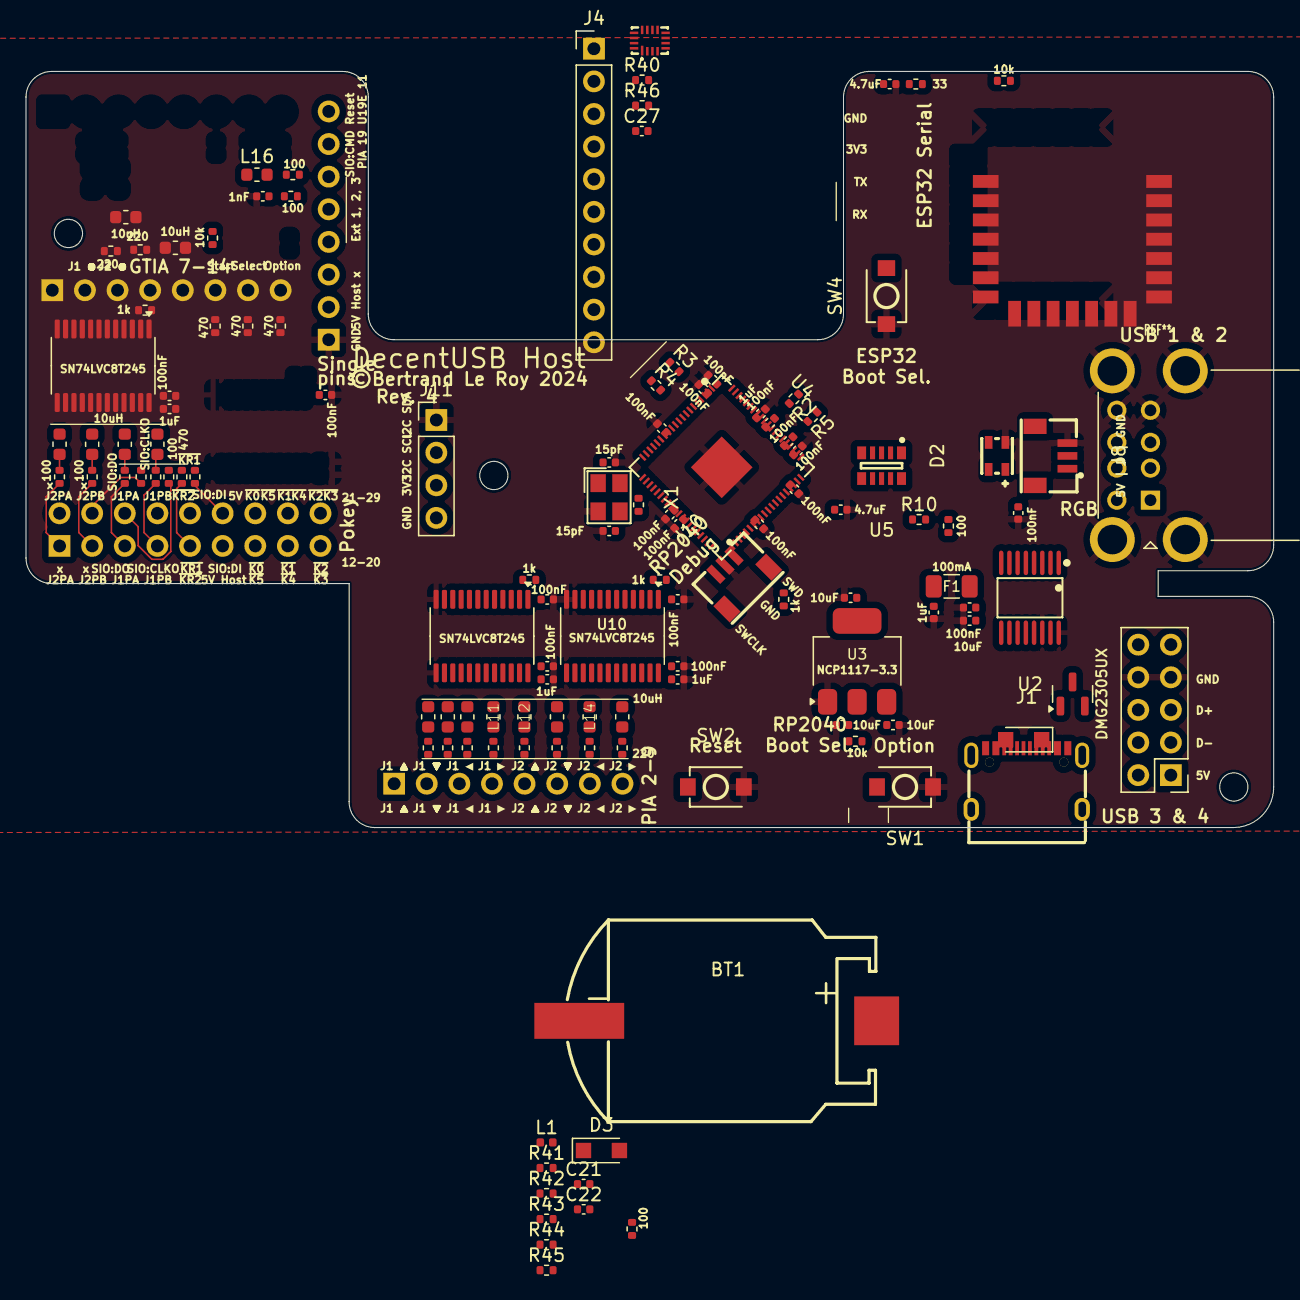
[picture p378: board DecentUSB2350.kicad_pcb from above]

Board: 2 copper layers, 97.2 x 58.9 mm, 131 parts (0 on the bottom side), 159 nets.
