bleroy/3d-junkyard/DecentCart/DecentCart5200/DecentCart5200.kicad_pcb

## KiCad design DecentCart/DecentCart5200/DecentCart5200.kicad_pcb (2025-03-16)

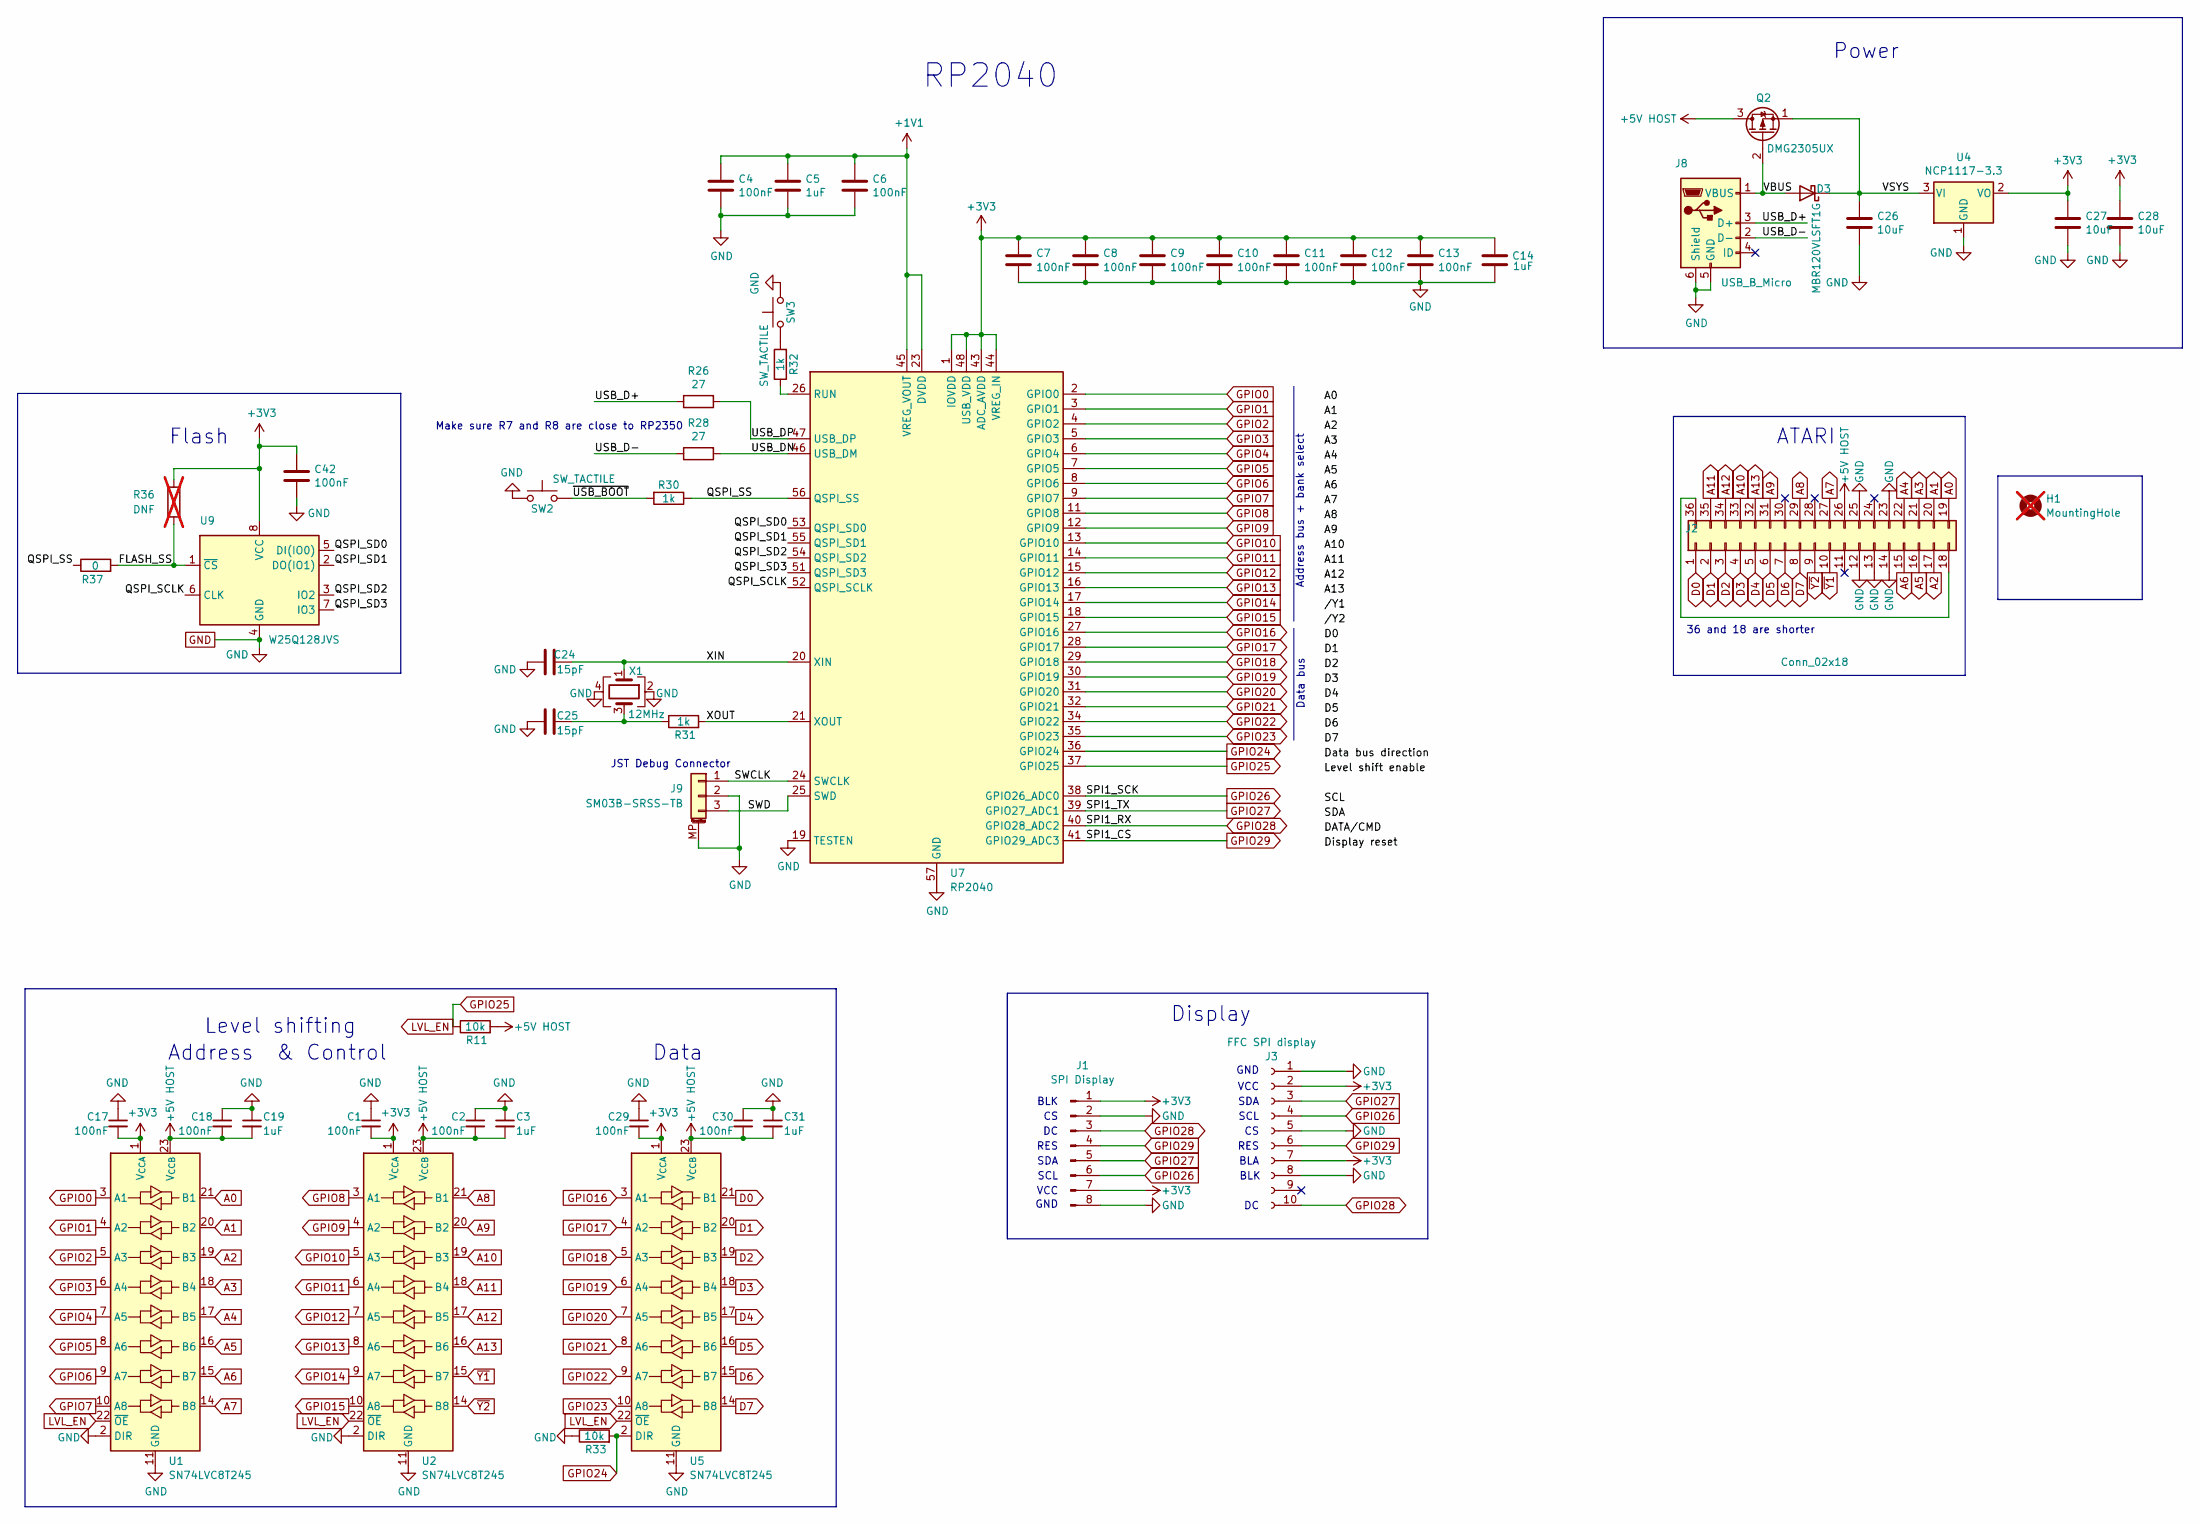
[picture p379: schematic DecentCart5200.kicad_sch]

Parts:
C1, C2, C4, C6, C7, C8, C9, C10, C11, C12, C13, C17, C18, C29, C30, C42: 100nF; C_0402_1005Metric; JLCPCB Part # C1525
C3, C5, C14, C19, C31: 1uF; C_0402_1005Metric; JLCPCB Part # C52923
C24, C25: 15pF; C_0402_1005Metric; JLCPCB Part # C1548
C26, C27, C28: 10uF; C_0402_1005Metric; JLCPCB Part # C15525
D3: MBR120VLSFT1G; Nexperia_CFP3_SOD-123W; JLCPCB Part # C8598
H1: MountingHole; MountingHole_2.2mm_M2; not fitted
J1: SPI Display; PinHeader_1x08_P2.54mm_Vertical
J2: Conn_02x18; Atari 5200 Cartridge Edge Connector
J3: FFC SPI display; TE_1-1734839-0_1x10-1MP_P0.5mm_Horizontal; JLCPCB Part # C262659
J8: USB_B_Micro; USB_Micro-B; JLCPCB Part # C2765187
J9: SM03B-SRSS-TB; JST_SH_BM03B-SRSS-TB_1x03-1MP_P1.00mm_Vertical; JLCPCB Part # C160389
Q2: DMG2305UX; SOT-23; JLCPCB Part # C150470
R11, R33: 10k; R_0402_1005Metric; JLCPCB Part # C25744
R26, R28: 27; R_0805_2012Metric; JLCPCB Part # C17561
R30, R31, R32: 1k; R_0402_1005Metric; JLCPCB Part # C11702
R36: DNF; R_0402_1005Metric; not fitted
R37: 0; SolderJumper-2_P1.3mm_Bridged_RoundedPad1.0x1.5mm; JLCPCB Part # C2074089
SW2, SW3: SW_TACTILE; Tactile_Switch_Basic_XKB_TS-1187A; JLCPCB Part # C318884
U1, U2, U5: SN74LVC8T245; TSSOP-24_4.4x7.8mm_P0.65mm; JLCPCB Part # C27643
U4: NCP1117-3.3; SOT-223-3_TabPin2; JLCPCB Part # C6186
U7: RP2040; QFN-56-1EP_7x7mm_P0.4mm_EP3.2x3.2mm; JLCPCB Part # C2040
U9: W25Q128JVS; SOIC-8_5.23x5.23mm_P1.27mm; JLCPCB Part # C97521
X1: 12MHz; Crystal_SMD_Abracon_ABM8AIG-4Pin_3.2x2.5mm; JLCPCB Part # C9002

Connections:
+1V1: C4.1, C5.1, C6.1, U7.23 (DVDD), U7.45 (VREG_VOUT), U7.50 (DVDD)
+3V3: C1.2, C7.1, C8.1, C9.1, C10.1, C11.1, C12.1, C13.1, C14.1, C17.2, C27.1, C28.1, C29.2, C42.1, J1.1, J1.7, J3.2, J3.7, R36.1, U1.1 (V_{CCA}), U2.1 (V_{CCA}), U4.2 (VO), U5.1 (V_{CCA}), U7.1 (IOVDD), U7.10 (IOVDD), U7.22 (IOVDD), U7.33 (IOVDD), U7.42 (IOVDD), U7.43 (ADC_AVDD), U7.44 (VREG_IN), U7.48 (USB_VDD), U7.49 (IOVDD), U9.8 (VCC)
+5V HOST: C2.2, C3.2, C18.2, C19.2, C30.2, C31.2, J2.26, Q2.3 (D), R11.2, U1.23 (V_{CCB}), U1.24 (V_{CCB}), U2.23 (V_{CCB}), U2.24 (V_{CCB}), U5.23 (V_{CCB}), U5.24 (V_{CCB})
/FLASH_SS: R36.2, R37.2, U9.1 (~CS)
/QSPI_SCLK: U7.52 (QSPI_SCLK), U9.6 (CLK)
/QSPI_SD0: U7.53 (QSPI_SD0), U9.5 (DI(IO0))
/QSPI_SD1: U7.55 (QSPI_SD1), U9.2 (DO(IO1))
/QSPI_SD2: U7.54 (QSPI_SD2), U9.3 (IO2)
/QSPI_SD3: U7.51 (QSPI_SD3), U9.7 (IO3)
/QSPI_SS: R30.1, R37.1, U7.56 (QSPI_SS)
/SWCLK: J9.1, U7.24 (SWCLK)
/SWD: J9.3, U7.25 (SWD)
/USB_D+: J8.3 (D+), R26.1
/USB_D-: J8.2 (D-), R28.1
/USB_DN: R28.2, U7.46 (USB_DM)
/USB_DP: R26.2, U7.47 (USB_DP)
/VBUS: D3.2 (A), J8.1 (VBUS), Q2.2 (G)
/XIN: C24.1, U7.20 (XIN), X1.1
/XOUT: R31.2, U7.21 (XOUT)
/~USB_BOOT: R30.2, SW2.2
A0: J2.19, U1.21 (B1)
A1: J2.20, U1.20 (B2)
A2: J2.17, U1.19 (B3)
A3: J2.21, U1.18 (B4)
A4: J2.22, U1.17 (B5)
A5: J2.16, U1.16 (B6)
A6: J2.15, U1.15 (B7)
A7: J2.27, U1.14 (B8)
A8: J2.29, U2.21 (B1)
A9: J2.31, U2.20 (B2)
A10: J2.33, U2.19 (B3)
A11: J2.35, U2.18 (B4)
A12: J2.34, U2.17 (B5)
A13: J2.32, U2.16 (B6)
D0: J2.1, U5.21 (B1)
D1: J2.2, U5.20 (B2)
D2: J2.3, U5.19 (B3)
D3: J2.4, U5.18 (B4)
D4: J2.5, U5.17 (B5)
D5: J2.6, U5.16 (B6)
D6: J2.7, U5.15 (B7)
D7: J2.8, U5.14 (B8)
GND: C1.1, C2.1, C3.1, C4.2, C5.2, C6.2, C7.2, C8.2, C9.2, C10.2, C11.2, C12.2, C13.2, C14.2, C17.1, C18.1, C19.1, C24.2, C25.1, C26.2, C27.2, C28.2, C29.1, C30.1, C31.1, C42.2, J1.2, J1.8, J2.12, J2.13, J2.14, J2.23, J2.25, J3.1, J3.5, J3.8, J8.5 (GND), J8.6 (Shield), J9.2, J9.MP (MountPin), R33.1, SW2.1, SW3.2, U1.2 (DIR), U1.11 (GND), U1.12 (GND), U1.13 (GND), U2.2 (DIR), U2.11 (GND), U2.12 (GND), U2.13 (GND), U4.1 (GND), U5.11 (GND), U5.12 (GND), U5.13 (GND), U7.19 (TESTEN), U7.57 (GND), U9.4 (GND), X1.2, X1.4
GPIO0: U1.3 (A1), U7.2 (GPIO0)
GPIO1: U1.4 (A2), U7.3 (GPIO1)
GPIO2: U1.5 (A3), U7.4 (GPIO2)
GPIO3: U1.6 (A4), U7.5 (GPIO3)
GPIO4: U1.7 (A5), U7.6 (GPIO4)
GPIO5: U1.8 (A6), U7.7 (GPIO5)
GPIO6: U1.9 (A7), U7.8 (GPIO6)
GPIO7: U1.10 (A8), U7.9 (GPIO7)
GPIO8: U2.3 (A1), U7.11 (GPIO8)
GPIO9: U2.4 (A2), U7.12 (GPIO9)
GPIO10: U2.5 (A3), U7.13 (GPIO10)
GPIO11: U2.6 (A4), U7.14 (GPIO11)
GPIO12: U2.7 (A5), U7.15 (GPIO12)
GPIO13: U2.8 (A6), U7.16 (GPIO13)
GPIO14: U2.9 (A7), U7.17 (GPIO14)
GPIO15: U2.10 (A8), U7.18 (GPIO15)
GPIO16: U5.3 (A1), U7.27 (GPIO16)
GPIO17: U5.4 (A2), U7.28 (GPIO17)
GPIO18: U5.5 (A3), U7.29 (GPIO18)
GPIO19: U5.6 (A4), U7.30 (GPIO19)
GPIO20: U5.7 (A5), U7.31 (GPIO20)
GPIO21: U5.8 (A6), U7.32 (GPIO21)
GPIO22: U5.9 (A7), U7.34 (GPIO22)
GPIO23: U5.10 (A8), U7.35 (GPIO23)
GPIO24: R33.2, U5.2 (DIR), U7.36 (GPIO24)
GPIO25: R11.1, U1.22 (~OE), U2.22 (~OE), U5.22 (~OE), U7.37 (GPIO25)
GPIO26: J1.6, J3.4, U7.38 (GPIO26_ADC0)
GPIO27: J1.5, J3.3, U7.39 (GPIO27_ADC1)
GPIO28: J1.3, J3.10, U7.40 (GPIO28_ADC2)
GPIO29: J1.4, J3.6, U7.41 (GPIO29_ADC3)
unnamed: C25.2, R31.1, X1.3
unnamed: C26.1, D3.1 (K), Q2.1 (S), U4.3 (VI)
unnamed: J2.18, J2.36
unnamed: R32.2, SW3.1
unnamed: R32.1, U7.26 (RUN)
~Y1: J2.10, U2.15 (B7)
~Y2: J2.9, U2.14 (B8)

Notes on the sheet:
SDA
VCC
Flash
RP2040
ATARI
Level shifting
Address bus + bank select
Data bus
RES
BLK
GND
Power
36 and 18 are shorter
SCL
Make sure R7 and R8 are close to RP2350
Data
JST Debug Connector
Display
BLA
Address & Control

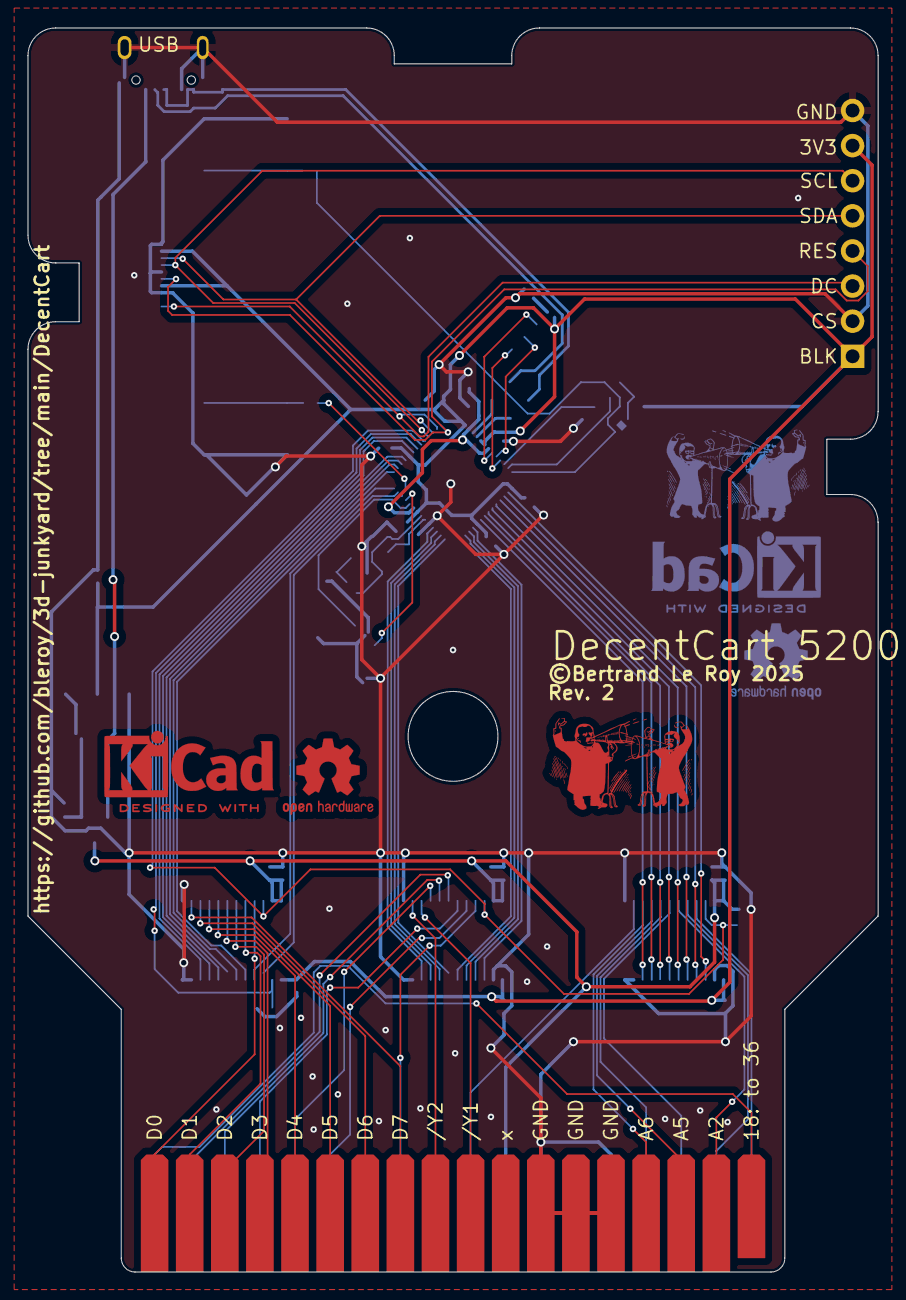
[picture p380: board DecentCart5200.kicad_pcb from above]

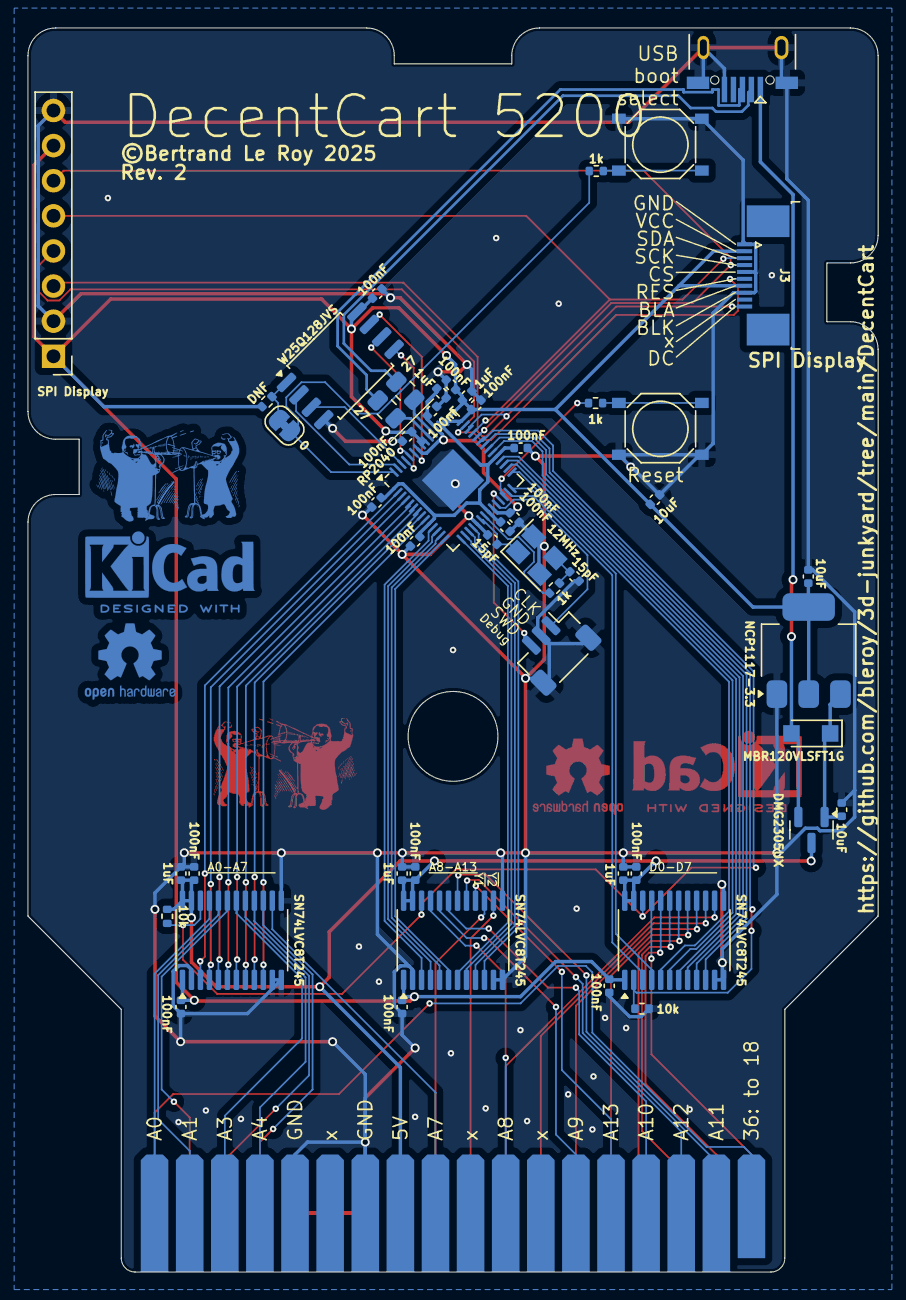
[picture p381: board DecentCart5200.kicad_pcb from below]

Board: 2 copper layers, 61.5 x 90.0 mm, 52 parts (50 on the bottom side), 80 nets.
