bleroy/3d-junkyard/misc-models/KeyboardTester/v1/AtariKeyboardTester.kicad_pcb

## KiCad design misc-models/KeyboardTester/v1/AtariKeyboardTester.kicad_pcb (2023-07-08)

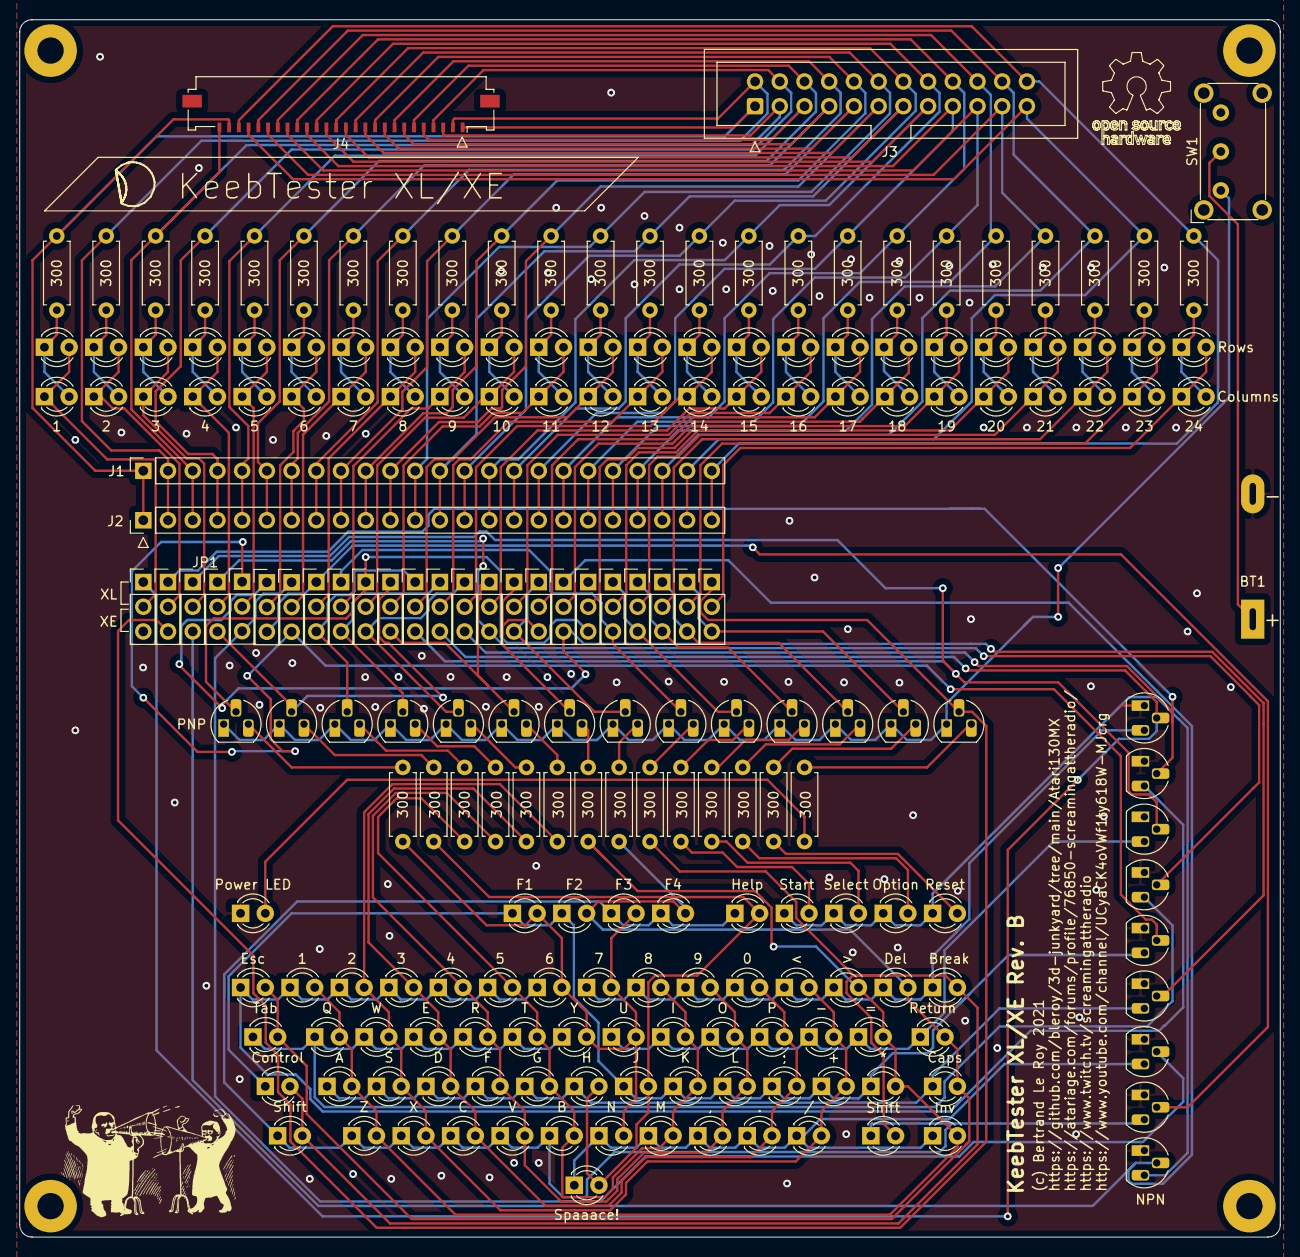
[picture p382: board AtariKeyboardTester.kicad_pcb from above]

Board: 2 copper layers, 129.5 x 125.1 mm, 207 parts (1 on the bottom side), 135 nets.

Parts:
0, 1, 1#2, 2, 2#2, 3, 3#2, 4, 4#2, 5, 5#2, 6, 6#2, 7, 7#2, 8, 8#2, 9, 9#2, 10, 11, 12, 13, 14, 15, 16, 17, 18, 19, 20, 21, 22, 23, 24, .: LED; LED_D3.0mm
300, 300#2, 300#3, 300#4, 300#5, 300#6, 300#7, 300#8, 300#9, 300#10, 300#11, 300#12, 300#13, 300#14, 300#15, 300#16, 300#17, 300#18, 300#19, 300#20, 300#21, 300#22, 300#23, 300#24, 300#25, 300#26, 300#27, 300#28, 300#29, 300#30, 300#31, 300#32, 300#33, 300#34, 300#35: R; R100
*: LED; LED_D3.0mm
+: LED; LED_D3.0mm
,: LED; LED_D3.0mm
-: LED; LED_D3.0mm
/: LED; LED_D3.0mm
;: LED; LED_D3.0mm
<: LED; LED_D3.0mm
=: LED; LED_D3.0mm
>: LED; LED_D3.0mm
A: LED; LED_D3.0mm
B: LED; LED_D3.0mm
BT1: Battery; BatteryHolder_MPD_BA9VPC_1xPP3
Break: LED; LED_D3.0mm
C: LED; LED_D3.0mm
Caps: LED; LED_D3.0mm
Control: LED; LED_D3.0mm
D: LED; LED_D3.0mm
D_A_2, D_A_3, D_A_4, D_A_5, D_A_6, D_A_7, D_A_8, D_A_9, D_A_10, D_A_11, D_A_12, D_A_13, D_A_14, D_A_15, D_A_16, D_A_17, D_A_18, D_A_19, D_A_20, D_A_21, D_A_22, D_A_23, D_A_24, D_A_25: LED; LED_D3.0mm
Del: LED; LED_D3.0mm
E: LED; LED_D3.0mm
Esc: LED; LED_D3.0mm
F, F1, F2, F3, F4: LED; LED_D3.0mm
G: LED; LED_D3.0mm
H: LED; LED_D3.0mm
Help: LED; LED_D3.0mm
I: LED; LED_D3.0mm
Inv: LED; LED_D3.0mm
J: LED; LED_D3.0mm
J1: Conn_01x24; PinSocket_1x24_P2.54mm_Vertical
J2: Conn_01x24; PinHeader_1x24_P2.54mm_Vertical
J3: Conn_02x12_Odd_Even; IDC-Header_2x12_P2.54mm_Vertical
J4: Conn_01x26; Molex_200528-0260_1x26-1MP_P1.00mm_Horizontal
JP1, JP2, JP3, JP4, JP5, JP6, JP7, JP8, JP9, JP10, JP11, JP12, JP13, JP14, JP15, JP16, JP17, JP18, JP19, JP20, JP21, JP22, JP23, JP24: SolderJumper_3_Open; PinHeader_1x03_P2.54mm_Vertical
K: LED; LED_D3.0mm
L: LED; LED_D3.0mm
M: LED; LED_D3.0mm
Matrix: Atari_XL_XE_Matrix
N: LED; LED_D3.0mm
O: LED; LED_D3.0mm
Option: LED; LED_D3.0mm
P: LED; LED_D3.0mm
Power LED: LED; LED_D3.0mm
Q: LED; LED_D3.0mm
Q_COL_1, Q_COL_2, Q_COL_3, Q_COL_4, Q_COL_5, Q_COL_6, Q_COL_7, Q_COL_8, Q_COL_9, Q_COL_10, Q_COL_11, Q_COL_12, Q_COL_13, Q_COL_14: Q_PNP_EBC; TO-92_HandSolder
Q_ROW_1, Q_ROW_2, Q_ROW_3, Q_ROW_4, Q_ROW_5, Q_ROW_6, Q_ROW_7, Q_ROW_8, Q_ROW_9: Q_NPN_EBC; TO-92_HandSolder
R: LED; LED_D3.0mm
R1, R2, R3: 300; R100
Reset: LED; LED_D3.0mm
Return: LED; LED_D3.0mm
S: LED; LED_D3.0mm
SW1: SW_SPST; SW_E-Switch_EG1224_SPDT_Angled
Select: LED; LED_D3.0mm
Shift: LED; LED_D3.0mm
Shift#2: LED; LED_D3.0mm
Spaaace!: LED; LED_D3.0mm
Start: LED; LED_D3.0mm
T: LED; LED_D3.0mm
Tab: LED; LED_D3.0mm
U: LED; LED_D3.0mm
V: LED; LED_D3.0mm
W: LED; LED_D3.0mm
X: LED; LED_D3.0mm
Y: LED; LED_D3.0mm
Z: LED; LED_D3.0mm

Connections:
B_CONN_1: 1.1, D_A_2.2, JP1.2
B_CONN_2: 2.1, D_A_3.2, JP2.2
B_CONN_3: 3.1, D_A_4.2, JP3.2
B_CONN_4: 4.1, D_A_5.2, JP4.2
B_CONN_5: 5.1, D_A_6.2, JP5.2
B_CONN_6: 6.1, D_A_7.2, JP6.2
B_CONN_7: 7.1, D_A_8.2, JP7.2
B_CONN_8: 8.1, D_A_9.2, JP8.2
B_CONN_9: 9.1, D_A_10.2, JP9.2
B_CONN_10: 10.1, D_A_11.2, JP10.2
B_CONN_11: 11.1, D_A_12.2, JP11.2
B_CONN_12: 12.1, D_A_13.2, JP12.2
B_CONN_13: 13.1, D_A_14.2, JP13.2
B_CONN_14: 14.1, D_A_15.2, JP14.2
B_CONN_15: 15.1, D_A_16.2, JP15.2
B_CONN_16: 16.1, D_A_17.2, JP16.2
B_CONN_17: 17.1, D_A_18.2, JP17.2
B_CONN_18: 18.1, D_A_19.2, JP18.2
B_CONN_19: 19.1, D_A_20.2, JP19.2
B_CONN_20: 20.1, D_A_21.2, JP20.2
B_CONN_21: 21.1, D_A_22.2, JP21.2
B_CONN_22: 22.1, D_A_23.2, JP22.2
B_CONN_23: 23.1, D_A_24.2, JP23.2
B_CONN_24: 24.1, D_A_25.2, JP24.2
COL_1: JP10.1, JP19.3, Q_COL_1.2
COL_2: JP4.3, JP11.1, Q_COL_2.2
COL_3: JP8.3, JP12.1, Q_COL_3.2
COL_4: JP9.3, JP13.1, Q_COL_4.2
COL_5: JP10.3, JP14.1, Q_COL_5.2
COL_6: JP11.3, JP15.1, Q_COL_6.2
COL_7: JP16.1, JP17.3, Q_COL_7.2
COL_8: JP16.3, JP17.1, Q_COL_8.2
COL_9: JP9.1, JP20.3, Q_COL_9.2
COL_10: JP20.1, JP21.3, Q_COL_10.2
COL_11: JP21.1, JP22.3, Q_COL_11.2
COL_12: JP22.1, JP23.3, Q_COL_12.2
COL_13: JP23.1, JP24.3, Q_COL_13.2
COL_14: JP2.3, JP24.1, Q_COL_14.2
CONN_1: J1.1, J2.1, J3.1, J4.1, J4.25, R1.2
CONN_2: J1.2, J2.2, J3.2, J4.2, R2.2
CONN_3: J1.3, J2.3, J3.3, J4.3, J4.26, R3.2
CONN_4: 300#33.2, J1.4, J2.4, J3.4, J4.4
CONN_5: 300.2, J1.5, J2.5, J3.5, J4.5
CONN_6: 300#2.2, J1.6, J2.6, J3.6, J4.6
CONN_7: 300#3.2, J1.7, J2.7, J3.7, J4.7
CONN_8: 300#4.2, J1.8, J2.8, J3.8, J4.8
CONN_9: 300#5.2, J1.9, J2.9, J3.9, J4.9
CONN_10: 300#6.2, J1.10, J2.10, J3.10, J4.10
CONN_11: 300#7.2, J1.11, J2.11, J3.11, J4.11
CONN_12: 300#8.2, J1.12, J2.12, J3.12, J4.12
CONN_13: 300#9.2, J1.13, J2.13, J3.13, J4.13
CONN_14: 300#10.2, J1.14, J2.14, J3.14, J4.14
CONN_15: 300#11.2, J1.15, J2.15, J3.15, J4.15
CONN_16: 300#12.2, J1.16, J2.16, J3.16, J4.16
CONN_17: 300#13.2, J1.17, J2.17, J3.17, J4.17
CONN_18: 300#14.2, J1.18, J2.18, J3.18, J4.18
CONN_19: 300#15.2, J1.19, J2.19, J3.19, J4.19
CONN_20: 300#16.2, J1.20, J2.20, J3.20, J4.20
CONN_21: 300#17.2, J1.21, J2.21, J3.21, J4.21
CONN_22: 300#18.2, J1.22, J2.22, J3.22, J4.22
CONN_23: 300#34.2, J1.23, J2.23, J3.23, J4.23
CONN_24: 300#19.2, J1.24, J2.24, J3.24, J4.24
GND: BT1.2, Power LED.1, Q_ROW_1.1, Q_ROW_2.1, Q_ROW_3.1, Q_ROW_4.1, Q_ROW_5.1, Q_ROW_6.1, Q_ROW_7.1, Q_ROW_8.1, Q_ROW_9.1
LED_COL_1: 6#2.2, 7#2.2, 300#20.2, F1.2, F3.2, N.2, U.2, Y.2
LED_COL_2: 300#21.2, H.2, Help.2, J.2, Spaaace!.2
LED_COL_3: 5#2.2, 8#2.2, 300#22.2, B.2, G.2, I.2, K.2, M.2, T.2
LED_COL_4: 4#2.2, 9#2.2, 300#23.2, ,.2, F.2, L.2, O.2, R.2, V.2
LED_COL_5: 0.2, 3#2.2, 300#24.2, ..2, ;.2, C.2, D.2, E.2, P.2
LED_COL_6: 2#2.2, 300#25.2, +.2, -.2, /.2, <.2, S.2, W.2, X.2
LED_COL_7: 1#2.2, 300#26.2, *.2, =.2, >.2, A.2, Inv.2, Q.2, Z.2
LED_COL_8: 300#35.2, Caps.2, Del.2, Esc.2, F2.2, F4.2, Return.2, Tab.2
LED_COL_9: 300#27.2, Break.2, Control.2, Shift.2, Shift#2.2
LED_COL_10: 300#28.2, Start.2
LED_COL_11: 300#29.2, Select.2
LED_COL_12: 300#30.2, Option.2
LED_COL_13: 300#31.2, Reset.2
LED_COL_14: 300#32.2, Power LED.2
LED_ROW_1: 0.1, 7#2.1, 8#2.1, 9#2.1, <.1, >.1, Break.1, Del.1, Q_ROW_1.3
LED_ROW_2: 1#2.1, 2#2.1, 3#2.1, 4#2.1, 5#2.1, 6#2.1, Esc.1, Q_ROW_2.3
LED_ROW_3: -.1, =.1, I.1, O.1, P.1, Q_ROW_3.3, Return.1, U.1
LED_ROW_4: E.1, Q.1, Q_ROW_4.3, R.1, T.1, Tab.1, W.1, Y.1
LED_ROW_5: *.1, +.1, ;.1, Control.1, F1.1, F2.1, J.1, K.1, L.1, Q_ROW_5.3
LED_ROW_6: A.1, Caps.1, D.1, F.1, G.1, H.1, Q_ROW_6.3, S.1
LED_ROW_7: ,.1, ..1, /.1, Inv.1, M.1, N.1, Q_ROW_7.3, Spaaace!.1
LED_ROW_8: B.1, C.1, F3.1, F4.1, Help.1, Q_ROW_8.3, Shift.1, Shift#2.1, V.1, X.1, Z.1
LED_ROW_9: Option.1, Q_ROW_9.3, Reset.1, Select.1, Start.1
unnamed: BT1.1, SW1.2
unnamed: 1.2, D_A_2.1, R1.1
unnamed: 2.2, D_A_3.1, R2.1
unnamed: 3.2, D_A_4.1, R3.1
unnamed: 4.2, 300#33.1, D_A_5.1
unnamed: 5.2, 300.1, D_A_6.1
unnamed: 6.2, 300#2.1, D_A_7.1
unnamed: 7.2, 300#3.1, D_A_8.1
unnamed: 8.2, 300#4.1, D_A_9.1
unnamed: 9.2, 300#5.1, D_A_10.1
unnamed: 10.2, 300#6.1, D_A_11.1
unnamed: 11.2, 300#7.1, D_A_12.1
unnamed: 12.2, 300#8.1, D_A_13.1
unnamed: 13.2, 300#9.1, D_A_14.1
unnamed: 14.2, 300#10.1, D_A_15.1
unnamed: 15.2, 300#11.1, D_A_16.1
unnamed: 16.2, 300#12.1, D_A_17.1
unnamed: 17.2, 300#13.1, D_A_18.1
unnamed: 18.2, 300#14.1, D_A_19.1
unnamed: 19.2, 300#15.1, D_A_20.1
unnamed: 20.2, 300#16.1, D_A_21.1
unnamed: 21.2, 300#17.1, D_A_22.1
unnamed: 22.2, 300#18.1, D_A_23.1
unnamed: 23.2, 300#34.1, D_A_24.1
unnamed: 24.2, 300#19.1, D_A_25.1
unnamed: 300#20.1, Q_COL_1.3
unnamed: 300#21.1, Q_COL_2.3
unnamed: 300#22.1, Q_COL_3.3
unnamed: 300#23.1, Q_COL_4.3
unnamed: 300#24.1, Q_COL_5.3
unnamed: 300#25.1, Q_COL_6.3
unnamed: 300#26.1, Q_COL_7.3
unnamed: 300#35.1, Q_COL_8.3
unnamed: 300#27.1, Q_COL_9.3
unnamed: 300#28.1, Q_COL_10.3
unnamed: 300#29.1, Q_COL_11.3
unnamed: 300#30.1, Q_COL_12.3
unnamed: 300#31.1, Q_COL_13.3
unnamed: 300#32.1, Q_COL_14.3
ROW_1: JP1.1, JP13.3, Q_ROW_1.2
ROW_2: JP2.1, JP14.3, Q_ROW_2.2
ROW_3: JP3.1, JP12.3, Q_ROW_3.2
ROW_4: JP4.1, JP15.3, Q_ROW_4.2
ROW_5: JP5.1, JP7.3, Q_ROW_5.2
ROW_6: JP6.1, JP18.3, Q_ROW_6.2
ROW_7: JP5.3, JP7.1, Q_ROW_7.2
ROW_8: JP6.3, JP8.1, Q_ROW_8.2
ROW_9: JP3.3, JP18.1, Q_ROW_9.2
VCC: Q_COL_1.1, Q_COL_2.1, Q_COL_3.1, Q_COL_4.1, Q_COL_5.1, Q_COL_6.1, Q_COL_7.1, Q_COL_8.1, Q_COL_9.1, Q_COL_10.1, Q_COL_11.1, Q_COL_12.1, Q_COL_13.1, Q_COL_14.1, SW1.1
