bleroy/3d-junkyard/misc-models/KeyboardTester/DecentKeyboardTester.kicad_pcb

## KiCad design misc-models/KeyboardTester/DecentKeyboardTester.kicad_pcb (2025-03-02)

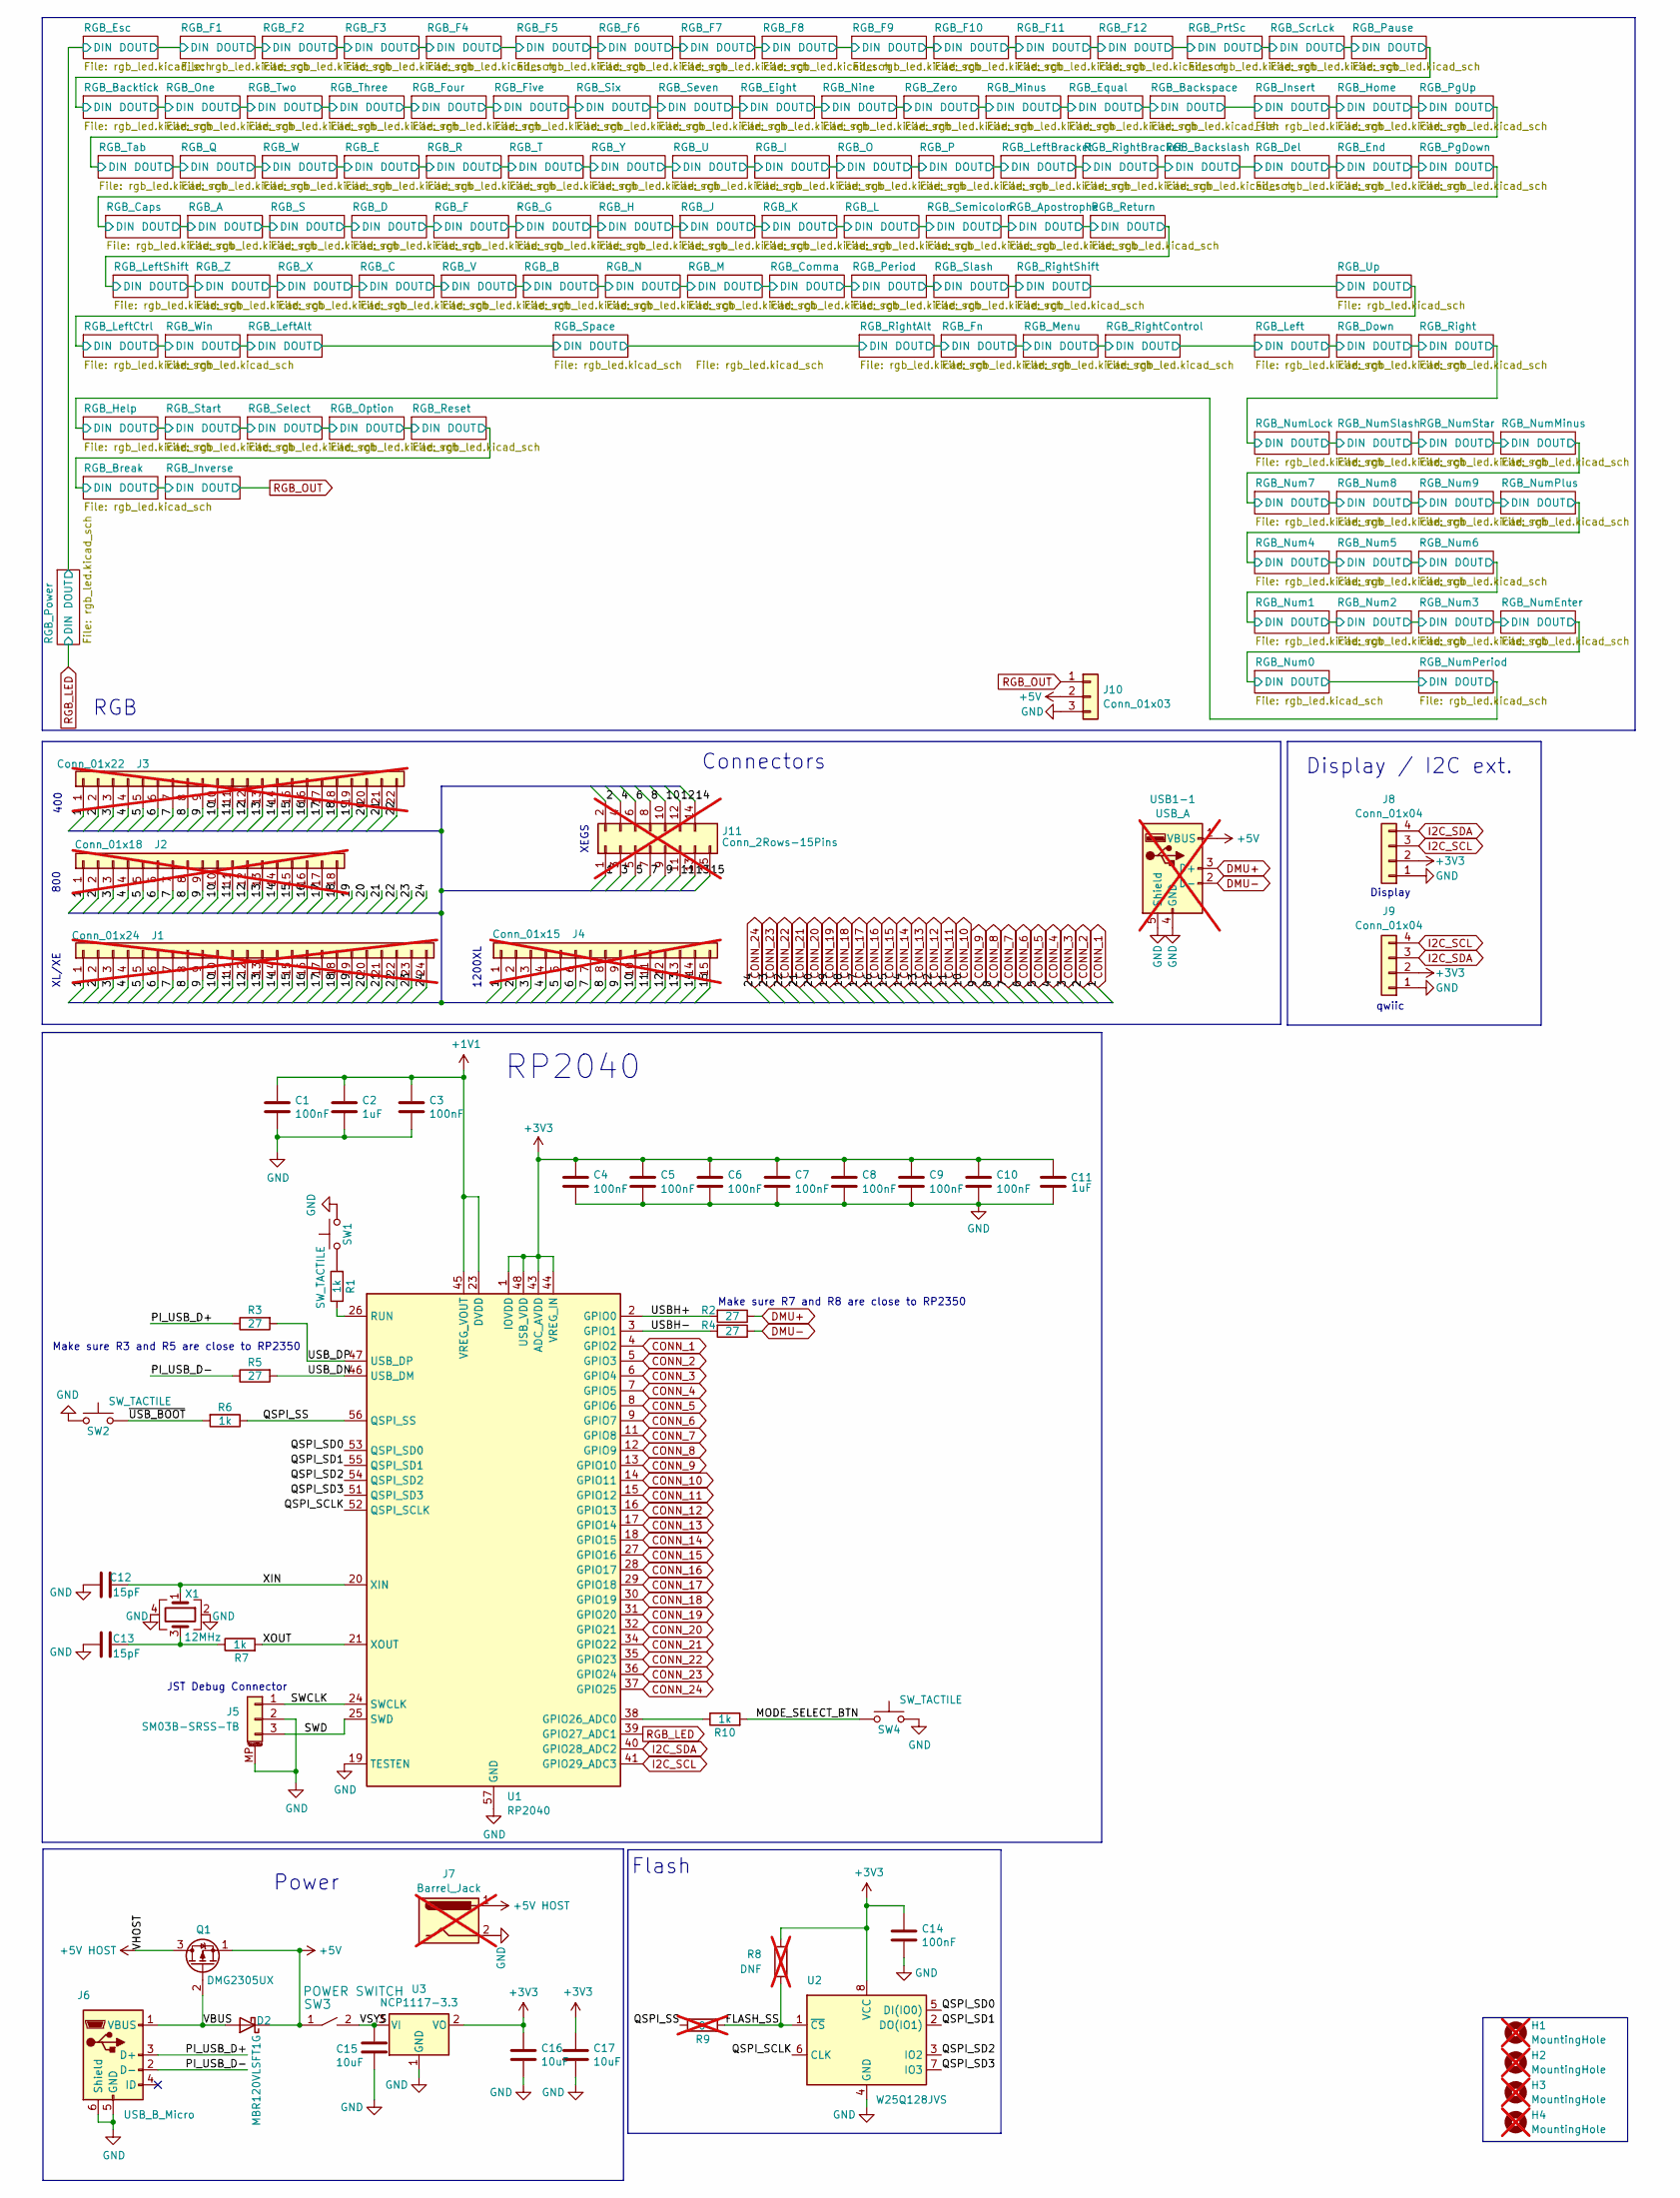
[picture p383: schematic DecentKeyboardTester.kicad_sch, Decent retro keyboard tester]

Parts:
C1, C3, C4, C5, C6, C7, C8, C9, C10, C14: 100nF; C_0402_1005Metric; JLCPCB Part # C1525
C2, C11: 1uF; C_0402_1005Metric; JLCPCB Part # C52923
C12, C13: 15pF; C_0402_1005Metric; JLCPCB Part # C1548
C15, C16, C17: 10uF; C_0402_1005Metric; JLCPCB Part # C15525
D2: MBR120VLSFT1G; Nexperia_CFP3_SOD-123W; JLCPCB Part # C8598
H1, H2, H3, H4: MountingHole; MountingHole_2.2mm_M2; not fitted
J1: Conn_01x24; PinSocket_1x24_P2.54mm_Vertical; not fitted
J2: Conn_01x18; PinSocket_1x18_P2.54mm_Vertical; not fitted
J3: Conn_01x22; PinSocket_1x22_P2.54mm_Vertical; not fitted
J4: Conn_01x15; PinSocket_1x15_P2.54mm_Vertical; not fitted
J5: SM03B-SRSS-TB; JST_SH_BM03B-SRSS-TB_1x03-1MP_P1.00mm_Vertical; JLCPCB Part # C160389
J6: USB_B_Micro; USB_Micro-AB_Molex_47590-0001; JLCPCB Part # C505111
J7: Barrel_Jack; BarrelJack_Horizontal; not fitted
J8: Conn_01x04; OLED_modeule_0_91_128x32_I2C
J9: Conn_01x04; JST_SH_SM04B-SRSS-TB_1x04-1MP_P1.00mm_Horizontal; JLCPCB Part # C160390
J10: Conn_01x03; JST_SH_SM03B-SRSS-TB_1x03-1MP_P1.00mm_Horizontal; JLCPCB Part # C160403
J11: Conn_2Rows-15Pins; DSUB-15_Male_Horizontal_P2.77x2.84mm_EdgePinOffset4.94mm_Ho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; not fitted
Q1: DMG2305UX; SOT-23; JLCPCB Part # C150470
R1, R6, R7, R10: 1k; R_0402_1005Metric; JLCPCB Part # C11702
R2, R3, R4, R5: 27; R_0805_2012Metric; JLCPCB Part # C17561
R8: DNF; R_0402_1005Metric; not fitted
R9: 0; SolderJumper-2_P1.3mm_Bridged_RoundedPad1.0x1.5mm; not fitted
SW1, SW2, SW4: SW_TACTILE; Tactile_Switch_Basic_XKB_TS-1187A; JLCPCB Part # C318884
SW3: POWER SWITCH; SW_SPDT_PCM12; JLCPCB Part # C431540
U1: RP2040; QFN-56-1EP_7x7mm_P0.4mm_EP3.2x3.2mm; JLCPCB Part # C2040
U2: W25Q128JVS; SOIC-8_5.23x5.23mm_P1.27mm; JLCPCB Part # C97521
U3: NCP1117-3.3; SOT-223-3_TabPin2; JLCPCB Part # C6186
USB1-1: USB_A; USB_A_Molex_67643_Horizontal; not fitted
X1: 12MHz; Crystal_SMD_Abracon_ABM8AIG-4Pin_3.2x2.5mm; JLCPCB Part # C9002

Connections:
+1V1: C1.1, C2.1, C3.1, U1.23 (DVDD), U1.45 (VREG_VOUT), U1.50 (DVDD)
+3V3: C4.1, C5.1, C6.1, C7.1, C8.1, C9.1, C10.1, C11.1, C14.1, C16.1, C17.1, J8.2, J9.2, R8.1, U1.1 (IOVDD), U1.10 (IOVDD), U1.22 (IOVDD), U1.33 (IOVDD), U1.42 (IOVDD), U1.43 (ADC_AVDD), U1.44 (VREG_IN), U1.48 (USB_VDD), U1.49 (IOVDD), U2.8 (VCC), U3.2 (VO)
+5V: D2.1 (K), J10.2, Q1.1 (S), SW3.1, USB1-1.1 (VBUS); also elsewhere on the board
+5V HOST: J7.1, Q1.3 (D)
/FLASH_SS: R8.2, R9.2, U2.1 (~CS)
/MODE_SELECT_BTN: R10.2, SW4.1
/PI_USB_D+: J6.3 (D+), R3.1
/PI_USB_D-: J6.2 (D-), R5.1
/QSPI_SCLK: U1.52 (QSPI_SCLK), U2.6 (CLK)
/QSPI_SD0: U1.53 (QSPI_SD0), U2.5 (DI(IO0))
/QSPI_SD1: U1.55 (QSPI_SD1), U2.2 (DO(IO1))
/QSPI_SD2: U1.54 (QSPI_SD2), U2.3 (IO2)
/QSPI_SD3: U1.51 (QSPI_SD3), U2.7 (IO3)
/QSPI_SS: R6.1, R9.1, U1.56 (QSPI_SS)
/SWCLK: J5.1, U1.24 (SWCLK)
/SWD: J5.3, U1.25 (SWD)
/USBH+: R2.2, U1.2 (GPIO0)
/USBH-: R4.2, U1.3 (GPIO1)
/USB_DN: R5.2, U1.46 (USB_DM)
/USB_DP: R3.2, U1.47 (USB_DP)
/VBUS: D2.2 (A), J6.1 (VBUS), Q1.2 (G)
/VSYS: C15.1, SW3.2, U3.3 (VI)
/XIN: C12.1, U1.20 (XIN), X1.1
/XOUT: R7.2, U1.21 (XOUT)
/~USB_BOOT: R6.2, SW2.2
CONN_1: J1.1, J2.1, J3.1, J4.1, J11.1, U1.4 (GPIO2)
CONN_2: J1.2, J2.2, J3.2, J4.2, J11.2, U1.5 (GPIO3)
CONN_3: J1.3, J2.3, J3.3, J4.3, J11.3, U1.6 (GPIO4)
CONN_4: J1.4, J2.4, J3.4, J4.4, J11.4, U1.7 (GPIO5)
CONN_5: J1.5, J2.5, J3.5, J4.5, J11.5, U1.8 (GPIO6)
CONN_6: J1.6, J2.6, J3.6, J4.6, J11.6, U1.9 (GPIO7)
CONN_7: J1.7, J2.7, J3.7, J4.7, J11.7, U1.11 (GPIO8)
CONN_8: J1.8, J2.8, J3.8, J4.8, J11.8, U1.12 (GPIO9)
CONN_9: J1.9, J2.9, J3.9, J4.9, J11.9, U1.13 (GPIO10)
CONN_10: J1.10, J2.10, J3.10, J4.10, J11.10, U1.14 (GPIO11)
CONN_11: J1.11, J2.11, J3.11, J4.11, J11.11, U1.15 (GPIO12)
CONN_12: J1.12, J2.12, J3.12, J4.12, J11.12, U1.16 (GPIO13)
CONN_13: J1.13, J2.13, J3.13, J4.13, J11.13, U1.17 (GPIO14)
CONN_14: J1.14, J2.14, J3.14, J4.14, J11.14, U1.18 (GPIO15)
CONN_15: J1.15, J2.15, J3.15, J4.15, J11.15, U1.27 (GPIO16)
CONN_16: J1.16, J2.16, J3.16, U1.28 (GPIO17)
CONN_17: J1.17, J2.17, J3.17, U1.29 (GPIO18)
CONN_18: J1.18, J2.18, J3.18, U1.30 (GPIO19)
CONN_19: J1.19, J3.19, U1.31 (GPIO20)
CONN_20: J1.20, J3.20, U1.32 (GPIO21)
CONN_21: J1.21, J3.21, U1.34 (GPIO22)
CONN_22: J1.22, J3.22, U1.35 (GPIO23)
CONN_23: J1.23, U1.36 (GPIO24)
CONN_24: J1.24, U1.37 (GPIO25)
DMU+: R2.1, USB1-1.3 (D+)
DMU-: R4.1, USB1-1.2 (D-)
GND: C1.2, C2.2, C3.2, C4.2, C5.2, C6.2, C7.2, C8.2, C9.2, C10.2, C11.2, C12.2, C13.1, C14.2, C15.2, C16.2, C17.2, J5.2, J5.MP (MountPin), J6.5 (GND), J6.6 (Shield), J7.2, J8.1, J9.1, J10.3, SW1.2, SW2.1, SW4.2, U1.19 (TESTEN), U1.57 (GND), U2.4 (GND), U3.1 (GND), USB1-1.4 (GND), USB1-1.5 (Shield), X1.2, X1.4; also elsewhere on the board
I2C_SCL: J8.3, J9.4, U1.41 (GPIO29_ADC3)
I2C_SDA: J8.4, J9.3, U1.40 (GPIO28_ADC2)
unnamed: C13.2, R7.1, X1.3
unnamed: R1.2, SW1.1
unnamed: R10.1, U1.38 (GPIO26_ADC0)
unnamed: R1.1, U1.26 (RUN)
RGB_LED: U1.39 (GPIO27_ADC1); also elsewhere on the board
RGB_OUT: J10.1; also elsewhere on the board

Notes on the sheet:
RP2040
XEGS
Display / I2C ext.
Display
400
800
Flash
qwiic
RGB
JST Debug Connector
Connectors
XL/XE
1200XL
Power
Make sure R3 and R5 are close to RP2350
Make sure R7 and R8 are close to RP2350

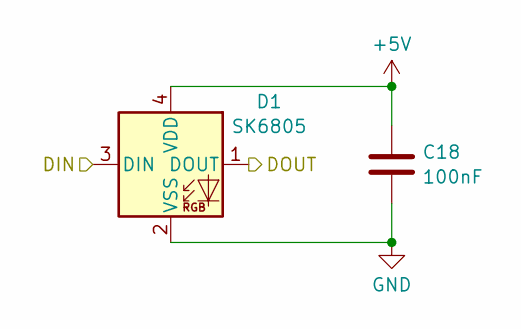
[picture p384: schematic rgb_led.kicad_sch, Individual RGB LED]

Parts:
C18: 100nF; C_0402_1005Metric; JLCPCB Part # C1525
D1: SK6805; SK6809-EC15; JLCPCB Part # C2909055

Connections:
+5V: C18.1, D1.4 (VDD); also elsewhere on the board
/RGB_Esc/DOUT: D1.3 (DIN); also elsewhere on the board
/RGB_F1/DOUT: D1.1 (DOUT); also elsewhere on the board
GND: C18.2, D1.2 (VSS); also elsewhere on the board

Parts of its further copies:
C19, C20, C21, C22, C23, C24, C25, C26, C27, C28, C29, C30, C31, C32, C33, C34, C35, C36, C37, C38, C39, C40, C41, C42, C43, C44, C45, C46, C47, C48, C49, C50, C51, C52, C53, C54, C55, C56, C57, C58, C59, C60, C61, C62, C63, C64, C65, C66, C67, C68, C69, C70, C71, C72, C73, C74, C75, C76, C77, C78, C79, C80, C81, C82, C83, C84, C85, C86, C87, C88, C89, C90, C91, C92, C93, C94, C95, C96, C97, C98, C99, C100, C101, C102, C103, C104, C105, C106, C107, C108, C109, C110, C111, C112, C113, C114, C115, C116, C117, C118, C119, C120, C121, C122, C123, C124, C125, C126, C127, C128, C129: 100nF; C_0402_1005Metric; JLCPCB Part # C1525
D3, D4, D5, D6, D7, D8, D9, D10, D11, D12, D13, D14, D15, D16, D17, D18, D19, D20, D21, D22, D23, D24, D25, D26, D27, D28, D29, D30, D31, D32, D33, D34, D35, D36, D37, D38, D39, D40, D41, D42, D43, D44, D45, D46, D47, D48, D49, D50, D51, D52, D53, D54, D55, D56, D57, D58, D59, D60, D61, D62, D63, D64, D65, D66, D67, D68, D69, D70, D71, D72, D73, D74, D75, D76, D77, D78, D79, D80, D81, D82, D83, D84, D85, D86, D87, D88, D89, D90, D91, D92, D93, D94, D95, D96, D97, D98, D99, D100, D101, D102, D103, D104, D105, D106, D107, D108, D109, D110, D111, D112, D113: SK6805; SK6809-EC15; JLCPCB Part # C2909055

Connections of its further copies:
+5V: C19.1, C20.1, C21.1, C22.1, C23.1, C24.1, C25.1, C26.1, C27.1, C28.1, C29.1, C30.1, C31.1, C32.1, C33.1, C34.1, C35.1, C36.1, C37.1, C38.1, C39.1, C40.1, C41.1, C42.1, C43.1, C44.1, C45.1, C46.1, C47.1, C48.1, C49.1, C50.1, C51.1, C52.1, C53.1, C54.1, C55.1, C56.1, C57.1, C58.1, C59.1, C60.1, C61.1, C62.1, C63.1, C64.1, C65.1, C66.1, C67.1, C68.1, C69.1, C70.1, C71.1, C72.1, C73.1, C74.1, C75.1, C76.1, C77.1, C78.1, C79.1, C80.1, C81.1, C82.1, C83.1, C84.1, C85.1, C86.1, C87.1, C88.1, C89.1, C90.1, C91.1, C92.1, C93.1, C94.1, C95.1, C96.1, C97.1, C98.1, C99.1, C100.1, C101.1, C102.1, C103.1, C104.1, C105.1, C106.1, C107.1, C108.1, C109.1, C110.1, C111.1, C112.1, C113.1, C114.1, C115.1, C116.1, C117.1, C118.1, C119.1, C120.1, C121.1, C122.1, C123.1, C124.1, C125.1, C126.1, C127.1, C128.1, C129.1, D3.4 (VDD), D4.4 (VDD), D5.4 (VDD), D6.4 (VDD), D7.4 (VDD), D8.4 (VDD), D9.4 (VDD), D10.4 (VDD), D11.4 (VDD), D12.4 (VDD), D13.4 (VDD), D14.4 (VDD), D15.4 (VDD), D16.4 (VDD), D17.4 (VDD), D18.4 (VDD), D19.4 (VDD), D20.4 (VDD), D21.4 (VDD), D22.4 (VDD), D23.4 (VDD), D24.4 (VDD), D25.4 (VDD), D26.4 (VDD), D27.4 (VDD), D28.4 (VDD), D29.4 (VDD), D30.4 (VDD), D31.4 (VDD), D32.4 (VDD), D33.4 (VDD), D34.4 (VDD), D35.4 (VDD), D36.4 (VDD), D37.4 (VDD), D38.4 (VDD), D39.4 (VDD), D40.4 (VDD), D41.4 (VDD), D42.4 (VDD), D43.4 (VDD), D44.4 (VDD), D45.4 (VDD), D46.4 (VDD), D47.4 (VDD), D48.4 (VDD), D49.4 (VDD), D50.4 (VDD), D51.4 (VDD), D52.4 (VDD), D53.4 (VDD), D54.4 (VDD), D55.4 (VDD), D56.4 (VDD), D57.4 (VDD), D58.4 (VDD), D59.4 (VDD), D60.4 (VDD), D61.4 (VDD), D62.4 (VDD), D63.4 (VDD), D64.4 (VDD), D65.4 (VDD), D66.4 (VDD), D67.4 (VDD), D68.4 (VDD), D69.4 (VDD), D70.4 (VDD), D71.4 (VDD), D72.4 (VDD), D73.4 (VDD), D74.4 (VDD), D75.4 (VDD), D76.4 (VDD), D77.4 (VDD), D78.4 (VDD), D79.4 (VDD), D80.4 (VDD), D81.4 (VDD), D82.4 (VDD), D83.4 (VDD), D84.4 (VDD), D85.4 (VDD), D86.4 (VDD), D87.4 (VDD), D88.4 (VDD), D89.4 (VDD), D90.4 (VDD), D91.4 (VDD), D92.4 (VDD), D93.4 (VDD), D94.4 (VDD), D95.4 (VDD), D96.4 (VDD), D97.4 (VDD), D98.4 (VDD), D99.4 (VDD), D100.4 (VDD), D101.4 (VDD), D102.4 (VDD), D103.4 (VDD), D104.4 (VDD), D105.4 (VDD), D106.4 (VDD), D107.4 (VDD), D108.4 (VDD), D109.4 (VDD), D110.4 (VDD), D111.4 (VDD), D112.4 (VDD), D113.4 (VDD); also elsewhere on the board
/RGB_A/DIN: D57.3 (DIN), D61.1 (DOUT)
/RGB_A/DOUT: D57.1 (DOUT), D63.3 (DIN)
/RGB_Apostrophe/DIN: D54.3 (DIN), D56.1 (DOUT)
/RGB_Apostrophe/DOUT: D54.1 (DOUT), D59.3 (DIN)
/RGB_B/DIN: D69.1 (DOUT), D70.3 (DIN)
/RGB_B/DOUT: D70.1 (DOUT), D71.3 (DIN)
/RGB_Backslash/DIN: D35.3 (DIN), D38.1 (DOUT)
/RGB_Backslash/DOUT: D35.1 (DOUT), D42.3 (DIN)
/RGB_Backspace/DIN: D30.1 (DOUT), D31.3 (DIN)
/RGB_Backspace/DOUT: D31.1 (DOUT), D32.3 (DIN)
/RGB_Backtick/DIN: D17.1 (DOUT), D18.3 (DIN)
/RGB_Backtick/DOUT: D18.1 (DOUT), D19.3 (DIN)
/RGB_Break/DIN: D110.1 (DOUT), D112.3 (DIN)
/RGB_Break/DOUT: D111.3 (DIN), D112.1 (DOUT)
/RGB_C/DIN: D68.3 (DIN), D76.1 (DOUT)
/RGB_C/DOUT: D68.1 (DOUT), D69.3 (DIN)
/RGB_Caps/DIN: D46.1 (DOUT), D61.3 (DIN)
/RGB_Comma/DIN: D72.1 (DOUT), D73.3 (DIN)
/RGB_Comma/DOUT: D73.1 (DOUT), D74.3 (DIN)
/RGB_D/DIN: D52.3 (DIN), D63.1 (DOUT)
/RGB_D/DOUT: D52.1 (DOUT), D58.3 (DIN)
/RGB_Del/DOUT: D41.3 (DIN), D42.1 (DOUT)
/RGB_Down/DIN: D85.3 (DIN), D86.1 (DOUT)
/RGB_Down/DOUT: D85.1 (DOUT), D87.3 (DIN)
/RGB_E/DIN: D49.3 (DIN), D50.1 (DOUT)
/RGB_E/DOUT: D40.3 (DIN), D49.1 (DOUT)
/RGB_Eight/DIN: D25.1 (DOUT), D26.3 (DIN)
/RGB_Eight/DOUT: D26.1 (DOUT), D27.3 (DIN)
/RGB_End/DOUT: D41.1 (DOUT), D46.3 (DIN)
/RGB_Equal/DIN: D29.1 (DOUT), D30.3 (DIN)
/RGB_Esc/DIN: D14.3 (DIN), D113.1 (DOUT)
/RGB_Esc/DOUT: D14.1 (DOUT); also elsewhere on the board
/RGB_F1/DOUT: D3.3 (DIN); also elsewhere on the board
/RGB_F2/DOUT: D3.1 (DOUT), D4.3 (DIN)
/RGB_F3/DOUT: D4.1 (DOUT), D5.3 (DIN)
/RGB_F4/DOUT: D5.1 (DOUT), D6.3 (DIN)
/RGB_F5/DOUT: D6.1 (DOUT), D7.3 (DIN)
/RGB_F6/DOUT: D7.1 (DOUT), D8.3 (DIN)
/RGB_F7/DOUT: D8.1 (DOUT), D9.3 (DIN)
/RGB_F8/DOUT: D9.1 (DOUT), D10.3 (DIN)
/RGB_F10/DIN: D10.1 (DOUT), D11.3 (DIN)
/RGB_F10/DOUT: D11.1 (DOUT), D12.3 (DIN)
/RGB_F11/DOUT: D12.1 (DOUT), D13.3 (DIN)
/RGB_F12/DOUT: D13.1 (DOUT), D15.3 (DIN)
/RGB_F/DOUT: D58.1 (DOUT), D60.3 (DIN)
/RGB_Five/DIN: D22.1 (DOUT), D23.3 (DIN)
/RGB_Five/DOUT: D23.1 (DOUT), D24.3 (DIN)
/RGB_Fn/DIN: D78.3 (DIN), D88.1 (DOUT)
/RGB_Fn/DOUT: D78.1 (DOUT), D83.3 (DIN)
/RGB_Four/DIN: D21.1 (DOUT), D22.3 (DIN)
/RGB_G/DOUT: D60.1 (DOUT), D64.3 (DIN)
/RGB_H/DOUT: D62.3 (DIN), D64.1 (DOUT)
/RGB_Help/DIN: D105.1 (DOUT), D106.3 (DIN)
/RGB_Help/DOUT: D106.1 (DOUT), D107.3 (DIN)
/RGB_Home/DIN: D32.1 (DOUT), D33.3 (DIN)
/RGB_Home/DOUT: D33.1 (DOUT), D34.3 (DIN)
/RGB_I/DIN: D37.3 (DIN), D47.1 (DOUT)
/RGB_I/DOUT: D37.1 (DOUT), D44.3 (DIN)
/RGB_J/DOUT: D53.3 (DIN), D62.1 (DOUT)
/RGB_K/DOUT: D53.1 (DOUT), D55.3 (DIN)
/RGB_L/DOUT: D55.1 (DOUT), D56.3 (DIN)
/RGB_Left/DIN: D82.1 (DOUT), D86.3 (DIN)
/RGB_LeftAlt/DIN: D89.3 (DIN), D90.1 (DOUT)
/RGB_LeftAlt/DOUT: D79.3 (DIN), D89.1 (DOUT)
/RGB_LeftBracket/DIN: D43.3 (DIN), D51.1 (DOUT)
/RGB_LeftBracket/DOUT: D38.3 (DIN), D43.1 (DOUT)
/RGB_LeftCtrl/DIN: D75.1 (DOUT), D81.3 (DIN)
/RGB_LeftCtrl/DOUT: D81.1 (DOUT), D90.3 (DIN)
/RGB_LeftShift/DIN: D59.1 (DOUT), D67.3 (DIN)
/RGB_LeftShift/DOUT: D65.3 (DIN), D67.1 (DOUT)
/RGB_M/DIN: D71.1 (DOUT), D72.3 (DIN)
/RGB_Menu/DOUT: D82.3 (DIN), D83.1 (DOUT)
/RGB_Minus/DIN: D28.1 (DOUT), D29.3 (DIN)
/RGB_Nine/DOUT: D27.1 (DOUT), D28.3 (DIN)
/RGB_Num0/DIN: D103.1 (DOUT), D104.3 (DIN)
/RGB_Num0/DOUT: D104.1 (DOUT), D105.3 (DIN)
/RGB_Num1/DIN: D99.1 (DOUT), D100.3 (DIN)
/RGB_Num1/DOUT: D100.1 (DOUT), D101.3 (DIN)
/RGB_Num2/DOUT: D101.1 (DOUT), D102.3 (DIN)
/RGB_Num3/DOUT: D102.1 (DOUT), D103.3 (DIN)
/RGB_Num4/DIN: D96.1 (DOUT), D97.3 (DIN)
/RGB_Num4/DOUT: D97.1 (DOUT), D98.3 (DIN)
/RGB_Num5/DOUT: D98.1 (DOUT), D99.3 (DIN)
/RGB_Num7/DIN: D92.1 (DOUT), D93.3 (DIN)
/RGB_Num7/DOUT: D93.1 (DOUT), D95.3 (DIN)
/RGB_Num8/DOUT: D94.3 (DIN), D95.1 (DOUT)
/RGB_Num9/DOUT: D94.1 (DOUT), D96.3 (DIN)
/RGB_NumLock/DIN: D80.3 (DIN), D87.1 (DOUT)
/RGB_NumLock/DOUT: D80.1 (DOUT), D84.3 (DIN)
/RGB_NumMinus/DIN: D91.1 (DOUT), D92.3 (DIN)
/RGB_NumSlash/DOUT: D84.1 (DOUT), D91.3 (DIN)
/RGB_O/DOUT: D44.1 (DOUT), D51.3 (DIN)
/RGB_One/DOUT: D19.1 (DOUT), D20.3 (DIN)
/RGB_Option/DIN: D108.1 (DOUT), D109.3 (DIN)
/RGB_Option/DOUT: D109.1 (DOUT), D110.3 (DIN)
/RGB_Pause/DIN: D16.1 (DOUT), D17.3 (DIN)
/RGB_Period/DOUT: D74.1 (DOUT), D77.3 (DIN)
/RGB_PgUp/DOUT: D34.1 (DOUT), D36.3 (DIN)
/RGB_PrtSc/DOUT: D15.1 (DOUT), D16.3 (DIN)
/RGB_Q/DIN: D36.1 (DOUT), D45.3 (DIN)
/RGB_Q/DOUT: D45.1 (DOUT), D50.3 (DIN)
/RGB_R/DOUT: D39.3 (DIN), D40.1 (DOUT)
/RGB_RightAlt/DIN: D79.1 (DOUT), D88.3 (DIN)
/RGB_RightShift/DIN: D66.3 (DIN), D77.1 (DOUT)
/RGB_RightShift/DOUT: D66.1 (DOUT), D75.3 (DIN)
/RGB_Select/DIN: D107.1 (DOUT), D108.3 (DIN)
/RGB_Seven/DIN: D24.1 (DOUT), D25.3 (DIN)
/RGB_T/DOUT: D39.1 (DOUT), D48.3 (DIN)
/RGB_Three/DIN: D20.1 (DOUT), D21.3 (DIN)
/RGB_U/DIN: D47.3 (DIN), D48.1 (DOUT)
/RGB_X/DIN: D65.1 (DOUT), D76.3 (DIN)
GND: C19.2, C20.2, C21.2, C22.2, C23.2, C24.2, C25.2, C26.2, C27.2, C28.2, C29.2, C30.2, C31.2, C32.2, C33.2, C34.2, C35.2, C36.2, C37.2, C38.2, C39.2, C40.2, C41.2, C42.2, C43.2, C44.2, C45.2, C46.2, C47.2, C48.2, C49.2, C50.2, C51.2, C52.2, C53.2, C54.2, C55.2, C56.2, C57.2, C58.2, C59.2, C60.2, C61.2, C62.2, C63.2, C64.2, C65.2, C66.2, C67.2, C68.2, C69.2, C70.2, C71.2, C72.2, C73.2, C74.2, C75.2, C76.2, C77.2, C78.2, C79.2, C80.2, C81.2, C82.2, C83.2, C84.2, C85.2, C86.2, C87.2, C88.2, C89.2, C90.2, C91.2, C92.2, C93.2, C94.2, C95.2, C96.2, C97.2, C98.2, C99.2, C100.2, C101.2, C102.2, C103.2, C104.2, C105.2, C106.2, C107.2, C108.2, C109.2, C110.2, C111.2, C112.2, C113.2, C114.2, C115.2, C116.2, C117.2, C118.2, C119.2, C120.2, C121.2, C122.2, C123.2, C124.2, C125.2, C126.2, C127.2, C128.2, C129.2, D3.2 (VSS), D4.2 (VSS), D5.2 (VSS), D6.2 (VSS), D7.2 (VSS), D8.2 (VSS), D9.2 (VSS), D10.2 (VSS), D11.2 (VSS), D12.2 (VSS), D13.2 (VSS), D14.2 (VSS), D15.2 (VSS), D16.2 (VSS), D17.2 (VSS), D18.2 (VSS), D19.2 (VSS), D20.2 (VSS), D21.2 (VSS), D22.2 (VSS), D23.2 (VSS), D24.2 (VSS), D25.2 (VSS), D26.2 (VSS), D27.2 (VSS), D28.2 (VSS), D29.2 (VSS), D30.2 (VSS), D31.2 (VSS), D32.2 (VSS), D33.2 (VSS), D34.2 (VSS), D35.2 (VSS), D36.2 (VSS), D37.2 (VSS), D38.2 (VSS), D39.2 (VSS), D40.2 (VSS), D41.2 (VSS), D42.2 (VSS), D43.2 (VSS), D44.2 (VSS), D45.2 (VSS), D46.2 (VSS), D47.2 (VSS), D48.2 (VSS), D49.2 (VSS), D50.2 (VSS), D51.2 (VSS), D52.2 (VSS), D53.2 (VSS), D54.2 (VSS), D55.2 (VSS), D56.2 (VSS), D57.2 (VSS), D58.2 (VSS), D59.2 (VSS), D60.2 (VSS), D61.2 (VSS), D62.2 (VSS), D63.2 (VSS), D64.2 (VSS), D65.2 (VSS), D66.2 (VSS), D67.2 (VSS), D68.2 (VSS), D69.2 (VSS), D70.2 (VSS), D71.2 (VSS), D72.2 (VSS), D73.2 (VSS), D74.2 (VSS), D75.2 (VSS), D76.2 (VSS), D77.2 (VSS), D78.2 (VSS), D79.2 (VSS), D80.2 (VSS), D81.2 (VSS), D82.2 (VSS), D83.2 (VSS), D84.2 (VSS), D85.2 (VSS), D86.2 (VSS), D87.2 (VSS), D88.2 (VSS), D89.2 (VSS), D90.2 (VSS), D91.2 (VSS), D92.2 (VSS), D93.2 (VSS), D94.2 (VSS), D95.2 (VSS), D96.2 (VSS), D97.2 (VSS), D98.2 (VSS), D99.2 (VSS), D100.2 (VSS), D101.2 (VSS), D102.2 (VSS), D103.2 (VSS), D104.2 (VSS), D105.2 (VSS), D106.2 (VSS), D107.2 (VSS), D108.2 (VSS), D109.2 (VSS), D110.2 (VSS), D111.2 (VSS), D112.2 (VSS), D113.2 (VSS); also elsewhere on the board
RGB_LED: D113.3 (DIN); also elsewhere on the board
RGB_OUT: D111.1 (DOUT); also elsewhere on the board

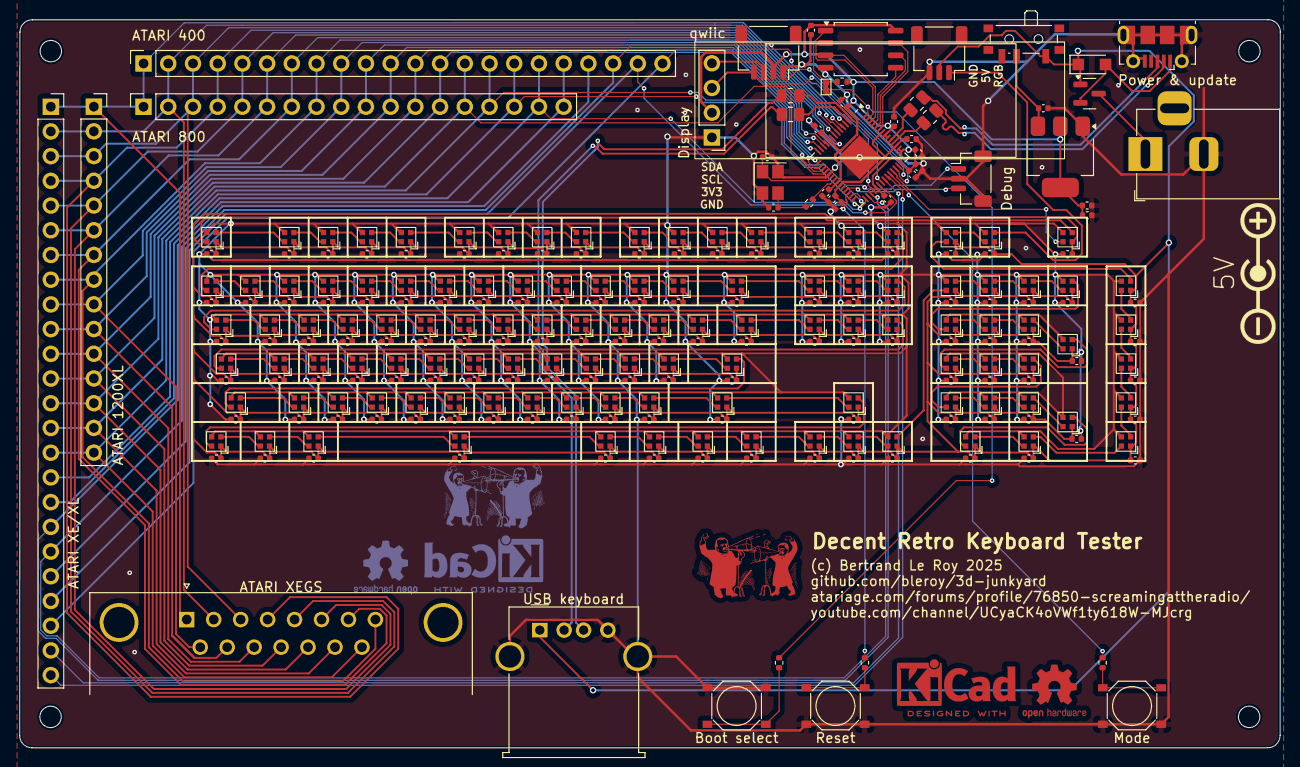
[picture p385: board DecentKeyboardTester.kicad_pcb from above]

Board: 2 copper layers, 129.6 x 74.8 mm, 277 parts (0 on the bottom side), 171 nets.
