bleroy/3d-junkyard/misc-models/Atari/S-Video/S-Video.kicad_pcb

## KiCad design misc-models/Atari/S-Video/S-Video.kicad_pcb (2025-01-17)

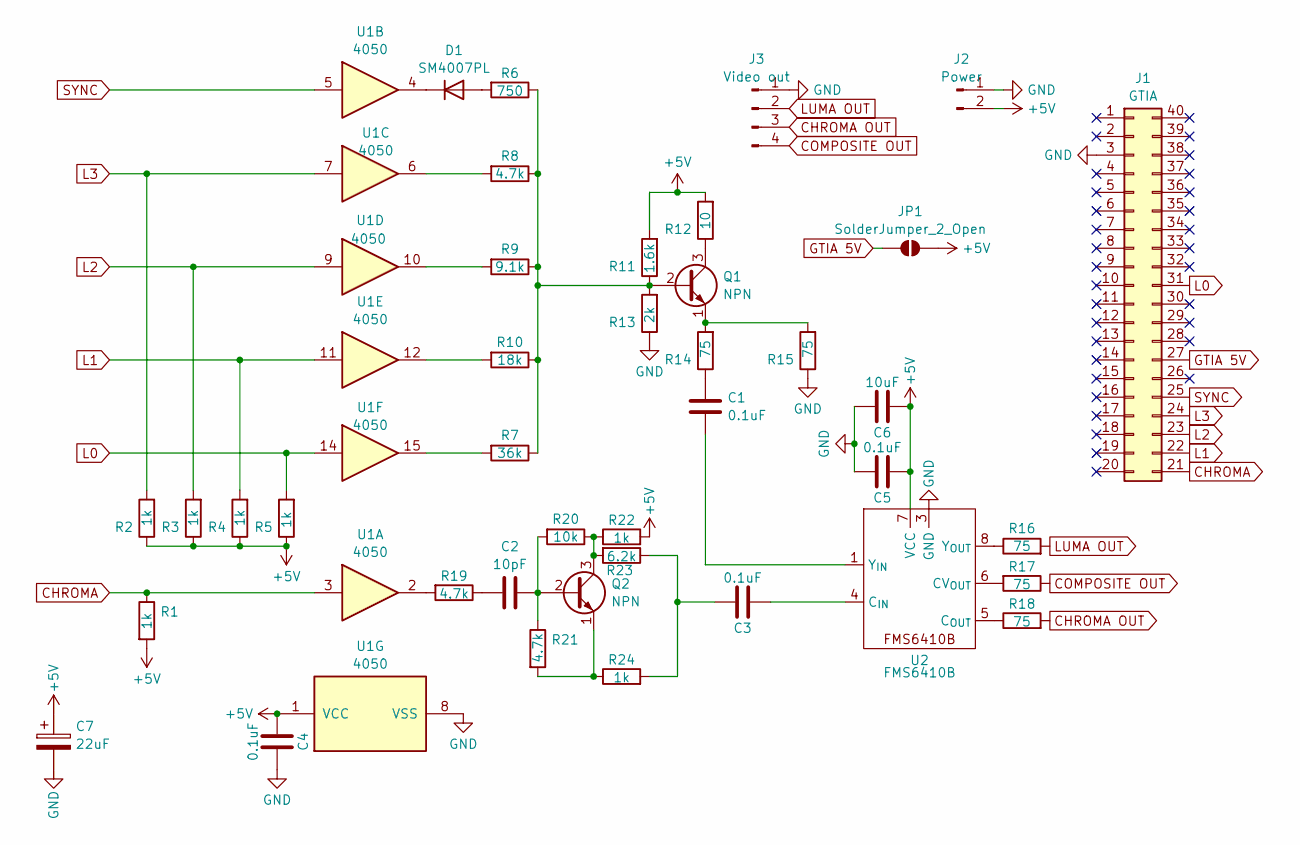
[picture p386: schematic S-Video.kicad_sch, S-video Atari mod]

Parts:
C1, C3, C4, C5: 0.1uF; C_0402_1005Metric; JLCPCB Part # C1525
C2: 10pF; C_0402_1005Metric; JLCPCB Part # C32949
C6: 10uF; C_0402_1005Metric; JLCPCB Part # C15525
C7: 22uF; C_Elec_4x5.4; JLCPCB Part # C98746
D1: SM4007PL; D_SOD-123; JLCPCB Part # C64898
J1: GTIA; DIP-40_W15.24mm_Socket
J2: Power; PinHeader_1x02_P2.54mm_Horizontal
J3: Video out; PinHeader_1x04_P2.54mm_Horizontal
JP1: SolderJumper_2_Open; SolderJumper-2_P1.3mm_Open_TrianglePad1.0x1.5mm
Q1, Q2: NPN; SOT-23; JLCPCB Part # C2145
R1, R2, R3, R4, R5, R22, R24: 1k; R_0402_1005Metric; JLCPCB Part # C11702
R6: 750; R_0402_1005Metric; JLCPCB Part # C25132
R7: 36k; R_0402_1005Metric; JLCPCB Part # C43676
R8, R19, R21: 4.7k; R_0402_1005Metric; JLCPCB Part # C25900
R9: 9.1k; R_0402_1005Metric; JLCPCB Part # C25926
R10: 18k; R_0402_1005Metric; JLCPCB Part # C25762
R11: 1.6k; R_0402_1005Metric; JLCPCB Part # C4908
R12: 10; R_0402_1005Metric; JLCPCB Part # C25077
R13: 2k; R_0402_1005Metric; JLCPCB Part # C4109
R14, R15, R16, R17, R18: 75; R_0402_1005Metric; JLCPCB Part # C25133
R20: 10k; R_0402_1005Metric; JLCPCB Part # C25744
R23: 6.2k; R_0402_1005Metric; JLCPCB Part # C137946
U1: 4050; SOIC-16_3.9x9.9mm_P1.27mm; JLCPCB Part # C131932
U2: FMS6410B; SOIC-8-1EP_3.9x4.9mm_P1.27mm_EP2.29x3mm; JLCPCB Part # C3823926

Connections:
+5V: C4.1, C5.1, C6.1, C7.1, J2.2, JP1.2 (B), R1.2, R2.1, R3.1, R4.1, R5.1, R11.2, R12.2, R22.2, U1.1 (VCC), U2.7 (VCC)
CHROMA: J1.21, R1.1, U1.3
CHROMA OUT: J3.3, R18.2
COMPOSITE OUT: J3.4, R17.1
GND: C4.2, C5.2, C6.2, C7.2, J1.3, J2.1, J3.1, R13.1, R15.1, U1.8 (VSS), U2.3 (GND)
GTIA 5V: J1.27, JP1.1 (A)
L0: J1.31, R5.2, U1.14
L1: J1.22, R4.2, U1.11
L2: J1.23, R3.2, U1.9
L3: J1.24, R2.2, U1.7
LUMA OUT: J3.2, R16.2
unnamed: C1.2, R14.1
unnamed: C2.2, R19.1
unnamed: C3.2, R23.1, R24.2
unnamed: D1.2 (A), R6.2
unnamed: D1.1 (K), U1.4
unnamed: Q1.2 (B), R6.1, R7.1, R8.1, R9.1, R10.1, R11.1, R13.2
unnamed: Q1.3 (C), R12.1
unnamed: Q1.1 (E), R14.2, R15.2
unnamed: C2.1, Q2.2 (B), R20.2, R21.1
unnamed: Q2.3 (C), R20.1, R22.1, R23.2
unnamed: Q2.1 (E), R21.2, R24.1
unnamed: R7.2, U1.15
unnamed: R8.2, U1.6
unnamed: R9.2, U1.10
unnamed: R10.2, U1.12
unnamed: R19.2, U1.2
unnamed: R17.2, U2.6 (CV_{OUT})
unnamed: C3.1, U2.4 (C_{IN})
unnamed: R18.1, U2.5 (C_{OUT})
unnamed: C1.1, U2.1 (Y_{IN})
unnamed: R16.1, U2.8 (Y_{OUT})
SYNC: J1.25, U1.5

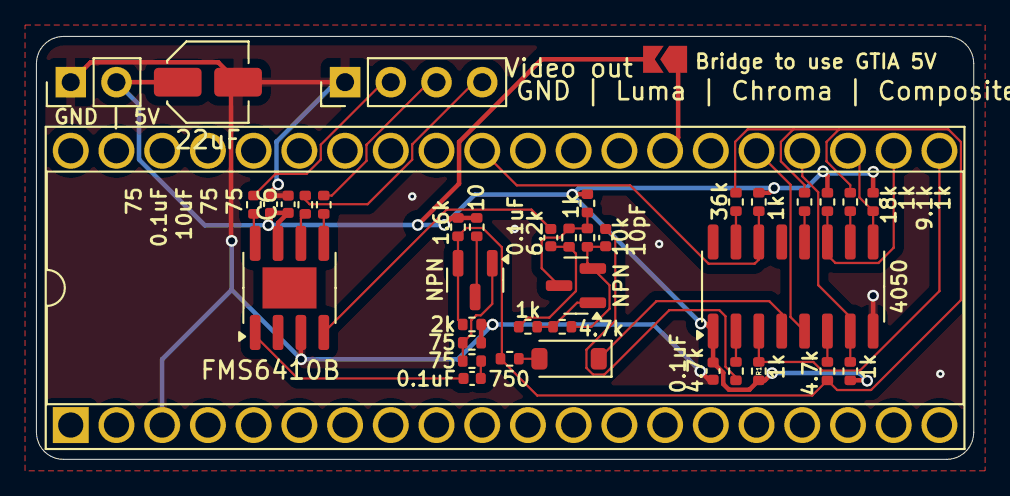
[picture p387: board S-Video.kicad_pcb from above]

Board: 2 copper layers, 52.1 x 23.5 mm, 40 parts (0 on the bottom side), 33 nets.
