bleroy/3d-junkyard/misc-models/Atari/PBI-breakout/PBI-breakout.kicad_pcb

## KiCad design misc-models/Atari/PBI-breakout/PBI-breakout.kicad_pcb (2025-01-11)

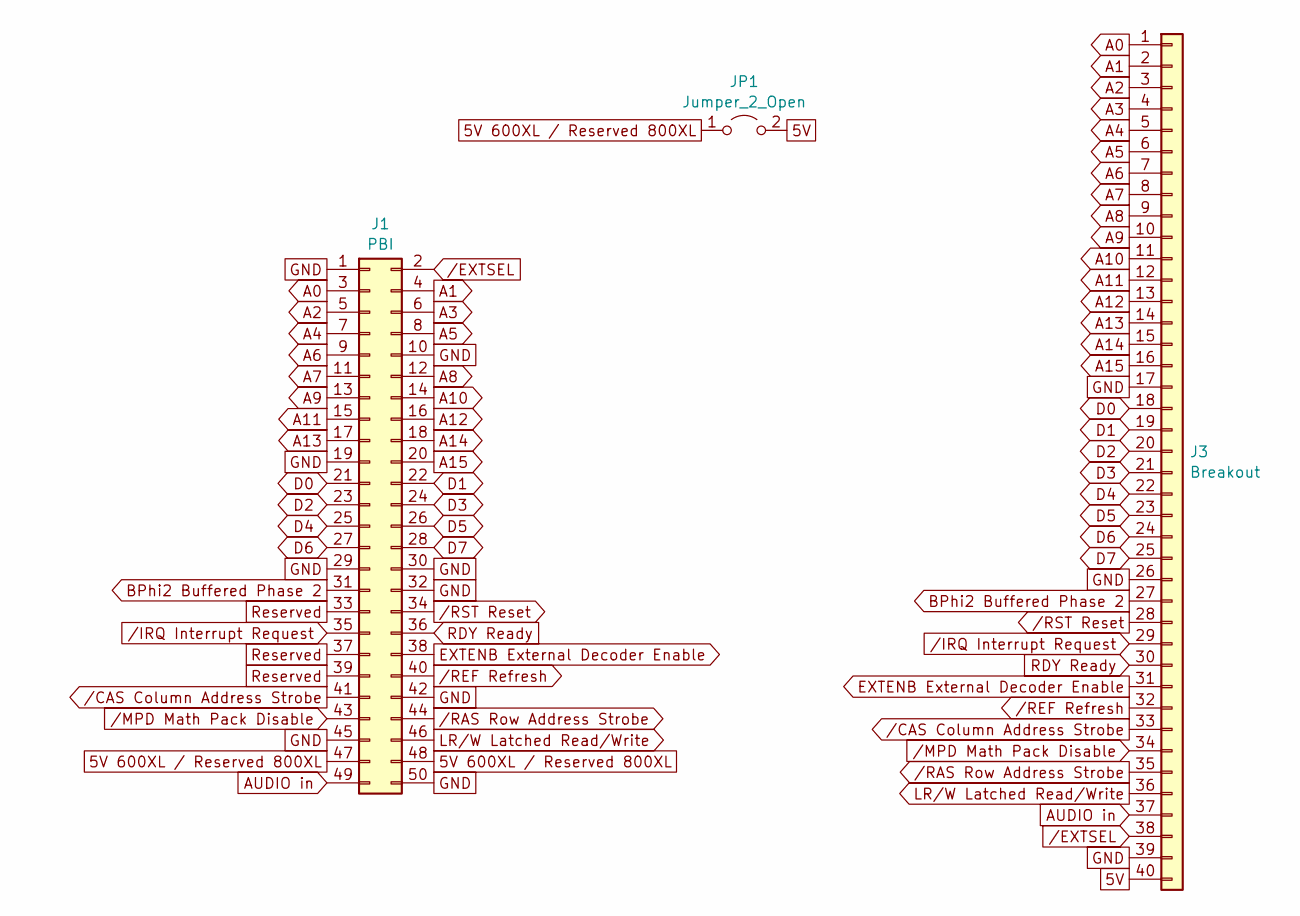
[picture p388: schematic PBI-breakout.kicad_sch, PBI breakout board]

Parts:
J1: PBI; PBI Edge Connector
J3: Breakout; PinHeader_1x40_P2.54mm_Horizontal
JP1: Jumper_2_Open; PinHeader_1x02_P2.54mm_Vertical

Connections:
5V: J3.40, JP1.2 (B)
5V 600XL / Reserved 800XL: J1.47, J1.48, JP1.1 (A)
A0: J1.3, J3.1
A1: J1.4, J3.2
A2: J1.5, J3.3
A3: J1.6, J3.4
A4: J1.7, J3.5
A5: J1.8, J3.6
A6: J1.9, J3.7
A7: J1.11, J3.8
A8: J1.12, J3.9
A9: J1.13, J3.10
A10: J1.14, J3.11
A11: J1.15, J3.12
A12: J1.16, J3.13
A13: J1.17, J3.14
A14: J1.18, J3.15
A15: J1.20, J3.16
AUDIO in: J1.49, J3.37
BPhi2 Buffered Phase 2: J1.31, J3.27
D0: J1.21, J3.18
D1: J1.22, J3.19
D2: J1.23, J3.20
D3: J1.24, J3.21
D4: J1.25, J3.22
D5: J1.26, J3.23
D6: J1.27, J3.24
D7: J1.28, J3.25
EXTENB External Decoder Enable: J1.38, J3.31
GND: J1.1, J1.10, J1.19, J1.29, J1.30, J1.32, J1.42, J1.45, J1.50, J3.17, J3.26, J3.39
LR/W Latched Read/Write: J1.46, J3.36
RDY Ready: J1.36, J3.30
Reserved: J1.33, J1.37, J1.39
/CAS Column Address Strobe: J1.41, J3.33
/EXTSEL: J1.2, J3.38
/IRQ Interrupt Request: J1.35, J3.29
/MPD Math Pack Disable: J1.43, J3.34
/RAS Row Address Strobe: J1.44, J3.35
/REF Refresh: J1.40, J3.32
/RST Reset: J1.34, J3.28

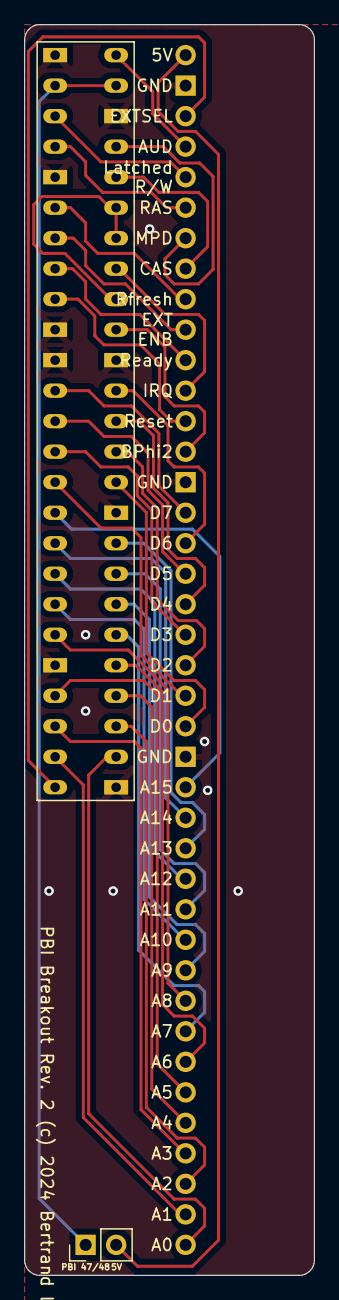
[picture p389: board PBI-breakout.kicad_pcb from above]

Board: 2 copper layers, 24.1 x 104.1 mm, 3 parts (1 on the bottom side), 40 nets.
