bleroy/3d-junkyard/misc-models/Atari/CartConnectorAdapter1200XL/CartConnectorAdapter1200XL.kicad_pcb

## KiCad design misc-models/Atari/CartConnectorAdapter1200XL/CartConnectorAdapter1200XL.kicad_pcb (2024-10-20)

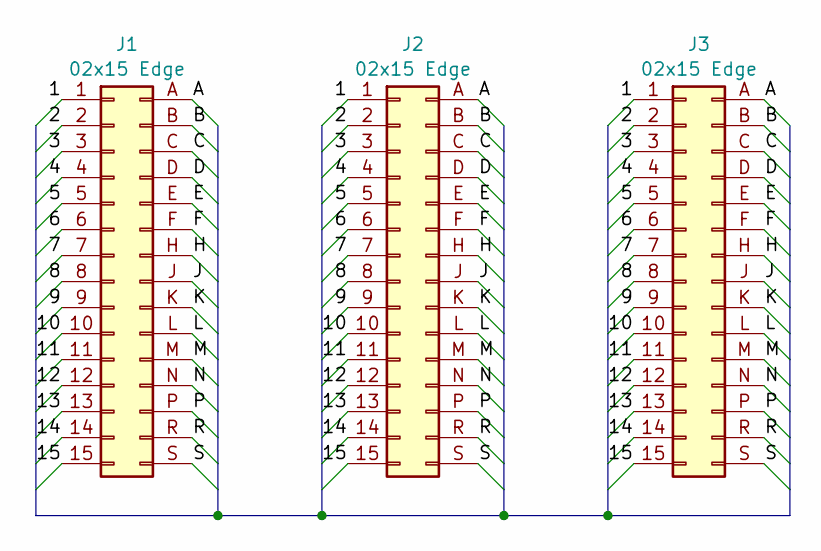
[picture p390: schematic CartConnectorAdapter1200XL.kicad_sch, Cart connector adapter for Atari 1200XL]

Parts:
J1, J2: 02x15 Edge; Atari_Cartridge_Connector
J3: 02x15 Edge; PinHeader_2x15_P2.54mm_Vertical

Connections:
/1: J1.1, J2.1, J3.1
/2: J1.2, J2.2, J3.2
/3: J1.3, J2.3, J3.3
/4: J1.4, J2.4, J3.4
/5: J1.5, J2.5, J3.5
/6: J1.6, J2.6, J3.6
/7: J1.7, J2.7, J3.7
/8: J1.8, J2.8, J3.8
/9: J1.9, J2.9, J3.9
/10: J1.10, J2.10, J3.10
/11: J1.11, J2.11, J3.11
/12: J1.12, J2.12, J3.12
/13: J1.13, J2.13, J3.13
/14: J1.14, J2.14, J3.14
/15: J1.15, J2.15, J3.15
/A: J1.A (Pin_16), J2.A (Pin_16), J3.A (Pin_16)
/B: J1.B (Pin_17), J2.B (Pin_17), J3.B (Pin_17)
/C: J1.C (Pin_18), J2.C (Pin_18), J3.C (Pin_18)
/D: J1.D (Pin_19), J2.D (Pin_19), J3.D (Pin_19)
/E: J1.E (Pin_20), J2.E (Pin_20), J3.E (Pin_20)
/F: J1.F (Pin_21), J2.F (Pin_21), J3.F (Pin_21)
/H: J1.H (Pin_22), J2.H (Pin_22), J3.H (Pin_22)
/J: J1.J (Pin_23), J2.J (Pin_23), J3.J (Pin_23)
/K: J1.K (Pin_24), J2.K (Pin_24), J3.K (Pin_24)
/L: J1.L (Pin_25), J2.L (Pin_25), J3.L (Pin_25)
/M: J1.M (Pin_26), J2.M (Pin_26), J3.M (Pin_26)
/N: J1.N (Pin_27), J2.N (Pin_27), J3.N (Pin_27)
/P: J1.P (Pin_28), J2.P (Pin_28), J3.P (Pin_28)
/R: J1.R (Pin_29), J2.R (Pin_29), J3.R (Pin_29)
/S: J1.S (Pin_30), J2.S (Pin_30), J3.S (Pin_30)

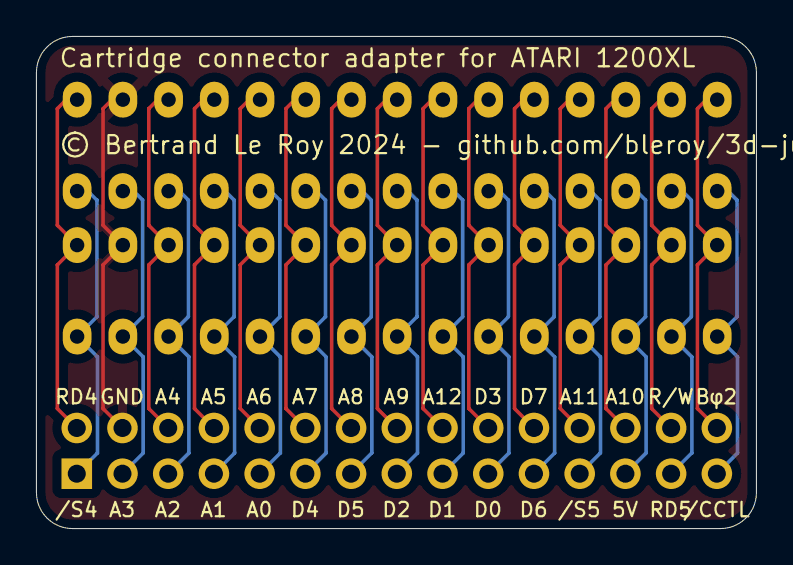
[picture p391: board CartConnectorAdapter1200XL.kicad_pcb from above]

Board: 2 copper layers, 40.0 x 27.3 mm, 3 parts (0 on the bottom side), 30 nets.
