bleroy/3d-junkyard/DecentXL/Adapters/600XL-keyboard-RN/600XL-keyboard-RN.kicad_pcb

## KiCad design DecentXL/Adapters/600XL-keyboard-RN/600XL-keyboard-RN.kicad_pcb (2024-08-12)

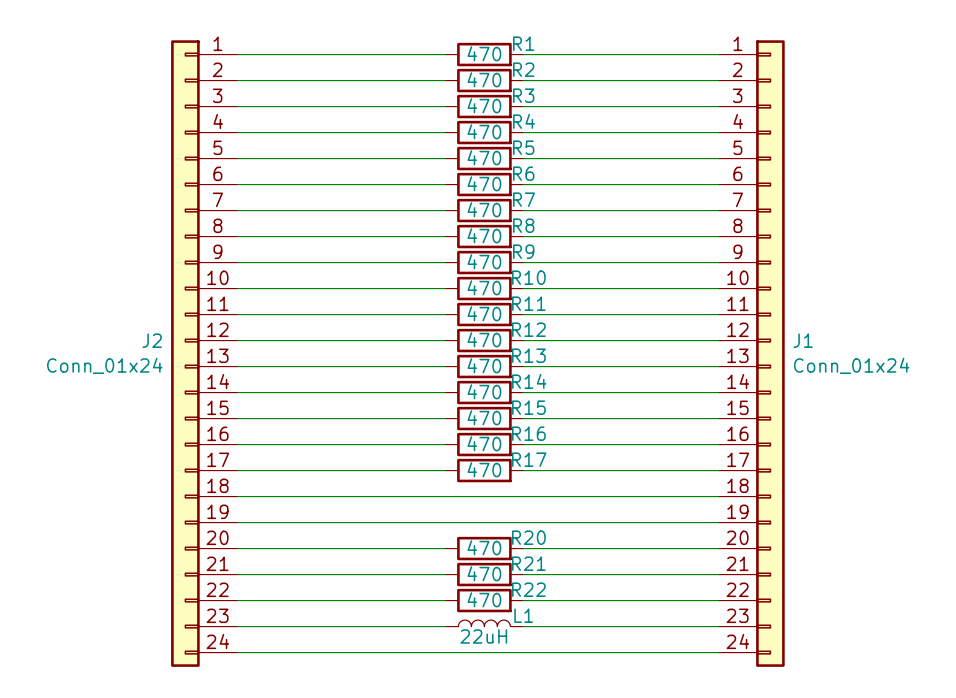
[picture p392: schematic 600XL-keyboard-RN.kicad_sch, 600XL Resistor Networks & Inductor Keyboard Interface board]

Parts:
J1, J2: Conn_01x24; PinHeader_1x24_P2.54mm_Vertical
L1: 22uH; L_0603_1608Metric; JLCPCB Part # C361669
R1, R2, R3, R4, R5, R6, R7, R8, R9, R10, R11, R12, R13, R14, R15, R16, R17, R20, R21, R22: 470; R_0603_1608Metric; JLCPCB Part # C23179

Connections:
unnamed: J1.1, R1.2
unnamed: J1.2, R2.2
unnamed: J1.3, R3.2
unnamed: J1.4, R4.2
unnamed: J1.5, R5.2
unnamed: J1.6, R6.2
unnamed: J1.7, R7.2
unnamed: J1.8, R8.2
unnamed: J1.9, R9.2
unnamed: J1.10, R10.2
unnamed: J1.11, R11.2
unnamed: J1.12, R12.2
unnamed: J1.13, R13.2
unnamed: J1.14, R14.2
unnamed: J1.15, R15.2
unnamed: J1.16, R16.2
unnamed: J1.17, R17.2
unnamed: J1.18, J2.18
unnamed: J1.19, J2.19
unnamed: J1.20, R20.2
unnamed: J1.21, R21.2
unnamed: J1.22, R22.2
unnamed: J1.23, L1.2
unnamed: J1.24, J2.24
unnamed: J2.1, R1.1
unnamed: J2.2, R2.1
unnamed: J2.3, R3.1
unnamed: J2.4, R4.1
unnamed: J2.5, R5.1
unnamed: J2.6, R6.1
unnamed: J2.7, R7.1
unnamed: J2.8, R8.1
unnamed: J2.9, R9.1
unnamed: J2.10, R10.1
unnamed: J2.11, R11.1
unnamed: J2.12, R12.1
unnamed: J2.13, R13.1
unnamed: J2.14, R14.1
unnamed: J2.15, R15.1
unnamed: J2.16, R16.1
unnamed: J2.17, R17.1
unnamed: J2.20, R20.1
unnamed: J2.21, R21.1
unnamed: J2.22, R22.1
unnamed: J2.23, L1.1

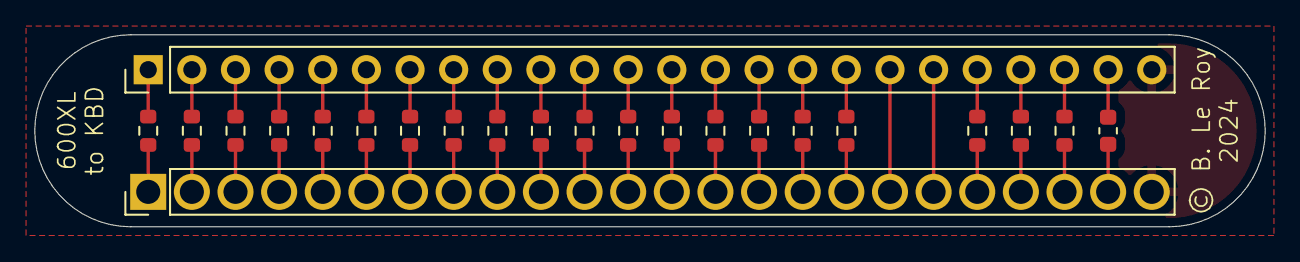
[picture p393: board 600XL-keyboard-RN.kicad_pcb from above]

Board: 2 copper layers, 71.6 x 11.2 mm, 23 parts (0 on the bottom side), 45 nets.
