bleroy/3d-junkyard/Decent400/USB/Decent400-to-USB.kicad_pcb

## KiCad design Decent400/USB/Decent400-to-USB.kicad_pcb (2024-03-22)

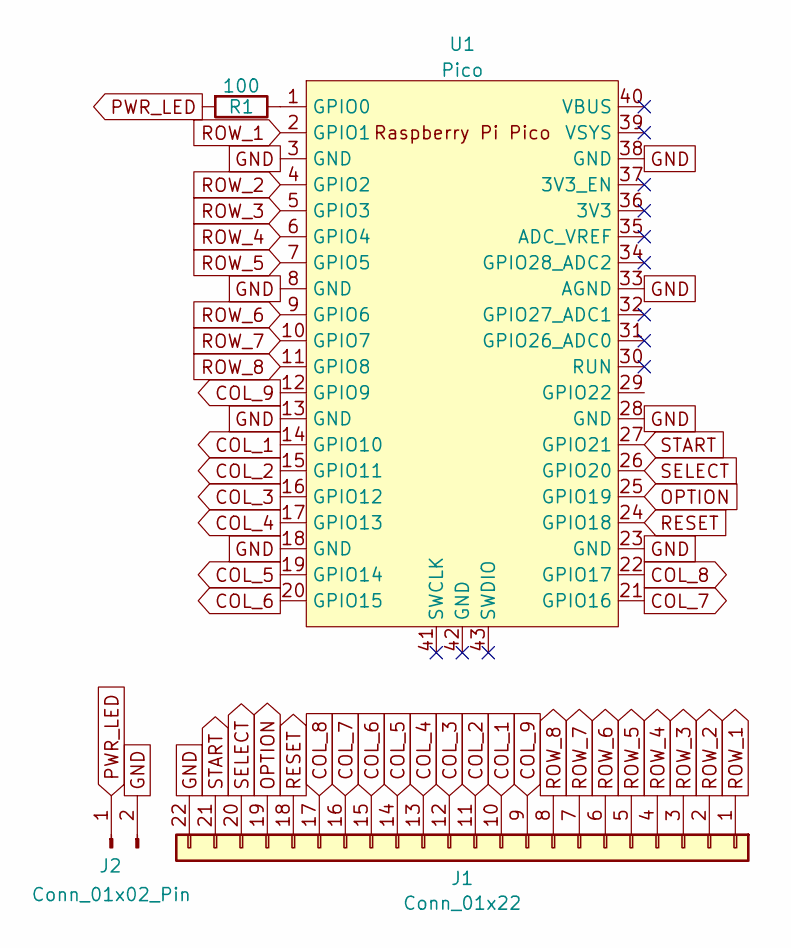
[picture p394: schematic Decent400-to-USB.kicad_sch, Decent400 USB adapter]

Parts:
J1: Conn_01x22; PinHeader_1x22_P2.54mm_Horizontal
J2: Conn_01x02_Pin; PinHeader_1x02_P2.54mm_Horizontal
R1: 100; R_Axial_DIN0411_L9.9mm_D3.6mm_P12.70mm_Horizontal
U1: Pico; RPi_Pico_SMD_TH

Connections:
COL_1: J1.10, U1.14 (GPIO10)
COL_2: J1.11, U1.15 (GPIO11)
COL_3: J1.12, U1.16 (GPIO12)
COL_4: J1.13, U1.17 (GPIO13)
COL_5: J1.14, U1.19 (GPIO14)
COL_6: J1.15, U1.20 (GPIO15)
COL_7: J1.16, U1.21 (GPIO16)
COL_8: J1.17, U1.22 (GPIO17)
COL_9: J1.9, U1.12 (GPIO9)
GND: J1.22, J2.2, U1.3 (GND), U1.8 (GND), U1.13 (GND), U1.18 (GND), U1.23 (GND), U1.28 (GND), U1.33 (AGND), U1.38 (GND)
unnamed: R1.1, U1.1 (GPIO0)
OPTION: J1.19, U1.25 (GPIO19)
PWR_LED: J2.1, R1.2
RESET: J1.18, U1.24 (GPIO18)
ROW_1: J1.1, U1.2 (GPIO1)
ROW_2: J1.2, U1.4 (GPIO2)
ROW_3: J1.3, U1.5 (GPIO3)
ROW_4: J1.4, U1.6 (GPIO4)
ROW_5: J1.5, U1.7 (GPIO5)
ROW_6: J1.6, U1.9 (GPIO6)
ROW_7: J1.7, U1.10 (GPIO7)
ROW_8: J1.8, U1.11 (GPIO8)
SELECT: J1.20, U1.26 (GPIO20)
START: J1.21, U1.27 (GPIO21)

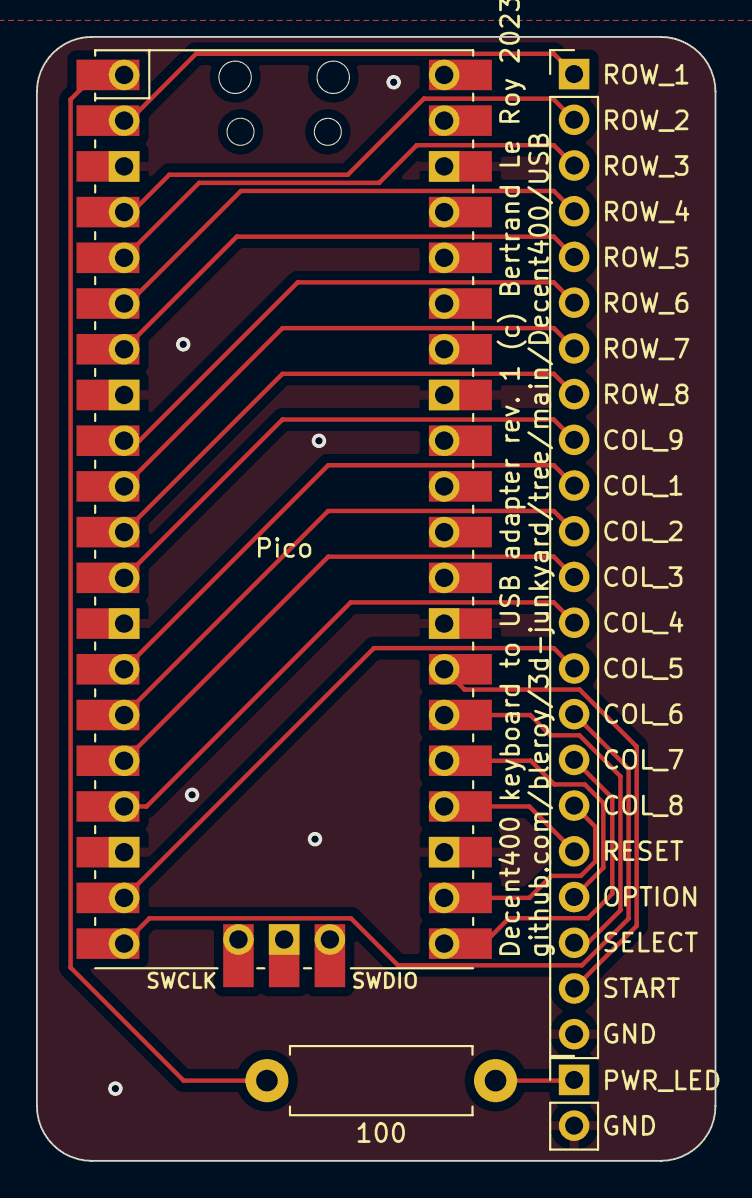
[picture p395: board Decent400-to-USB.kicad_pcb from above]

Board: 2 copper layers, 37.7 x 62.4 mm, 4 parts (0 on the bottom side), 24 nets.
