bleroy/3d-junkyard/Decent1200/Keyboard/Decent1200.kicad_sch

## KiCad design Decent1200/Keyboard/Decent1200.kicad_sch (2024-01-14)

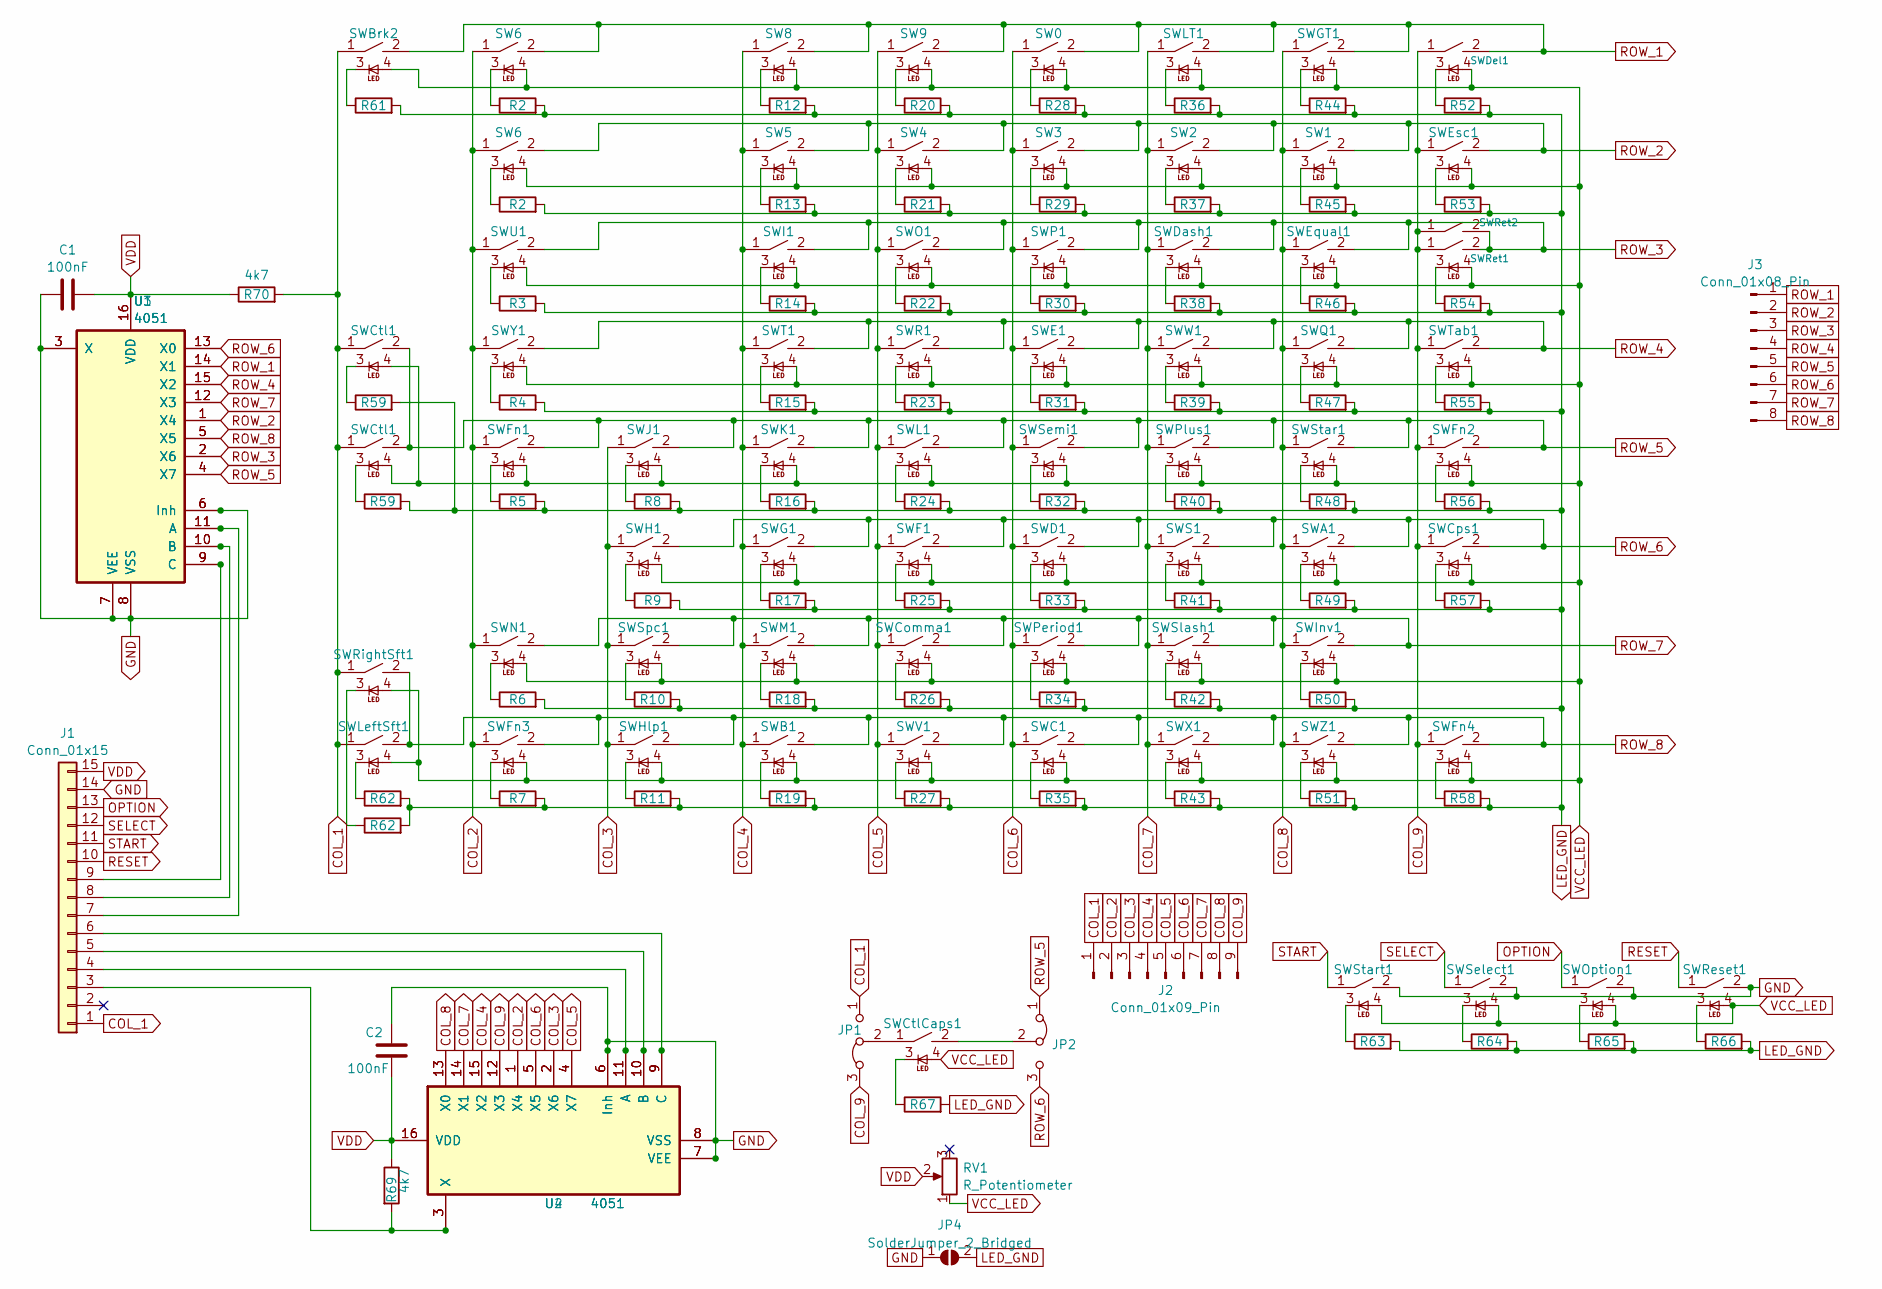
[picture p397: schematic Decent1200.kicad_sch]

Parts:
C1, C2: 100nF; C_0603_1608Metric; JLCPCB Part # C14663
J1: Conn_01x15; PinHeader_1x15_P2.54mm_Horizontal
J2: Conn_01x09_Pin; PinHeader_1x09_P2.54mm_Vertical
J3: Conn_01x08_Pin; PinHeader_1x08_P2.54mm_Vertical
JP1, JP2: Jumper_3_Bridged12; PinHeader_1x03_P2.54mm_Horizontal
JP4: SolderJumper_2_Bridged; SolderJumper-2_P1.3mm_Bridged_RoundedPad1.0x1.5mm
R2, R3, R4, R5, R6, R7, R8, R9, R10, R11, R12, R13, R14, R15, R16, R17, R18, R19, R20, R21, R22, R23, R24, R25, R26, R27, R28, R29, R30, R31, R32, R33, R34, R35, R36, R37, R38, R39, R40, R41, R42, R43, R44, R45, R46, R47, R48, R49, R50, R51, R52, R53, R54, R55, R56, R57, R58, R59, R61, R62, R63, R64, R65, R66, R67: R; R_0603_1608Metric; JLCPCB Part # C22775
R69, R70: 4k7; R_0603_1608Metric; JLCPCB Part # C23162
RV1: R_Potentiometer; Potentiometer_Bourns_TC33X_Vertical; JLCPCB Part # C720647
SW0: 0; MX-1-00U-LED; JLCPCB Part # C193191
SW1: 1; MX-1-00U-LED; JLCPCB Part # C193191
SW2: 2; MX-1-00U-LED; JLCPCB Part # C193191
SW3: 3; MX-1-00U-LED; JLCPCB Part # C193191
SW4: 4; MX-1-00U-LED; JLCPCB Part # C193191
SW5: 5; MX-1-00U-LED; JLCPCB Part # C193191
SW6: 6; MX-1-00U-LED; JLCPCB Part # C193191
SW8: 8; MX-1-00U-LED; JLCPCB Part # C193191
SW9: 9; MX-1-00U-LED; JLCPCB Part # C193191
SWA1: A; MX-1-00U-LED; JLCPCB Part # C193191
SWB1: B; MX-1-00U-LED; JLCPCB Part # C193191
SWBrk2: Break; MX-1-00_1-25U-LED-Console; JLCPCB Part # C193191
SWC1: C; MX-1-00U-LED; JLCPCB Part # C193191
SWComma1: Comma; MX-1-00U-LED; JLCPCB Part # C193191
SWCps1: Caps; MX-1-25U-LED; JLCPCB Part # C193191
SWCtl1: Control; MX-1-25U-LED; JLCPCB Part # C193191
SWCtlCaps1: ControlCaps; MX-1-25U-CAPS-LED; JLCPCB Part # C193191
SWD1: D; MX-1-00U-LED; JLCPCB Part # C193191
SWDash1: Dash; MX-1-00U-LED; JLCPCB Part # C193191
SWDel1: Delete; MX-2-00U-LED; JLCPCB Part # C193191
SWE1: E; MX-1-00U-LED; JLCPCB Part # C193191
SWEqual1: Equal; MX-1-00U-LED; JLCPCB Part # C193191
SWEsc1: Esc; MX-1-00_1-25U-LED; JLCPCB Part # C193191
SWF1: F; MX-1-00U-LED; JLCPCB Part # C193191
SWFn1: F1; MX-1-00_1-25U-LED-Console; JLCPCB Part # C193191
SWFn2: F2; MX-1-00_1-25U-LED-Console; JLCPCB Part # C193191
SWFn3: F3; MX-1-00_1-25U-LED-Console; JLCPCB Part # C193191
SWFn4: F4; MX-1-00_1-25U-LED-Console; JLCPCB Part # C193191
SWG1: G; MX-1-00U-LED; JLCPCB Part # C193191
SWGT1: >; MX-1-00U-LED; JLCPCB Part # C193191
SWH1: H; MX-1-00U-LED; JLCPCB Part # C193191
SWHlp1: Help; MX-1-00_1-25U-LED-Console; JLCPCB Part # C193191
SWI1: I; MX-1-00U-LED; JLCPCB Part # C193191
SWInv1: Inverse; MX-1-00_1-25U-LED-Console; JLCPCB Part # C193191
SWJ1: J; MX-1-00U-LED; JLCPCB Part # C193191
SWK1: K; MX-1-00U-LED; JLCPCB Part # C193191
SWL1: L; MX-1-00U-LED; JLCPCB Part # C193191
SWLT1: <; MX-1-00U-LED; JLCPCB Part # C193191
SWLeftSft1: Shift; MX-2-25_2-50U-LED; JLCPCB Part # C193191
SWM1: M; MX-1-00U-LED; JLCPCB Part # C193191
SWN1: N; MX-1-00U-LED; JLCPCB Part # C193191
SWO1: O; MX-1-00U-LED; JLCPCB Part # C193191
SWOption1: Option; MX-1-00_1-25U-LED-Console; JLCPCB Part # C193191
SWP1: P; MX-1-00U-LED; JLCPCB Part # C193191
SWPeriod1: Period; MX-1-00U-LED; JLCPCB Part # C193191
SWPlus1: Plus; MX-1-00U-LED; JLCPCB Part # C193191
SWQ1: Q; MX-1-00U-LED; JLCPCB Part # C193191
SWR1: R; MX-1-00U-LED; JLCPCB Part # C193191
SWReset1: Reset; MX-1-00_1-25U-LED-Console; JLCPCB Part # C193191
SWRet1: Return; MX-1-50U-RETURN-LED; JLCPCB Part # C193191
SWRet2: Return; MX-ISO-RETURN; JLCPCB Part # C193191
SWRightSft1: Shift; MX-2-75U-LED; JLCPCB Part # C193191
SWS1: S; MX-1-00U-LED; JLCPCB Part # C193191
SWSelect1: Select; MX-1-00_1-25U-LED-Console; JLCPCB Part # C193191
SWSemi1: Semicolon; MX-1-00U-LED; JLCPCB Part # C193191
SWSlash1: Slash; MX-1-00U-LED; JLCPCB Part # C193191
SWSpc1: Space; MX-6-25U-LED; JLCPCB Part # C193191
SWStar1: Star; MX-1-00U-LED; JLCPCB Part # C193191
SWStart1: Start; MX-1-00_1-25U-LED-Console; JLCPCB Part # C193191
SWT1: T; MX-1-00U-LED; JLCPCB Part # C193191
SWTab1: Tab; MX-1-50_1-75U-LED; JLCPCB Part # C193191
SWU1: U; MX-1-00U-LED; JLCPCB Part # C193191
SWV1: V; MX-1-00U-LED; JLCPCB Part # C193191
SWW1: W; MX-1-00U-LED; JLCPCB Part # C193191
SWX1: X; MX-1-00U-LED; JLCPCB Part # C193191
SWY1: Y; MX-1-00U-LED; JLCPCB Part # C193191
SWZ1: Z; MX-1-00U-LED; JLCPCB Part # C193191
U1, U2: 4051; SOIC-16_3.9x9.9mm_P1.27mm; JLCPCB Part # C21379
U3, U4: 4051; DIP-16_W7.62mm; JLCPCB Part # C21379

Connections:
COL_1: J1.1, J2.1, JP1.1 (A), R70.2, SWBrk2.1, SWCtl1.1, SWLeftSft1.1, SWRightSft1.1
COL_2: J2.2, SW6.1, SWFn1.1, SWFn3.1, SWN1.1, SWU1.1, SWY1.1, U2.1 (X4), U4.1 (X4)
COL_3: J2.3, SWH1.1, SWHlp1.1, SWJ1.1, SWSpc1.1, U2.2 (X6), U4.2 (X6)
COL_4: J2.4, SW5.1, SW8.1, SWB1.1, SWG1.1, SWI1.1, SWK1.1, SWM1.1, SWT1.1, U2.15 (X2), U4.15 (X2)
COL_5: J2.5, SW4.1, SW9.1, SWComma1.1, SWF1.1, SWL1.1, SWO1.1, SWR1.1, SWV1.1, U2.4 (X7), U4.4 (X7)
COL_6: J2.6, SW0.1, SW3.1, SWC1.1, SWD1.1, SWE1.1, SWP1.1, SWPeriod1.1, SWSemi1.1, U2.5 (X5), U4.5 (X5)
COL_7: J2.7, SW2.1, SWDash1.1, SWLT1.1, SWPlus1.1, SWS1.1, SWSlash1.1, SWW1.1, SWX1.1, U2.14 (X1), U4.14 (X1)
COL_8: J2.8, SW1.1, SWA1.1, SWEqual1.1, SWGT1.1, SWInv1.1, SWQ1.1, SWStar1.1, SWZ1.1, U2.13 (X0), U4.13 (X0)
COL_9: J2.9, JP1.3 (B), SWCps1.1, SWDel1.1, SWEsc1.1, SWFn2.1, SWFn4.1, SWRet1.1, SWRet2.1, SWTab1.1, U2.12 (X3), U4.12 (X3)
GND: C1.1, C2.1, J1.14, JP4.1 (A), SWOption1.2, SWReset1.2, SWSelect1.2, SWStart1.2, U1.3 (X), U1.6 (Inh), U1.7 (VEE), U1.8 (VSS), U2.6 (Inh), U2.7 (VEE), U2.8 (VSS), U3.3 (X), U3.6 (Inh), U3.7 (VEE), U3.8 (VSS), U4.6 (Inh), U4.7 (VEE), U4.8 (VSS)
LED_GND: JP4.2 (B), R2.2, R3.2, R4.2, R5.2, R6.2, R7.2, R8.2, R9.2, R10.2, R11.2, R12.2, R13.2, R14.2, R15.2, R16.2, R17.2, R18.2, R19.2, R20.2, R21.2, R22.2, R23.2, R24.2, R25.2, R26.2, R27.2, R28.2, R29.2, R30.2, R31.2, R32.2, R33.2, R34.2, R35.2, R36.2, R37.2, R38.2, R39.2, R40.2, R41.2, R42.2, R43.2, R44.2, R45.2, R46.2, R47.2, R48.2, R49.2, R50.2, R51.2, R52.2, R53.2, R54.2, R55.2, R56.2, R57.2, R58.2, R59.2, R61.2, R62.2, R63.2, R64.2, R65.2, R66.2, R67.2
unnamed: J1.3, R69.2, U2.3 (X), U4.3 (X)
unnamed: J1.4, U2.11 (A), U4.11 (A)
unnamed: J1.5, U2.10 (B), U4.10 (B)
unnamed: J1.6, U2.9 (C), U4.9 (C)
unnamed: J1.7, U1.11 (A), U3.11 (A)
unnamed: J1.8, U1.10 (B), U3.10 (B)
unnamed: J1.9, U1.9 (C), U3.9 (C)
unnamed: JP1.2 (C), SWCtlCaps1.1
unnamed: JP2.2 (C), SWCtlCaps1.2
unnamed: R2.1, SW6.3
unnamed: R3.1, SWU1.3
unnamed: R4.1, SWY1.3
unnamed: R5.1, SWFn1.3
unnamed: R6.1, SWN1.3
unnamed: R7.1, SWFn3.3
unnamed: R8.1, SWJ1.3
unnamed: R9.1, SWH1.3
unnamed: R10.1, SWSpc1.3
unnamed: R11.1, SWHlp1.3
unnamed: R12.1, SW8.3
unnamed: R13.1, SW5.3
unnamed: R14.1, SWI1.3
unnamed: R15.1, SWT1.3
unnamed: R16.1, SWK1.3
unnamed: R17.1, SWG1.3
unnamed: R18.1, SWM1.3
unnamed: R19.1, SWB1.3
unnamed: R20.1, SW9.3
unnamed: R21.1, SW4.3
unnamed: R22.1, SWO1.3
unnamed: R23.1, SWR1.3
unnamed: R24.1, SWL1.3
unnamed: R25.1, SWF1.3
unnamed: R26.1, SWComma1.3
unnamed: R27.1, SWV1.3
unnamed: R28.1, SW0.3
unnamed: R29.1, SW3.3
unnamed: R30.1, SWP1.3
unnamed: R31.1, SWE1.3
unnamed: R32.1, SWSemi1.3
unnamed: R33.1, SWD1.3
unnamed: R34.1, SWPeriod1.3
unnamed: R35.1, SWC1.3
unnamed: R36.1, SWLT1.3
unnamed: R37.1, SW2.3
unnamed: R38.1, SWDash1.3
unnamed: R39.1, SWW1.3
unnamed: R40.1, SWPlus1.3
unnamed: R41.1, SWS1.3
unnamed: R42.1, SWSlash1.3
unnamed: R43.1, SWX1.3
unnamed: R44.1, SWGT1.3
unnamed: R45.1, SW1.3
unnamed: R46.1, SWEqual1.3
unnamed: R47.1, SWQ1.3
unnamed: R48.1, SWStar1.3
unnamed: R49.1, SWA1.3
unnamed: R50.1, SWInv1.3
unnamed: R51.1, SWZ1.3
unnamed: R52.1, SWDel1.3
unnamed: R53.1, SWEsc1.3
unnamed: R54.1, SWRet1.3
unnamed: R55.1, SWTab1.3
unnamed: R56.1, SWFn2.3
unnamed: R57.1, SWCps1.3
unnamed: R58.1, SWFn4.3
unnamed: R59.1, SWCtl1.3
unnamed: R61.1, SWBrk2.3
unnamed: R62.1, SWLeftSft1.3, SWRightSft1.3
unnamed: R63.1, SWStart1.3
unnamed: R64.1, SWSelect1.3
unnamed: R65.1, SWOption1.3
unnamed: R66.1, SWReset1.3
unnamed: R67.1, SWCtlCaps1.3
OPTION: J1.13, SWOption1.1
RESET: J1.10, SWReset1.1
ROW_1: J3.1, SW0.2, SW6.2, SW8.2, SW9.2, SWBrk2.2, SWDel1.2, SWGT1.2, SWLT1.2, U1.14 (X1), U3.14 (X1)
ROW_2: J3.2, SW1.2, SW2.2, SW3.2, SW4.2, SW5.2, SW6.2, SWEsc1.2, U1.1 (X4), U3.1 (X4)
ROW_3: J3.3, SWDash1.2, SWEqual1.2, SWI1.2, SWO1.2, SWP1.2, SWRet1.2, SWRet2.2, SWU1.2, U1.2 (X6), U3.2 (X6)
ROW_4: J3.4, SWE1.2, SWQ1.2, SWR1.2, SWT1.2, SWTab1.2, SWW1.2, SWY1.2, U1.15 (X2), U3.15 (X2)
ROW_5: J3.5, JP2.1 (A), SWCtl1.2, SWFn1.2, SWFn2.2, SWJ1.2, SWK1.2, SWL1.2, SWPlus1.2, SWSemi1.2, SWStar1.2, U1.4 (X7), U3.4 (X7)
ROW_6: J3.6, JP2.3 (B), SWA1.2, SWCps1.2, SWD1.2, SWF1.2, SWG1.2, SWH1.2, SWS1.2, U1.13 (X0), U3.13 (X0)
ROW_7: J3.7, SWComma1.2, SWInv1.2, SWM1.2, SWN1.2, SWPeriod1.2, SWSlash1.2, SWSpc1.2, U1.12 (X3), U3.12 (X3)
ROW_8: J3.8, SWB1.2, SWC1.2, SWFn3.2, SWFn4.2, SWHlp1.2, SWLeftSft1.2, SWRightSft1.2, SWV1.2, SWX1.2, SWZ1.2, U1.5 (X5), U3.5 (X5)
SELECT: J1.12, SWSelect1.1
START: J1.11, SWStart1.1
VCC_LED: RV1.1, SW0.4, SW1.4, SW2.4, SW3.4, SW4.4, SW5.4, SW6.4, SW8.4, SW9.4, SWA1.4, SWB1.4, SWBrk2.4, SWC1.4, SWComma1.4, SWCps1.4, SWCtl1.4, SWCtlCaps1.4, SWD1.4, SWDash1.4, SWDel1.4, SWE1.4, SWEqual1.4, SWEsc1.4, SWF1.4, SWFn1.4, SWFn2.4, SWFn3.4, SWFn4.4, SWG1.4, SWGT1.4, SWH1.4, SWHlp1.4, SWI1.4, SWInv1.4, SWJ1.4, SWK1.4, SWL1.4, SWLT1.4, SWLeftSft1.4, SWM1.4, SWN1.4, SWO1.4, SWOption1.4, SWP1.4, SWPeriod1.4, SWPlus1.4, SWQ1.4, SWR1.4, SWReset1.4, SWRet1.4, SWRightSft1.4, SWS1.4, SWSelect1.4, SWSemi1.4, SWSlash1.4, SWSpc1.4, SWStar1.4, SWStart1.4, SWT1.4, SWTab1.4, SWU1.4, SWV1.4, SWW1.4, SWX1.4, SWY1.4, SWZ1.4
VDD: C1.2, C2.2, J1.15, R69.1, R70.1, RV1.2, U1.16 (VDD), U2.16 (VDD), U3.16 (VDD), U4.16 (VDD)
