bleroy/3d-junkyard/JoyKeyMX/AtariJoystickPaddleTester/AtariJoystickPaddleTester.kicad_sch

## KiCad design JoyKeyMX/AtariJoystickPaddleTester/AtariJoystickPaddleTester.kicad_sch (2023-04-02)

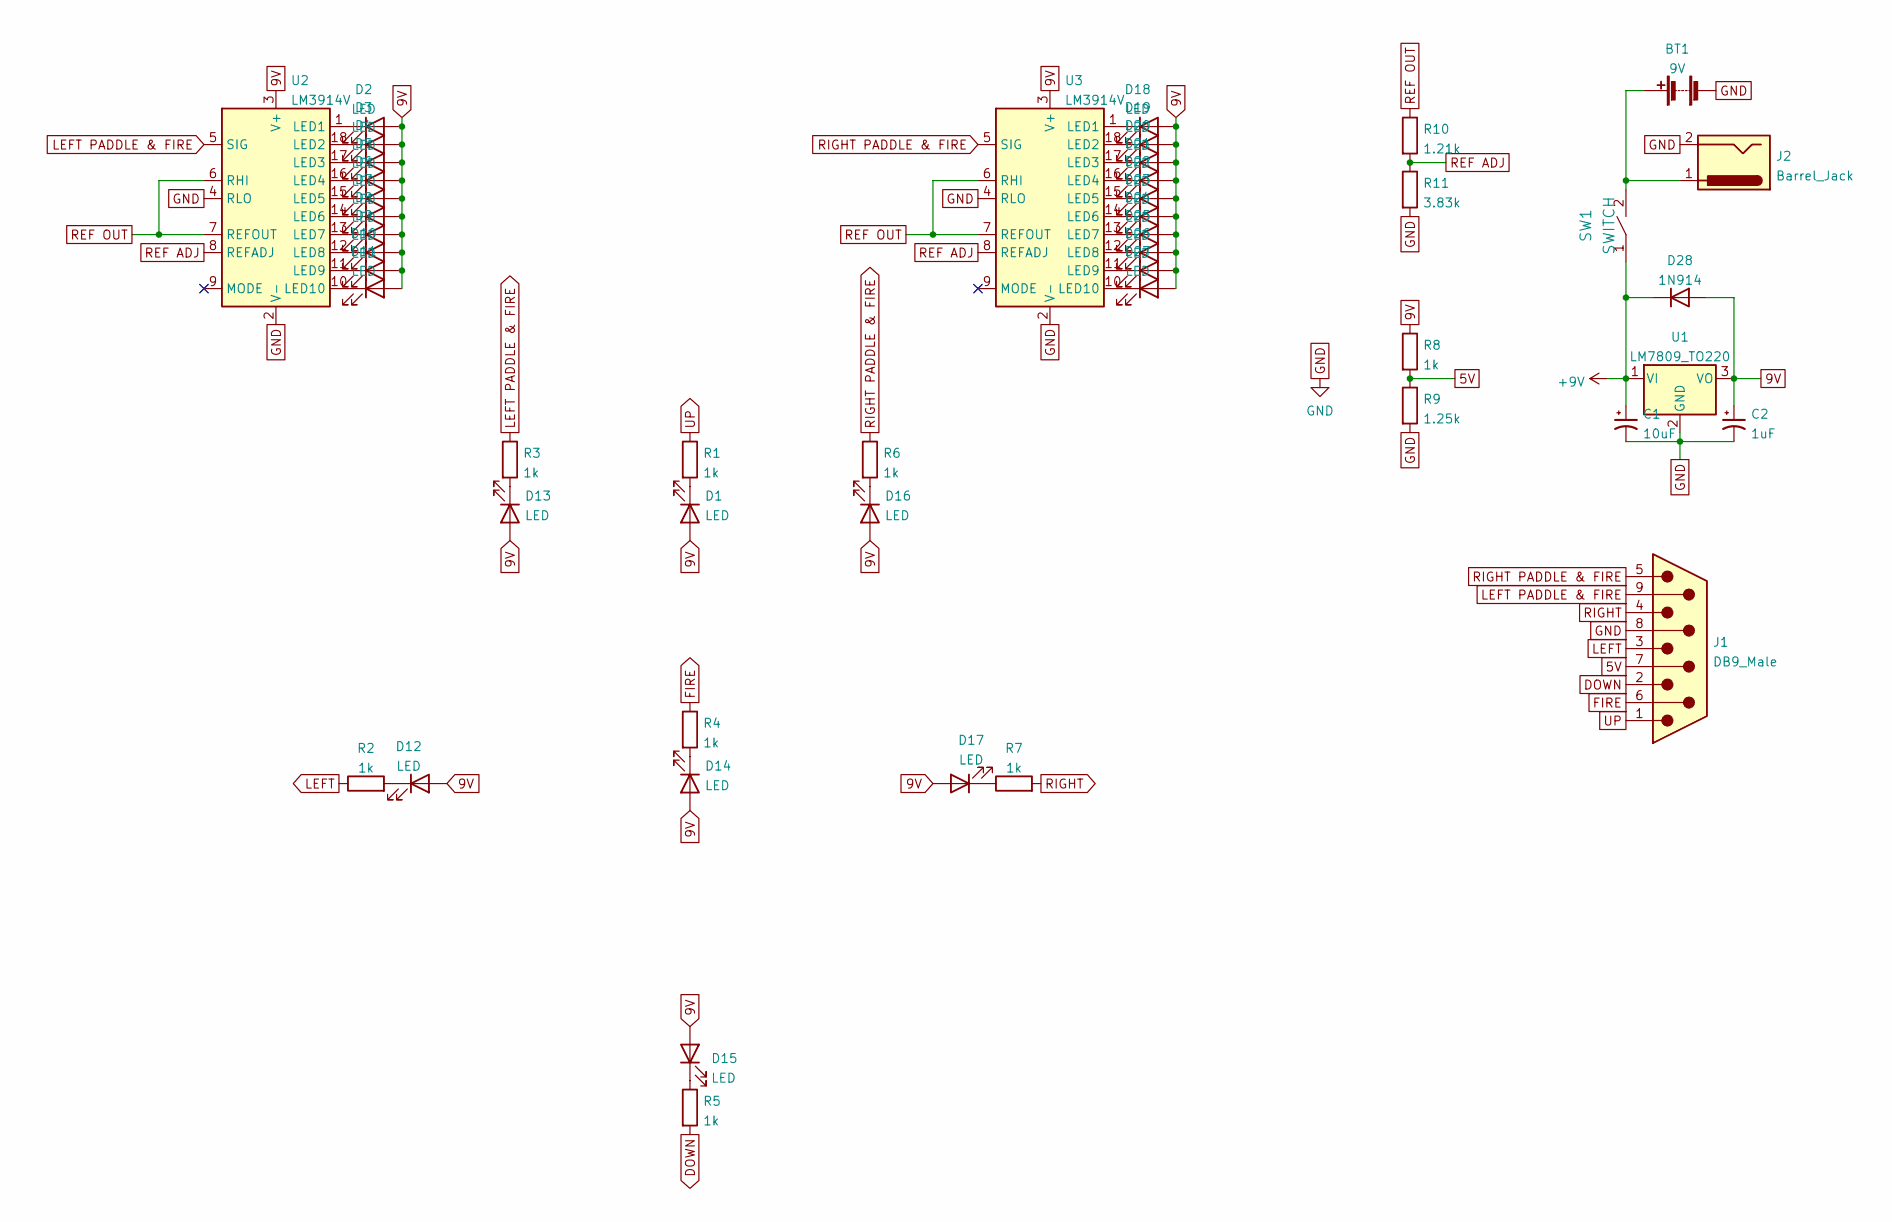
[picture p398: schematic AtariJoystickPaddleTester.kicad_sch]

Parts:
BT1: 9V; BatteryHolder_MPD_BA9VPC_1xPP3
C1: 10uF; CP_Radial_D5.0mm_P2.50mm
C2: 1uF; CP_Radial_D5.0mm_P2.50mm
D1, D2, D3, D4, D5, D6, D7, D8, D9, D10, D11, D12, D13, D14, D15, D16, D17, D18, D19, D20, D21, D22, D23, D24, D25, D26, D27: LED; LED_D10.0mm
D28: 1N914; D_DO-35_SOD27_P7.62mm_Horizontal
J1: DB9_Male; DSUB-9_Male_Horizontal_P2.77x2.84mm_EdgePinOffset4.94mm_Hou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
J2: Barrel_Jack; BarrelJack_Horizontal
R1, R2, R3, R4, R5, R6, R7, R8: 1k; R_Axial_DIN0207_L6.3mm_D2.5mm_P7.62mm_Horizontal
R9: 1.25k; R_Axial_DIN0207_L6.3mm_D2.5mm_P7.62mm_Horizontal
R10: 1.21k; R_Axial_DIN0207_L6.3mm_D2.5mm_P7.62mm_Horizontal
R11: 3.83k; R_Axial_DIN0207_L6.3mm_D2.5mm_P7.62mm_Horizontal
SW1: SWITCH; Slide Switch 3-pin
U1: LM7809_TO220; TO-220-3_Horizontal_TabDown
U2, U3: LM3914V; DIP-18_W7.62mm

Connections:
5V: J1.7, R8.2, R9.1
9V: C2.1, D1.2 (A), D2.2 (A), D3.2 (A), D4.2 (A), D5.2 (A), D6.2 (A), D7.2 (A), D8.2 (A), D9.2 (A), D10.2 (A), D11.2 (A), D12.2 (A), D13.2 (A), D14.2 (A), D15.2 (A), D16.2 (A), D17.2 (A), D18.2 (A), D19.2 (A), D20.2 (A), D21.2 (A), D22.2 (A), D23.2 (A), D24.2 (A), D25.2 (A), D26.2 (A), D27.2 (A), D28.2 (A), R8.1, U1.3 (VO), U2.3 (V+), U3.3 (V+)
+9V: C1.1, D28.1 (K), SW1.1, U1.1 (VI)
DOWN: J1.2, R5.2
FIRE: J1.6, R4.1
GND: BT1.2 (-), C1.2, C2.2, J1.8, J2.2, R9.2, R11.2, U1.2 (GND), U2.2 (V-), U2.4 (RLO), U3.2 (V-), U3.4 (RLO)
LEFT: J1.3, R2.1
LEFT PADDLE & FIRE: J1.9, R3.1, U2.5 (SIG)
unnamed: BT1.1 (+), J2.1, SW1.2
unnamed: D1.1 (K), R1.2
unnamed: D2.1 (K), U2.1 (LED1)
unnamed: D3.1 (K), U2.18 (LED2)
unnamed: D4.1 (K), U2.17 (LED3)
unnamed: D5.1 (K), U2.16 (LED4)
unnamed: D6.1 (K), U2.15 (LED5)
unnamed: D7.1 (K), U2.14 (LED6)
unnamed: D8.1 (K), U2.13 (LED7)
unnamed: D9.1 (K), U2.12 (LED8)
unnamed: D10.1 (K), U2.11 (LED9)
unnamed: D11.1 (K), U2.10 (LED10)
unnamed: D12.1 (K), R2.2
unnamed: D13.1 (K), R3.2
unnamed: D14.1 (K), R4.2
unnamed: D15.1 (K), R5.1
unnamed: D16.1 (K), R6.2
unnamed: D17.1 (K), R7.1
unnamed: D18.1 (K), U3.1 (LED1)
unnamed: D19.1 (K), U3.18 (LED2)
unnamed: D20.1 (K), U3.17 (LED3)
unnamed: D21.1 (K), U3.16 (LED4)
unnamed: D22.1 (K), U3.15 (LED5)
unnamed: D23.1 (K), U3.14 (LED6)
unnamed: D24.1 (K), U3.13 (LED7)
unnamed: D25.1 (K), U3.12 (LED8)
unnamed: D26.1 (K), U3.11 (LED9)
unnamed: D27.1 (K), U3.10 (LED10)
REF ADJ: R10.2, R11.1, U2.8 (REFADJ), U3.8 (REFADJ)
REF OUT: R10.1, U2.6 (RHI), U2.7 (REFOUT), U3.6 (RHI), U3.7 (REFOUT)
RIGHT: J1.4, R7.2
RIGHT PADDLE & FIRE: J1.5, R6.1, U3.5 (SIG)
UP: J1.1, R1.1
