bleroy/3d-junkyard/Decent60/keyboard/Firmware/src/keymaps/default/keymap.c

// Copyright 2023 QMK
// SPDX-License-Identifier: GPL-2.0-or-later

#include QMK_KEYBOARD_H

enum decent_layers {
    BASE
};

const uint16_t PROGMEM keymaps[][MATRIX_ROWS][MATRIX_COLS] = {
    /*
    *      /─────/─────/─────/─────/─────/─────/─────/─────/─────/
    *     /F1   /F2   /F3   /F4   /Help /Start/Slect/Optin/Reset/
    *    /─────/─────/─────/─────/─────/─────/─────/─────/─────/
    * ┌───┬───┬───┬───┬───┬───┬───┬───┬───┬───┬───┬───┬───┬───────┐
    * │Esc│ 1!│ 2@│ 3#│ 4%│ 5%│ 6^│ 7&│ 8*│ 9(│ 0)│ - │ = │ Backsp│
    * ├───┴─┬─┴─┬─┴─┬─┴─┬─┴─┬─┴─┬─┴─┬─┴─┬─┴─┬─┴─┬─┴─┬─┴─┬─┴─┬─────┤
    * │ Tab │ Q │ W │ E │ R │ T │ Y │ U │ I │ O │ P │ [{│ ]}│  \| │
    * ├─────┴┬──┴┬──┴┬──┴┬──┴┬──┴┬──┴┬──┴┬──┴┬──┴┬──┴┬──┴┬──┴─────┤
    * │ Caps │ A │ S │ D │ F │ G │ H │ J │ K │ L │ ;:│ '"│  Enter │
    * ├──────┴─┬─┴─┬─┴─┬─┴─┬─┴─┬─┴─┬─┴─┬─┴─┬─┴─┬─┴─┬─┴─┬─┴────────┤
    * │ Shift  │ Z │ X │ C │ V │ B │ N │ M │ ,<│ .>│ /?│    Shift │
    * ├────┬───┴┬──┴─┬─┴───┴───┴───┴───┴───┴──┬┴───┼───┴┬────┬────┤
    * │Ctrl│ GUI│ Brk│                        │  ← │  ↑ │  ↓ │  → │
    * └────┴────┴────┴────────────────────────┴────┴────┴────┴────┘
    */
    [BASE] = LAYOUT(
        KC_F1,   KC_F2,   KC_F3,   KC_F4,   KC_F5,   KC_F6,   KC_F7,   KC_F8,   KC_F9,

        QK_GESC, KC_1,    KC_2,    KC_3,    KC_4,    KC_5,    KC_6,    KC_7,    KC_8,    KC_9,    KC_0,    KC_MINS, KC_EQL,  KC_BSPC,
        KC_TAB,  KC_Q,    KC_W,    KC_E,    KC_R,    KC_T,    KC_Y,    KC_U,    KC_I,    KC_O,    KC_P,    KC_LBRC, KC_RBRC, KC_BSLS,
        KC_CAPS, KC_A,    KC_S,    KC_D,    KC_F,    KC_G,    KC_H,    KC_J,    KC_K,    KC_L,    KC_SCLN, KC_QUOT,          KC_ENT,
        KC_LSFT,          KC_Z,    KC_X,    KC_C,    KC_V,    KC_B,    KC_N,    KC_M,    KC_COMM, KC_DOT,  KC_SLSH,          KC_RSFT,
        KC_LCTL, KC_LGUI, KC_LALT,                            KC_SPC,                             KC_LEFT, KC_UP,   KC_DOWN, KC_RIGHT
    )
};

#if defined(ENCODER_MAP_ENABLE)
const uint16_t PROGMEM encoder_map[][NUM_ENCODERS][NUM_DIRECTIONS] = {
    [0] = { ENCODER_CCW_CW(KC_VOLD, KC_VOLU) }
};
#endif
